gratefulfrog/ArduGuitar/Ardu2/design/POC-3_MAX395/HMI/Images/PB076096 Annotated.pdf

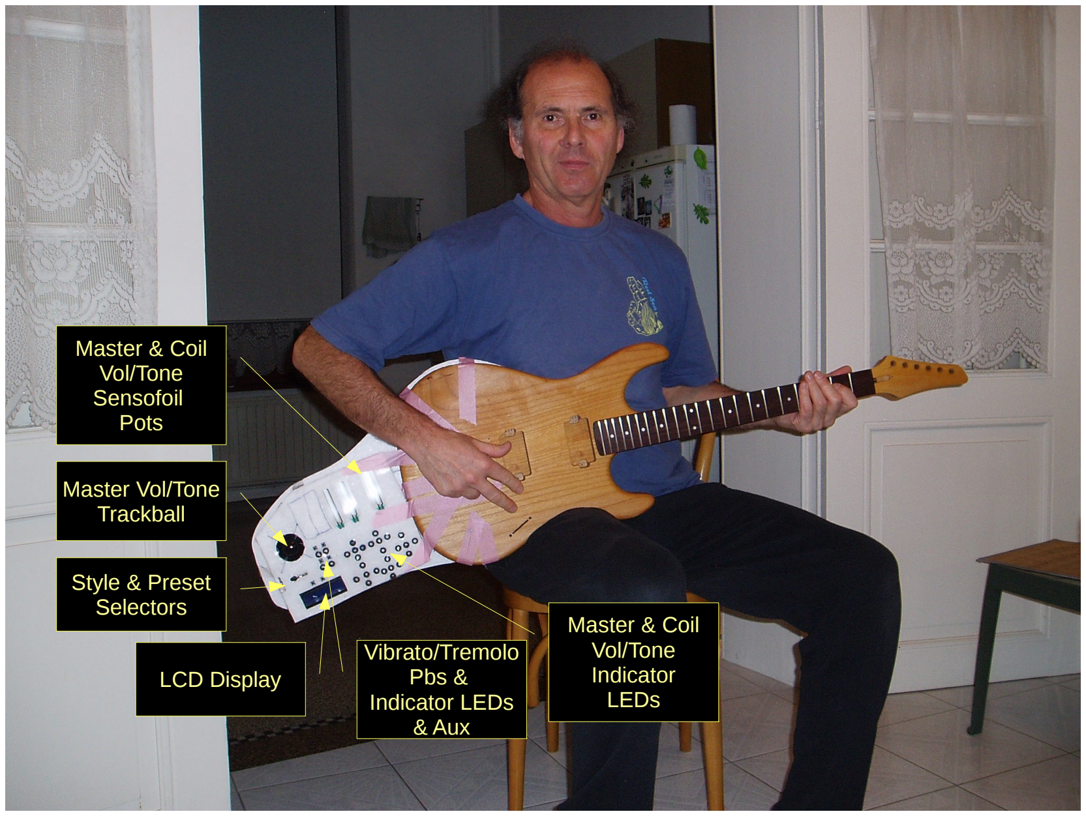
[picture p10: page 1]

Master Vol/Tone
Trackball

Master & Coil
Vol/Tone
Sensofoil
Pots

Style & Preset
Selectors

LCD Display

Vibrato/Tremolo
Pbs &
Indicator LEDs
& Aux

Master & Coil
Vol/Tone
Indicator
LEDs
