gratefulfrog/ArduGuitar/Ardu2/design/POC-3_MAX395/HMI/Images/boltplus-no-text.pdf

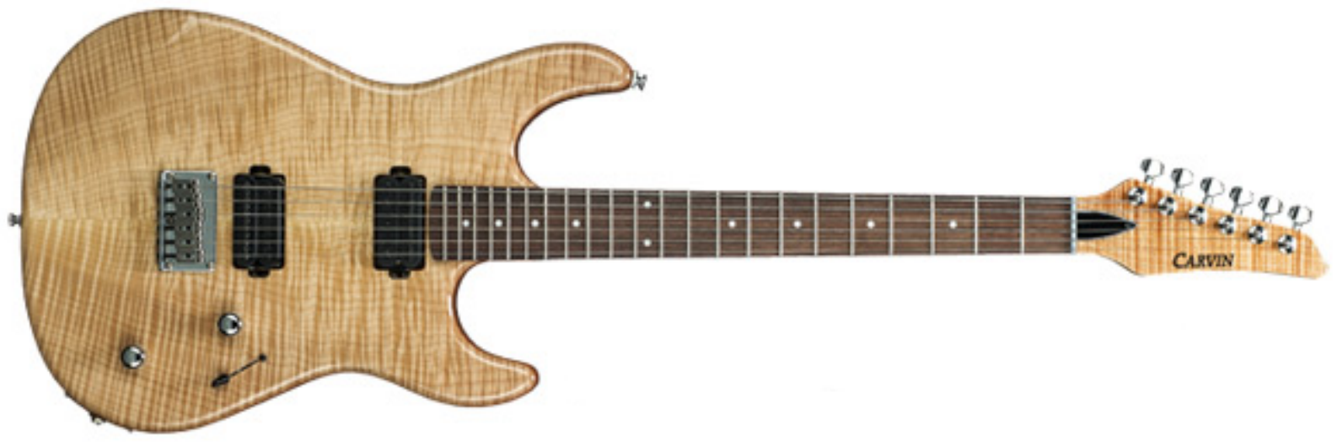
[picture p11: page 1]
