gratefulfrog/ArduGuitar/arduino/Layouts/ArduStomp/EnclosureDesign/2D/FullDesign09/outside-panels.pdf

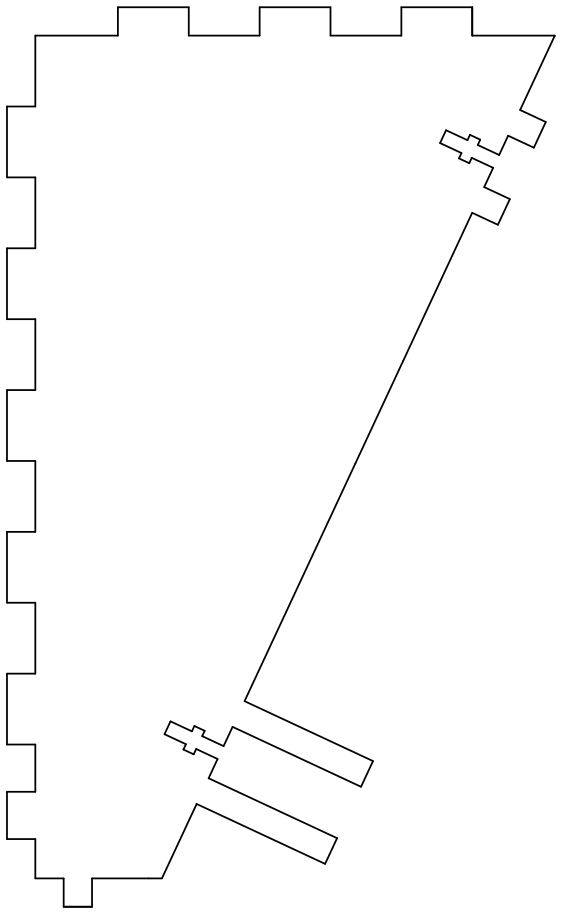
[picture p12: figure]
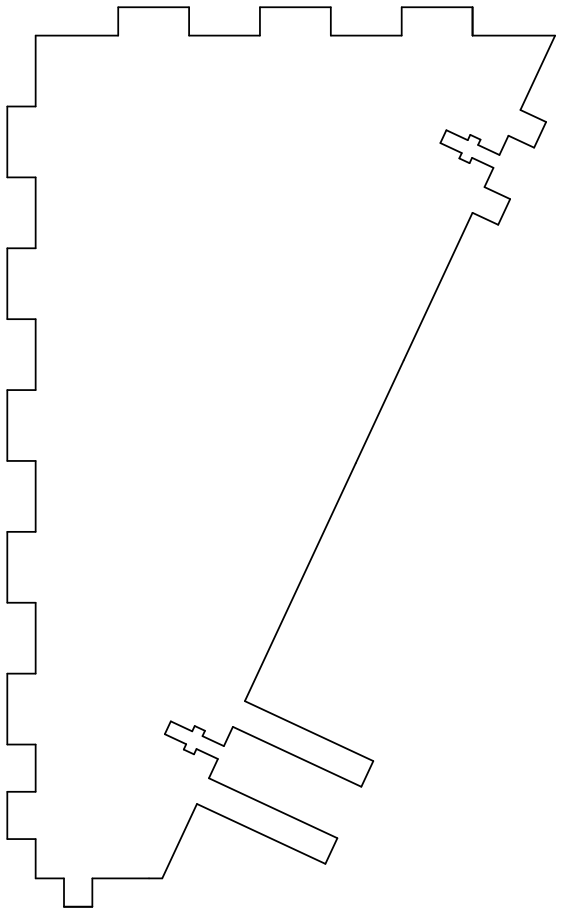
[picture p13: figure]
