gratefulfrog/ArduGuitar/Ardu2/design/EarlyDesigns/Ardu2_schem_00.png

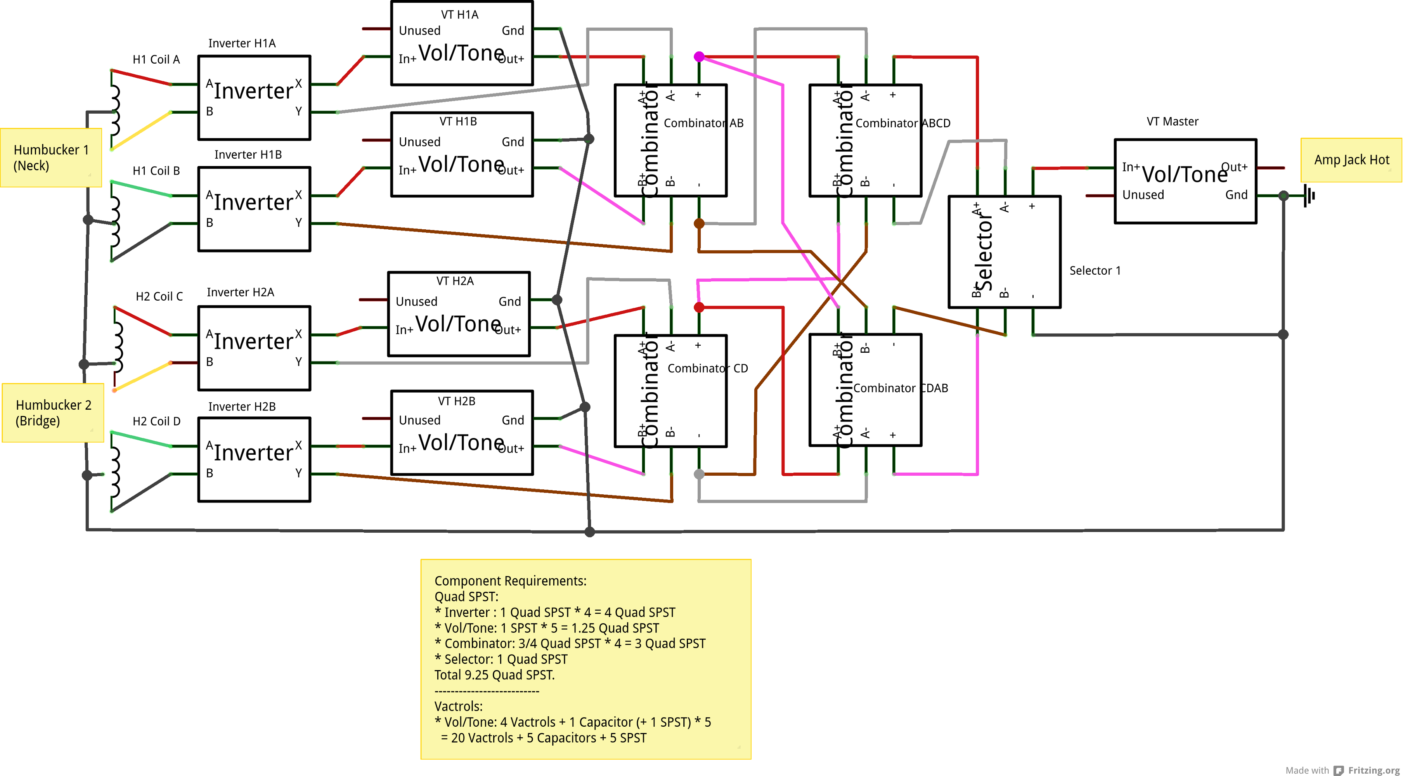
Ardu2/design/EarlyDesigns/Ardu2_schem_00.png
