gratefulfrog/ArduGuitar/Ardu2/design/EarlyDesigns/Ardu2_schem_00_a.png

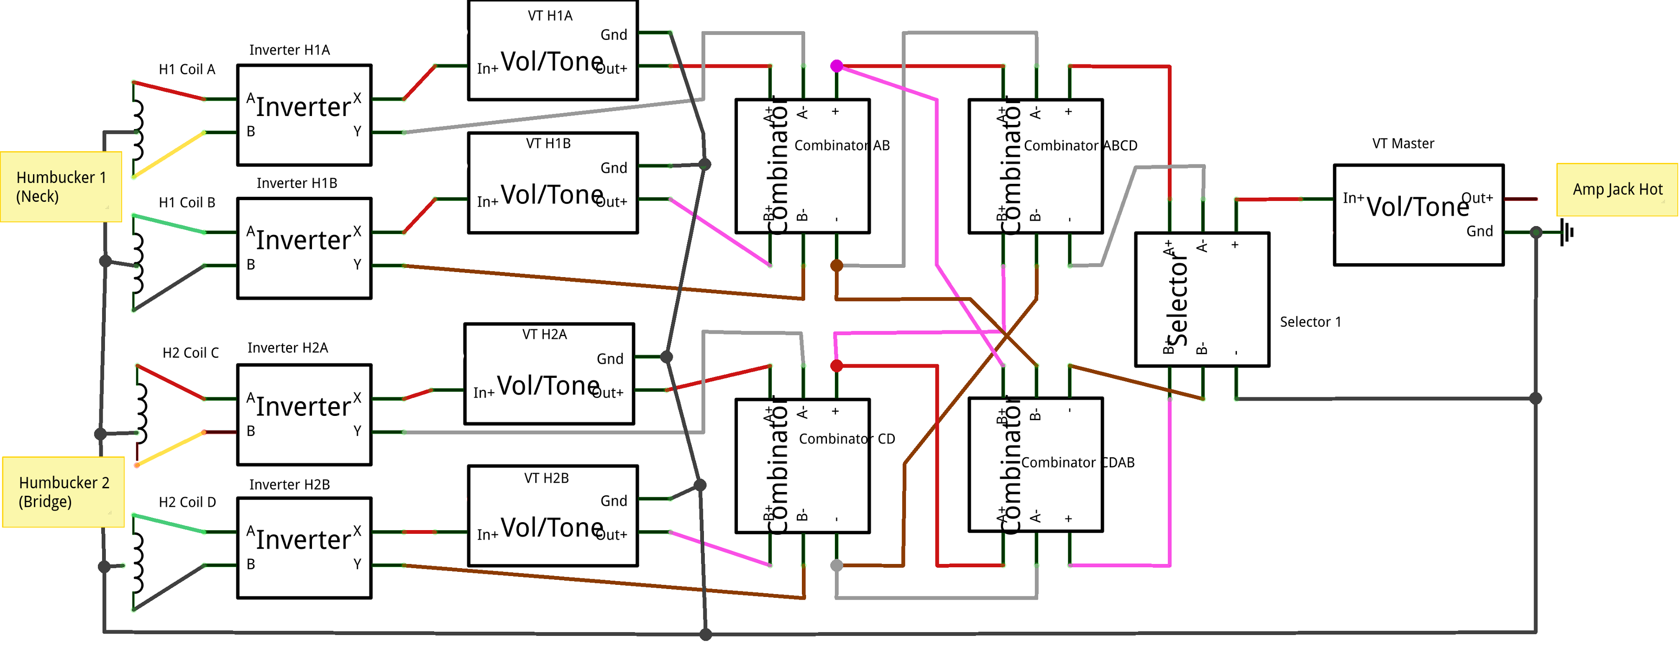
Ardu2/design/EarlyDesigns/Ardu2_schem_00_a.png
