gratefulfrog/ArduGuitar/Ardu2/design/EarlyDesigns/Combinator_pcb.png

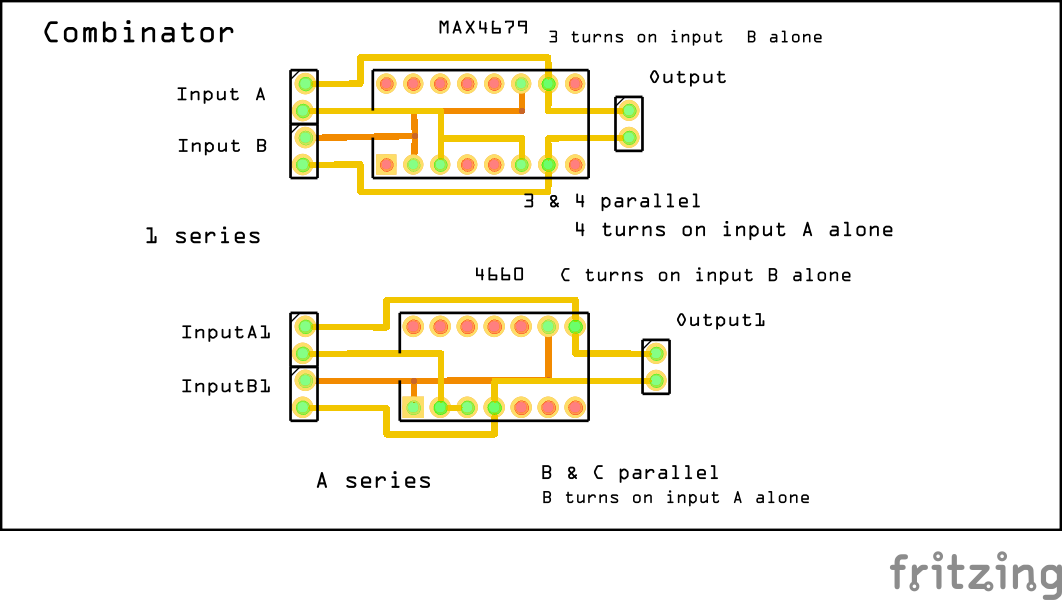
Ardu2/design/EarlyDesigns/Combinator_pcb.png
