gratefulfrog/ArduGuitar/Ardu2/design/EarlyDesigns/Selector_pcb.png

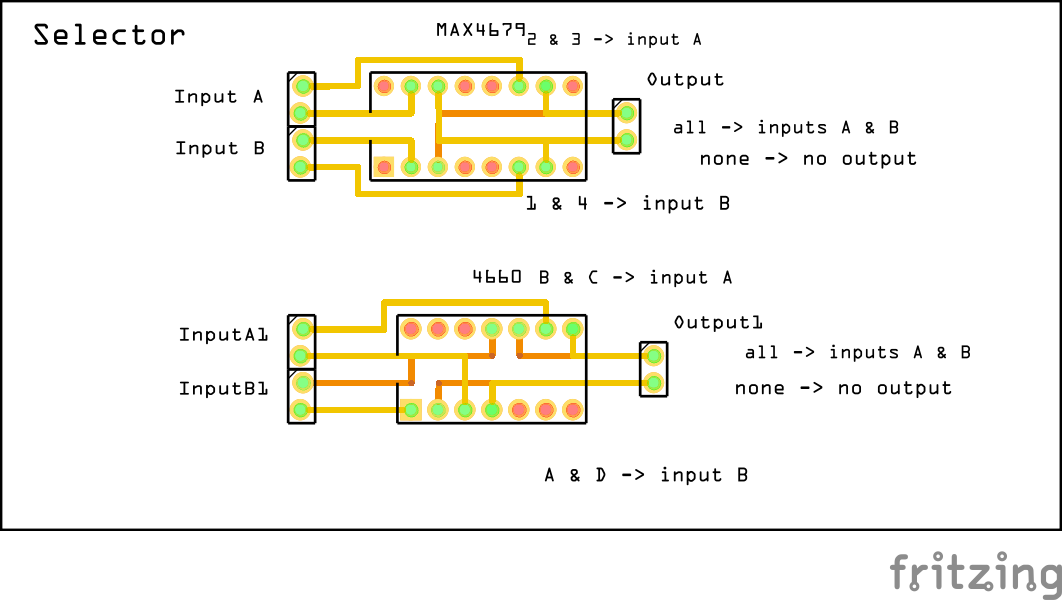
Ardu2/design/EarlyDesigns/Selector_pcb.png
