gratefulfrog/ArduGuitar/Ardu2/design/EarlyDesigns/Vol-Tone 4066_bb.png

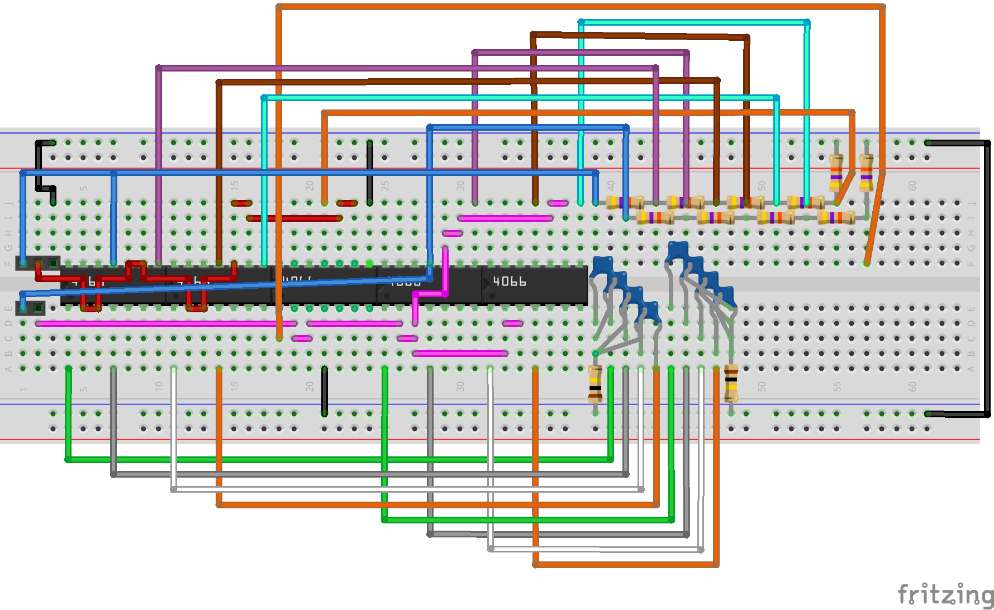
Ardu2/design/EarlyDesigns/Vol-Tone 4066_bb.png
