gratefulfrog/ArduGuitar/Ardu2/design/EarlyDesigns/Vol-Tone Max4679_pcb.png

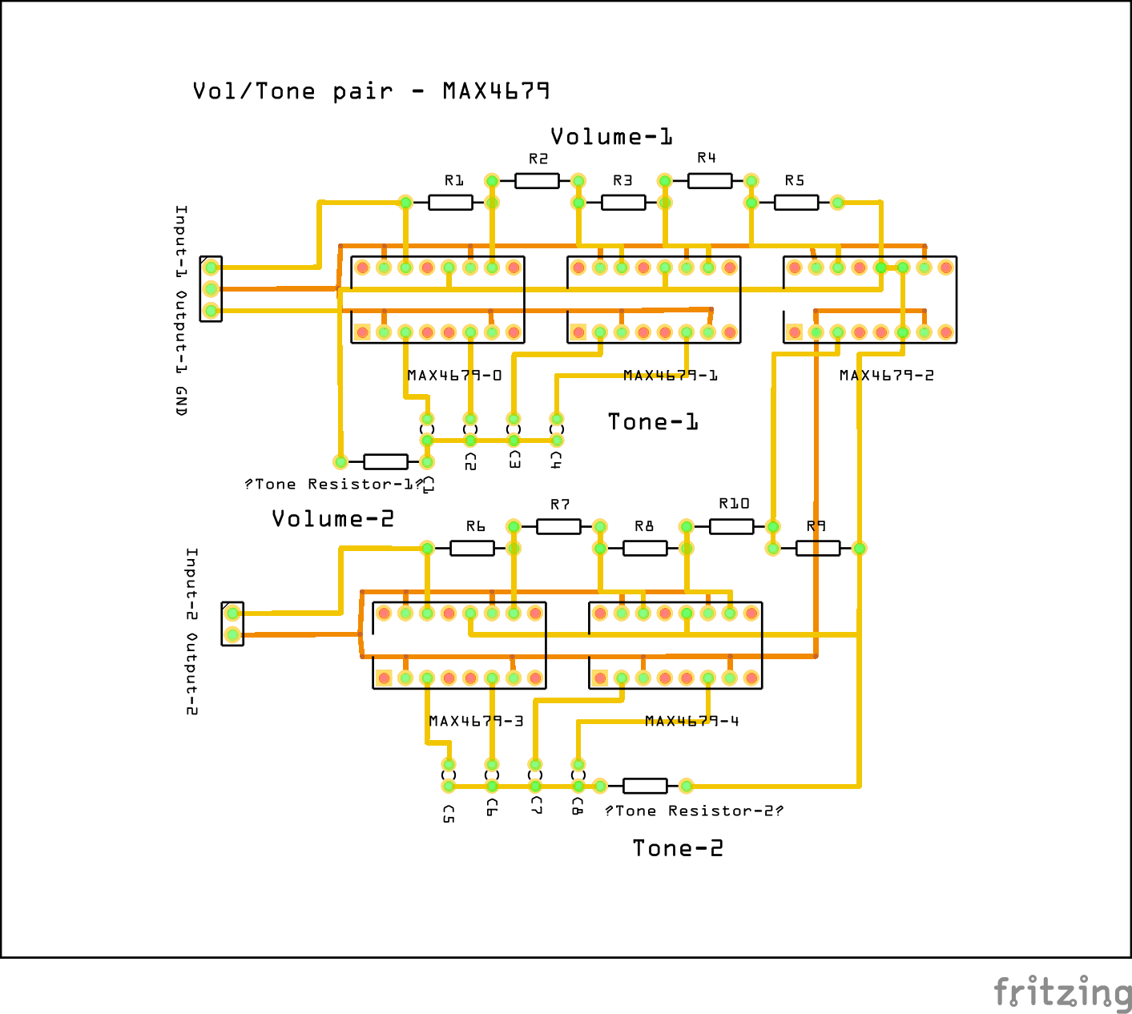
Ardu2/design/EarlyDesigns/Vol-Tone Max4679_pcb.png
