gratefulfrog/ArduGuitar/Ardu2/design/InputStage_Vol_Tone 04_pcb.png

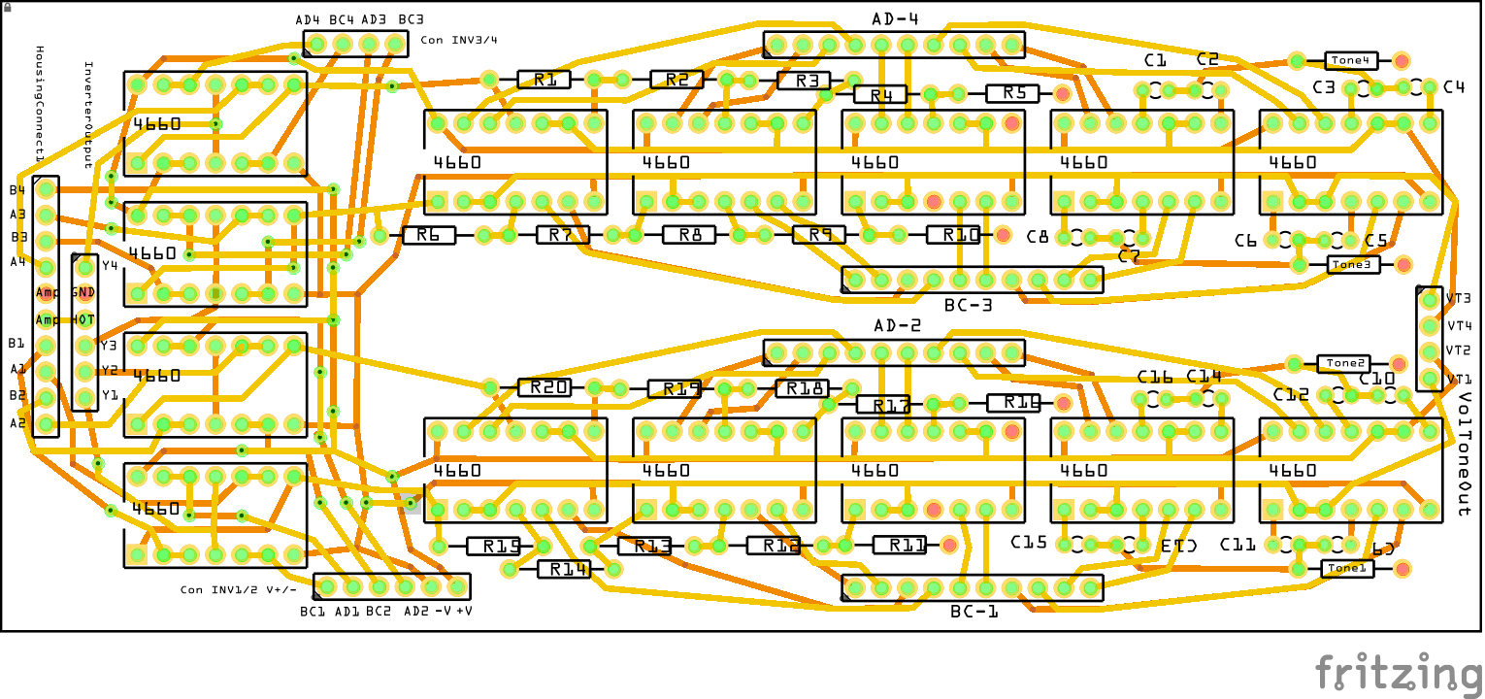
Ardu2/design/InputStage_Vol_Tone 04_pcb.png
