gratefulfrog/ArduGuitar/Ardu2/design/Inverter_pcb.png

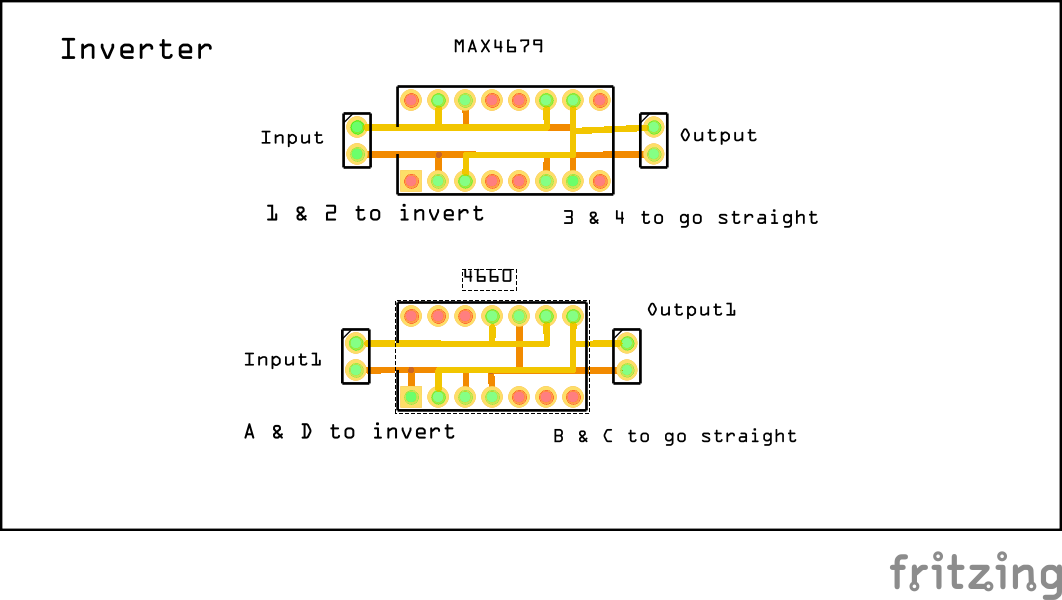
Ardu2/design/Inverter_pcb.png
