gratefulfrog/ArduGuitar/Ardu2/design/POC-0/POC Combine-Select-Master-V-T Breadboard_bb.png

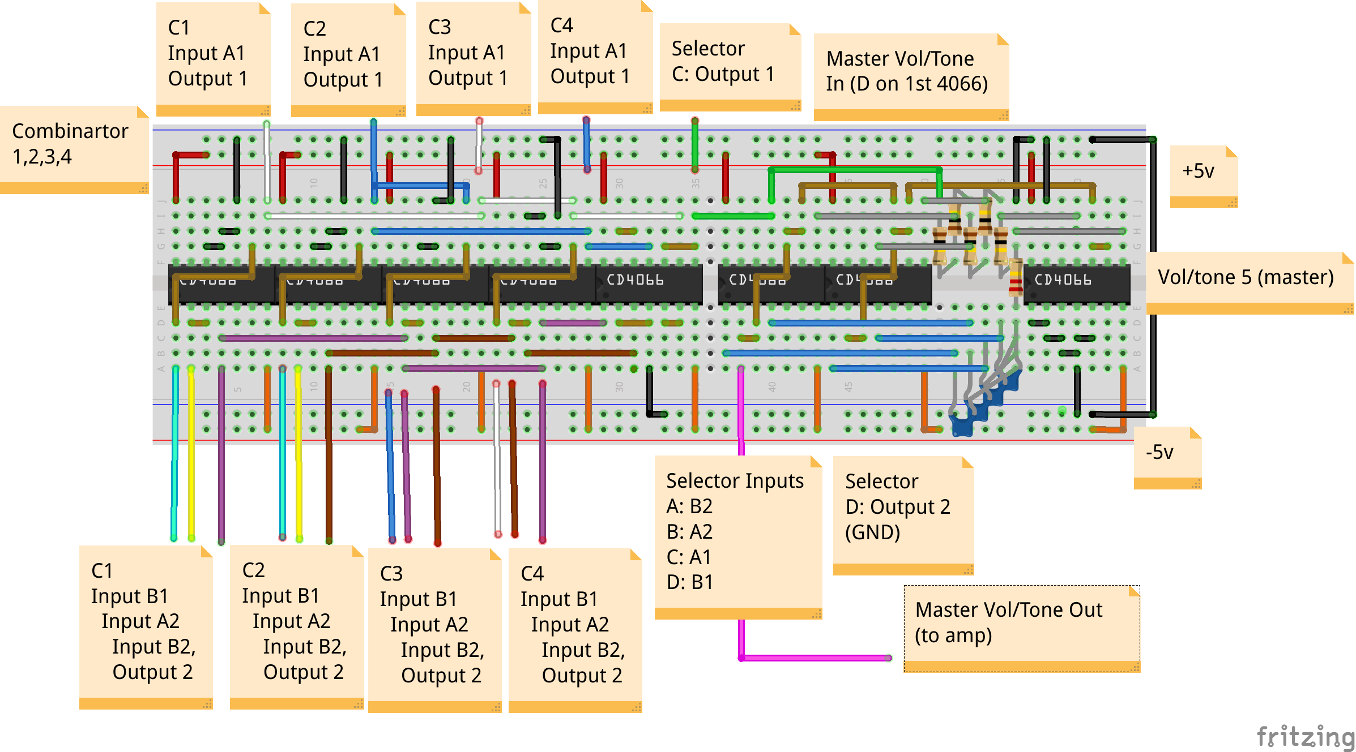
Ardu2/design/POC-0/POC Combine-Select-Master-V-T Breadboard_bb.png
