gratefulfrog/ArduGuitar/Ardu2/design/POC-0/POC Inverter Breadboard_bb.png

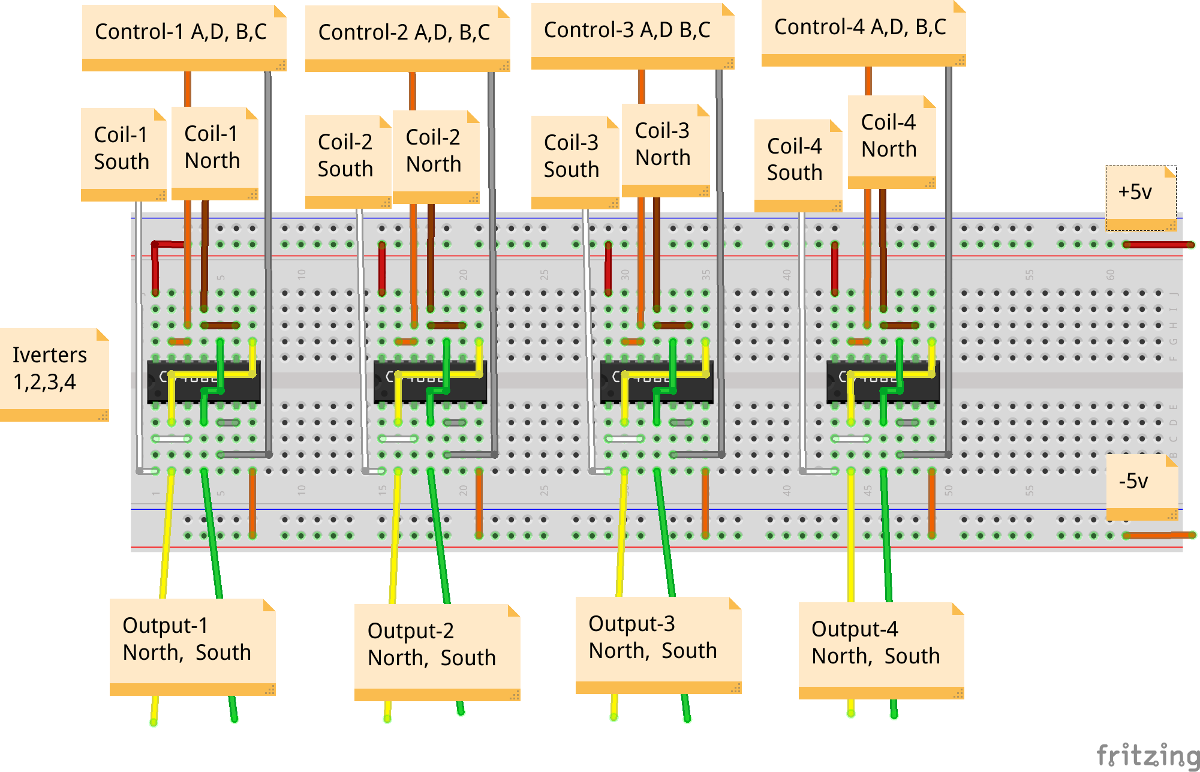
Ardu2/design/POC-0/POC Inverter Breadboard_bb.png
