gratefulfrog/ArduGuitar/Ardu2/design/POC-1/Full Conceptul View_schem.png

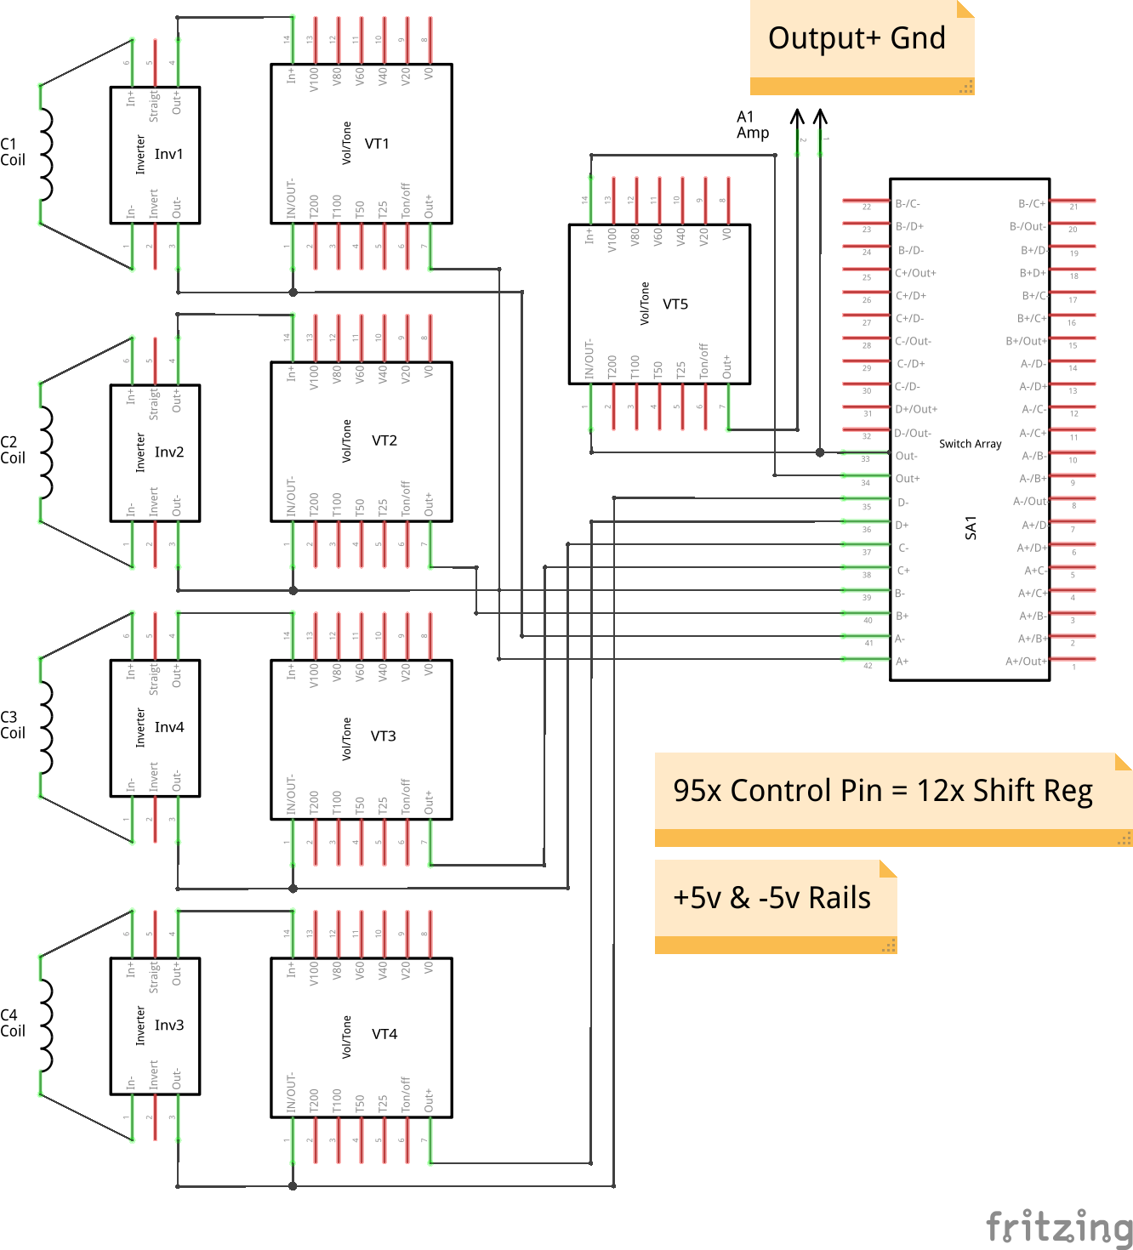
Ardu2/design/POC-1/Full Conceptul View_schem.png
