gratefulfrog/ArduGuitar/Ardu2/design/POC-1/POC -5V PSU breadboard_bb.png

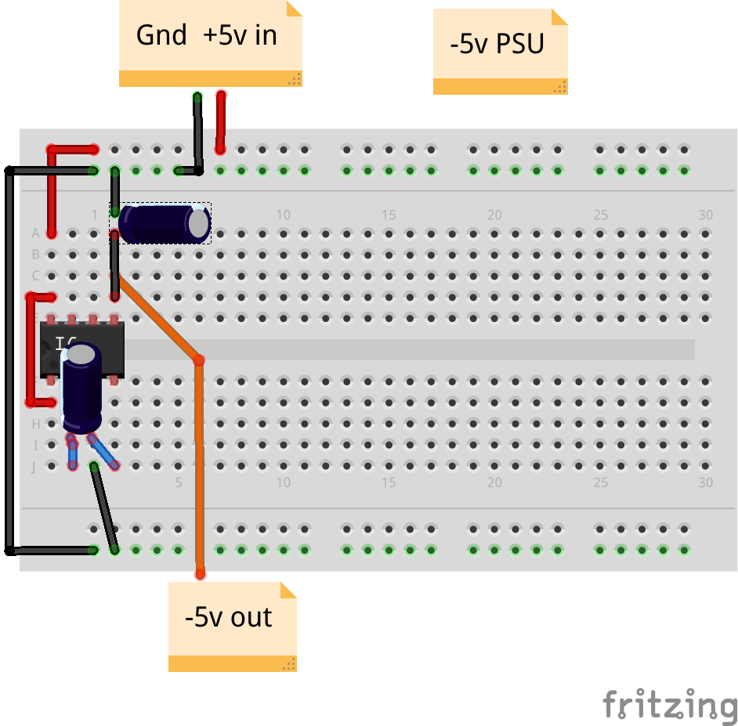
Ardu2/design/POC-1/POC -5V PSU breadboard_bb.png
