gratefulfrog/ArduGuitar/Ardu2/design/POC-1/POC Inverter Breadboard resistive tone control_bb.png

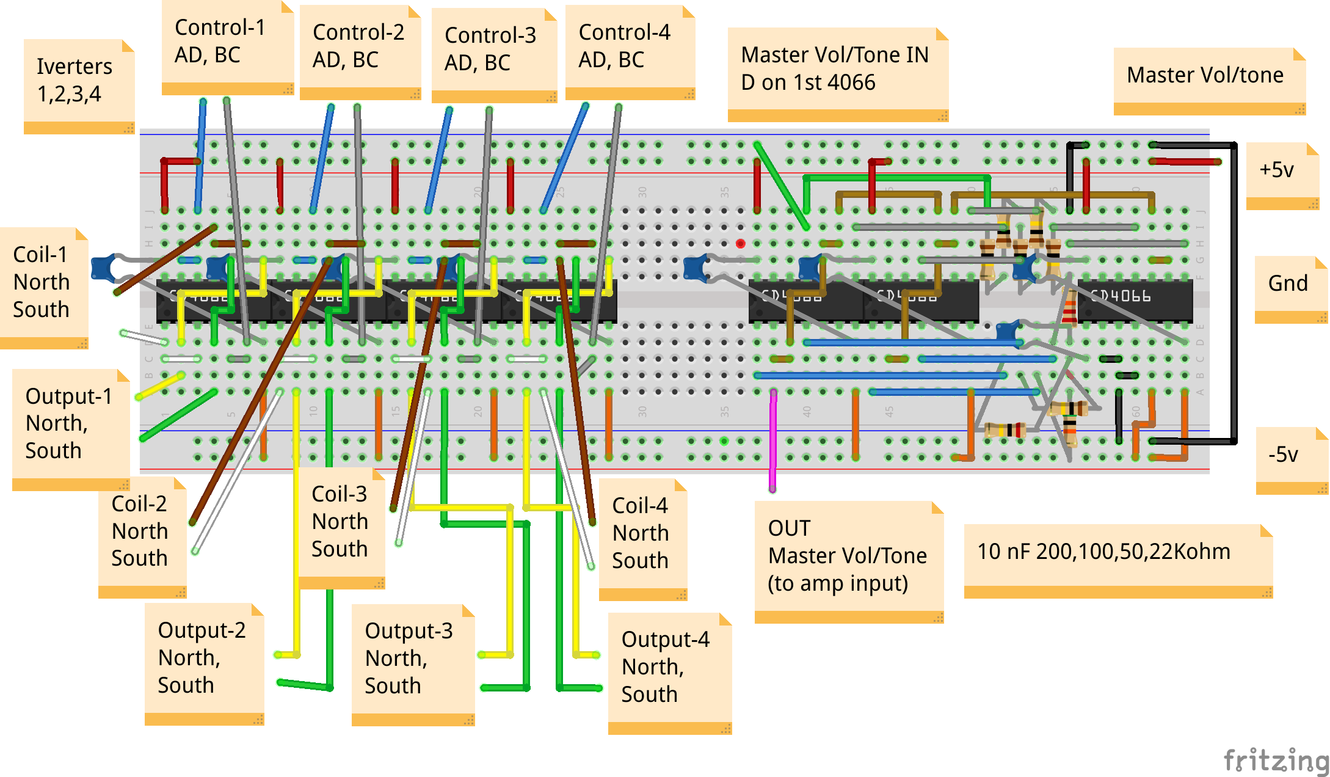
Ardu2/design/POC-1/POC Inverter Breadboard resistive tone control_bb.png
