gratefulfrog/ArduGuitar/Ardu2/design/POC-1/POC Vol-Tone Breadboard_bb.png

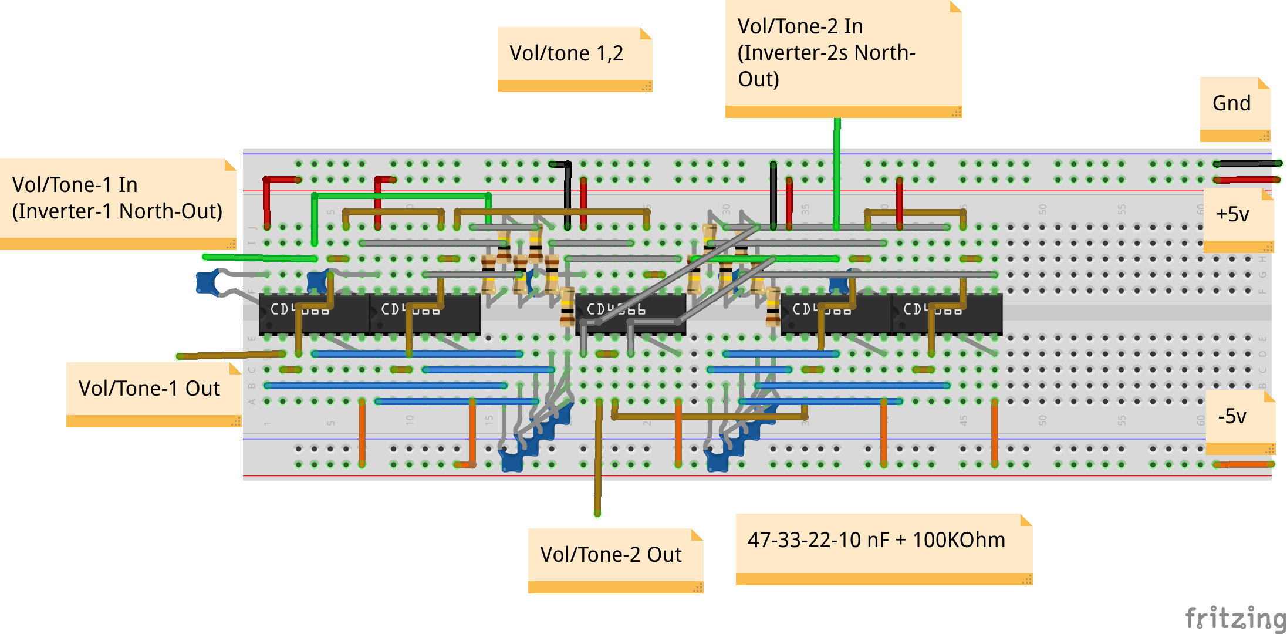
Ardu2/design/POC-1/POC Vol-Tone Breadboard_bb.png
