gratefulfrog/ArduGuitar/Ardu2/design/POC-1/POC-1 Switching Schematic_schem.png

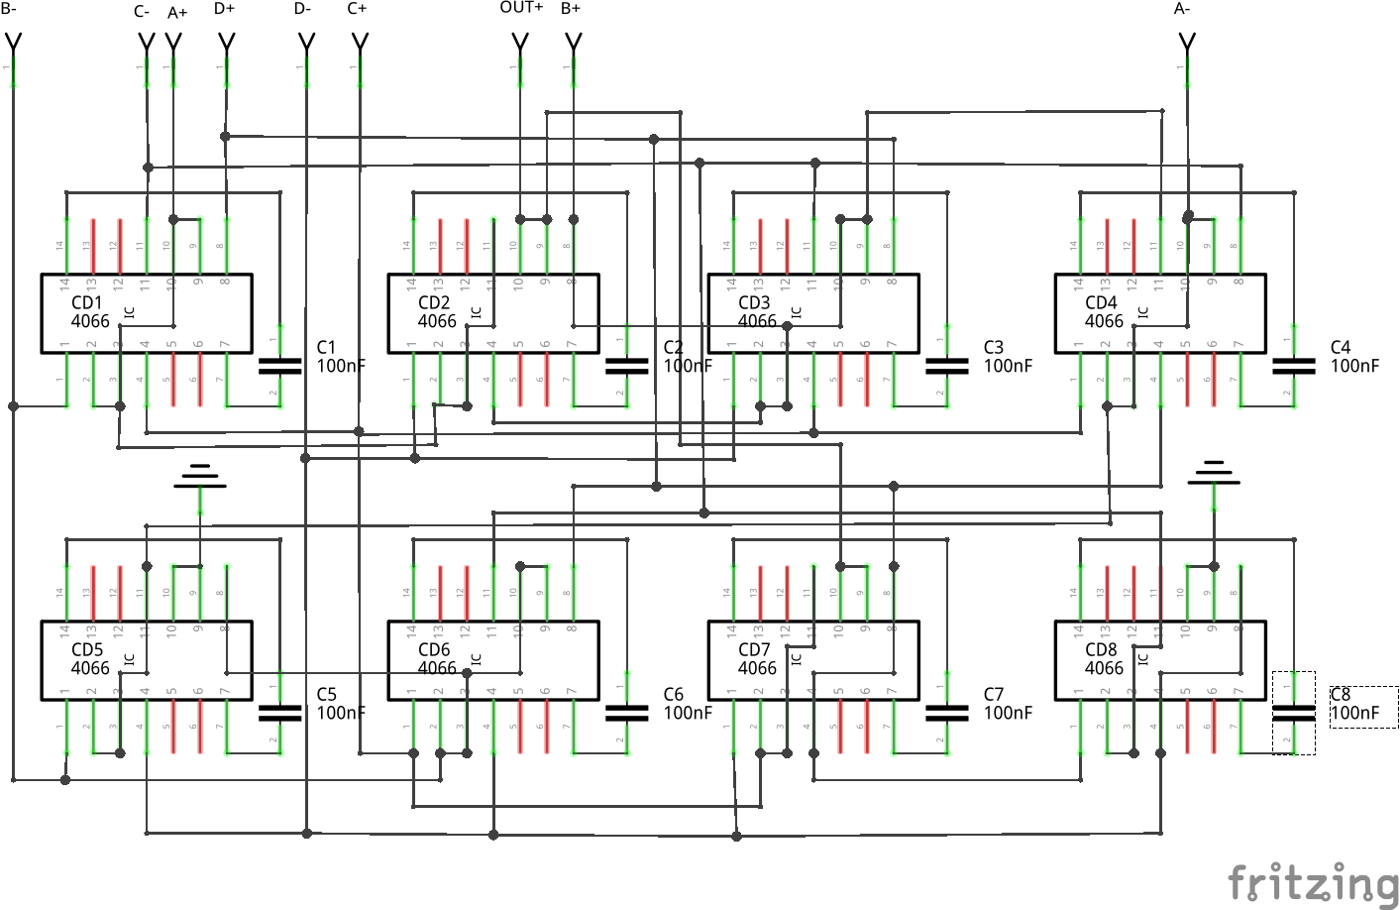
Ardu2/design/POC-1/POC-1 Switching Schematic_schem.png
