gratefulfrog/ArduGuitar/Ardu2/design/POC-1/SPDT Switch-Array-PCB_pcb.png

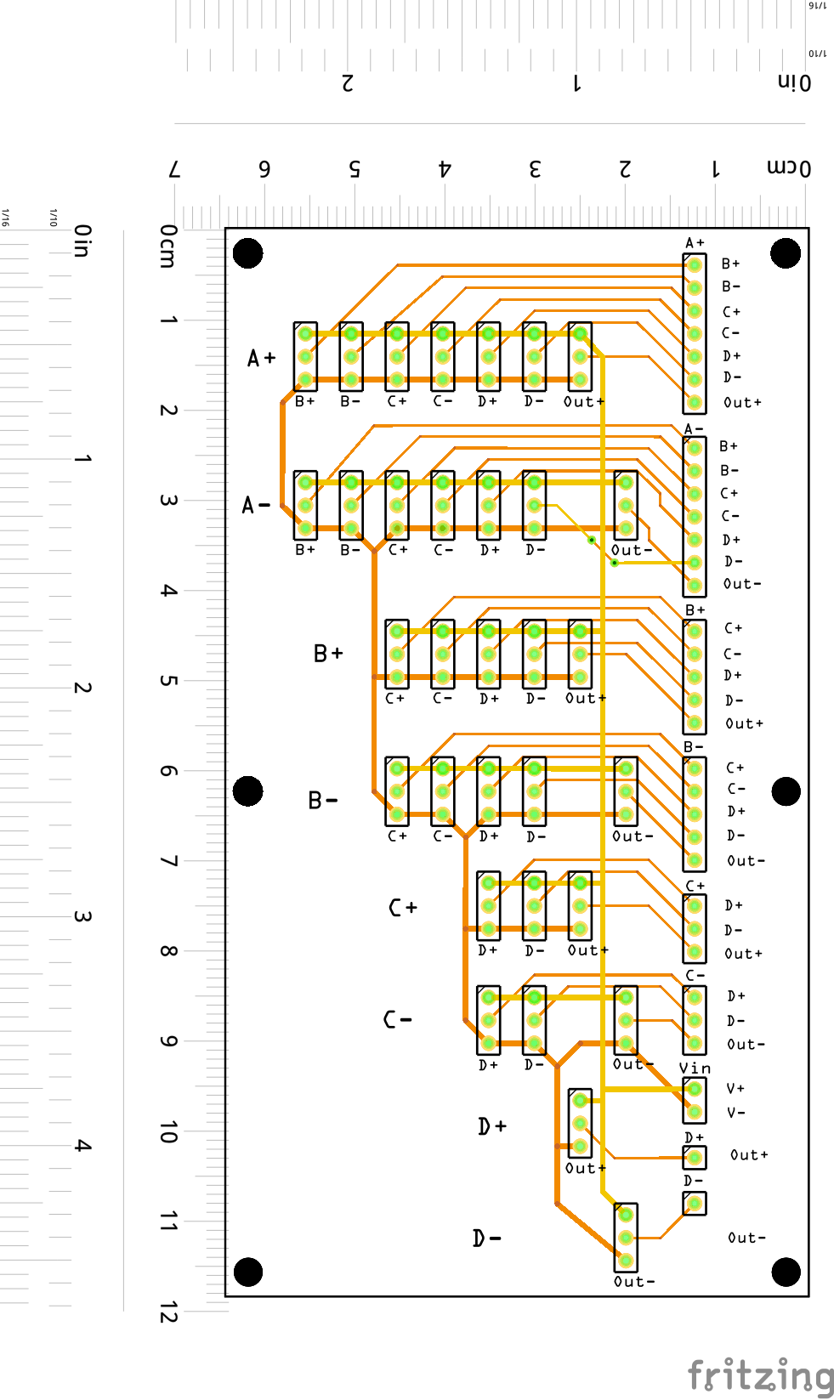
Ardu2/design/POC-1/SPDT Switch-Array-PCB_pcb.png
