gratefulfrog/ArduGuitar/Ardu2/design/POC-2/Carvin Integration/Carvin/10PDT Mount v3_pcb.png

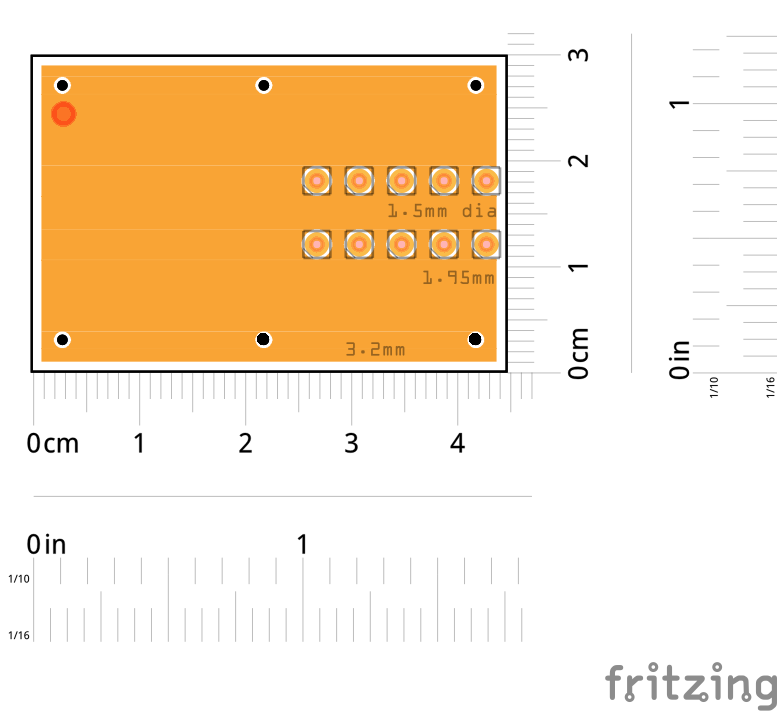
Ardu2/design/POC-2/Carvin Integration/Carvin/10PDT Mount v3_pcb.png
