gratefulfrog/ArduGuitar/Ardu2/design/POC-2/Carvin Integration/Carvin/10PDT Mount v4_pcb.png

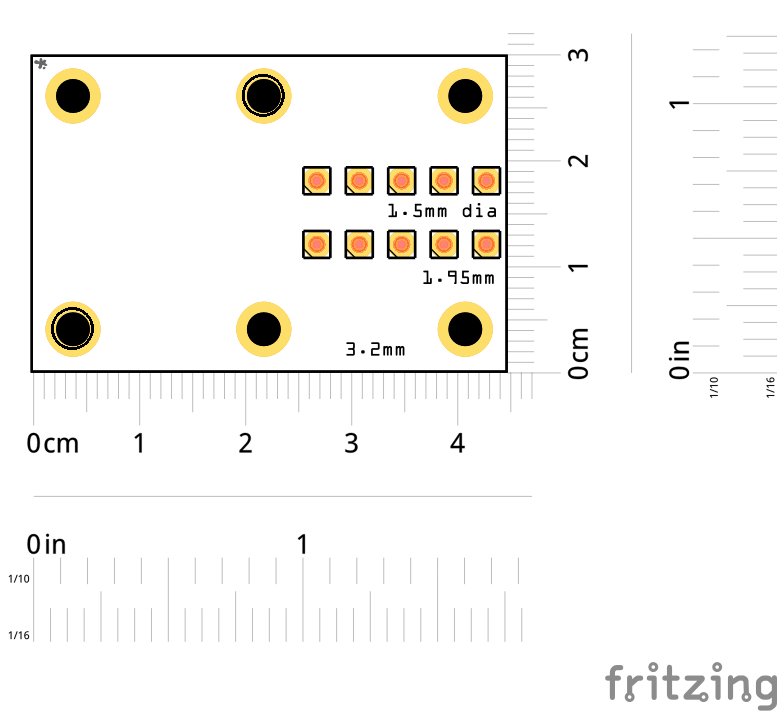
Ardu2/design/POC-2/Carvin Integration/Carvin/10PDT Mount v4_pcb.png
