gratefulfrog/ArduGuitar/Ardu2/design/POC-2/Carvin Integration/Carvin/MyCarvin/IMG_20140908_171224.jpg

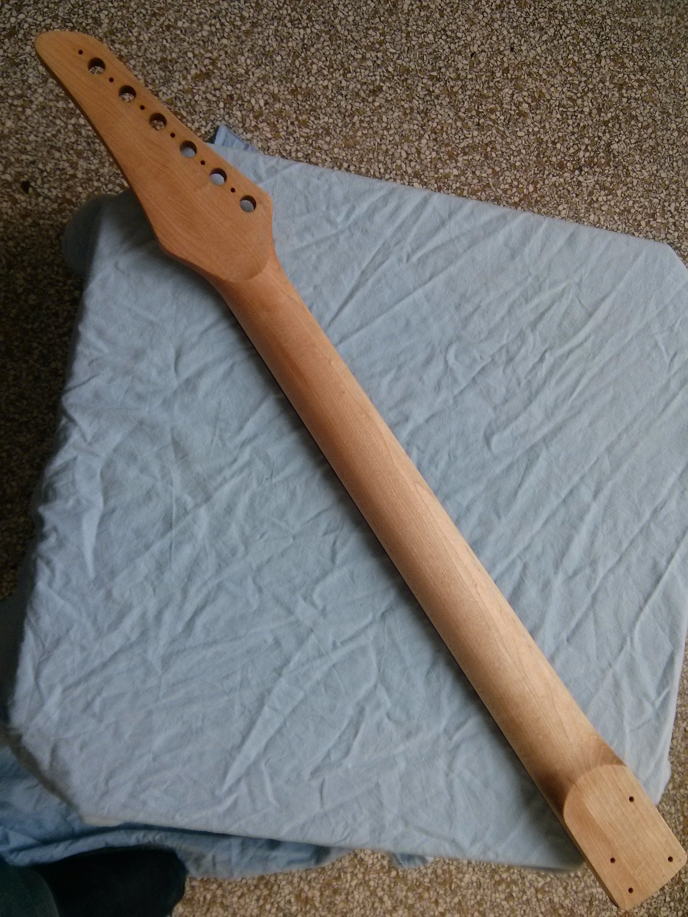
Ardu2/design/POC-2/Carvin Integration/Carvin/MyCarvin/IMG_20140908_171224.jpg
