gratefulfrog/ArduGuitar/Ardu2/design/POC-2/Carvin Integration/Carvin/MyCarvin/ThreadedInserts.jpg

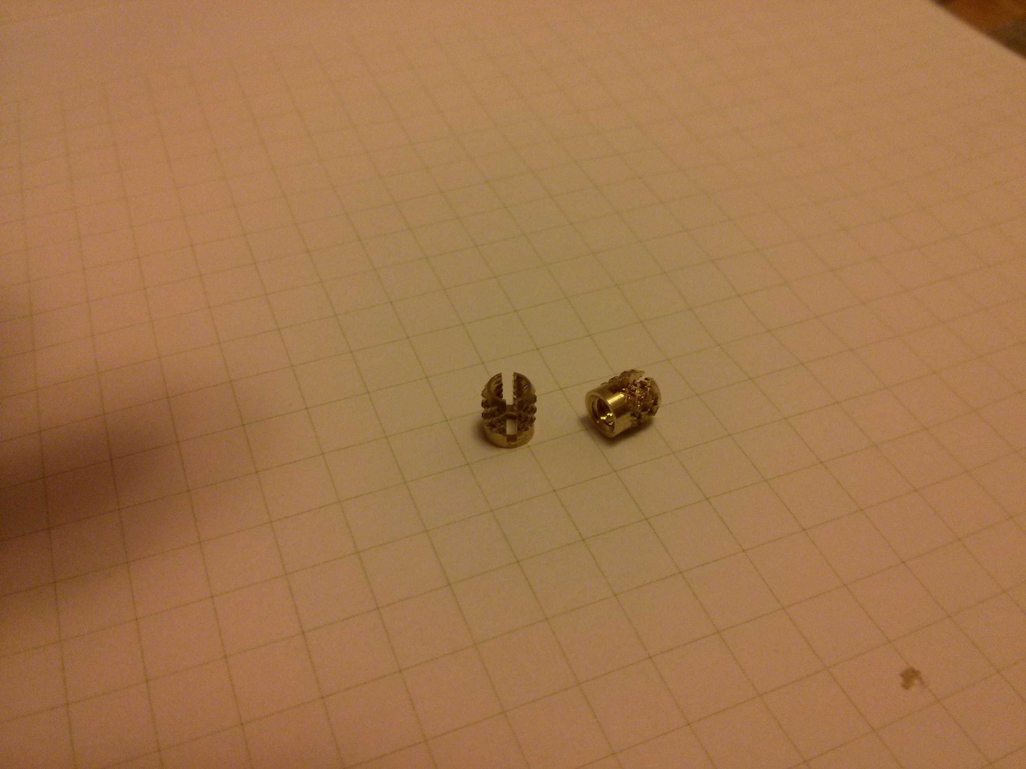
Ardu2/design/POC-2/Carvin Integration/Carvin/MyCarvin/ThreadedInserts.jpg
