gratefulfrog/ArduGuitar/Ardu2/design/POC-2/etch/pcb.png

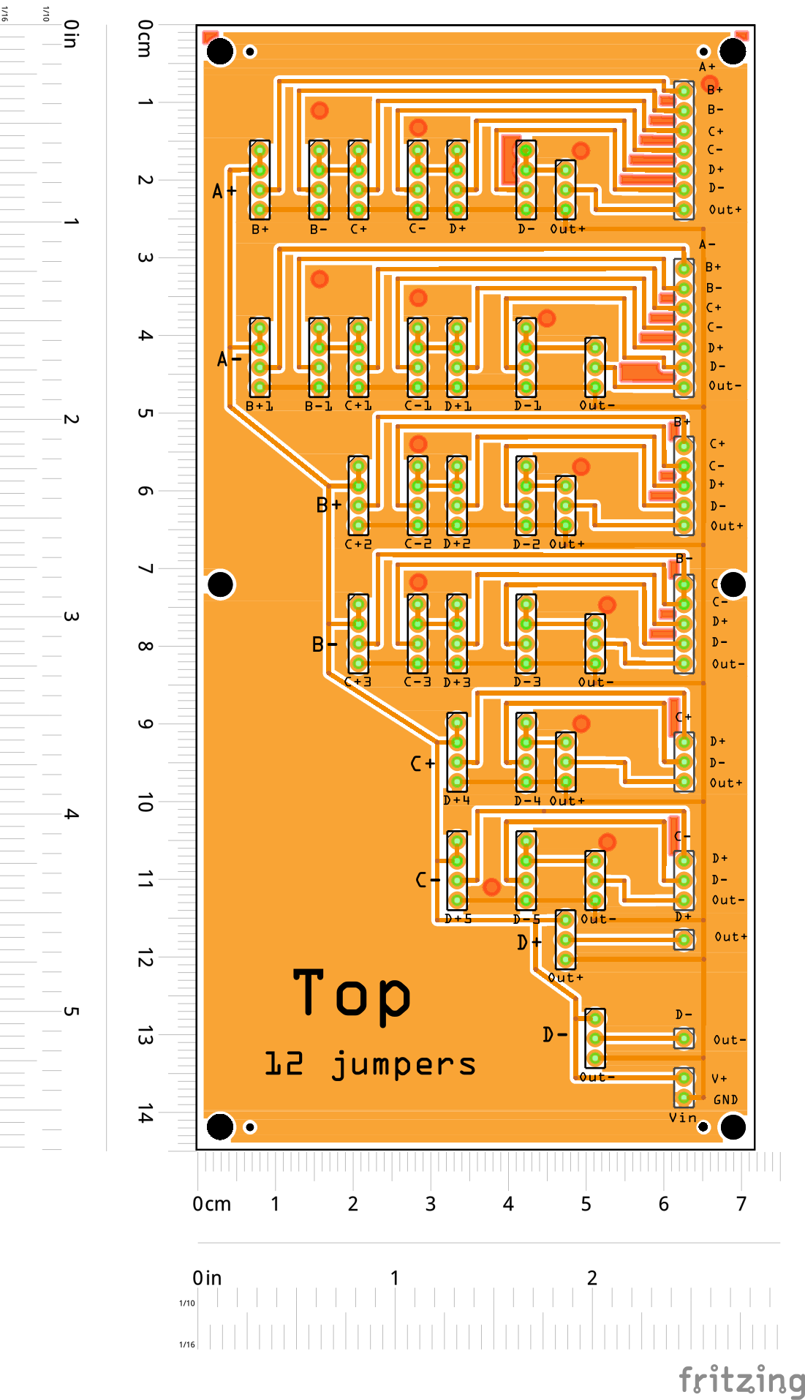
Ardu2/design/POC-2/etch/pcb.png
