gratefulfrog/ArduGuitar/Ardu2/design/POC-2/IntegrationPhotos/IMG_20150215_131508.jpg

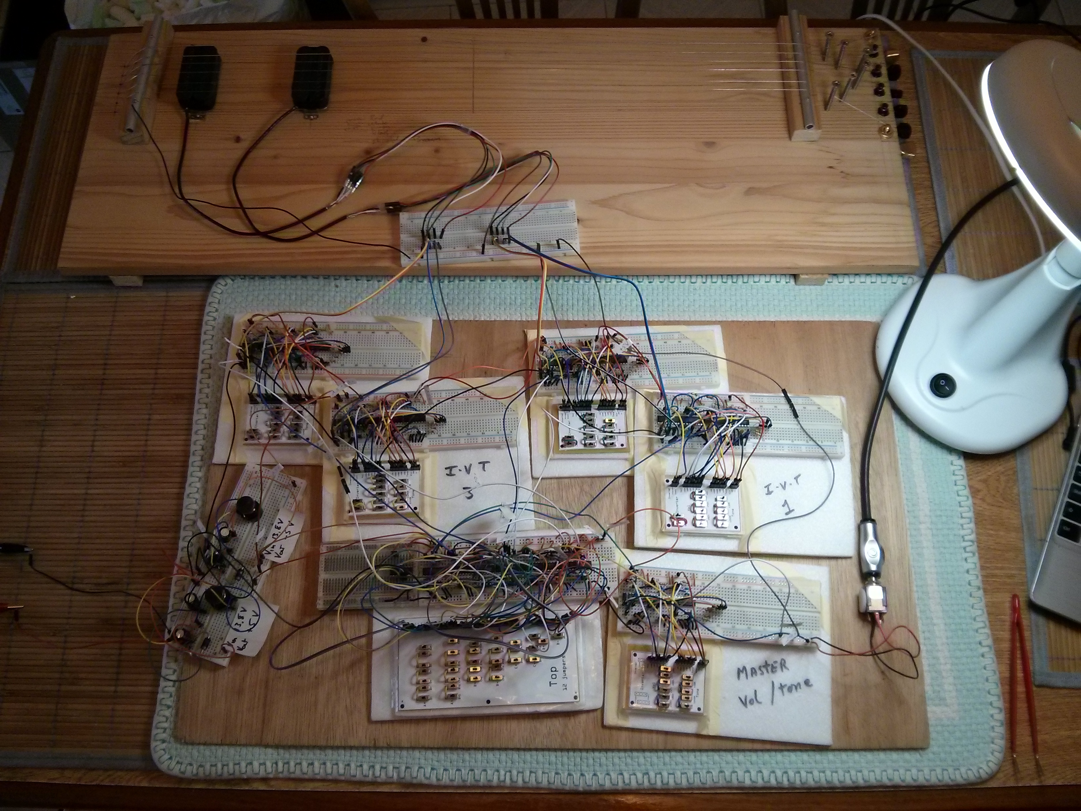
Ardu2/design/POC-2/IntegrationPhotos/IMG_20150215_131508.jpg
