gratefulfrog/ArduGuitar/Ardu2/design/POC-2/IntegrationPhotos/IMG_20150404_211104.jpg

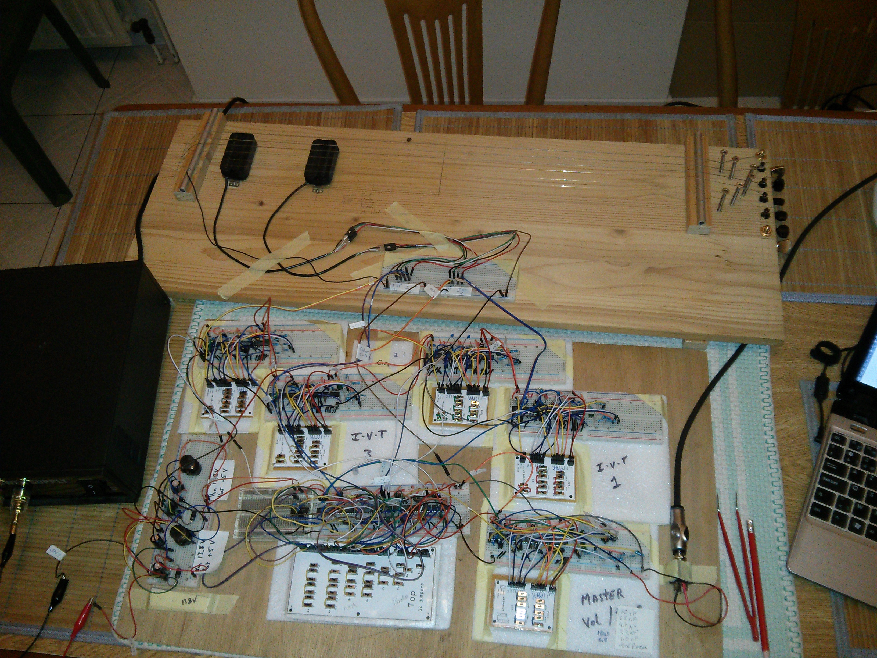
Ardu2/design/POC-2/IntegrationPhotos/IMG_20150404_211104.jpg
