gratefulfrog/ArduGuitar/Ardu2/design/POC-2/InverterVolTone/4316 Master Vol-resistive-tone control PCB _pcb.png

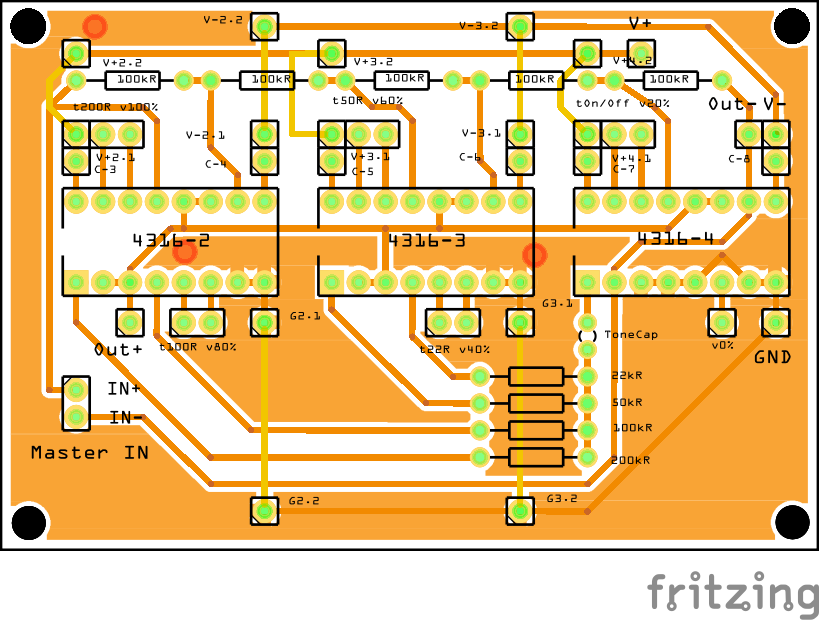
Ardu2/design/POC-2/InverterVolTone/4316 Master Vol-resistive-tone control PCB _pcb.png
