gratefulfrog/ArduGuitar/Ardu2/design/POC-2/InverterVolTone/4316-Inverter-Vol-Tone-PCB_pcb.png

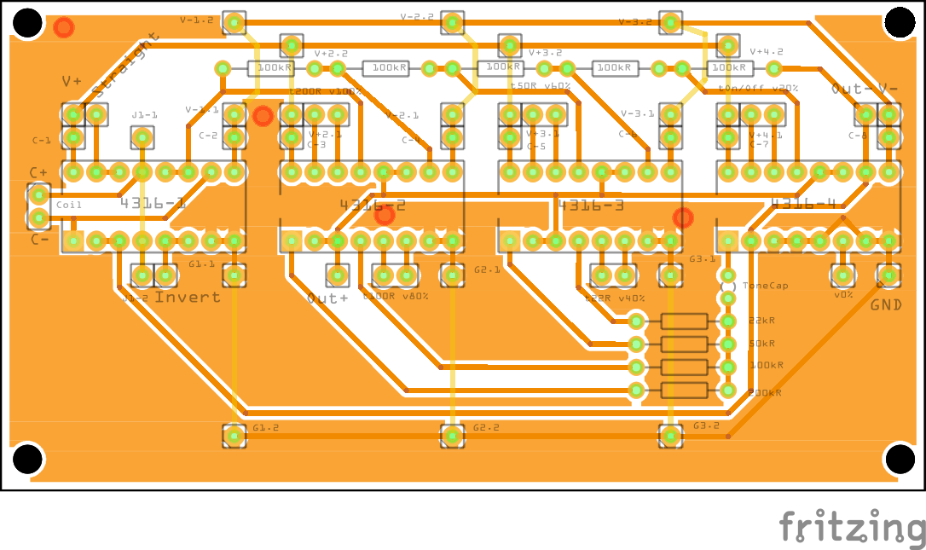
Ardu2/design/POC-2/InverterVolTone/4316-Inverter-Vol-Tone-PCB_pcb.png
