gratefulfrog/ArduGuitar/Ardu2/design/POC-2/InverterVolTone/4316d Single Inverter and resistive tone control pcb b_pcb.png

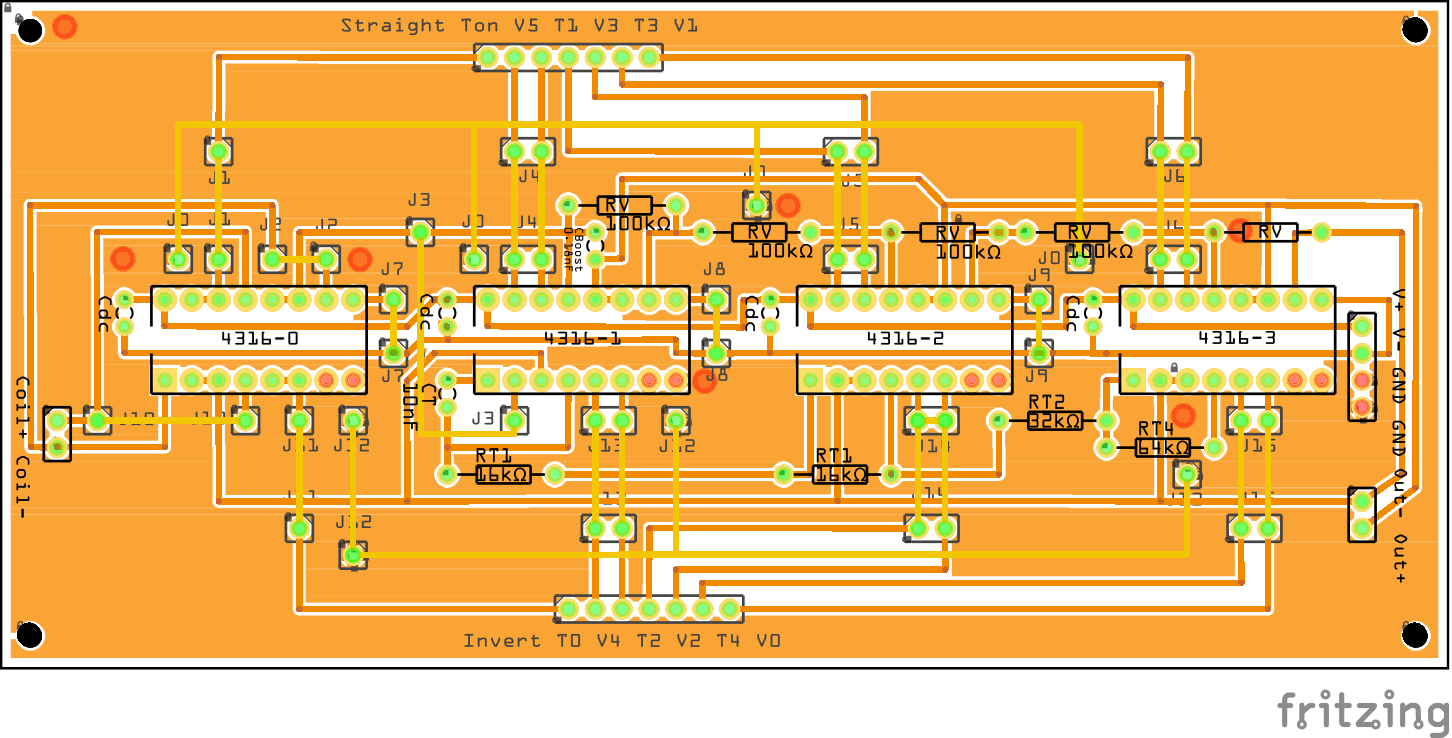
Ardu2/design/POC-2/InverterVolTone/4316d Single Inverter and resistive tone control pcb b_pcb.png
