gratefulfrog/ArduGuitar/Ardu2/design/POC-2/InverterVolTone/4316e IVT schematic _schem.png

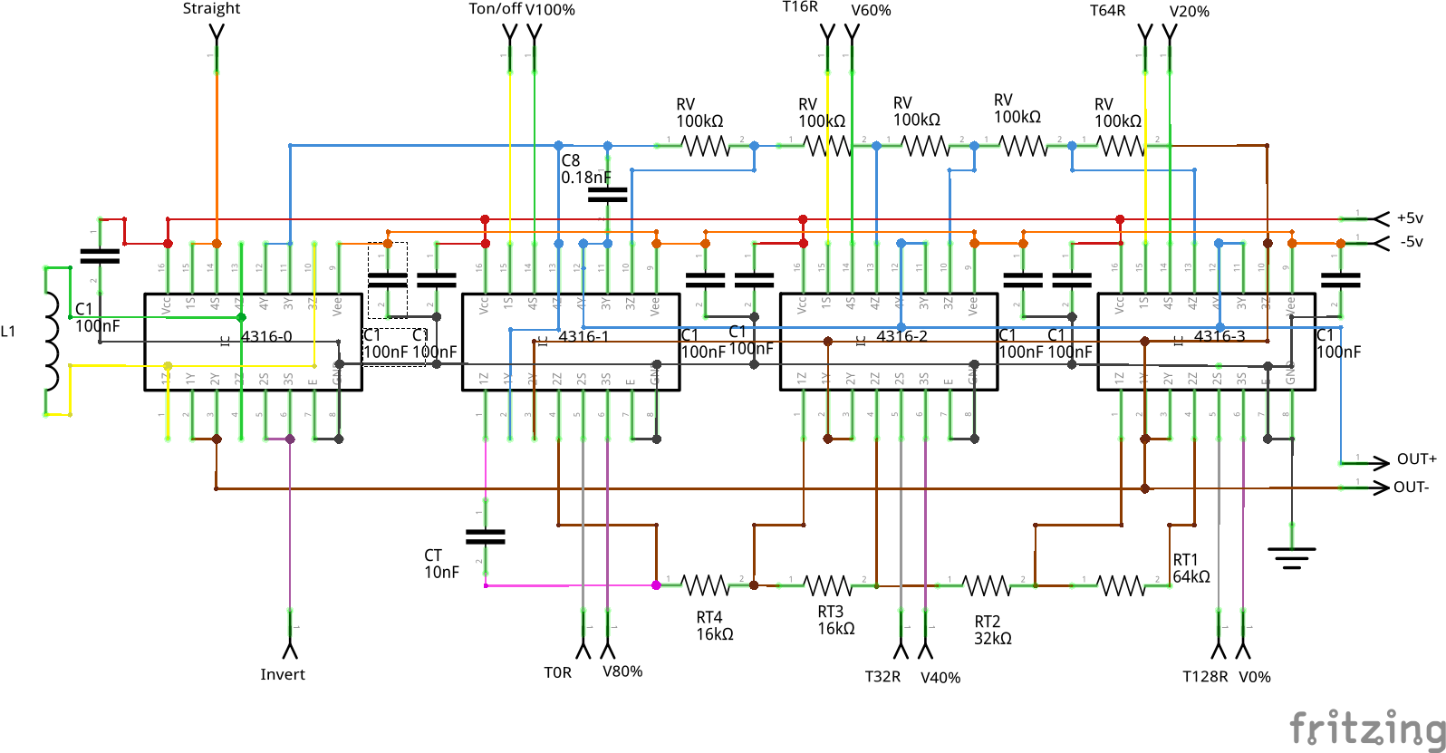
Ardu2/design/POC-2/InverterVolTone/4316e IVT schematic _schem.png
