gratefulfrog/ArduGuitar/Ardu2/design/POC-2/InverterVolTone/4316e Master Vol-resistive-tone control schematic _schem.png

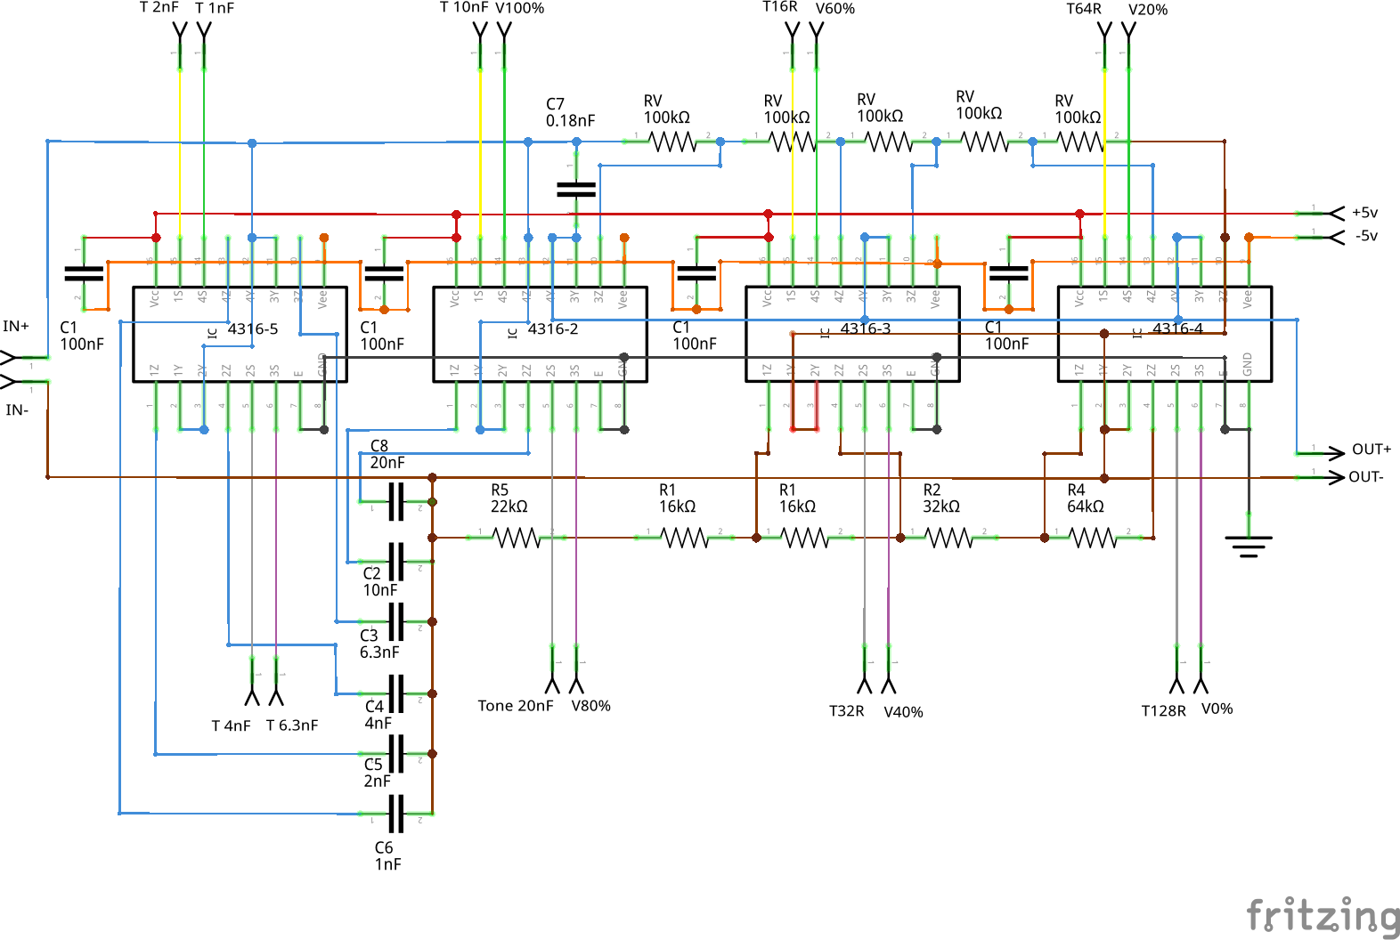
Ardu2/design/POC-2/InverterVolTone/4316e Master Vol-resistive-tone control schematic _schem.png
