gratefulfrog/ArduGuitar/Ardu2/design/POC-2/InverterVolTone/SPDT-GERBER/IMG_20150123_162215.jpg

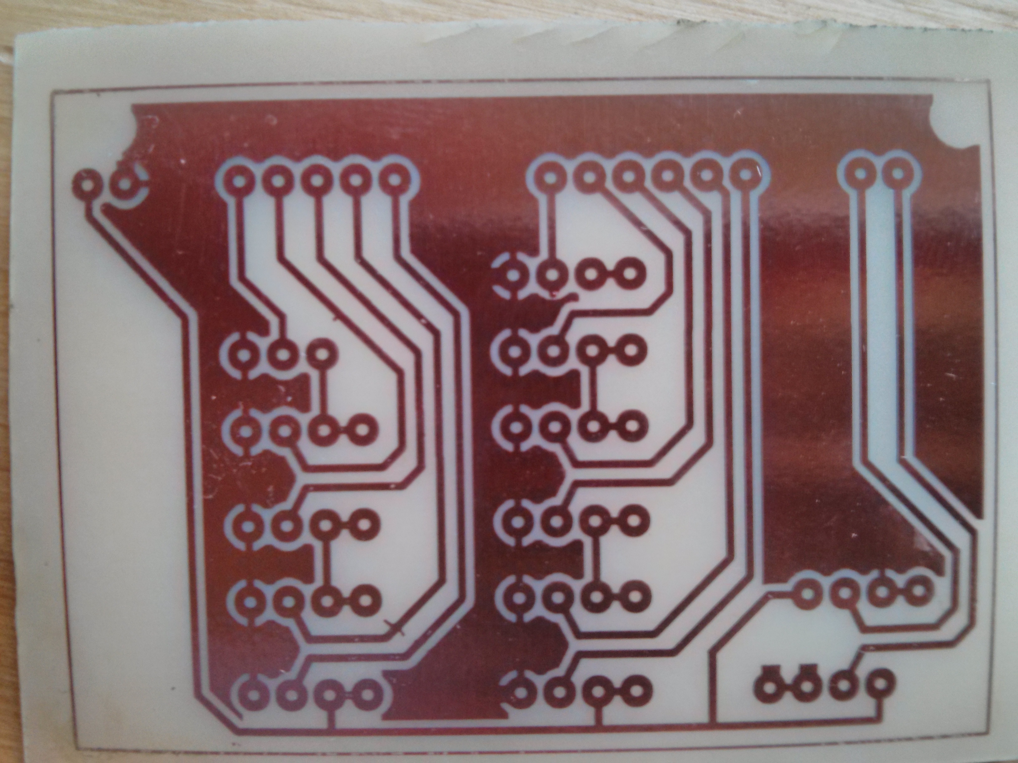
Ardu2/design/POC-2/InverterVolTone/SPDT-GERBER/IMG_20150123_162215.jpg
