gratefulfrog/ArduGuitar/Ardu2/design/POC-2/InverterVolTone/SPDT-GERBER/IMG_20150125_183051.jpg

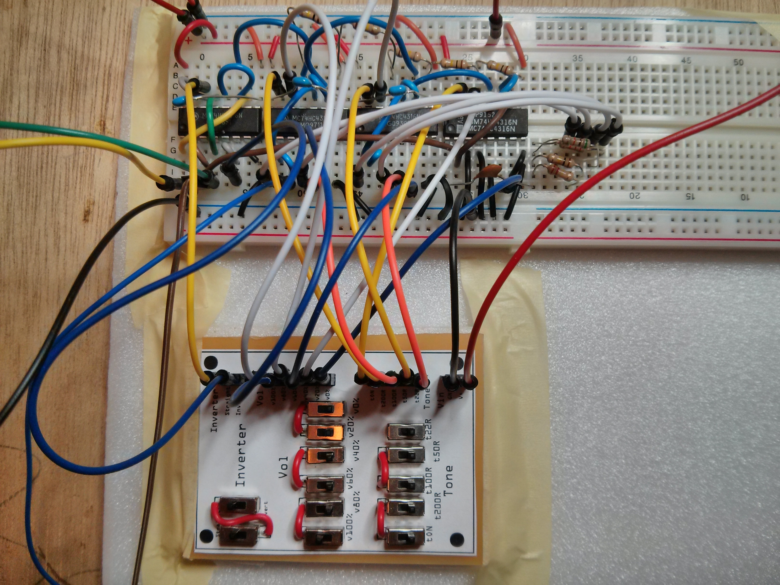
Ardu2/design/POC-2/InverterVolTone/SPDT-GERBER/IMG_20150125_183051.jpg
