gratefulfrog/ArduGuitar/Ardu2/design/POC-2/InverterVolTone/SPDT-GERBER/IMG_20150126_152714.jpg

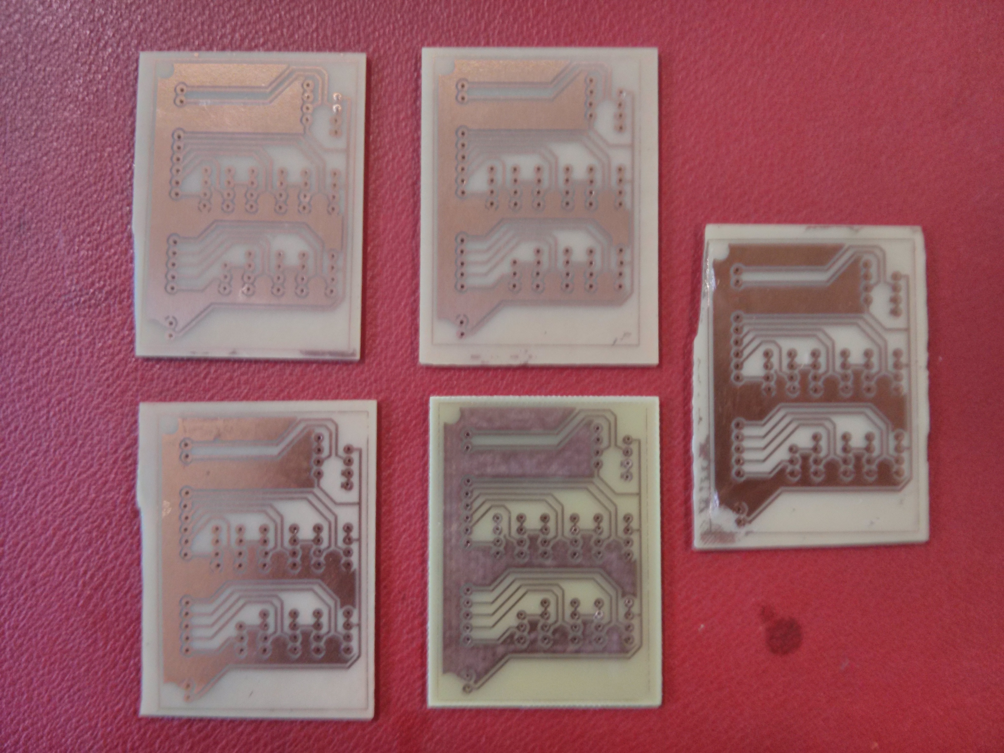
Ardu2/design/POC-2/InverterVolTone/SPDT-GERBER/IMG_20150126_152714.jpg
