gratefulfrog/ArduGuitar/Ardu2/design/POC-2/InverterVolTone/SPDT-GERBER/IMG_20150212_202227.jpg

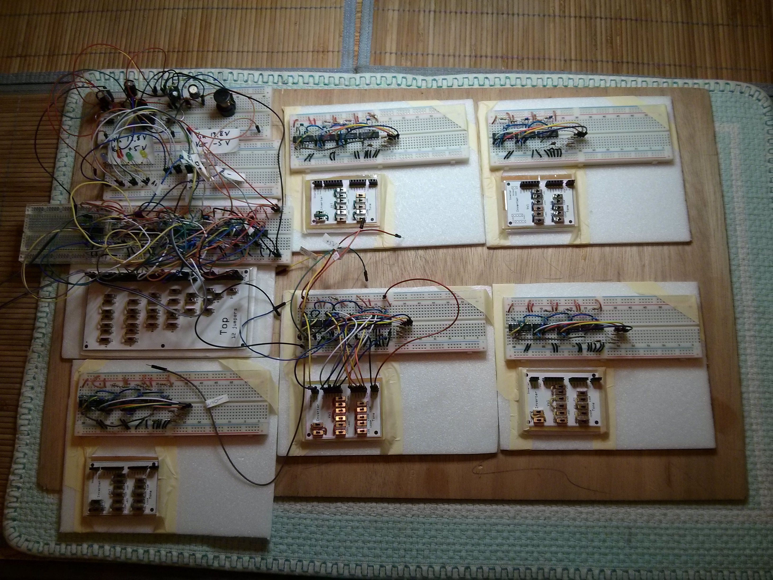
Ardu2/design/POC-2/InverterVolTone/SPDT-GERBER/IMG_20150212_202227.jpg
