gratefulfrog/ArduGuitar/Ardu2/design/POC-2/InverterVolTone/SPDT-GERBER/IMG_20150213_175602.jpg

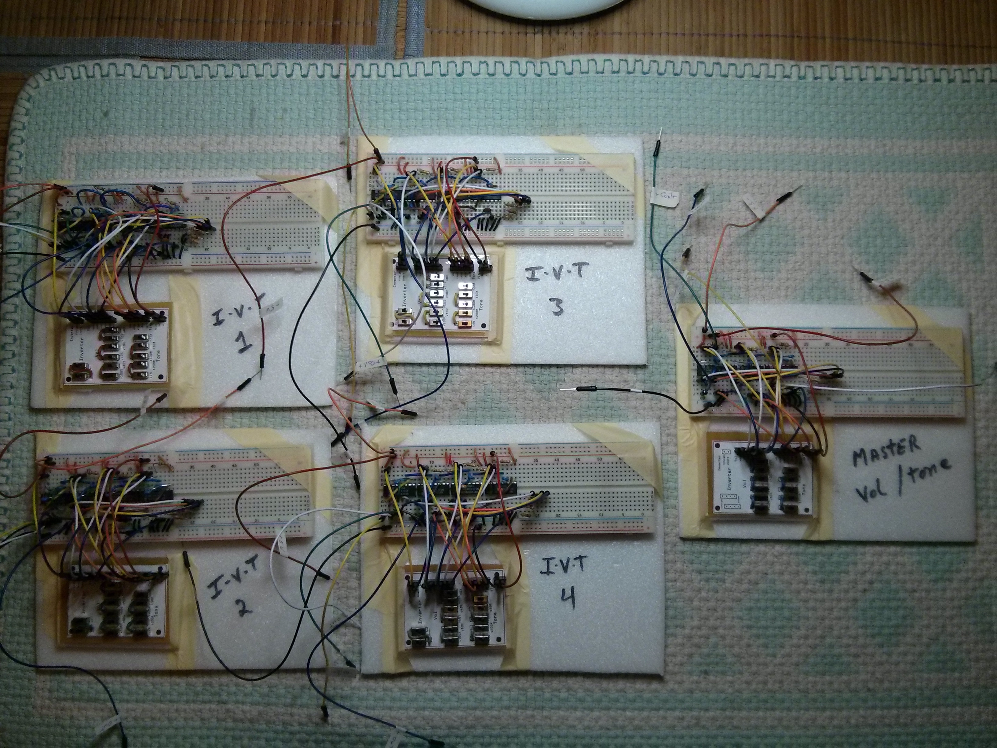
Ardu2/design/POC-2/InverterVolTone/SPDT-GERBER/IMG_20150213_175602.jpg
