gratefulfrog/ArduGuitar/Ardu2/design/POC-2/InverterVolTone/SPDT-JUMPER-Inverter-Vol-tone-Switch-PCB-big-pads_pcb.png

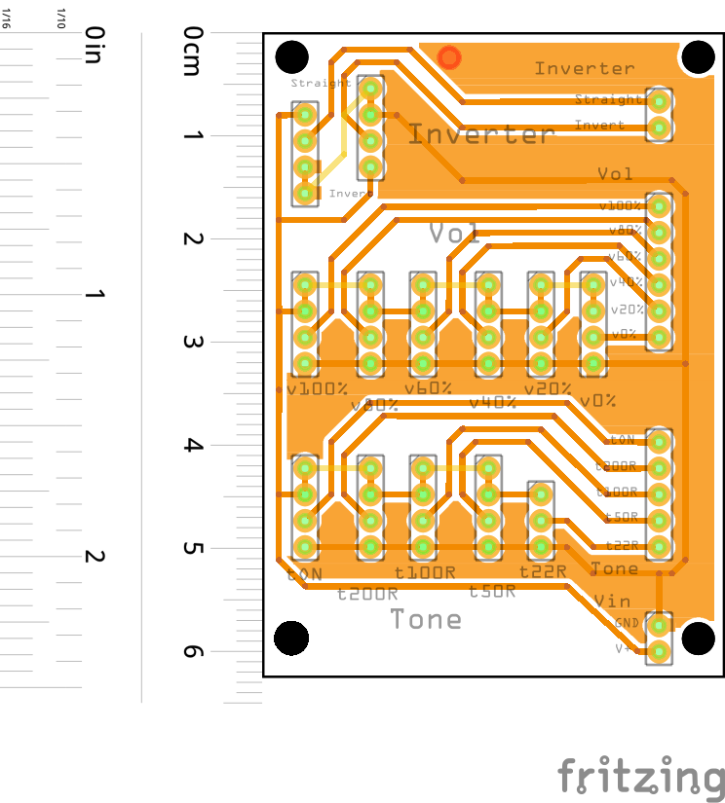
Ardu2/design/POC-2/InverterVolTone/SPDT-JUMPER-Inverter-Vol-tone-Switch-PCB-big-pads_pcb.png
