gratefulfrog/ArduGuitar/Ardu2/design/POC-2/PSU/PSU +5v_bb.png

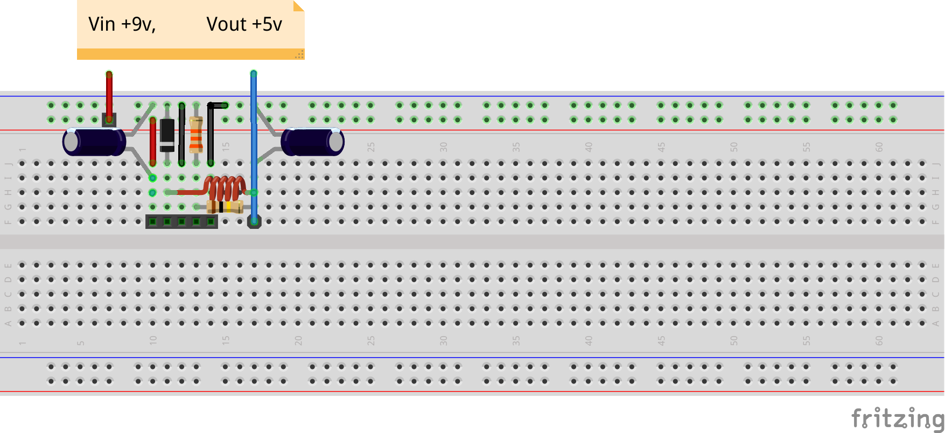
Ardu2/design/POC-2/PSU/PSU +5v_bb.png
