gratefulfrog/ArduGuitar/Ardu2/design/POC-2/PSU/PSU -5v_schem.png

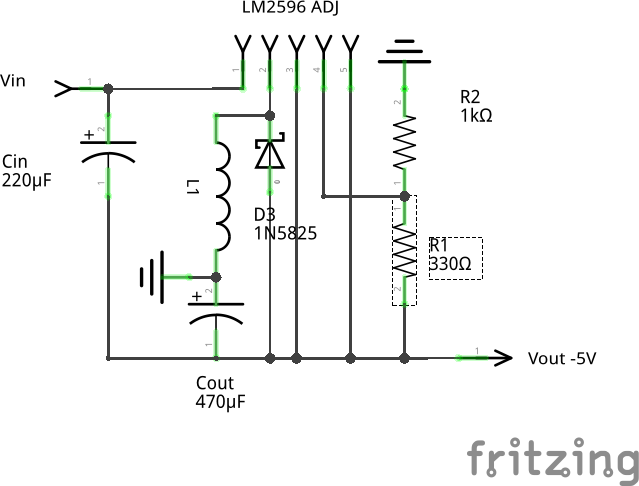
Ardu2/design/POC-2/PSU/PSU -5v_schem.png
