gratefulfrog/ArduGuitar/Ardu2/design/POC-2/SPDT JUMPER Switch-Array-PCB_pcb.png

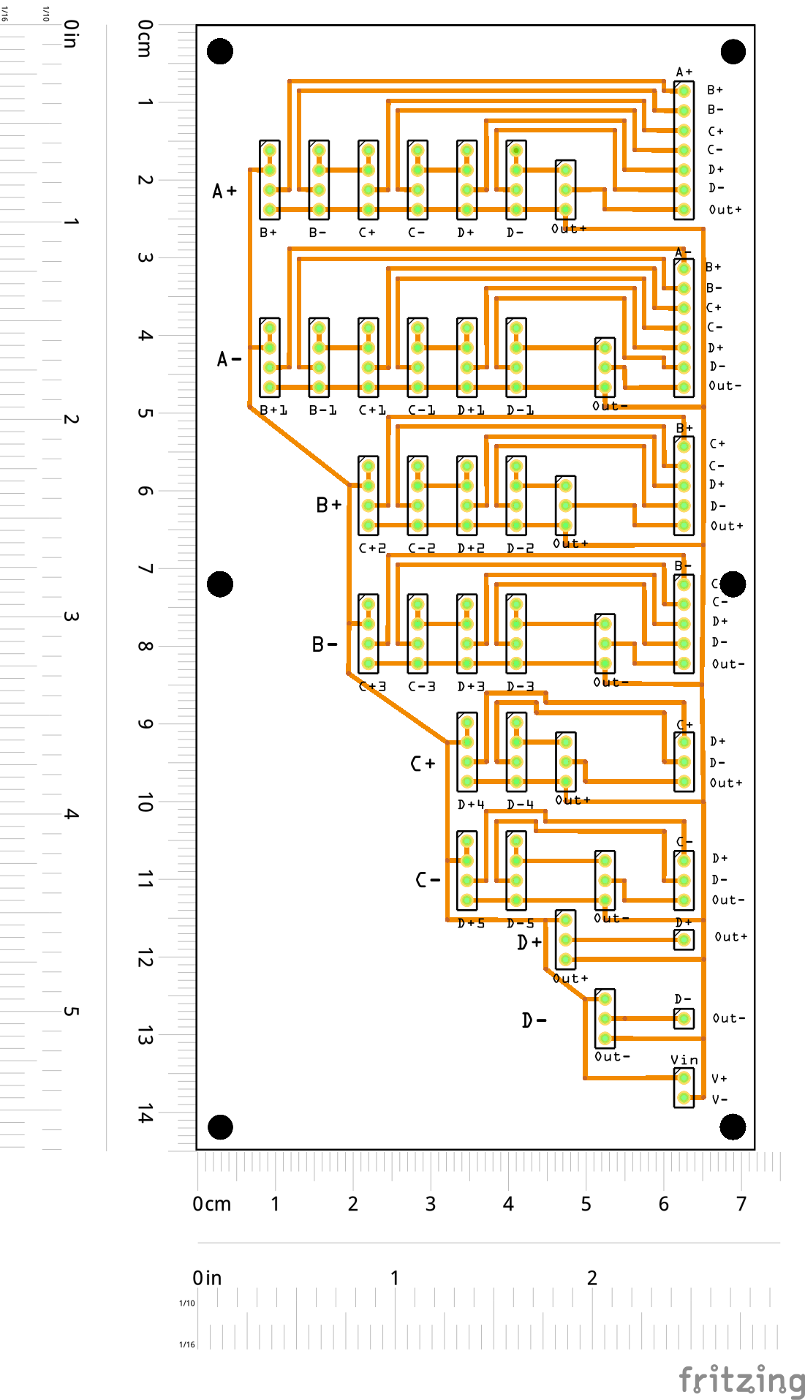
Ardu2/design/POC-2/SPDT JUMPER Switch-Array-PCB_pcb.png
