gratefulfrog/ArduGuitar/Ardu2/design/POC-2/SwitchArray/4316_Switching Schematic_schem.png

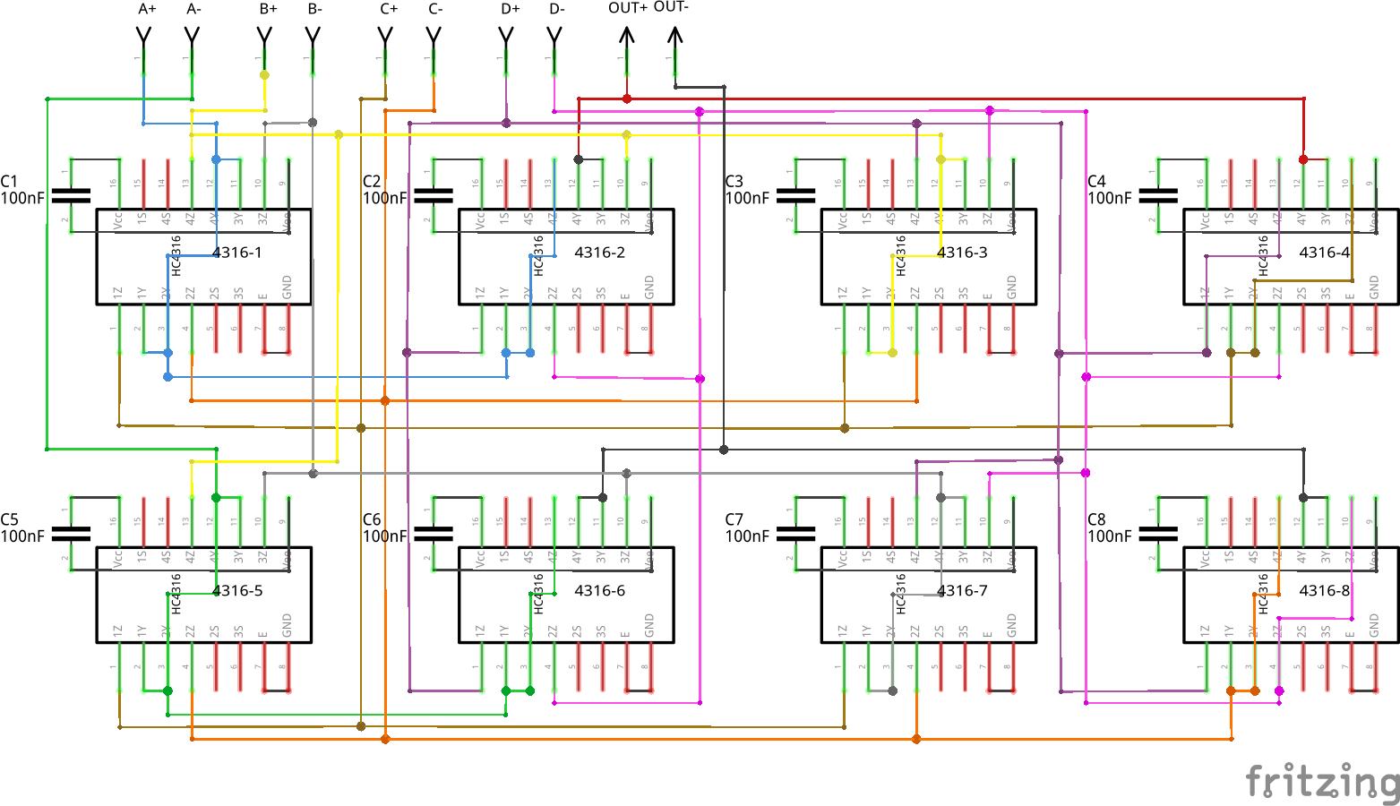
Ardu2/design/POC-2/SwitchArray/4316_Switching Schematic_schem.png
