gratefulfrog/ArduGuitar/Ardu2/design/POC-2/SwitchArray/4316a Switching Schematic_schem.png

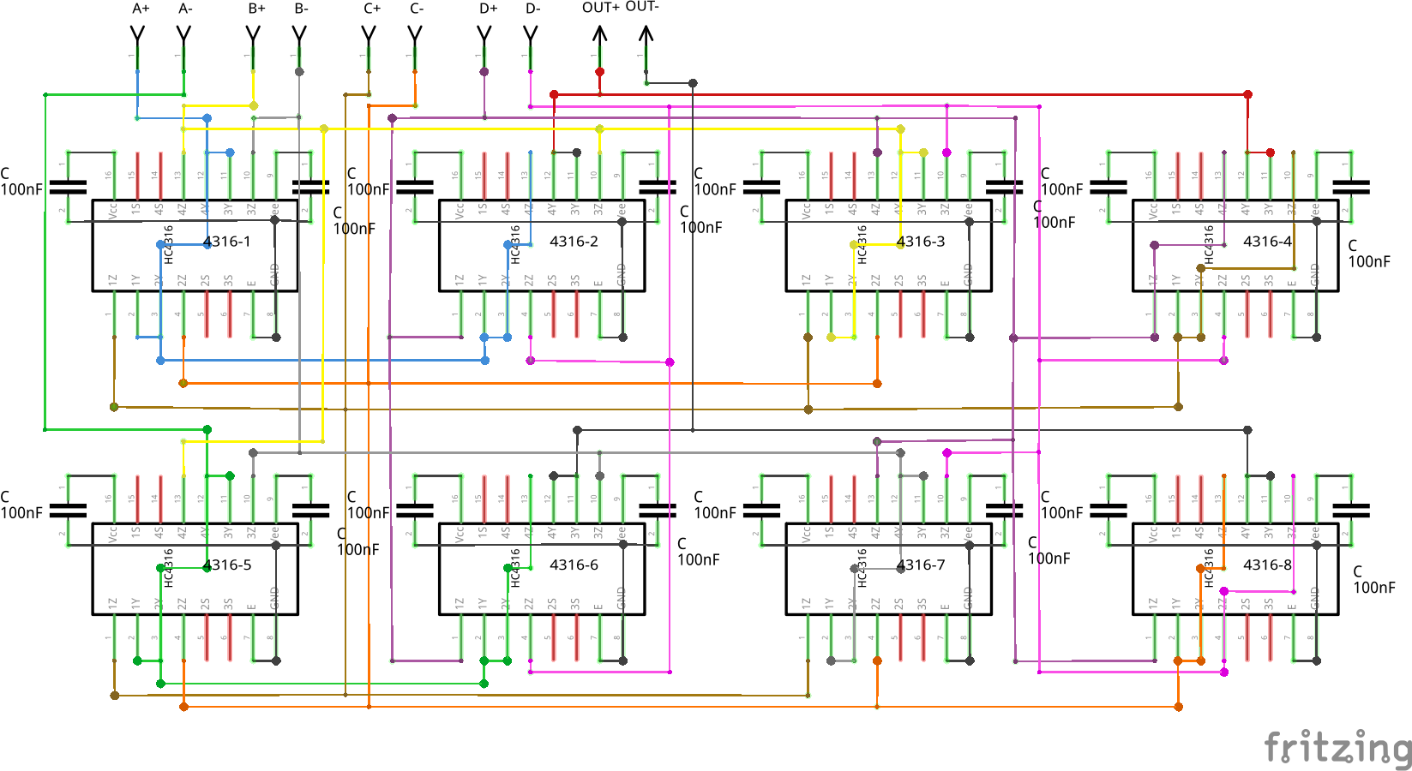
Ardu2/design/POC-2/SwitchArray/4316a Switching Schematic_schem.png
