gratefulfrog/ArduGuitar/Ardu2/design/POC-2/SwitchArray/4316AnalogSwitchArrayBreadBoard/4316ArrayPCB_pcb.png

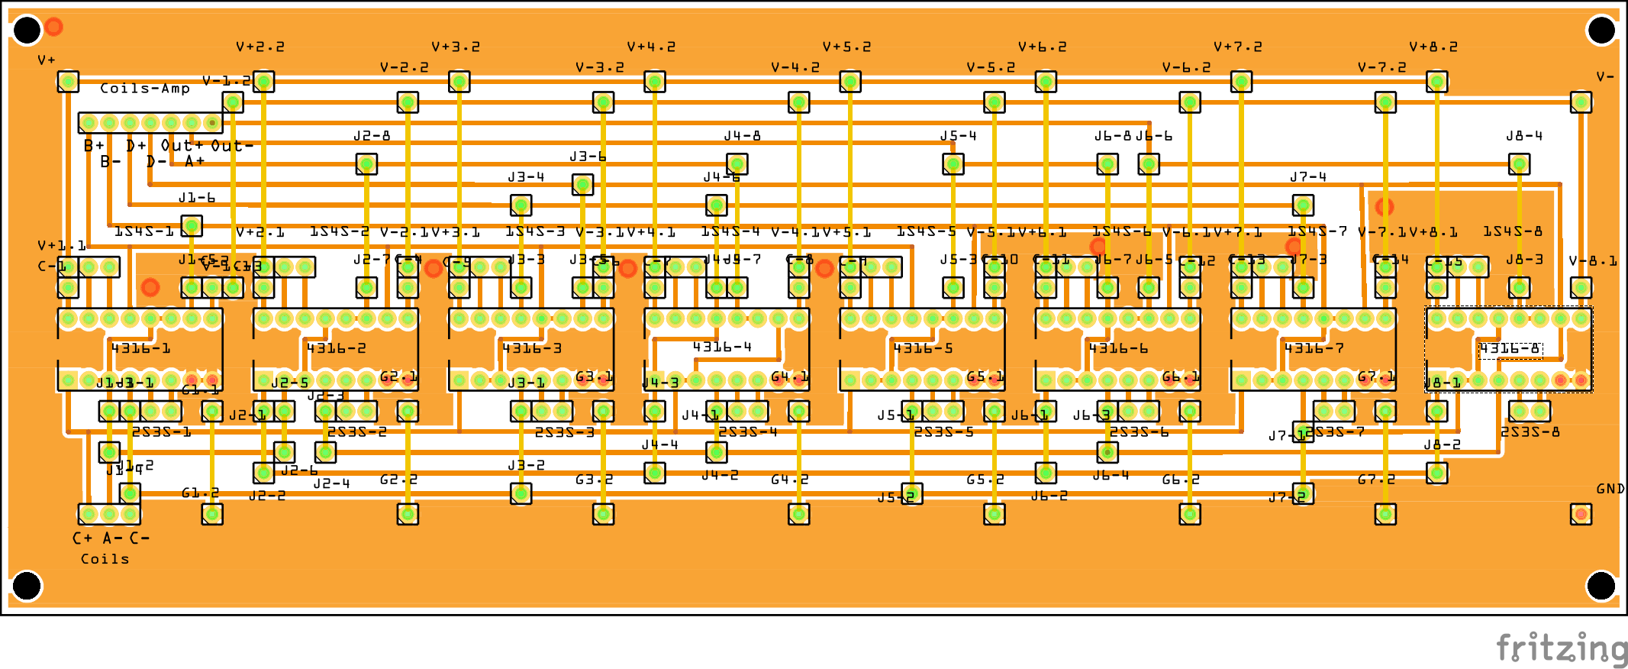
Ardu2/design/POC-2/SwitchArray/4316AnalogSwitchArrayBreadBoard/4316ArrayPCB_pcb.png
