gratefulfrog/ArduGuitar/Ardu2/design/POC-2/SwitchArray/4316AnalogSwitchArrayBreadBoard/Breadboard_LEDs_PSU.jpg

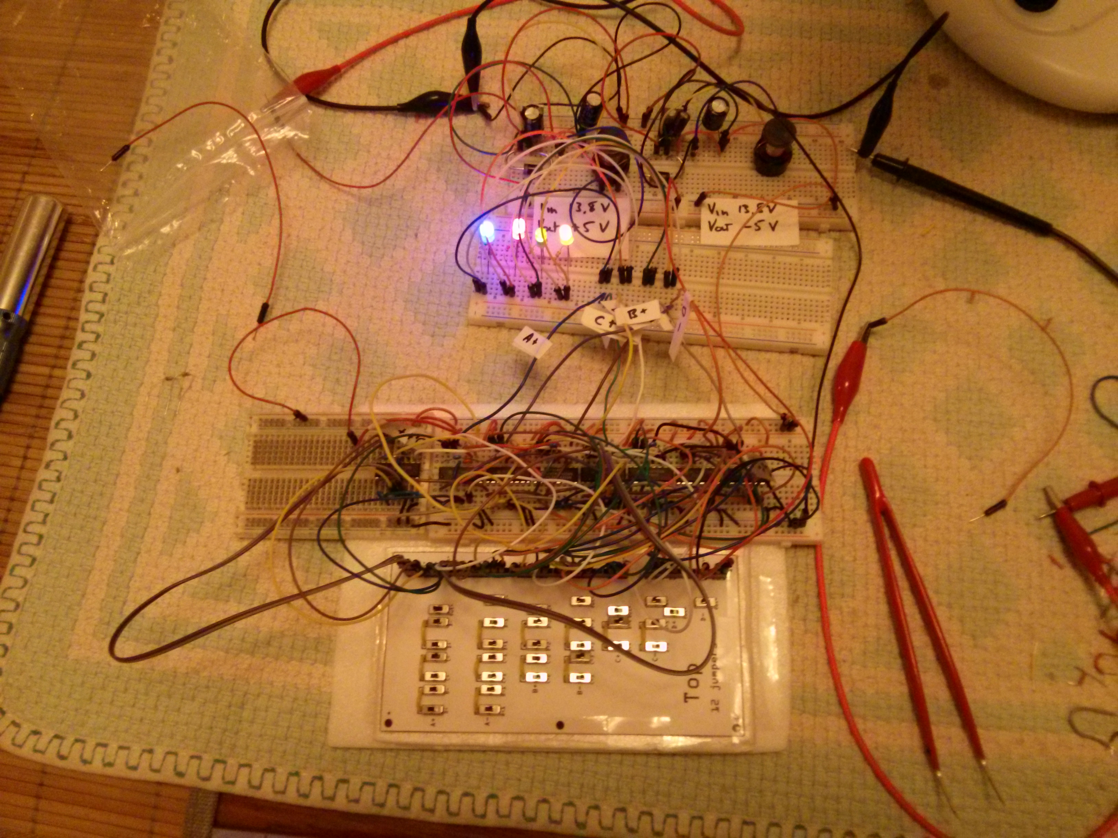
Ardu2/design/POC-2/SwitchArray/4316AnalogSwitchArrayBreadBoard/Breadboard_LEDs_PSU.jpg
