gratefulfrog/ArduGuitar/Ardu2/design/POC-2/SwitchArray/SwitchBoard/SPDT-JUMPER-Switch-Array-PCB-GERBER-Big-Pads/IMG_20141217_205641.jpg

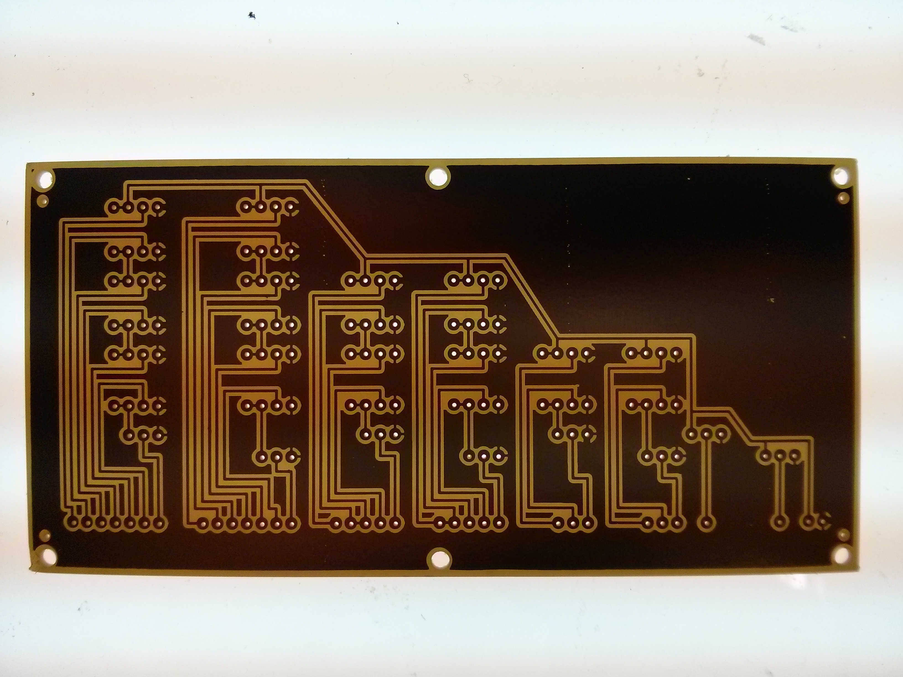
Ardu2/design/POC-2/SwitchArray/SwitchBoard/SPDT-JUMPER-Switch-Array-PCB-GERBER-Big-Pads/IMG_20141217_205641.jpg
