gratefulfrog/ArduGuitar/Ardu2/design/POC-2/SwitchArray/SwitchBoard/SPDT-JUMPER-Switch-Array-PCB-GERBER-Big-Pads/SPDT-JUMPER-Switch-Array-PCB-big-pads_pcb.png

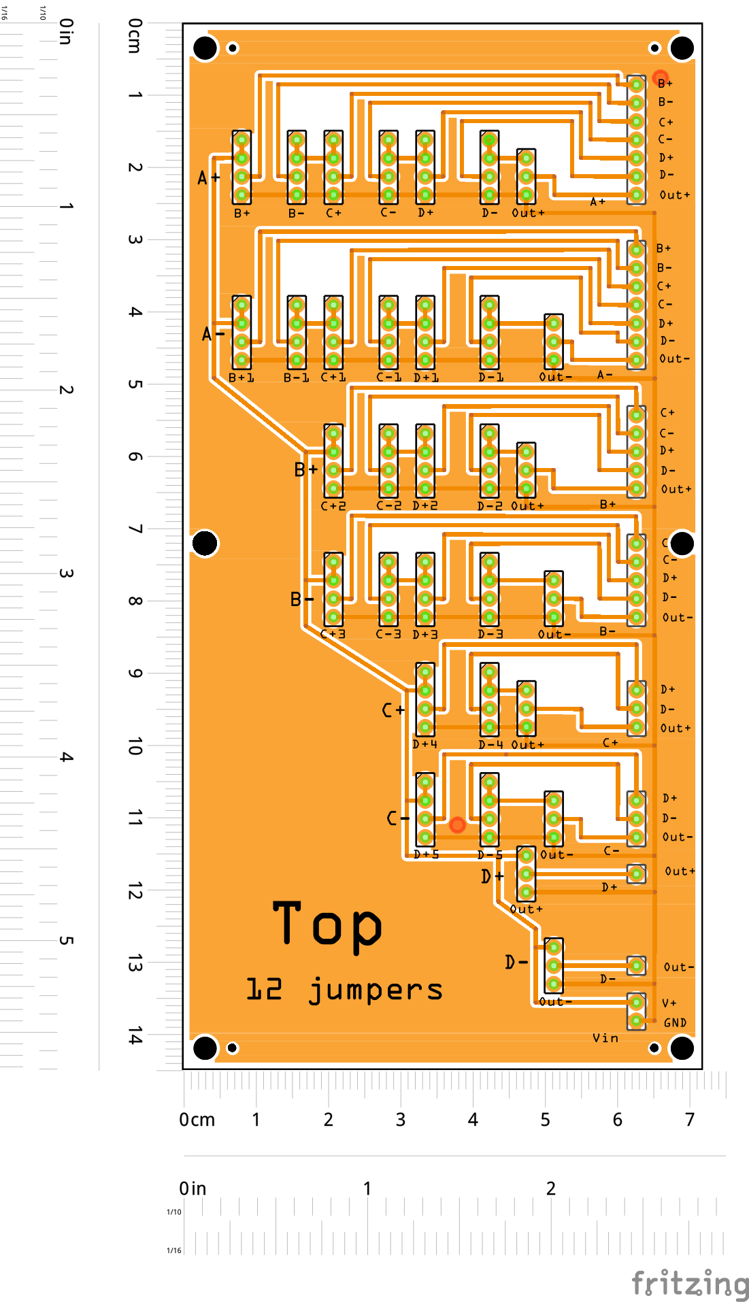
Ardu2/design/POC-2/SwitchArray/SwitchBoard/SPDT-JUMPER-Switch-Array-PCB-GERBER-Big-Pads/SPDT-JUMPER-Switch-Array-PCB-big-pads_pcb.png
