gratefulfrog/ArduGuitar/Ardu2/design/POC-3_MAX395/Fritzing Projects/Inverter-Vol-Tone-Scematic-Audio-d_schem.png

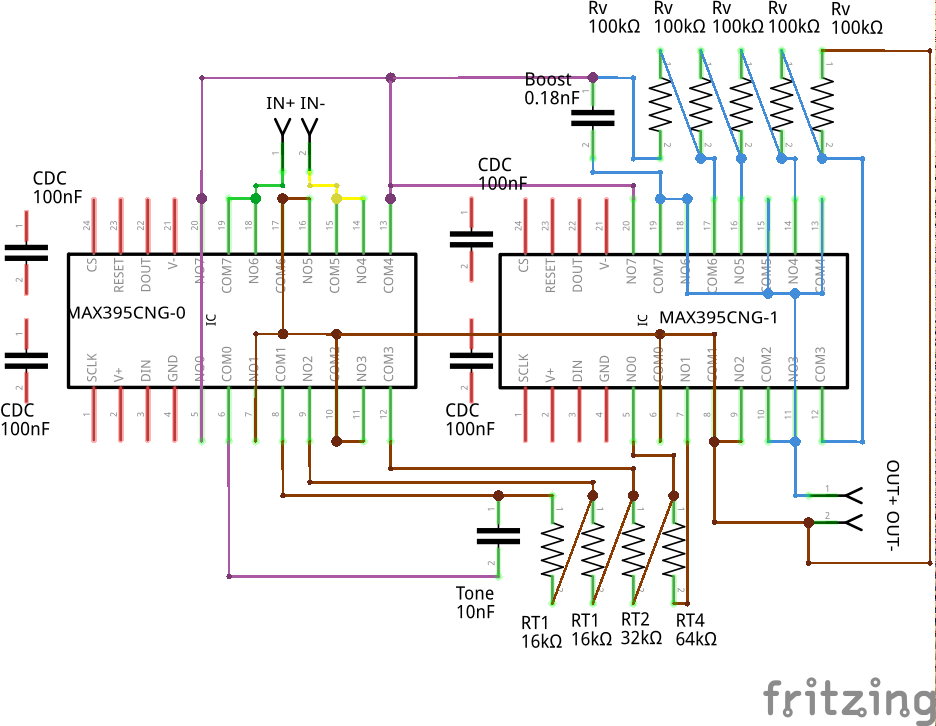
Ardu2/design/POC-3_MAX395/Fritzing Projects/Inverter-Vol-Tone-Scematic-Audio-d_schem.png
