gratefulfrog/ArduGuitar/Ardu2/design/POC-3_MAX395/Fritzing Projects/Master-Vol-Tone-Scematic-d_schem.png

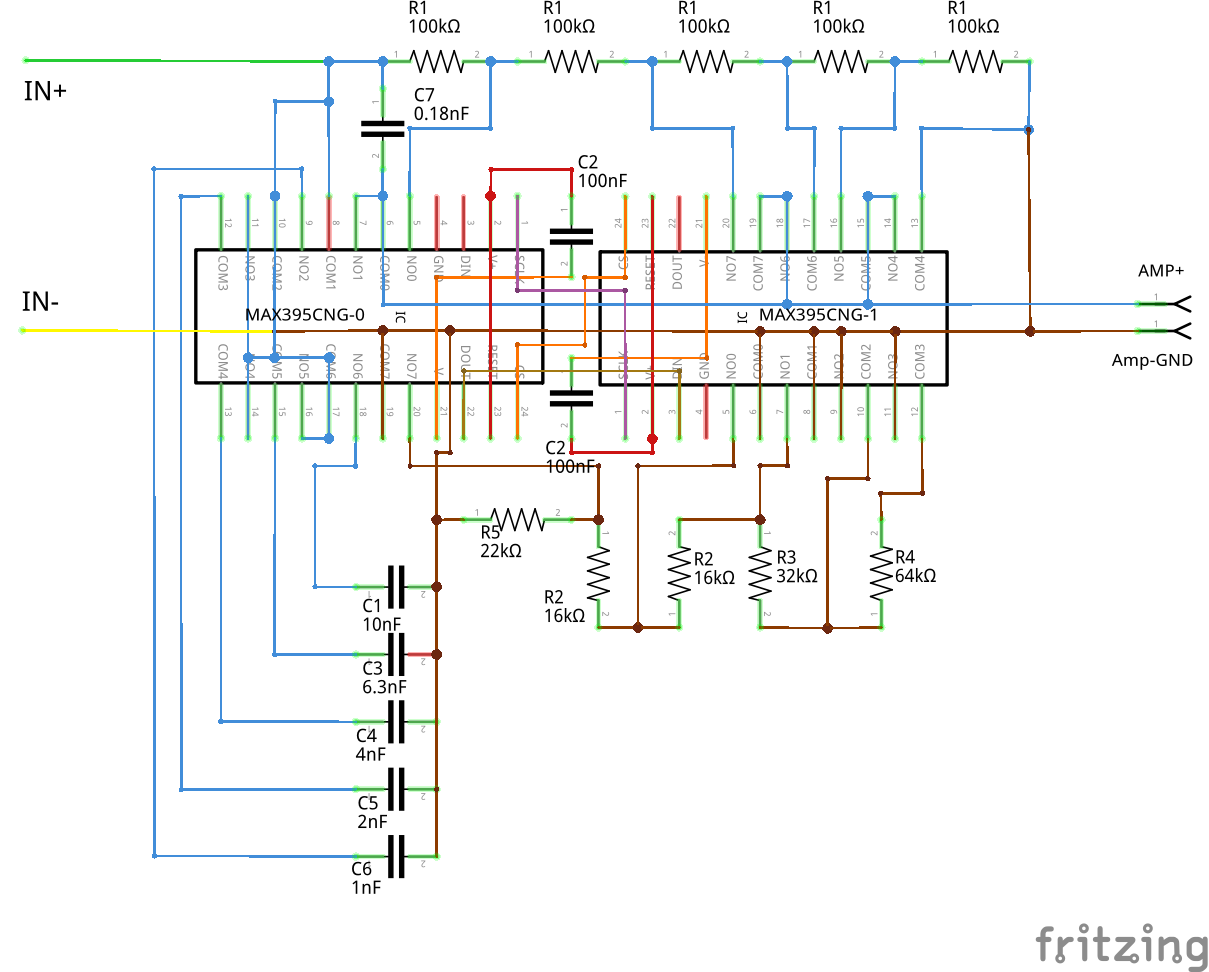
Ardu2/design/POC-3_MAX395/Fritzing Projects/Master-Vol-Tone-Scematic-d_schem.png
