gratefulfrog/ArduGuitar/Ardu2/design/POC-3_MAX395/Fritzing Projects/ReverseCurrentProtection_schem.png

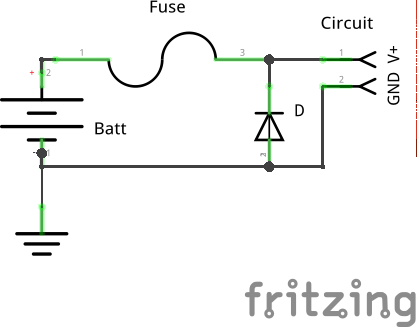
Ardu2/design/POC-3_MAX395/Fritzing Projects/ReverseCurrentProtection_schem.png
