gratefulfrog/ArduGuitar/Ardu2/design/POC-3_MAX395/Fritzing Projects/Vactrol Direct Shunt a_schem.png

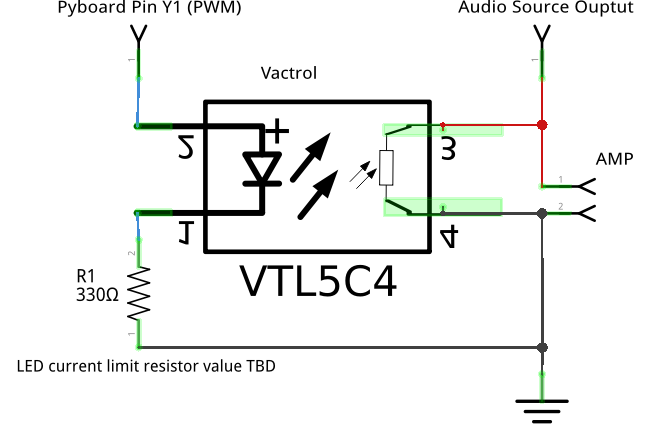
Ardu2/design/POC-3_MAX395/Fritzing Projects/Vactrol Direct Shunt a_schem.png
