gratefulfrog/ArduGuitar/Ardu2/design/POC-3_MAX395/HMI/HMI PCB 00_pcb.png

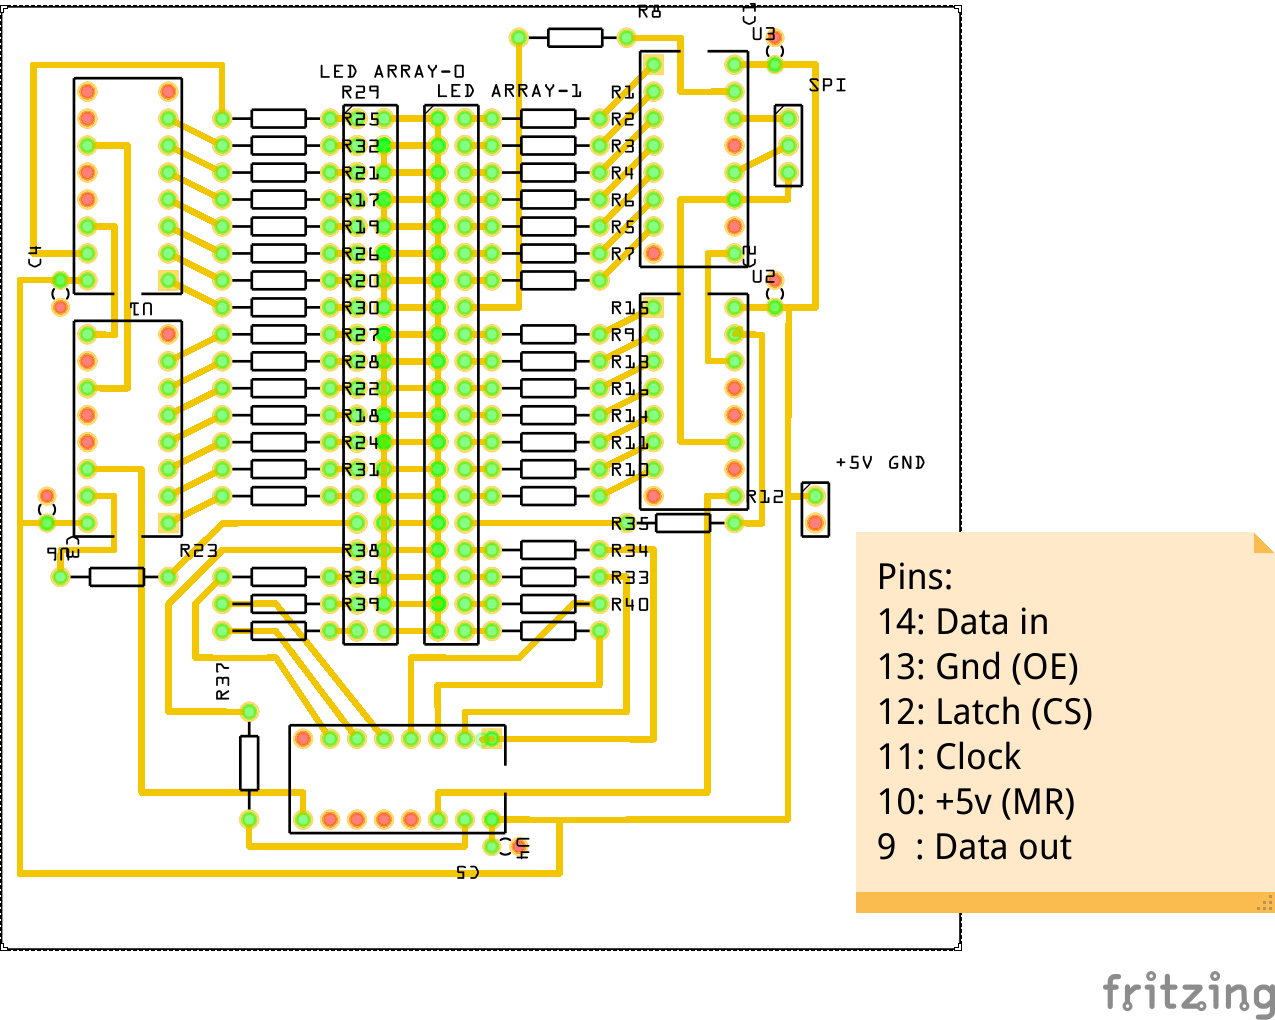
Ardu2/design/POC-3_MAX395/HMI/HMI PCB 00_pcb.png
