gratefulfrog/ArduGuitar/Ardu2/design/POC-3_MAX395/HMI/Images/boltplus-Butt.jpg

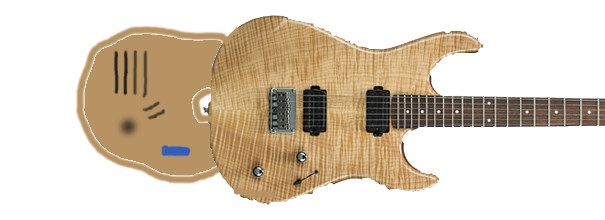
Ardu2/design/POC-3_MAX395/HMI/Images/boltplus-Butt.jpg
