gratefulfrog/ArduGuitar/Ardu2/design/POC-3_MAX395/HMI/Images/boltplus-edge-0.bmp

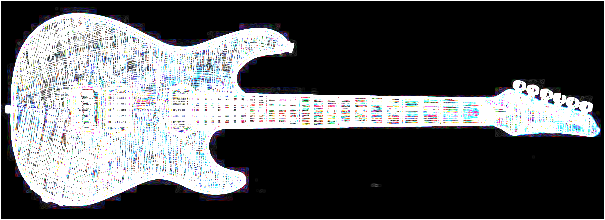
Ardu2/design/POC-3_MAX395/HMI/Images/boltplus-edge-0.bmp
