gratefulfrog/ArduGuitar/Ardu2/design/POC-3_MAX395/HMI/Images/boltplus-main.jpg

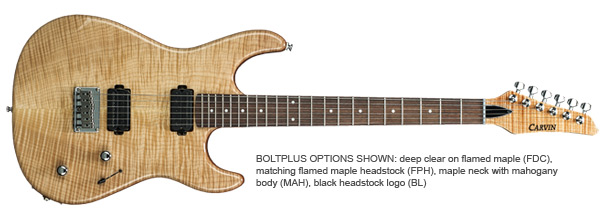
Ardu2/design/POC-3_MAX395/HMI/Images/boltplus-main.jpg
