gratefulfrog/ArduGuitar/Ardu2/design/POC-3_MAX395/HMI/Images/HMI_03.png

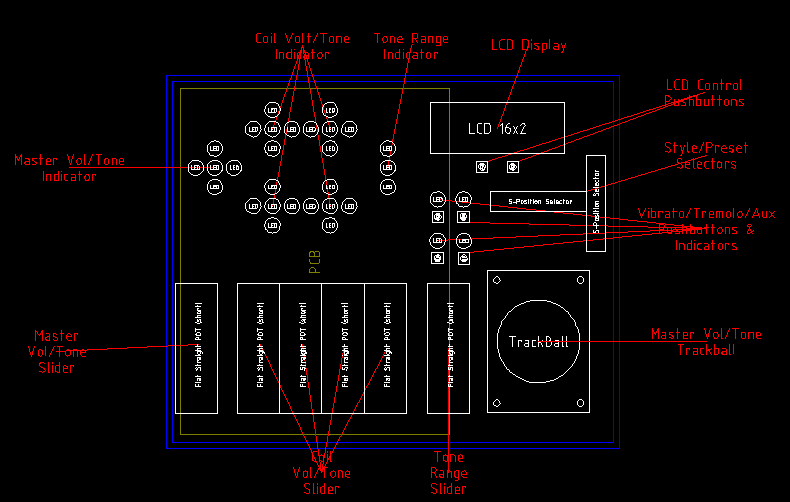
Ardu2/design/POC-3_MAX395/HMI/Images/HMI_03.png
