gratefulfrog/ArduGuitar/Ardu2/design/POC-3_MAX395/HMI/Images/HMI_03_Guitar_Cut_01.png

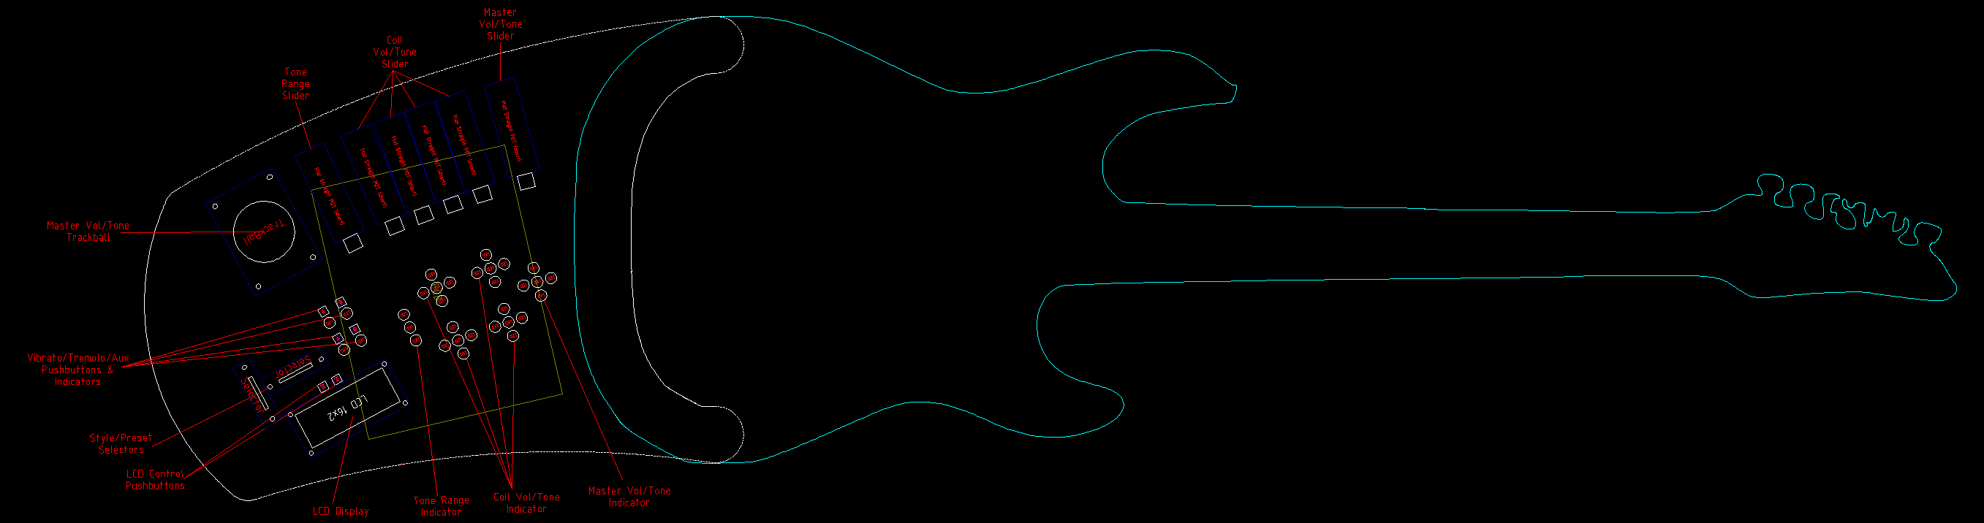
Ardu2/design/POC-3_MAX395/HMI/Images/HMI_03_Guitar_Cut_01.png
