gratefulfrog/ArduGuitar/Ardu2/design/POC-3_MAX395/HMI/Images/IMG_20151107_185758.jpg

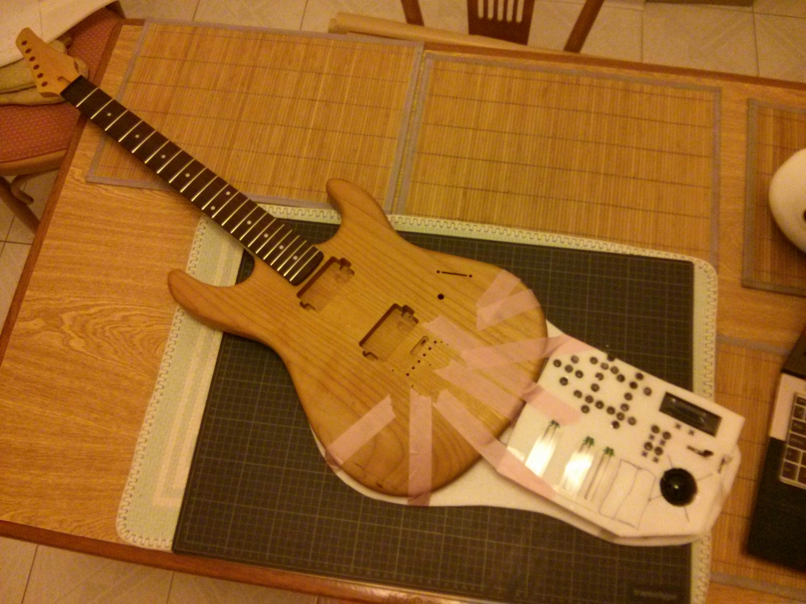
Ardu2/design/POC-3_MAX395/HMI/Images/IMG_20151107_185758.jpg
