gratefulfrog/ArduGuitar/Ardu2/design/POC-3_MAX395/HMI/Images/IMG_20151111_171045.jpg

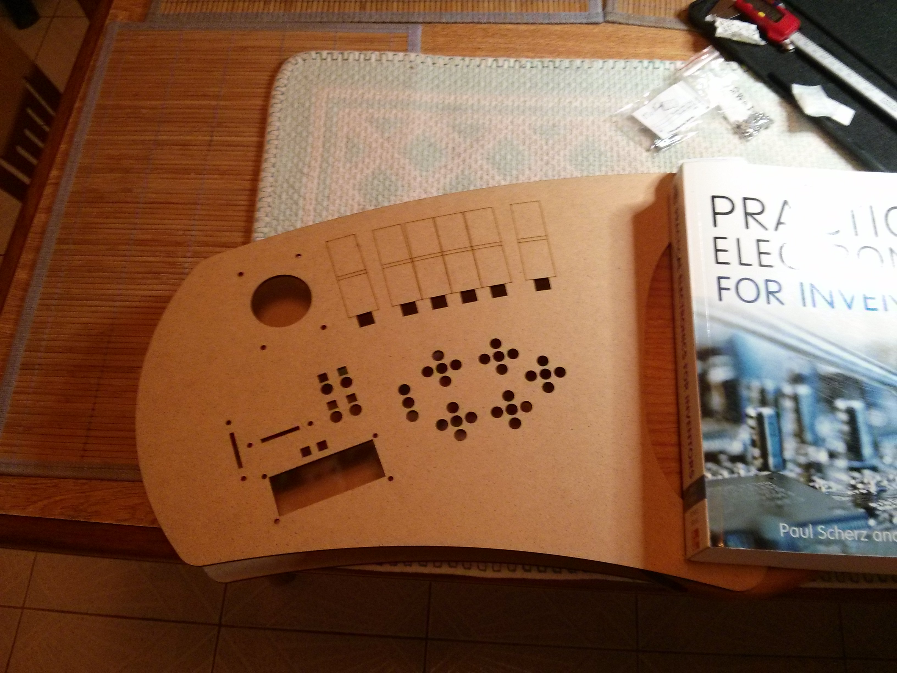
Ardu2/design/POC-3_MAX395/HMI/Images/IMG_20151111_171045.jpg
