gratefulfrog/ArduGuitar/Ardu2/design/POC-3_MAX395/HMI/Images/IMG_20151111_171104.jpg

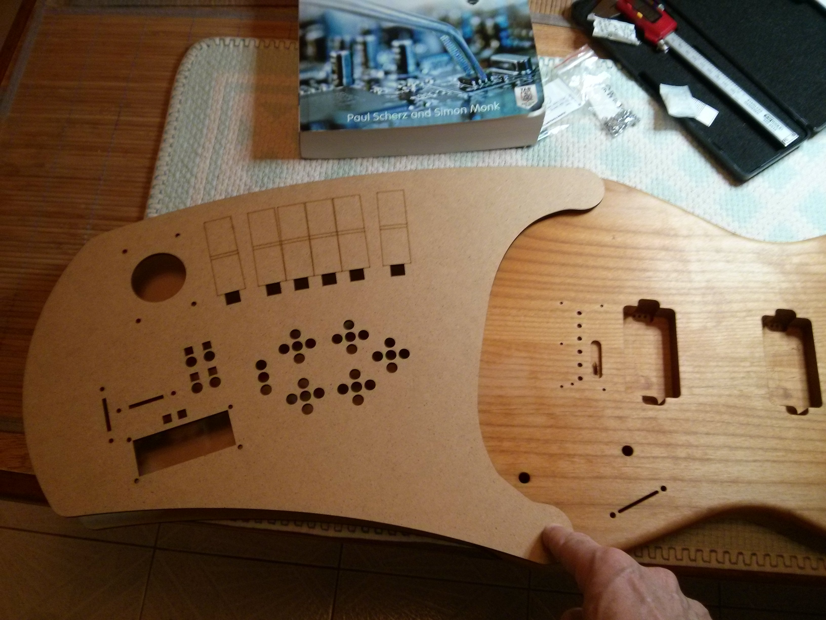
Ardu2/design/POC-3_MAX395/HMI/Images/IMG_20151111_171104.jpg
