gratefulfrog/ArduGuitar/Ardu2/design/POC-3_MAX395/HMI/Images/IMG_20151115_192312.jpg

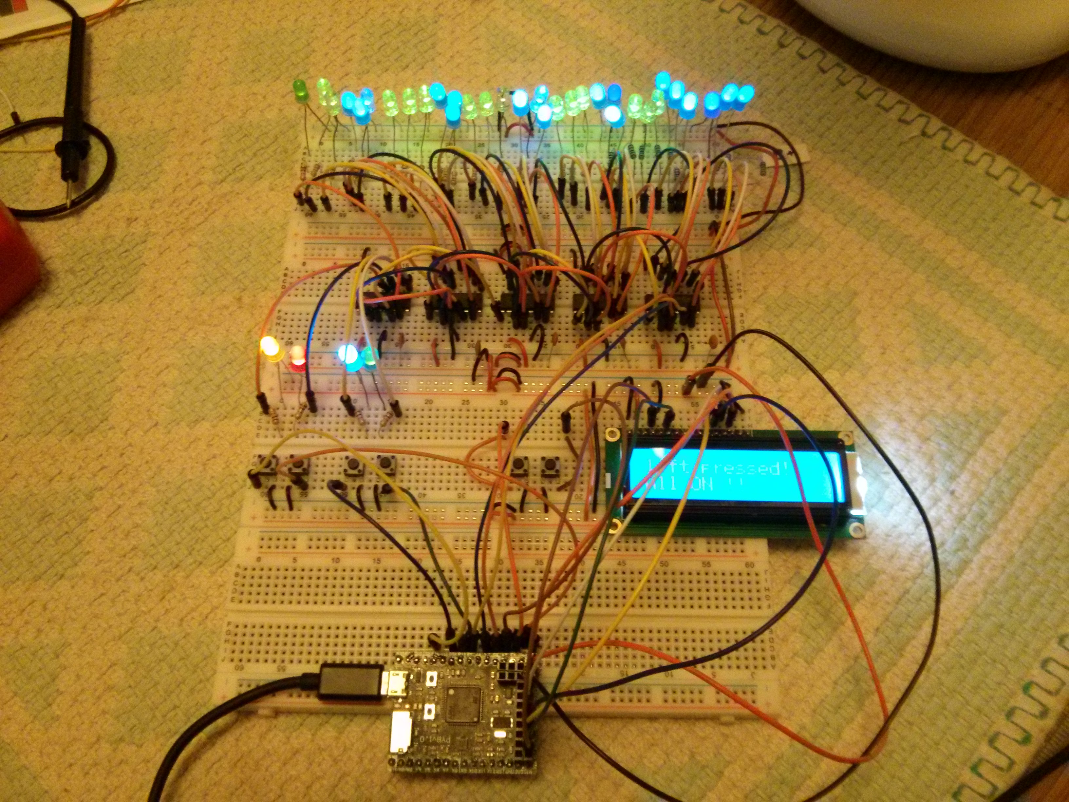
Ardu2/design/POC-3_MAX395/HMI/Images/IMG_20151115_192312.jpg
