gratefulfrog/ArduGuitar/Ardu2/design/POC-3_MAX395/HMI/Images/IMG_20151118_225135.jpg

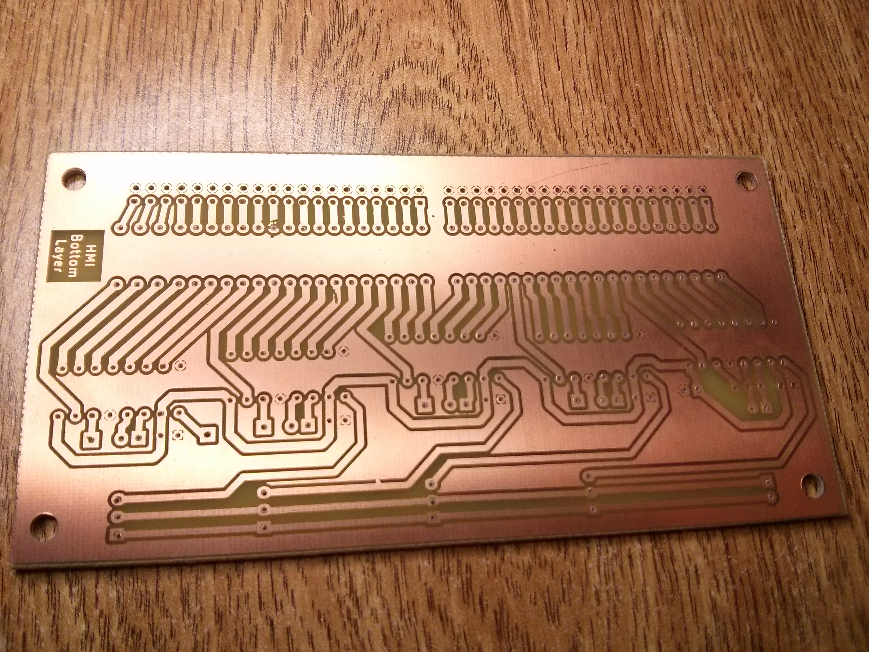
Ardu2/design/POC-3_MAX395/HMI/Images/IMG_20151118_225135.jpg
