gratefulfrog/ArduGuitar/Ardu2/design/POC-3_MAX395/HMI/Images/IMG_20151214_121152.jpg

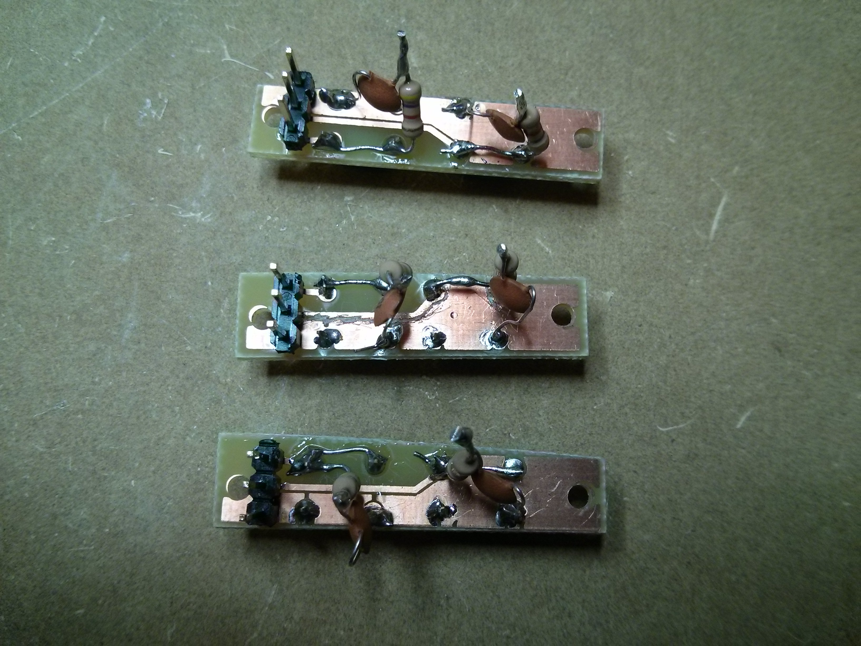
Ardu2/design/POC-3_MAX395/HMI/Images/IMG_20151214_121152.jpg
