gratefulfrog/ArduGuitar/Ardu2/design/POC-3_MAX395/HMI/Images/IMG_20160127_210350.jpg

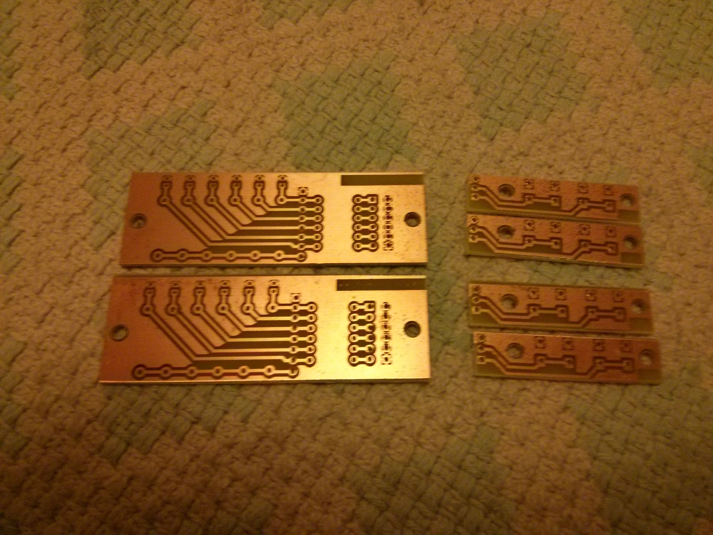
Ardu2/design/POC-3_MAX395/HMI/Images/IMG_20160127_210350.jpg
