gratefulfrog/ArduGuitar/Ardu2/design/POC-3_MAX395/HMI/Images/IMG_20160401_185954.jpg

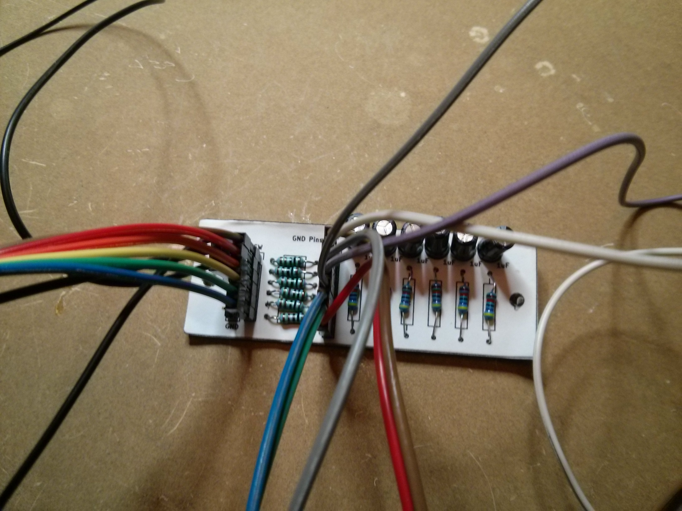
Ardu2/design/POC-3_MAX395/HMI/Images/IMG_20160401_185954.jpg
