gratefulfrog/ArduGuitar/Ardu2/design/POC-3_MAX395/HMI/Images/IMG_20160405_194827.jpg

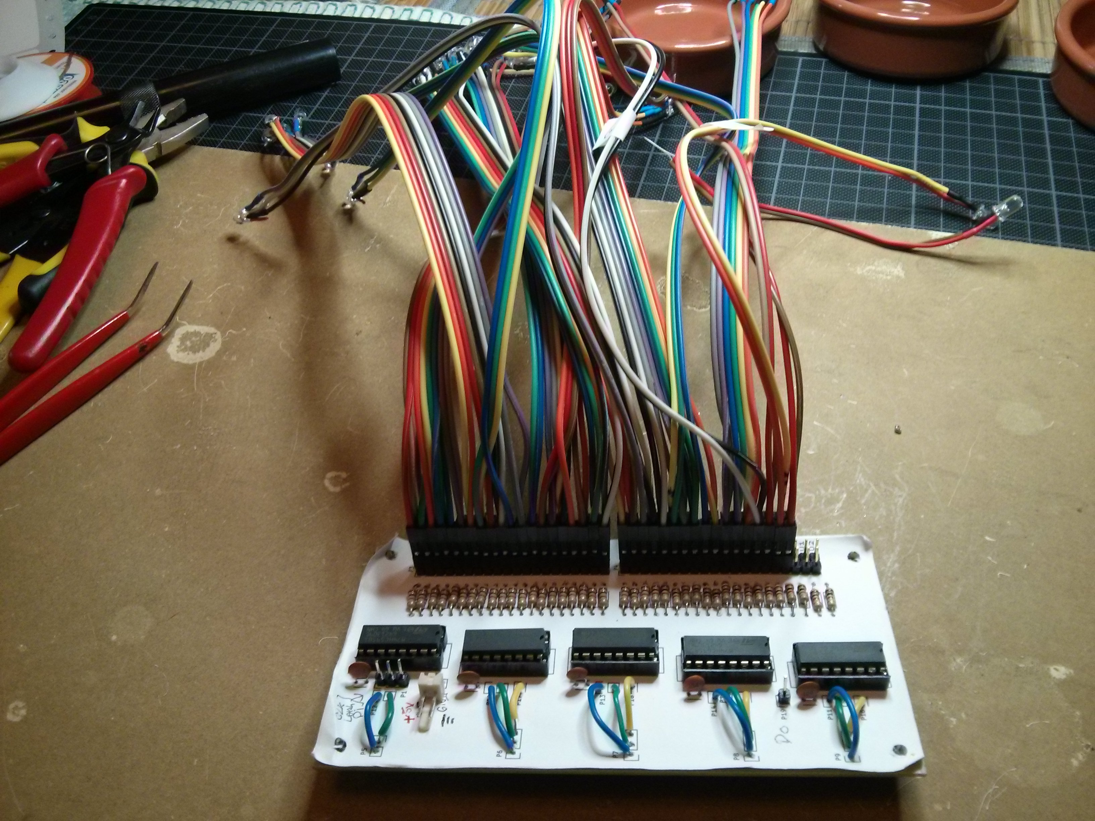
Ardu2/design/POC-3_MAX395/HMI/Images/IMG_20160405_194827.jpg
