gratefulfrog/ArduGuitar/Ardu2/design/POC-3_MAX395/HMI/Images/IMG_20161121_161558.jpg

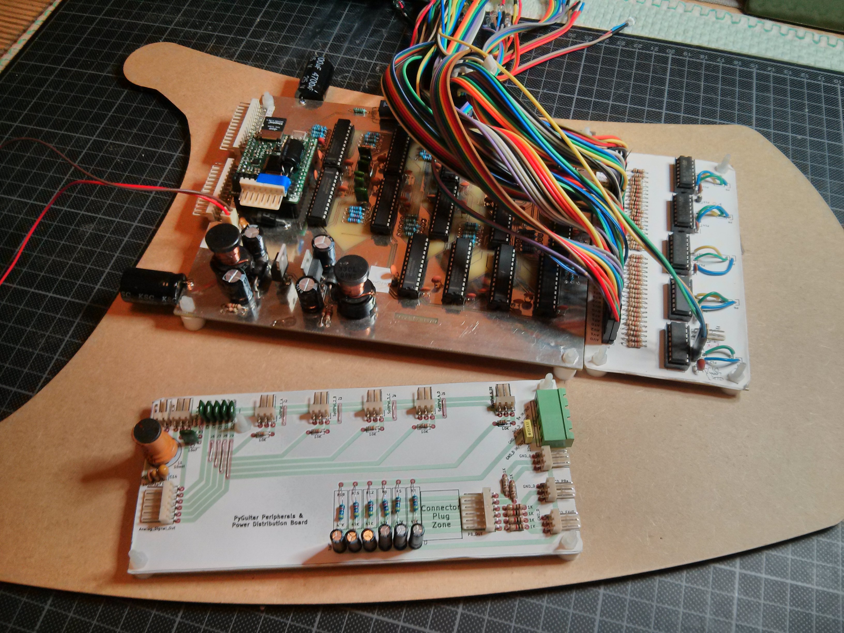
Ardu2/design/POC-3_MAX395/HMI/Images/IMG_20161121_161558.jpg
