gratefulfrog/ArduGuitar/Ardu2/design/POC-3_MAX395/HMI/Images/IMG_20161122_150657.jpg

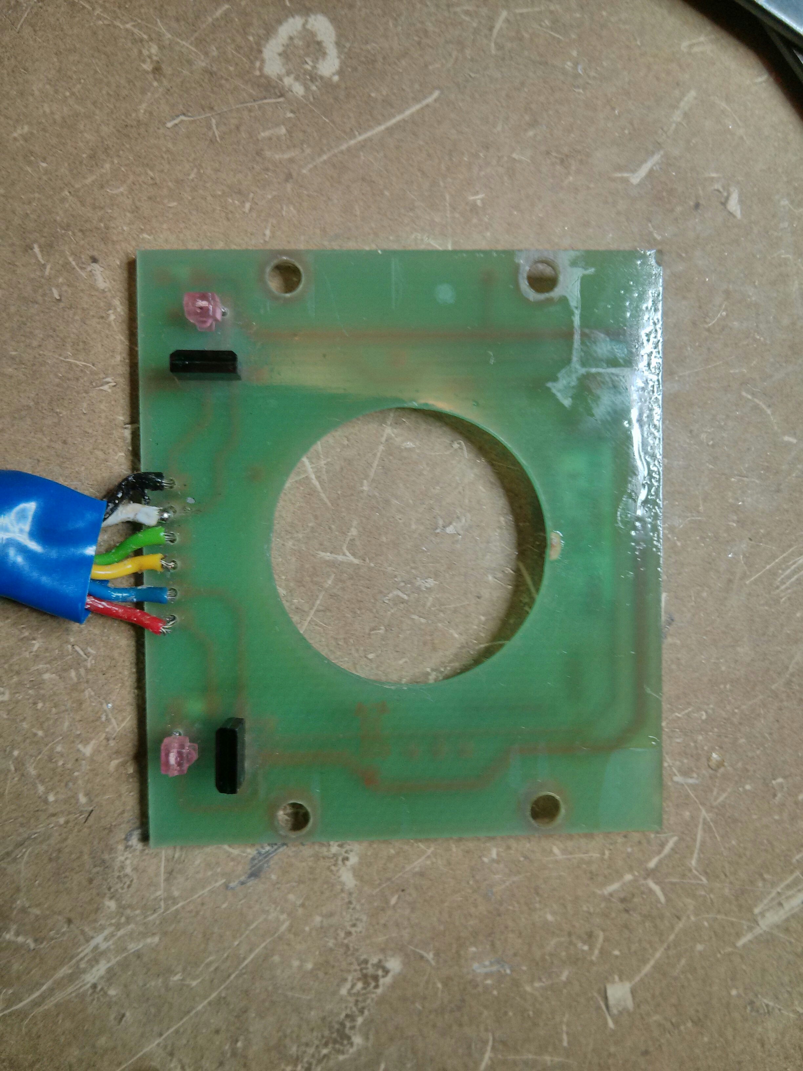
Ardu2/design/POC-3_MAX395/HMI/Images/IMG_20161122_150657.jpg
