gratefulfrog/ArduGuitar/Ardu2/design/POC-3_MAX395/HMI/Images/IMG_20161122_162938.jpg

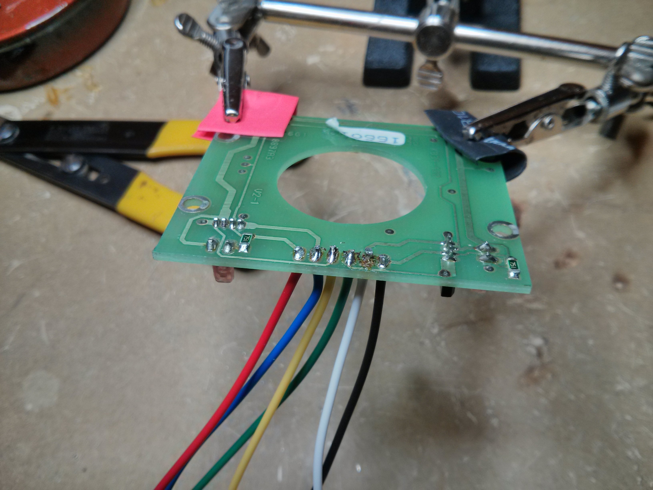
Ardu2/design/POC-3_MAX395/HMI/Images/IMG_20161122_162938.jpg
