gratefulfrog/ArduGuitar/Ardu2/design/POC-3_MAX395/HMI/Images/PB076097.JPG

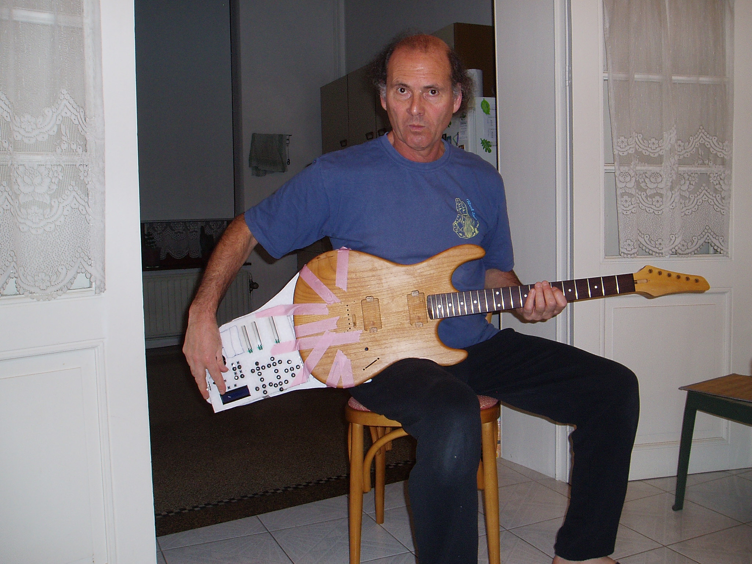
Ardu2/design/POC-3_MAX395/HMI/Images/PB076097.JPG
