gratefulfrog/ArduGuitar/Ardu2/design/POC-3_MAX395/HMI/KicadProjects/2PB with Headers/SVG/2PB with Headers-brd.svg.png

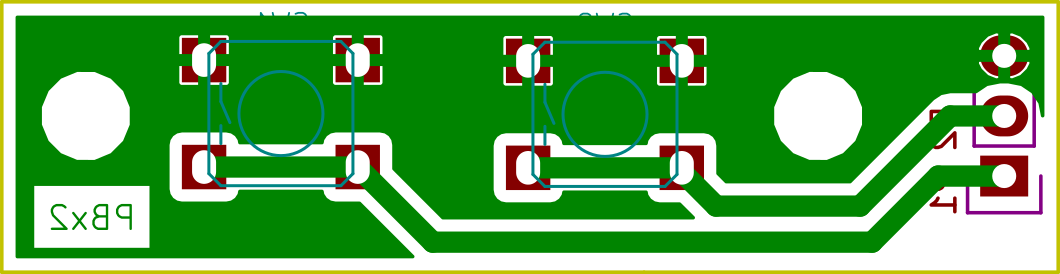
Ardu2/design/POC-3_MAX395/HMI/KicadProjects/2PB with Headers/SVG/2PB with Headers-brd.svg.png
