gratefulfrog/ArduGuitar/Ardu2/design/POC-3_MAX395/HMI/KicadProjects/Main HMI Circuit/Images/IMG_20151119_191544.jpg

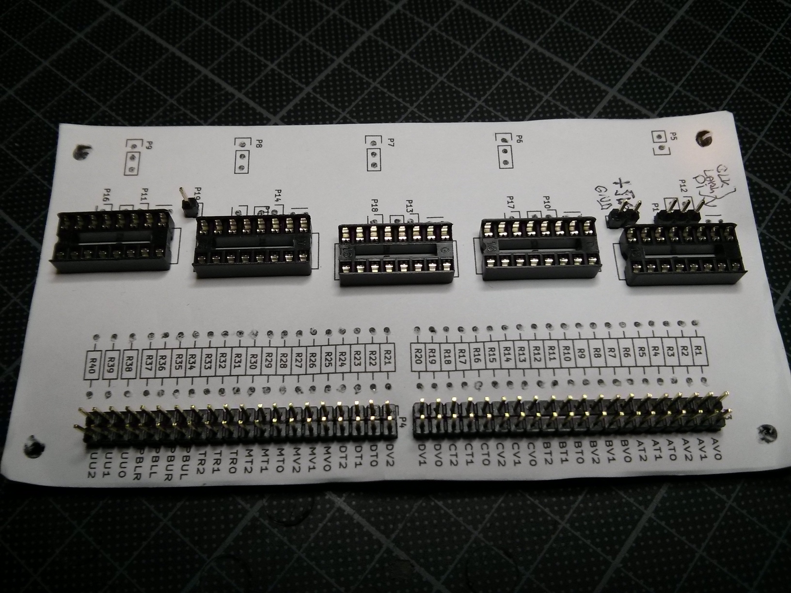
Ardu2/design/POC-3_MAX395/HMI/KicadProjects/Main HMI Circuit/Images/IMG_20151119_191544.jpg
