gratefulfrog/ArduGuitar/Ardu2/design/POC-3_MAX395/HMI/KicadProjects/Main HMI Circuit/Images/IMG_20151120_171828.jpg

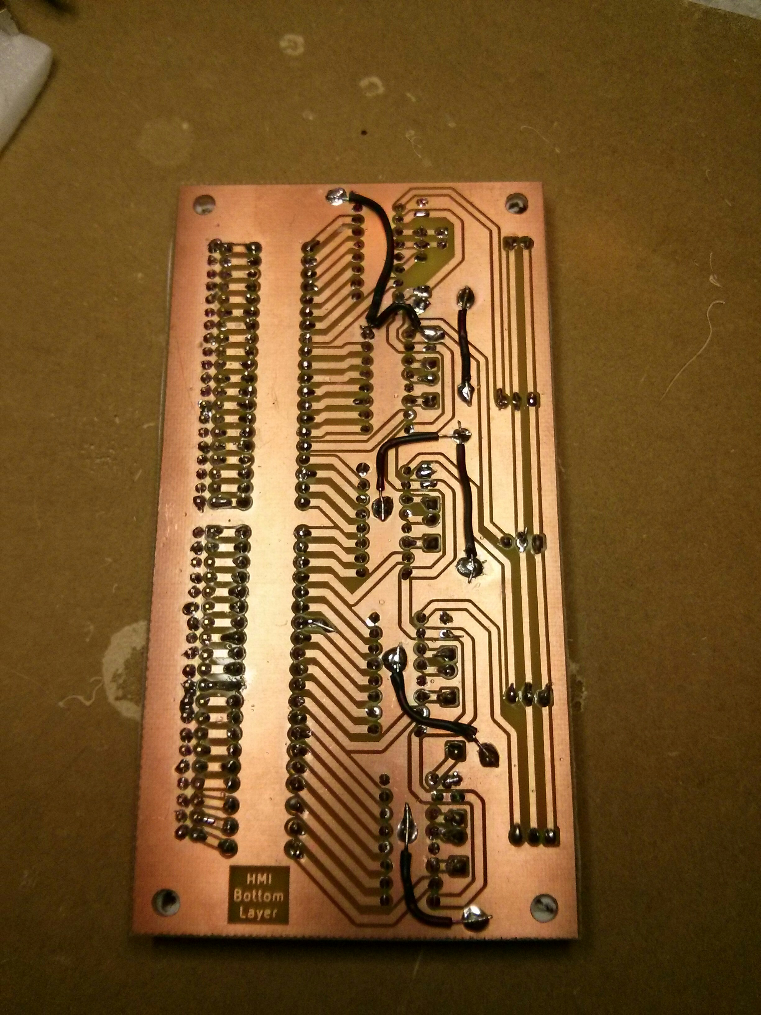
Ardu2/design/POC-3_MAX395/HMI/KicadProjects/Main HMI Circuit/Images/IMG_20151120_171828.jpg
