gratefulfrog/ArduGuitar/Ardu2/design/POC-3_MAX395/HMI/KicadProjects/Multi-PB-Debounce Circuit/SVG/Multi-PB-Debounce Circuit.sch.svg.png

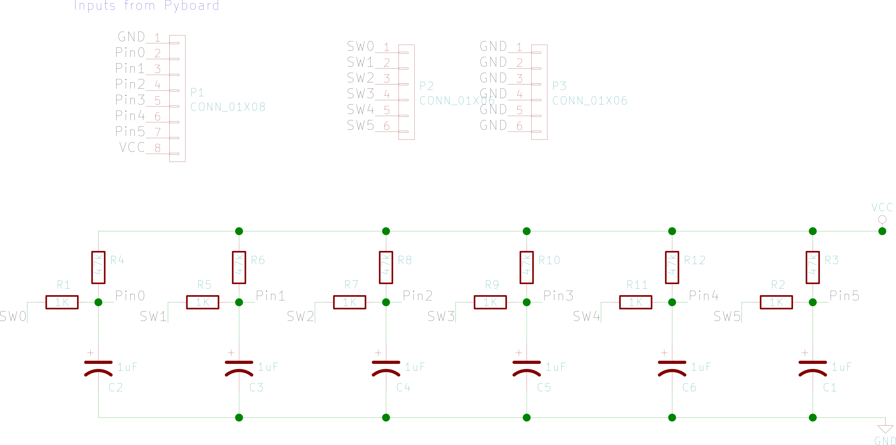
Ardu2/design/POC-3_MAX395/HMI/KicadProjects/Multi-PB-Debounce Circuit/SVG/Multi-PB-Debounce Circuit.sch.svg.png
