gratefulfrog/ArduGuitar/Ardu2/design/POC-3_MAX395/HMI/KicadProjects/PowerSupplyConnections Circuit/Images/IMG_20160601_153843.jpg

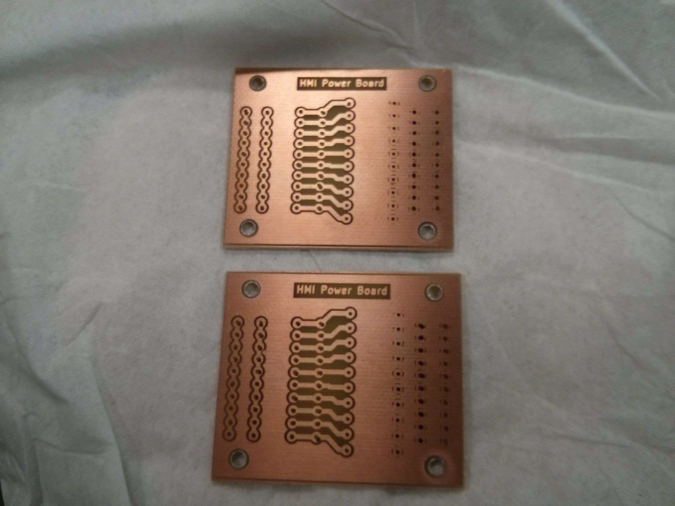
Ardu2/design/POC-3_MAX395/HMI/KicadProjects/PowerSupplyConnections Circuit/Images/IMG_20160601_153843.jpg
