gratefulfrog/ArduGuitar/Ardu2/design/POC-3_MAX395/HMI/KicadProjects/PowerSupplyConnections Circuit/Images/IMG_20160602_161205.jpg

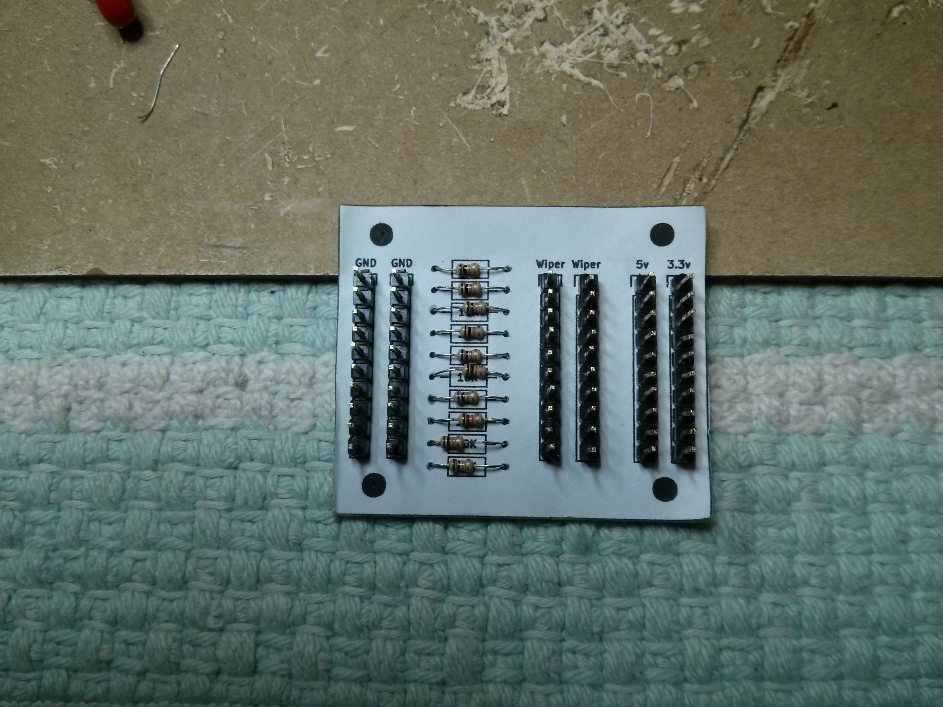
Ardu2/design/POC-3_MAX395/HMI/KicadProjects/PowerSupplyConnections Circuit/Images/IMG_20160602_161205.jpg
