gratefulfrog/ArduGuitar/Ardu2/design/POC-3_MAX395/HMI/MountingBlocks/LaserCutSpacerBlocks.jpg

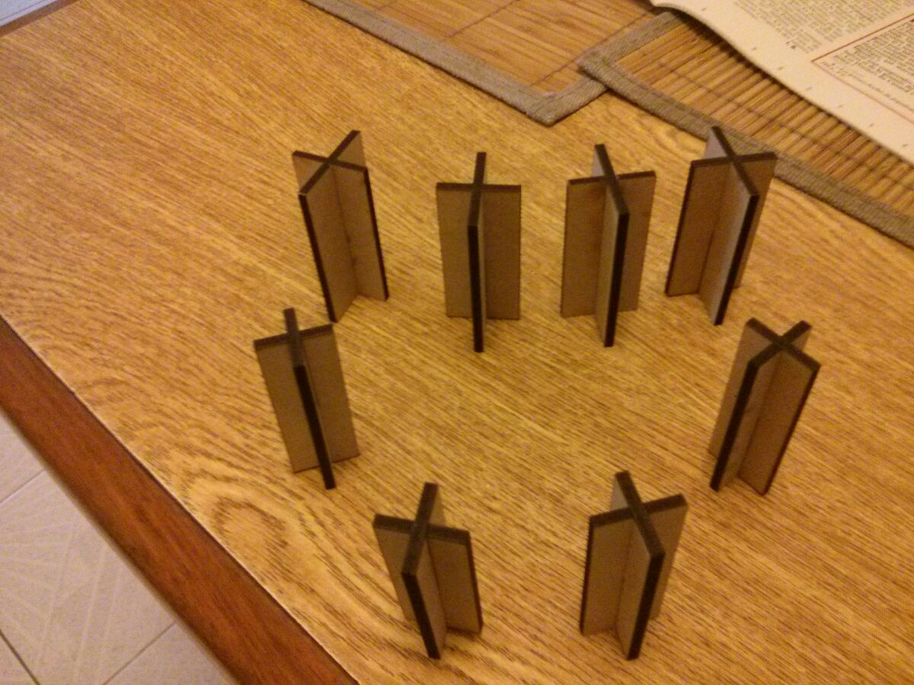
Ardu2/design/POC-3_MAX395/HMI/MountingBlocks/LaserCutSpacerBlocks.jpg
