gratefulfrog/ArduGuitar/Ardu2/design/POC-3_MAX395/HMI/MountingBlocks/LaserCutTempBlocks.png

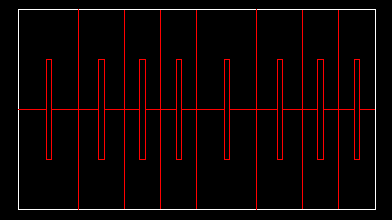
Ardu2/design/POC-3_MAX395/HMI/MountingBlocks/LaserCutTempBlocks.png
