gratefulfrog/ArduGuitar/Ardu2/design/POC-3_MAX395/HMI/MountingBlocks/triJig.png

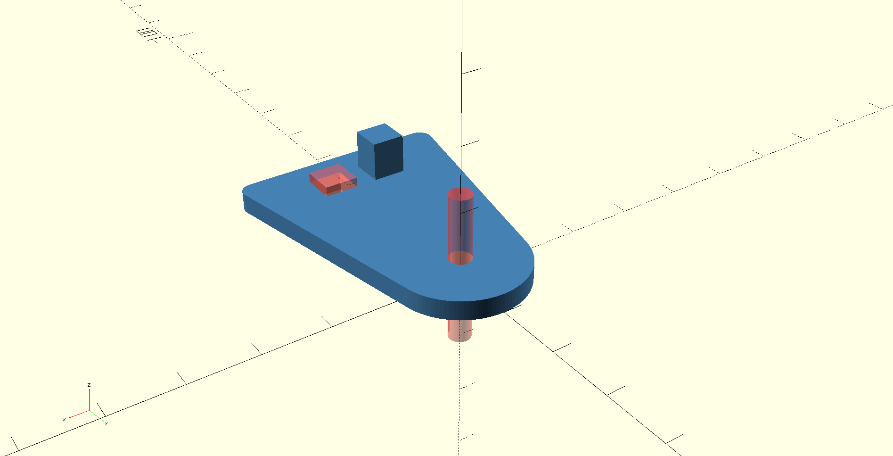
Ardu2/design/POC-3_MAX395/HMI/MountingBlocks/triJig.png
