gratefulfrog/ArduGuitar/Ardu2/design/POC-3_MAX395/HMI/PCB Standoffs/Low_Standoff.png

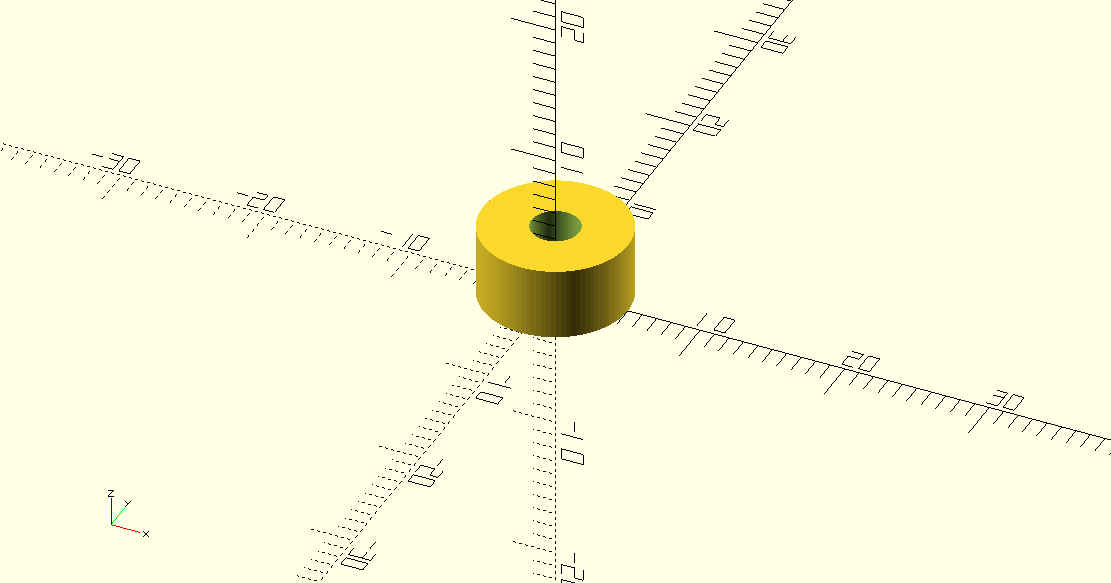
Ardu2/design/POC-3_MAX395/HMI/PCB Standoffs/Low_Standoff.png
