gratefulfrog/ArduGuitar/Ardu2/design/POC-3_MAX395/Images/HMI Integration/IMG_20160611_155002.jpg

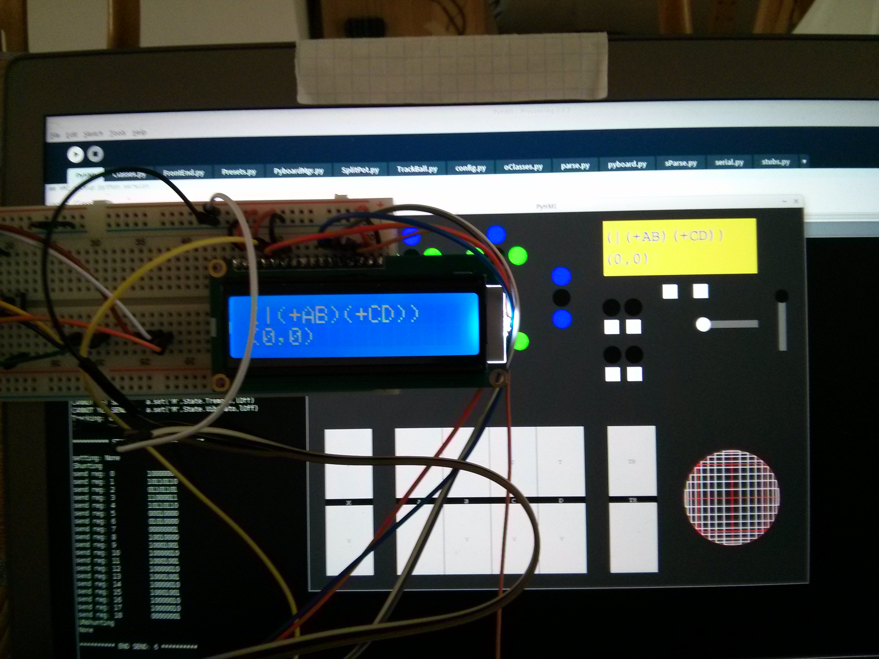
Ardu2/design/POC-3_MAX395/Images/HMI Integration/IMG_20160611_155002.jpg
