gratefulfrog/ArduGuitar/Ardu2/design/POC-3_MAX395/Images/IMG_20150605_182147.jpg

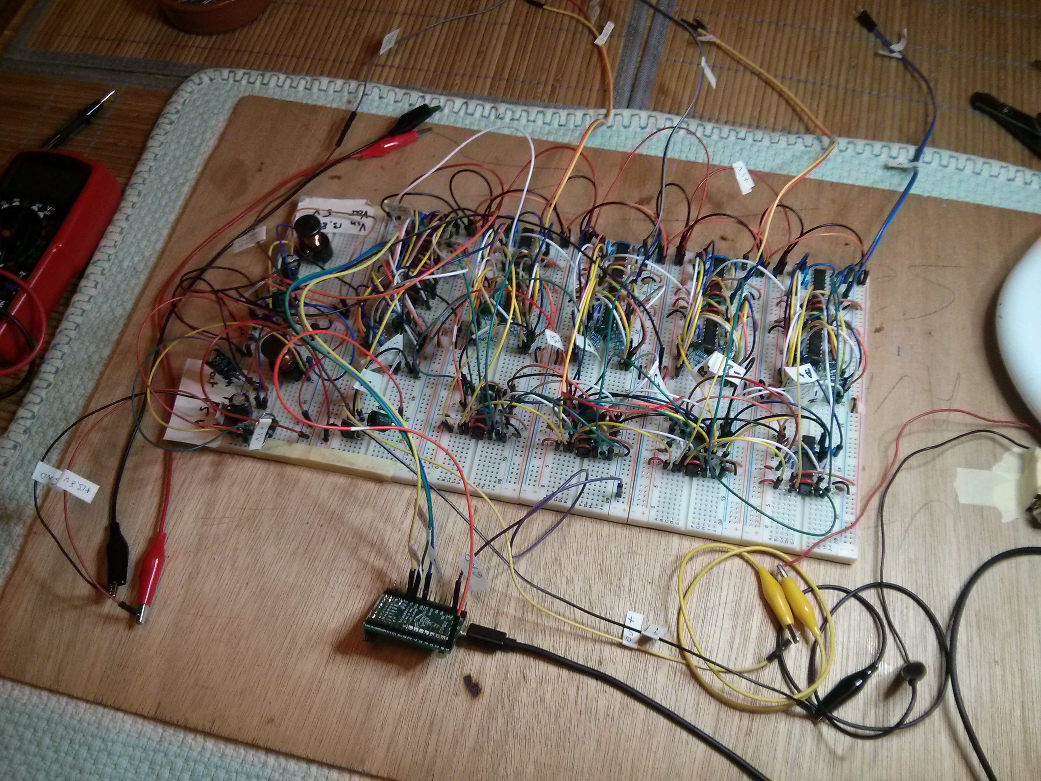
Ardu2/design/POC-3_MAX395/Images/IMG_20150605_182147.jpg
