gratefulfrog/ArduGuitar/Ardu2/design/POC-3_MAX395/Images/IMG_20150611_190052.jpg

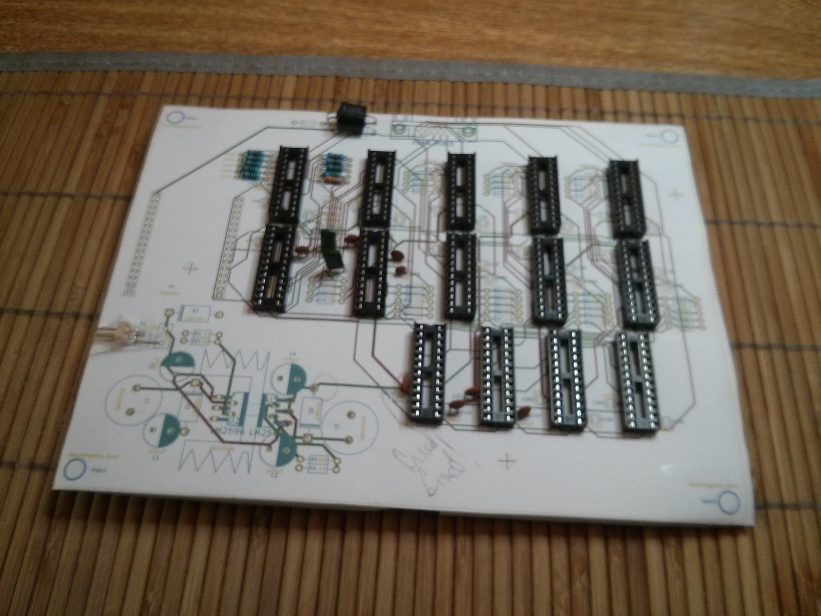
Ardu2/design/POC-3_MAX395/Images/IMG_20150611_190052.jpg
