gratefulfrog/ArduGuitar/Ardu2/design/POC-3_MAX395/Images/IMG_20150617_171433.jpg

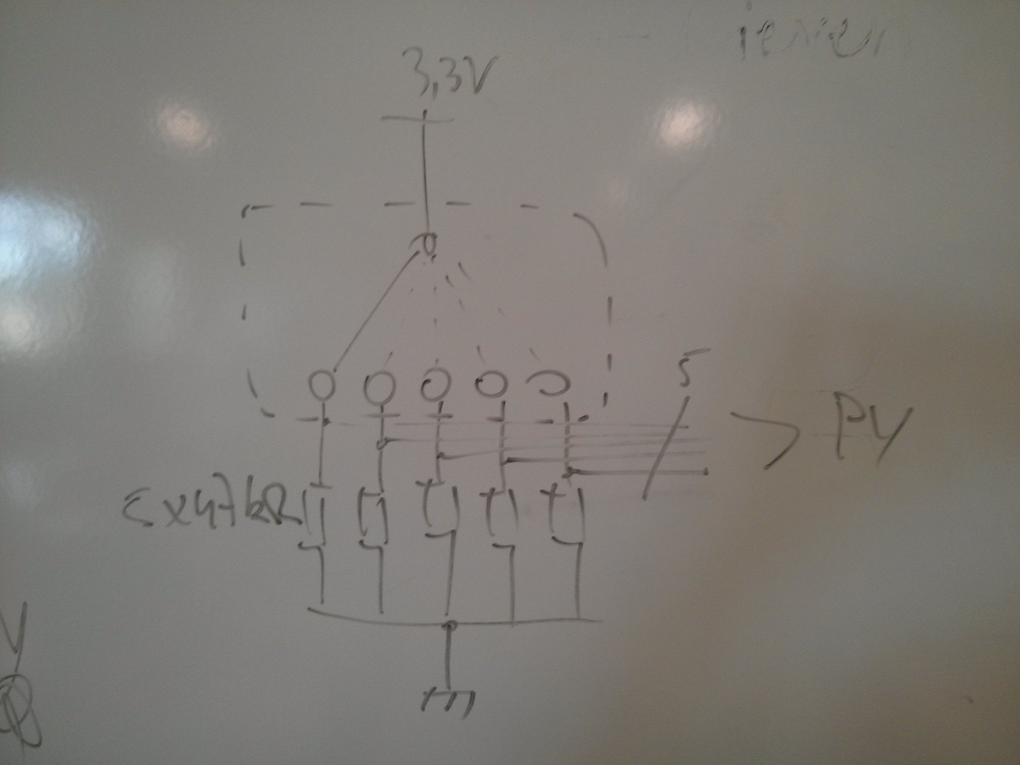
Ardu2/design/POC-3_MAX395/Images/IMG_20150617_171433.jpg
