gratefulfrog/ArduGuitar/Ardu2/design/POC-3_MAX395/Images/IMG_20150619_144740.jpg

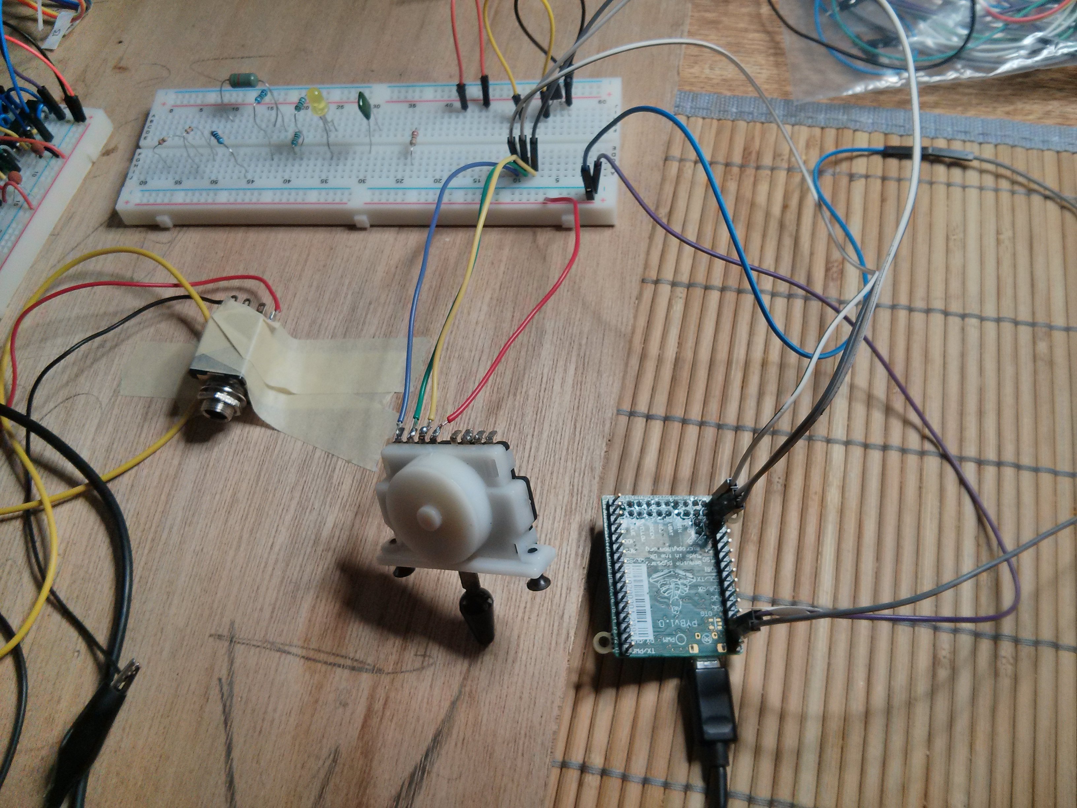
Ardu2/design/POC-3_MAX395/Images/IMG_20150619_144740.jpg
