gratefulfrog/ArduGuitar/Ardu2/design/POC-3_MAX395/Images/IMG_20150921_115923.jpg

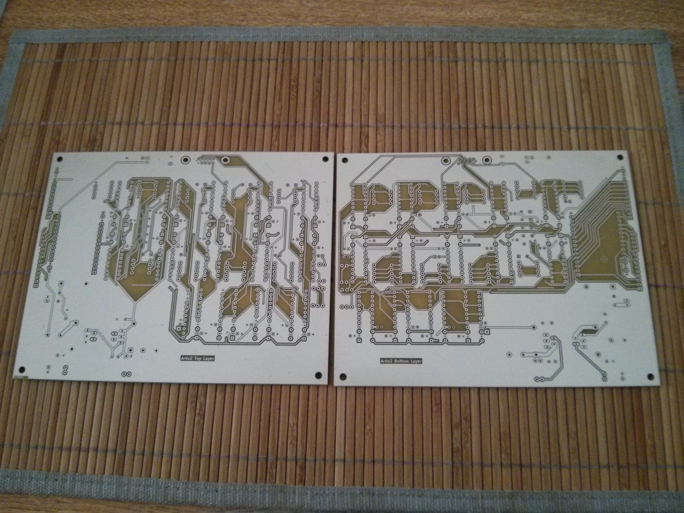
Ardu2/design/POC-3_MAX395/Images/IMG_20150921_115923.jpg
