gratefulfrog/ArduGuitar/Ardu2/design/POC-3_MAX395/Images/IMG_20151030_173928.jpg

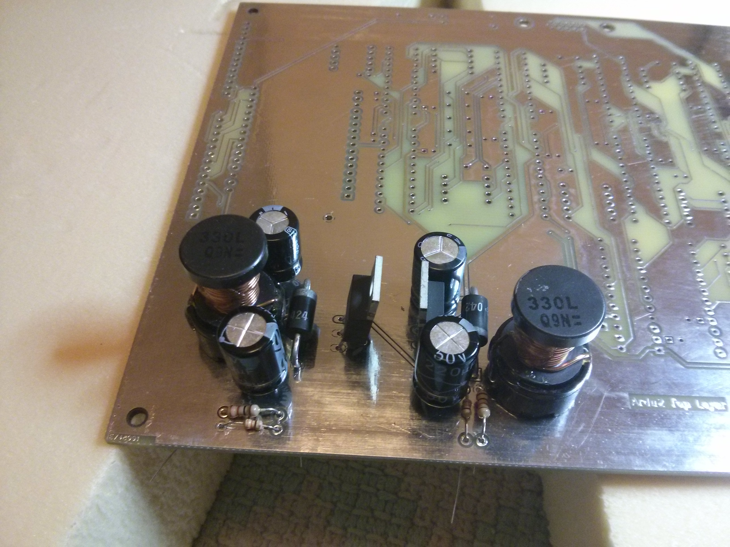
Ardu2/design/POC-3_MAX395/Images/IMG_20151030_173928.jpg
