gratefulfrog/ArduGuitar/Ardu2/design/POC-3_MAX395/Images/IMG_20151031_122256.jpg

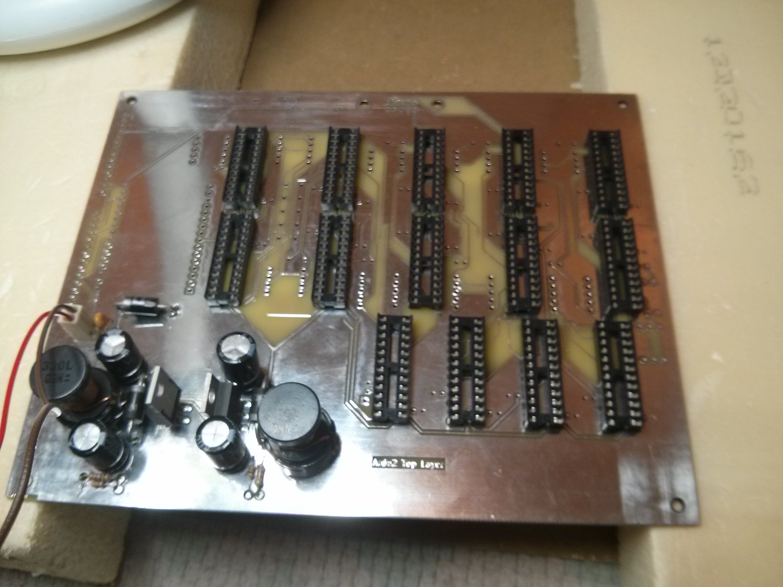
Ardu2/design/POC-3_MAX395/Images/IMG_20151031_122256.jpg
