gratefulfrog/ArduGuitar/Ardu2/design/POC-3_MAX395/Images/IMG_20151101_115259.jpg

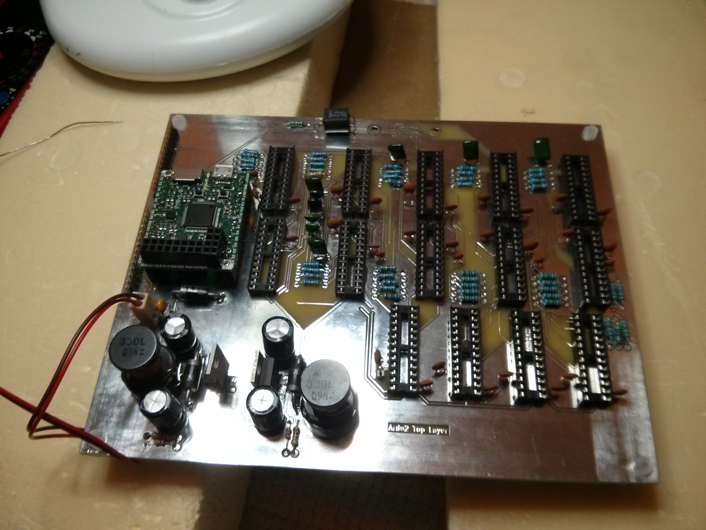
Ardu2/design/POC-3_MAX395/Images/IMG_20151101_115259.jpg
