gratefulfrog/ArduGuitar/Ardu2/design/POC-3_MAX395/Images/IMG_20151101_125033.jpg

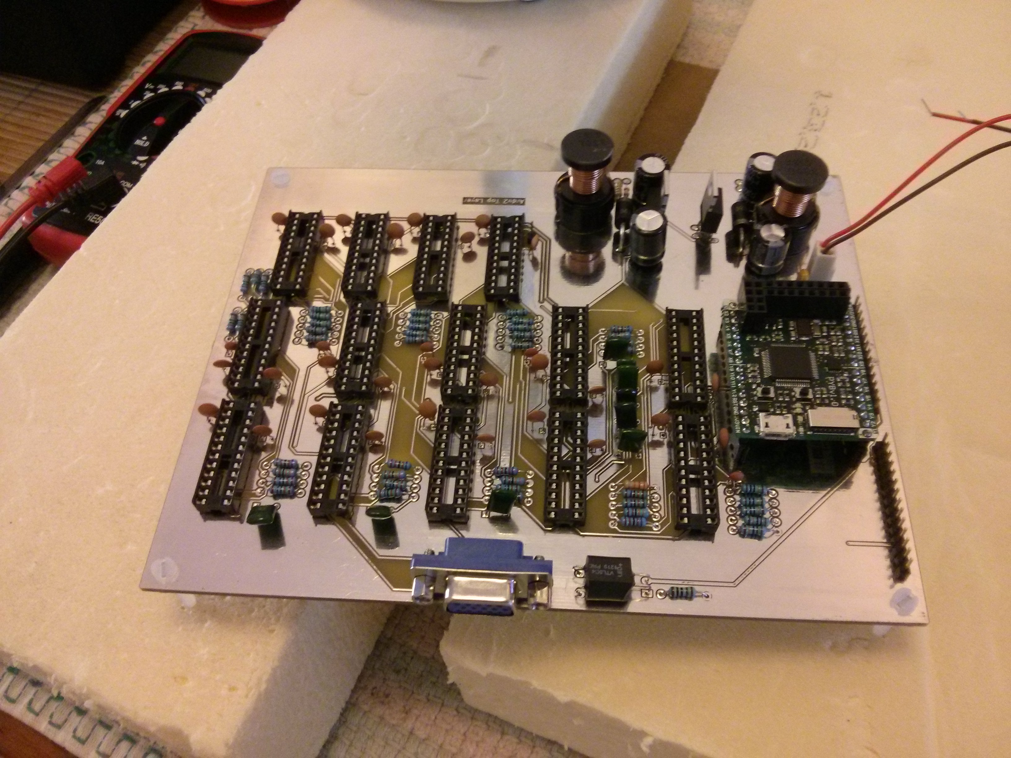
Ardu2/design/POC-3_MAX395/Images/IMG_20151101_125033.jpg
