gratefulfrog/ArduGuitar/Ardu2/design/POC-3_MAX395/Images/IMG_20151102_133929.jpg

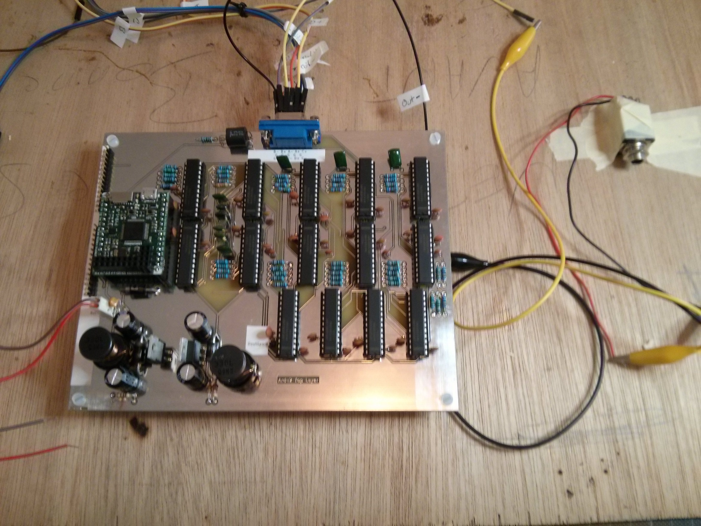
Ardu2/design/POC-3_MAX395/Images/IMG_20151102_133929.jpg
