gratefulfrog/ArduGuitar/Ardu2/design/POC-3_MAX395/Images/IMG_20151104_093342.jpg

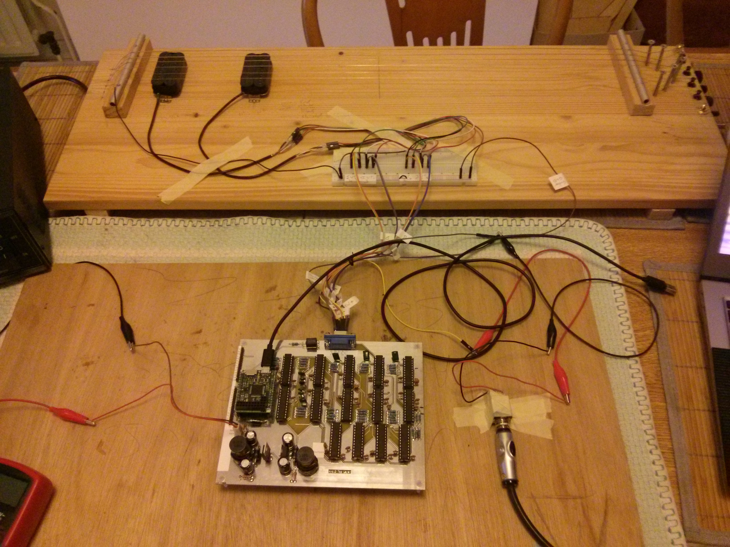
Ardu2/design/POC-3_MAX395/Images/IMG_20151104_093342.jpg
