gratefulfrog/ArduGuitar/Ardu2/design/POC-3_MAX395/Images/IMG_20151105_194800.jpg

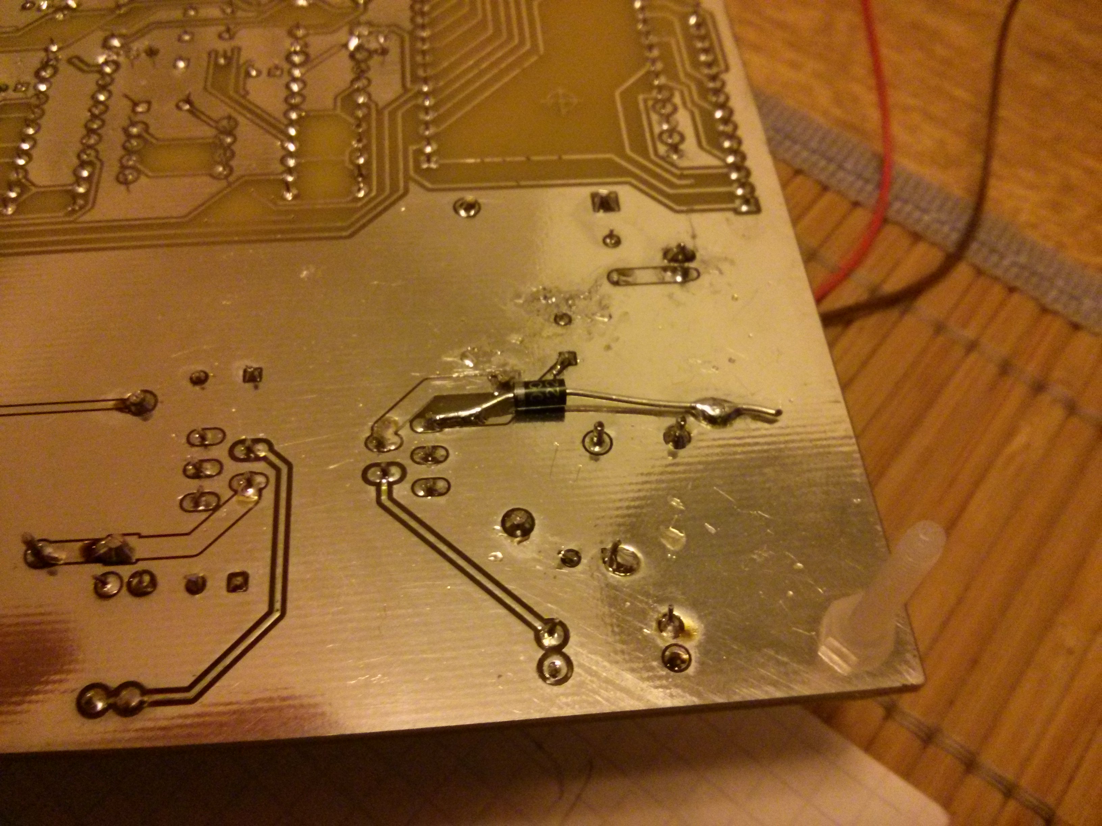
Ardu2/design/POC-3_MAX395/Images/IMG_20151105_194800.jpg
