gratefulfrog/ArduGuitar/Ardu2/design/POC-3_MAX395/Images/IMG_20161108_184722.jpg

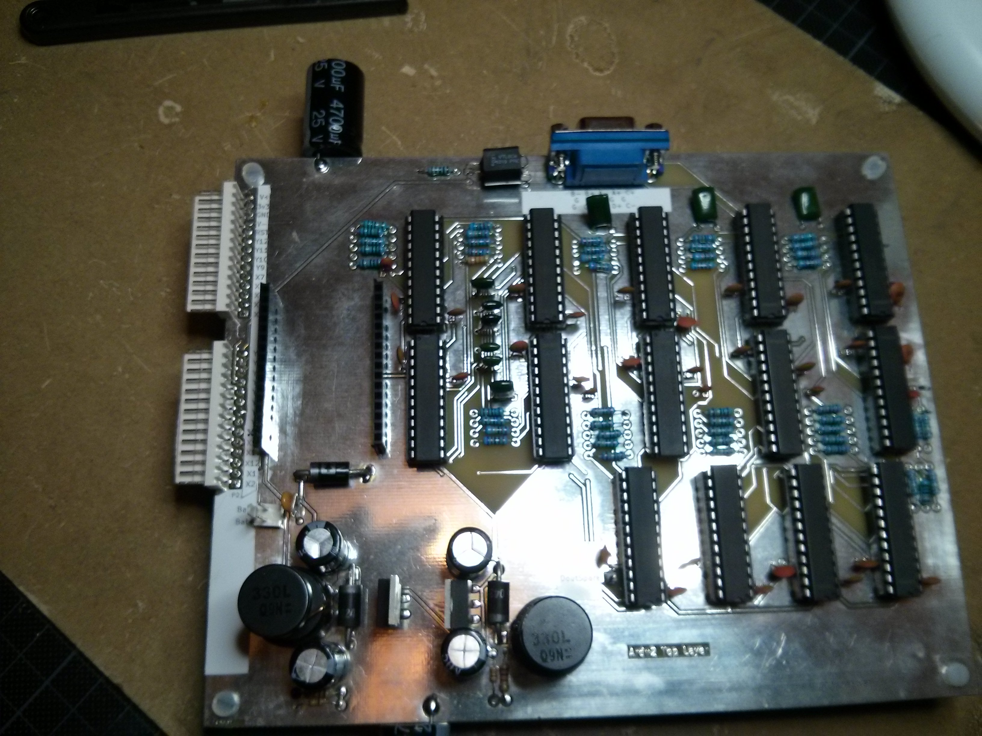
Ardu2/design/POC-3_MAX395/Images/IMG_20161108_184722.jpg
