gratefulfrog/ArduGuitar/Ardu2/design/POC-3_MAX395/Images/IMG_20161108_185035.jpg

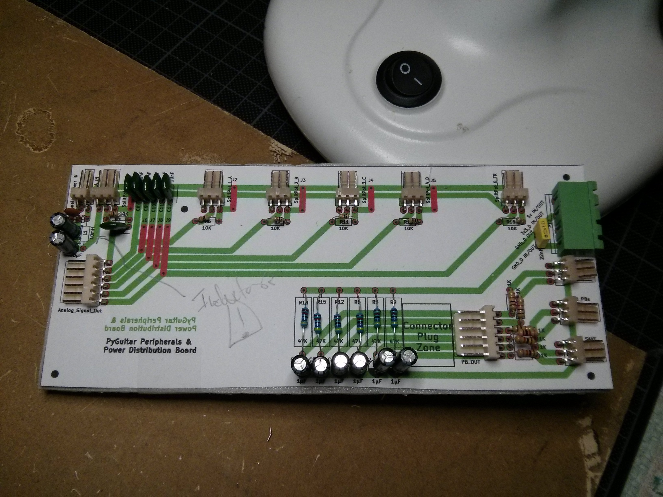
Ardu2/design/POC-3_MAX395/Images/IMG_20161108_185035.jpg
