gratefulfrog/ArduGuitar/Ardu2/design/POC-3_MAX395/Images/IMG_20161112_153519.jpg

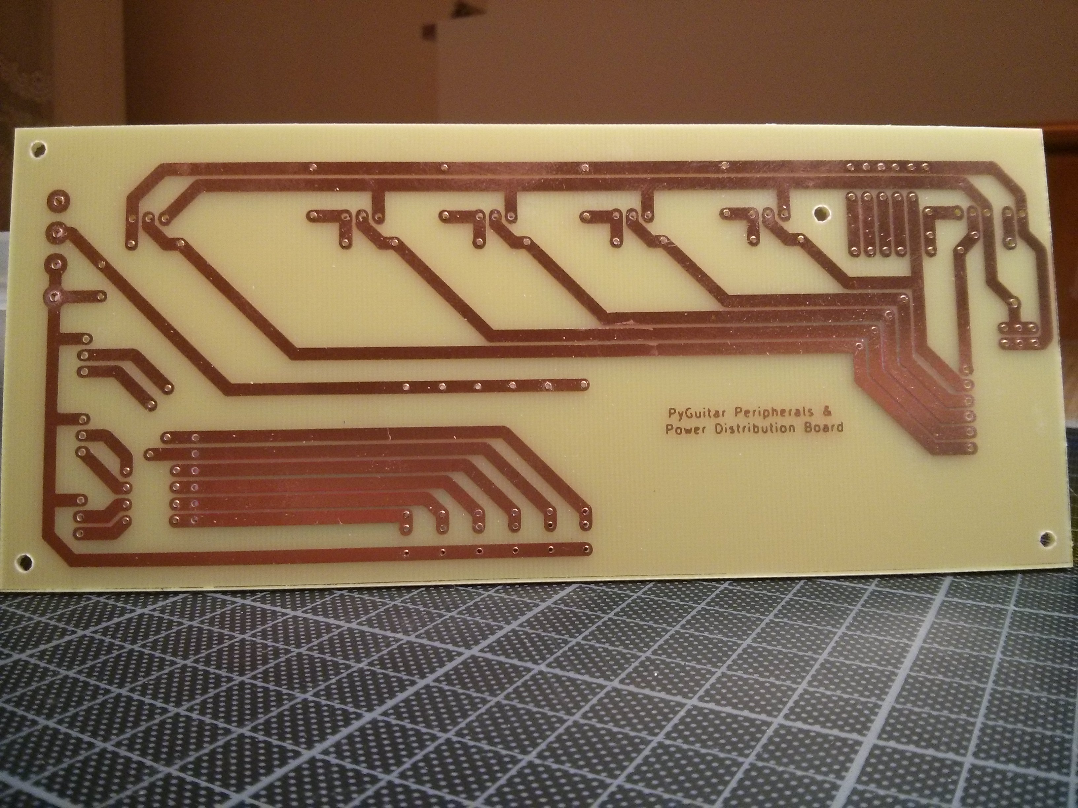
Ardu2/design/POC-3_MAX395/Images/IMG_20161112_153519.jpg
