gratefulfrog/ArduGuitar/Ardu2/design/POC-3_MAX395/Images/IMG_20161112_213906.jpg

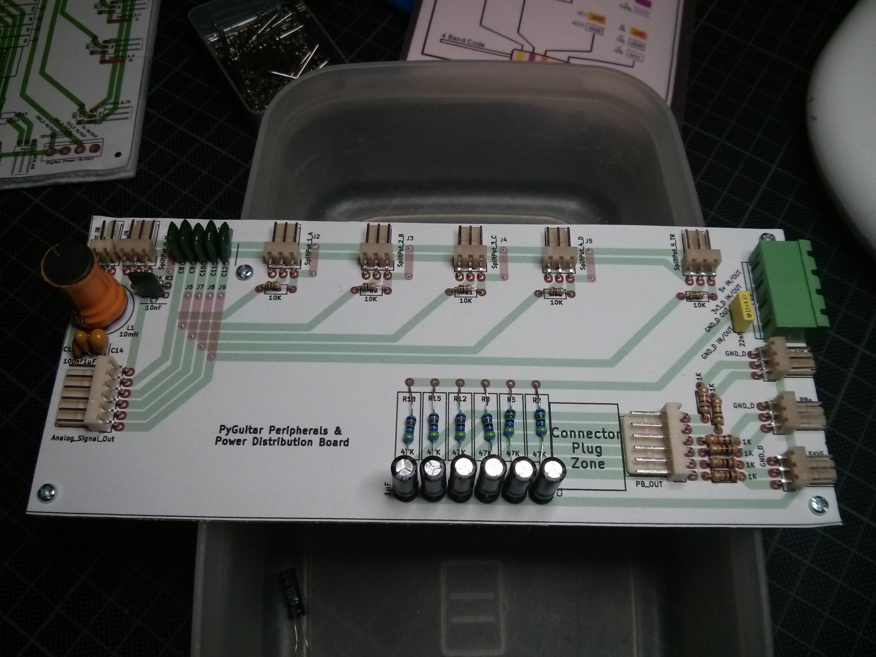
Ardu2/design/POC-3_MAX395/Images/IMG_20161112_213906.jpg
