gratefulfrog/ArduGuitar/Ardu2/design/POC-3_MAX395/Images/IMG_20161113_161443.jpg

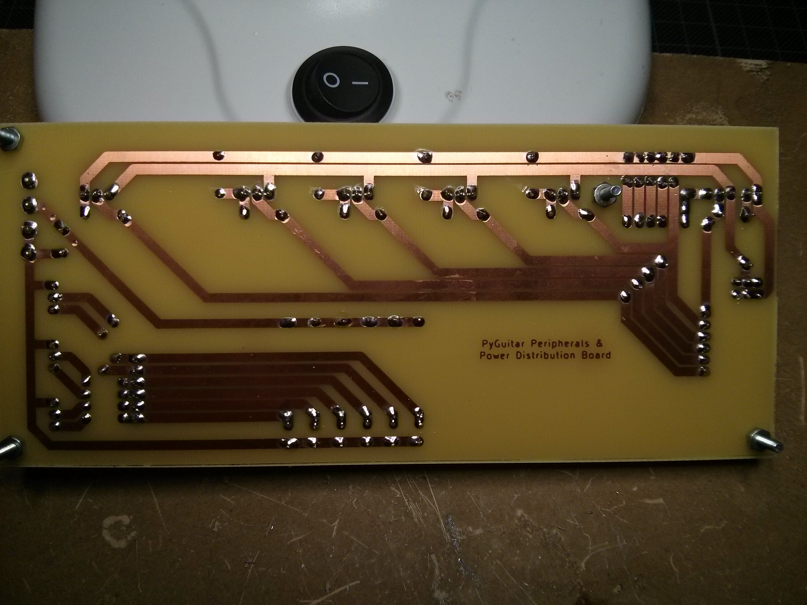
Ardu2/design/POC-3_MAX395/Images/IMG_20161113_161443.jpg
