gratefulfrog/ArduGuitar/Ardu2/design/POC-3_MAX395/Images/IMG_20161114_180803.jpg

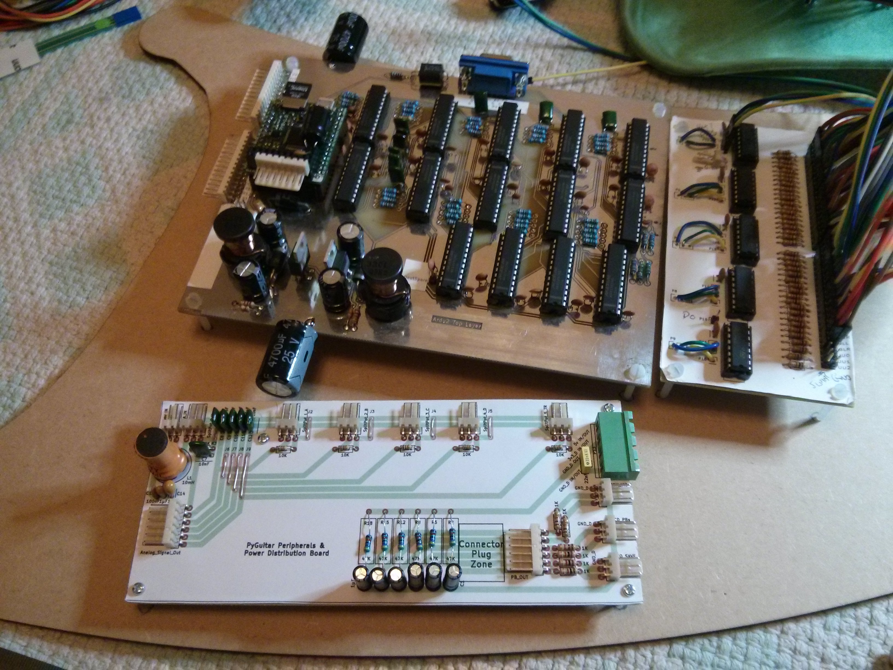
Ardu2/design/POC-3_MAX395/Images/IMG_20161114_180803.jpg
