gratefulfrog/ArduGuitar/Ardu2/design/POC-3_MAX395/Images/IMG_20161114_180810.jpg

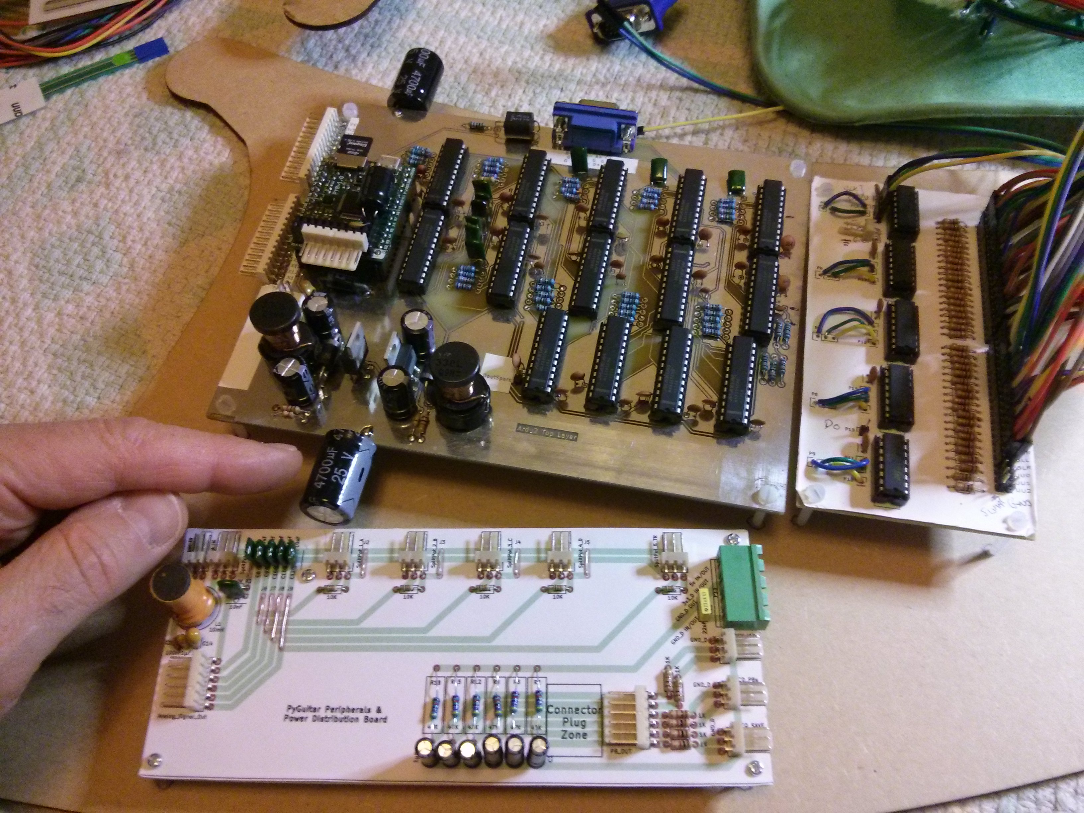
Ardu2/design/POC-3_MAX395/Images/IMG_20161114_180810.jpg
