gratefulfrog/ArduGuitar/Ardu2/design/POC-3_MAX395/Images/IMG_20161115_164658.jpg

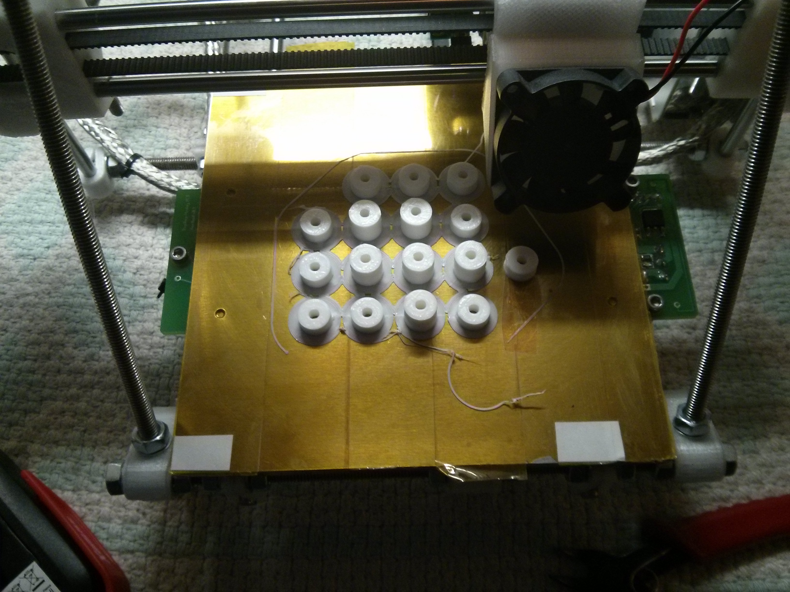
Ardu2/design/POC-3_MAX395/Images/IMG_20161115_164658.jpg
