gratefulfrog/ArduGuitar/Ardu2/design/POC-3_MAX395/Images/IMG_20161202_190014.jpg

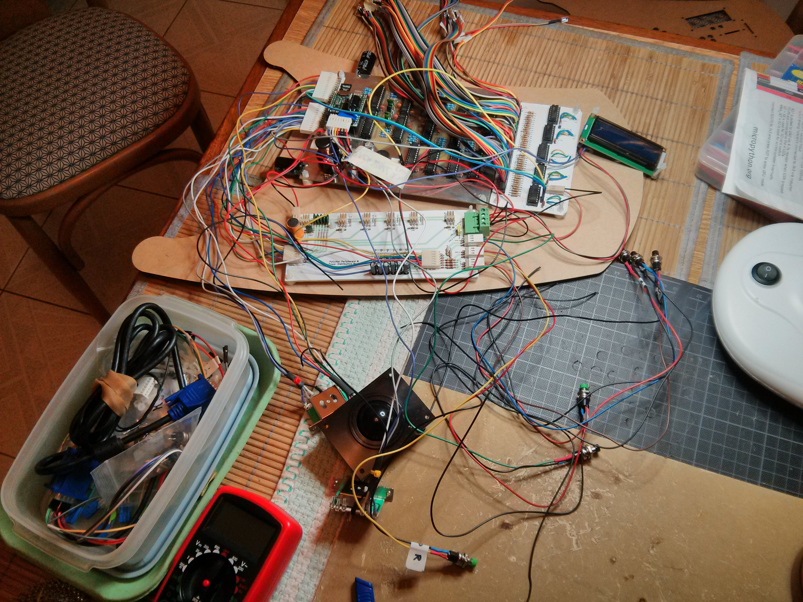
Ardu2/design/POC-3_MAX395/Images/IMG_20161202_190014.jpg
