gratefulfrog/ArduGuitar/Ardu2/design/POC-3_MAX395/Images/IMG_20161227_161129.jpg

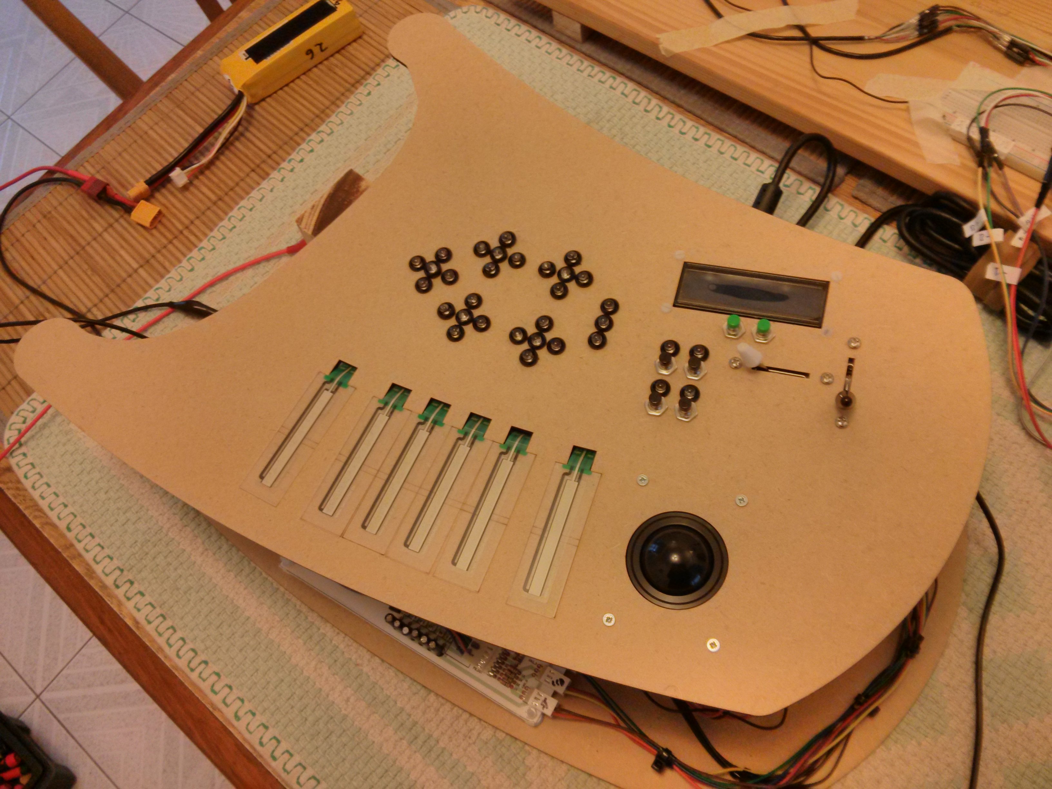
Ardu2/design/POC-3_MAX395/Images/IMG_20161227_161129.jpg
