gratefulfrog/ArduGuitar/Ardu2/design/POC-3_MAX395/Images/IMG_20171229_121007.jpg

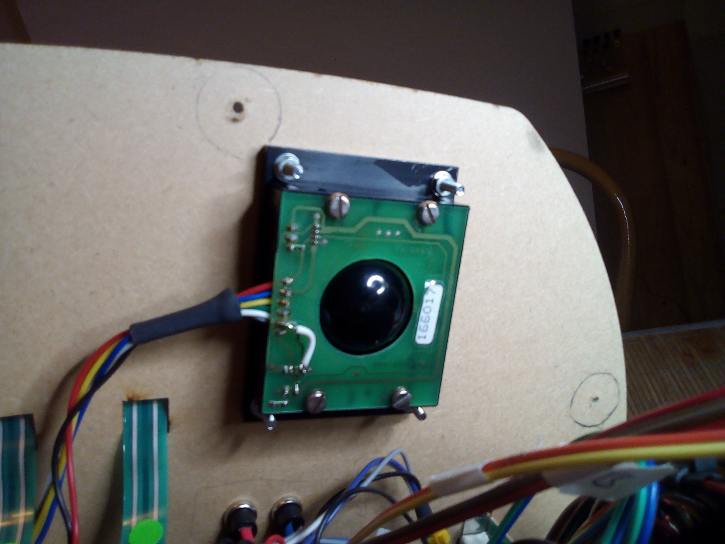
Ardu2/design/POC-3_MAX395/Images/IMG_20171229_121007.jpg
