gratefulfrog/ArduGuitar/Ardu2/design/POC-3_MAX395/Images/Switch-Debouncing-cap.png

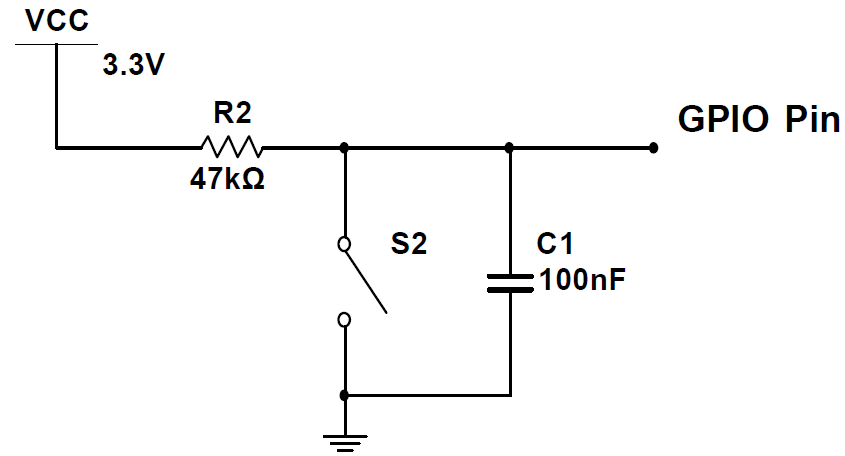
Ardu2/design/POC-3_MAX395/Images/Switch-Debouncing-cap.png
