gratefulfrog/ArduGuitar/Ardu2/design/POC-3_MAX395/Images/VGA Connector/IMG_20151102_095550.jpg

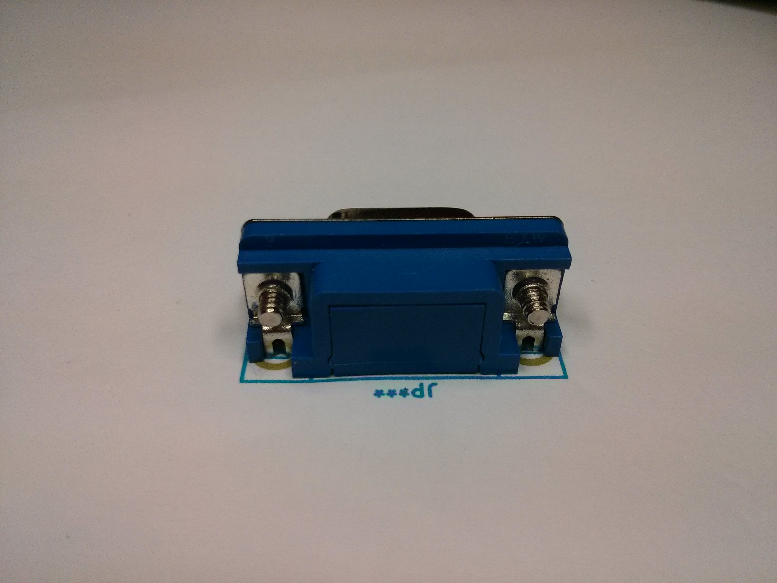
Ardu2/design/POC-3_MAX395/Images/VGA Connector/IMG_20151102_095550.jpg
