gratefulfrog/ArduGuitar/Ardu2/design/POC-3_MAX395/Images/VGA Connector/VGA_Connector_Pinout.png

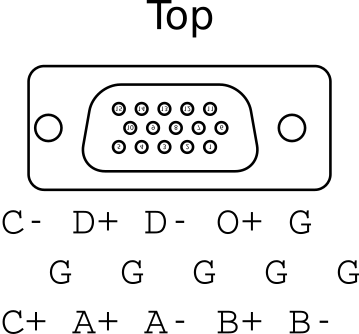
Ardu2/design/POC-3_MAX395/Images/VGA Connector/VGA_Connector_Pinout.png
