gratefulfrog/ArduGuitar/Ardu2/design/POC-3_MAX395/KicadProjects/FullCircuit/Gerber/V1.7/fullCircuit-brd.png

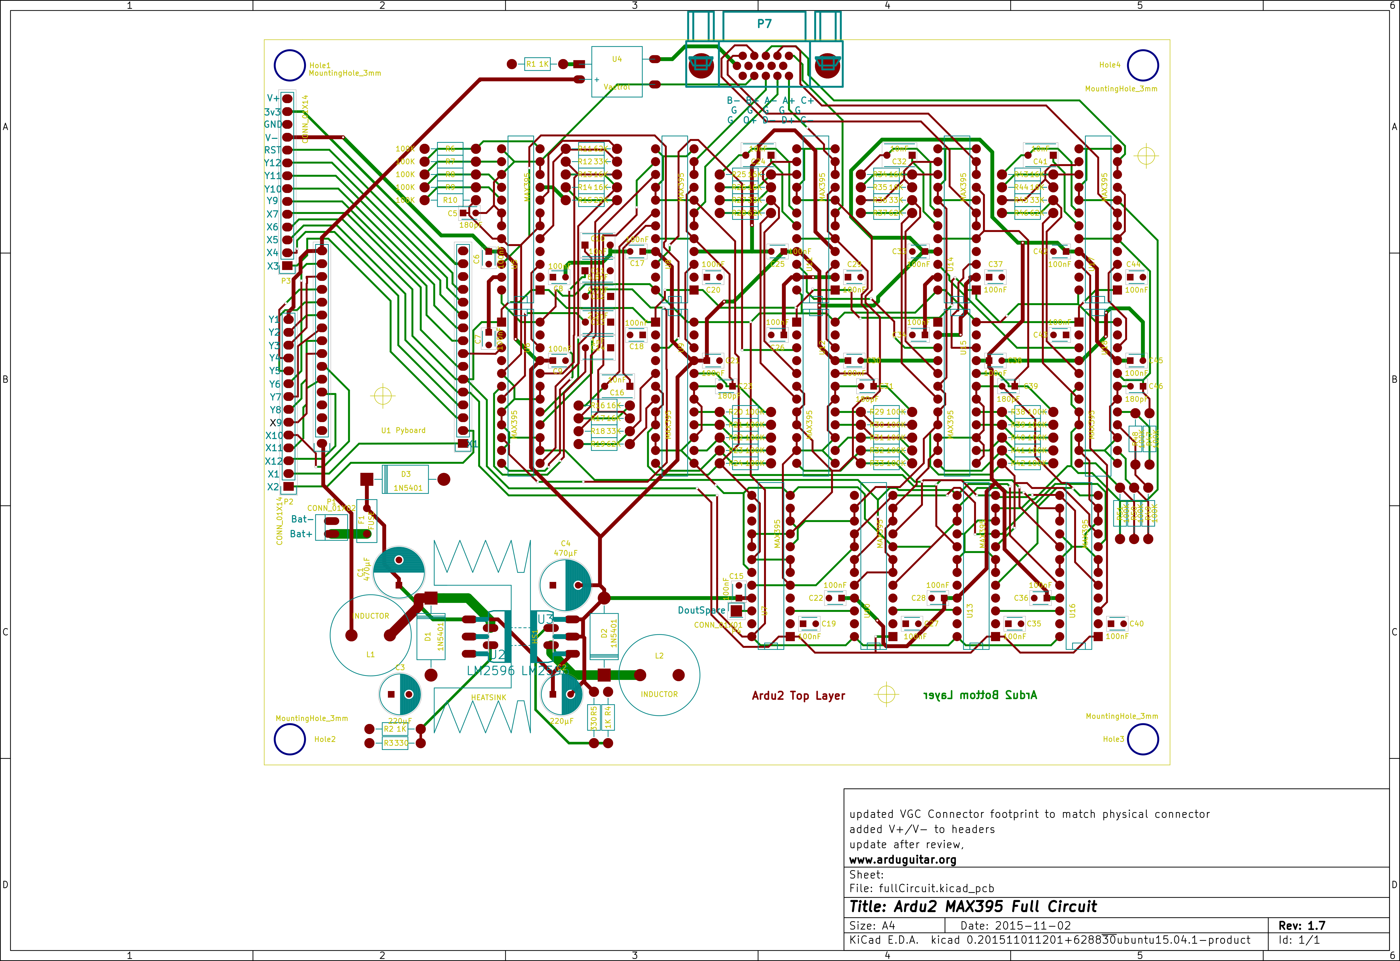
Ardu2/design/POC-3_MAX395/KicadProjects/FullCircuit/Gerber/V1.7/fullCircuit-brd.png
