gratefulfrog/ArduGuitar/Ardu2/design/POC-3_MAX395/KicadProjects/FullCircuit/Images/V1.8/FullSchematic.png

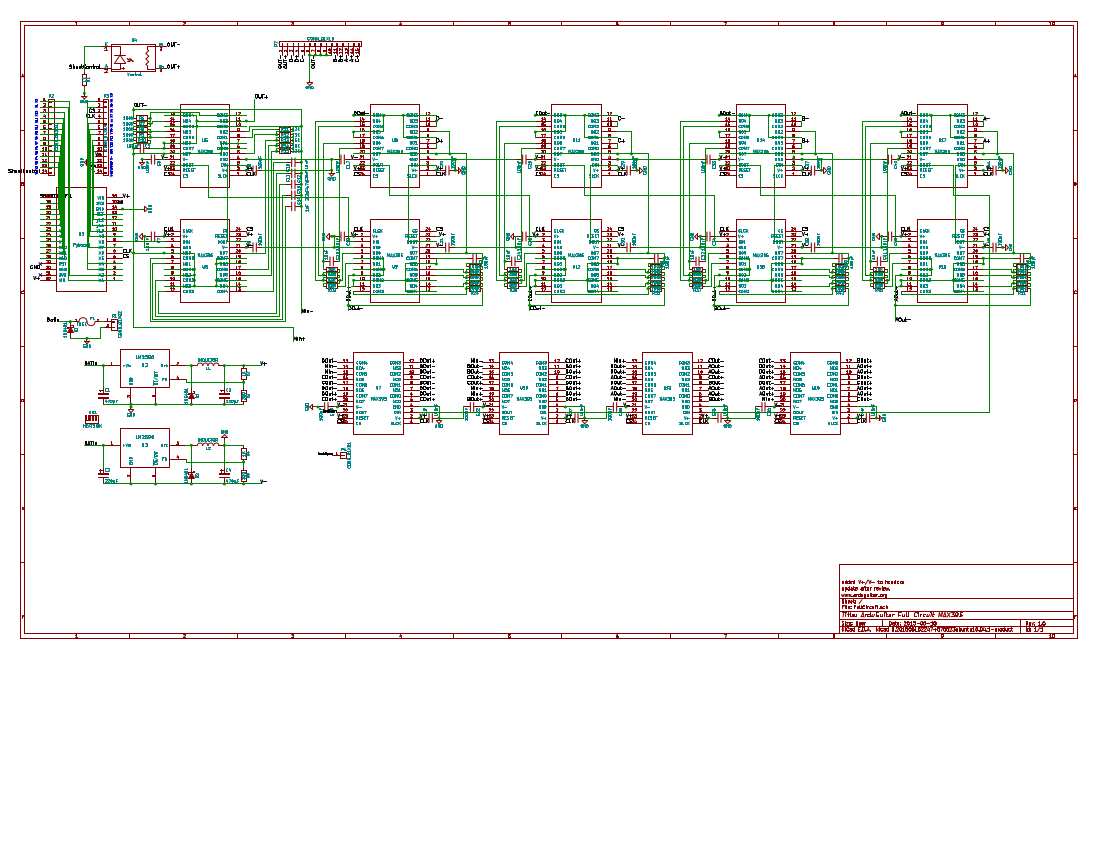
Ardu2/design/POC-3_MAX395/KicadProjects/FullCircuit/Images/V1.8/FullSchematic.png
