gratefulfrog/ArduGuitar/Ardu2/design/POC-3_MAX395/KicadProjects/FullCircuit/Images/V1.8/PCB_1_8_add_Schottkey.png

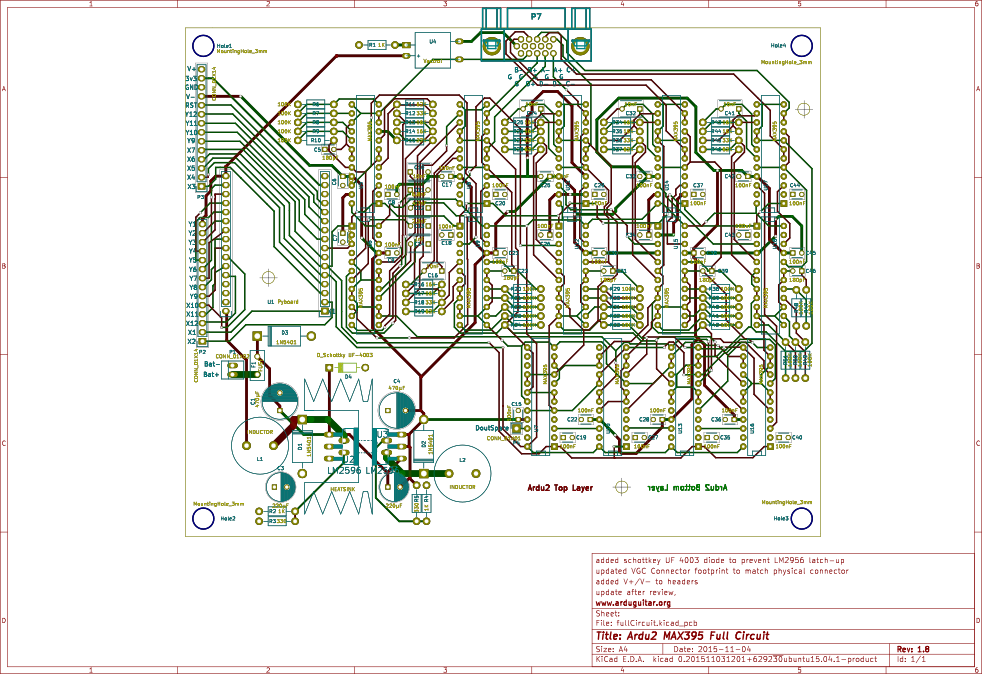
Ardu2/design/POC-3_MAX395/KicadProjects/FullCircuit/Images/V1.8/PCB_1_8_add_Schottkey.png
