gratefulfrog/ArduGuitar/Ardu2/design/POC-3_MAX395/KicadProjects/HMI_PCB/HMI-PCB-brd.png

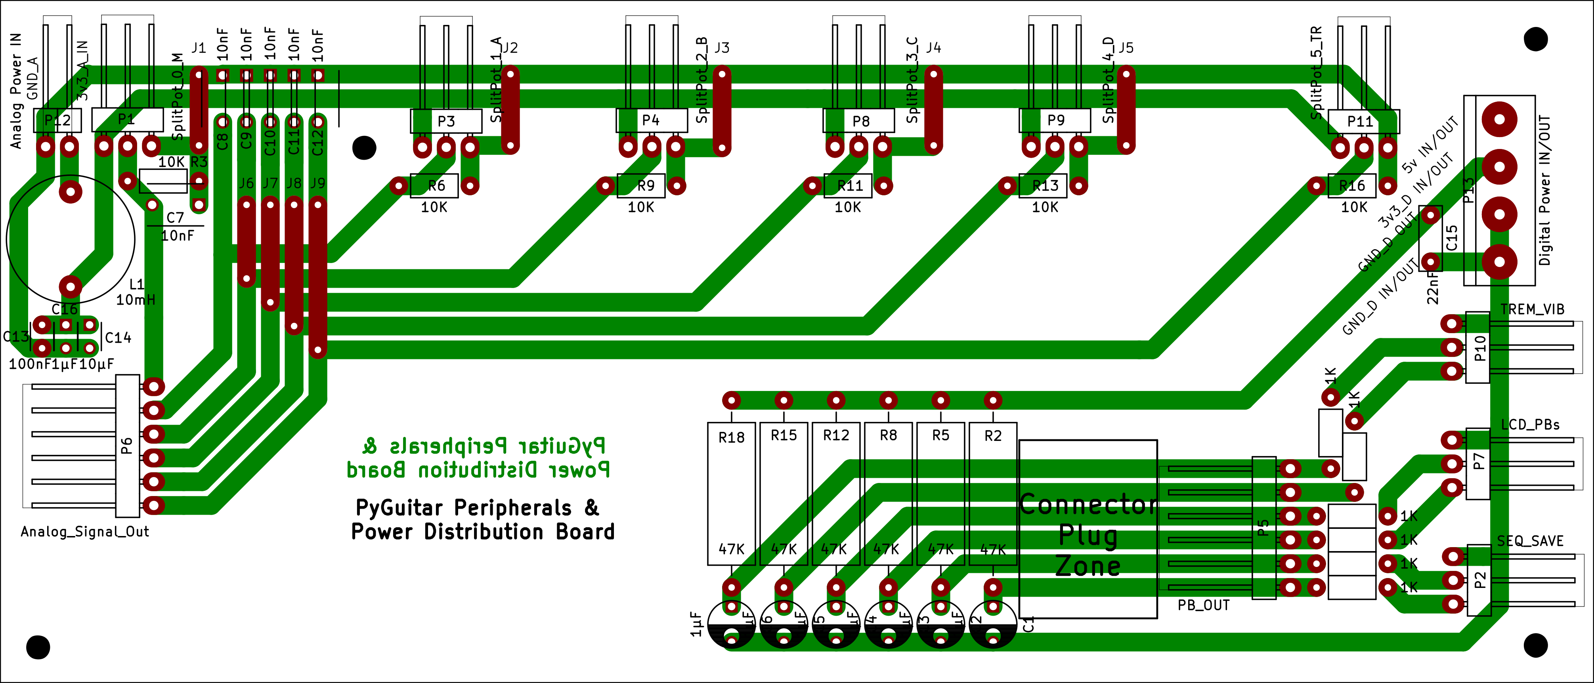
Ardu2/design/POC-3_MAX395/KicadProjects/HMI_PCB/HMI-PCB-brd.png
