gratefulfrog/ArduGuitar/Ardu2/design/POC-3_MAX395/KicadProjects/HMI_PCB/HMI-PCB.sch.png

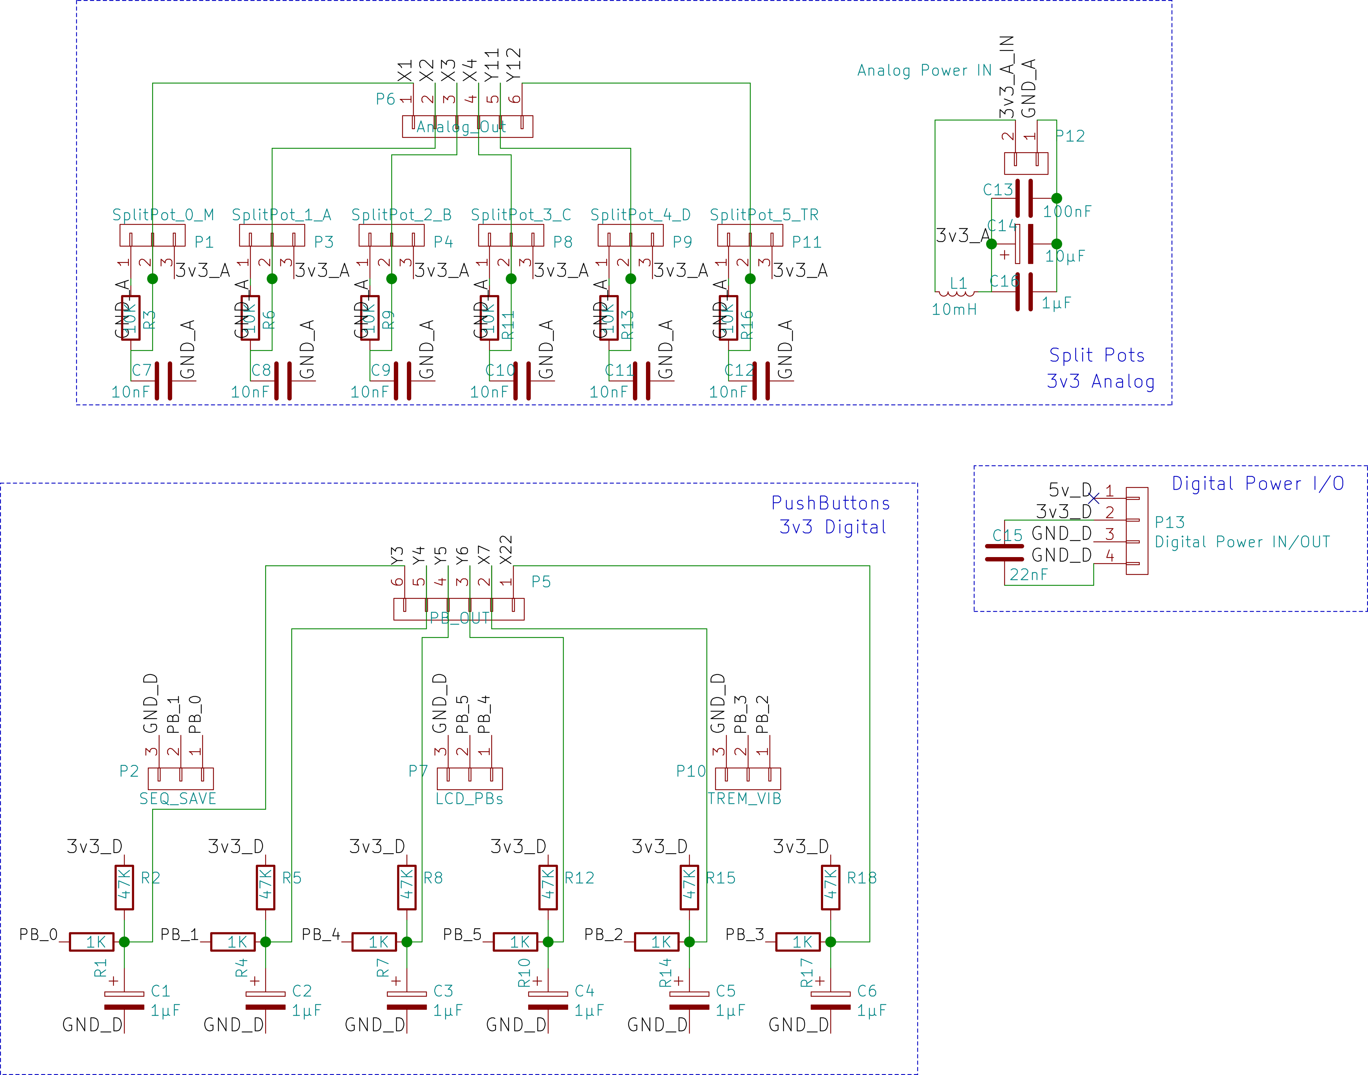
Ardu2/design/POC-3_MAX395/KicadProjects/HMI_PCB/HMI-PCB.sch.png
