gratefulfrog/ArduGuitar/Ardu2/design/POC-3_MAX395/pyboard/DraftDevt/PS2/PyPS2/interruptVersion/Images/PollInteraction.png

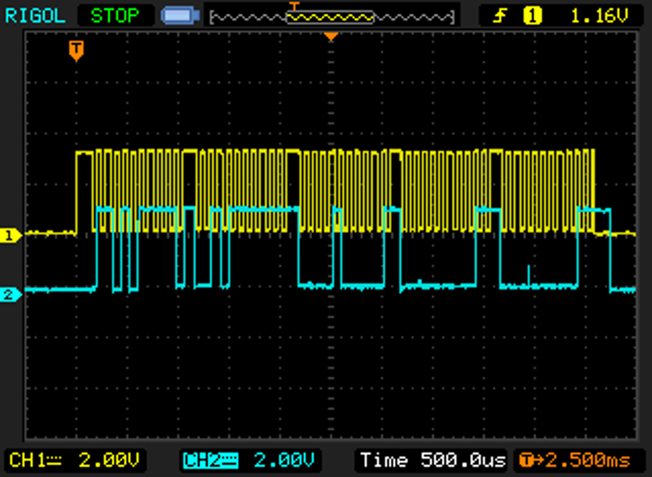
Ardu2/design/POC-3_MAX395/pyboard/DraftDevt/PS2/PyPS2/interruptVersion/Images/PollInteraction.png
