gratefulfrog/ArduGuitar/Ardu2/design/POC-3_MAX395/pyboard/images/Full HMI Mockup.png

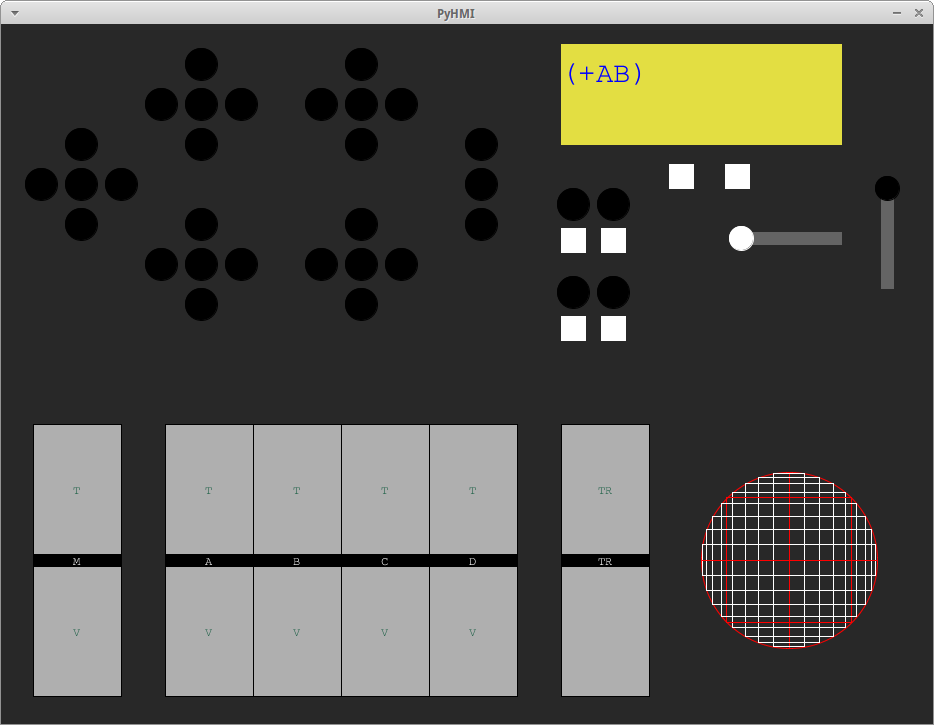
Ardu2/design/POC-3_MAX395/pyboard/images/Full HMI Mockup.png
