gratefulfrog/ArduGuitar/Ardu2/design/POC-3_MAX395/pyboard/images/IMG_20150228_122853.jpg

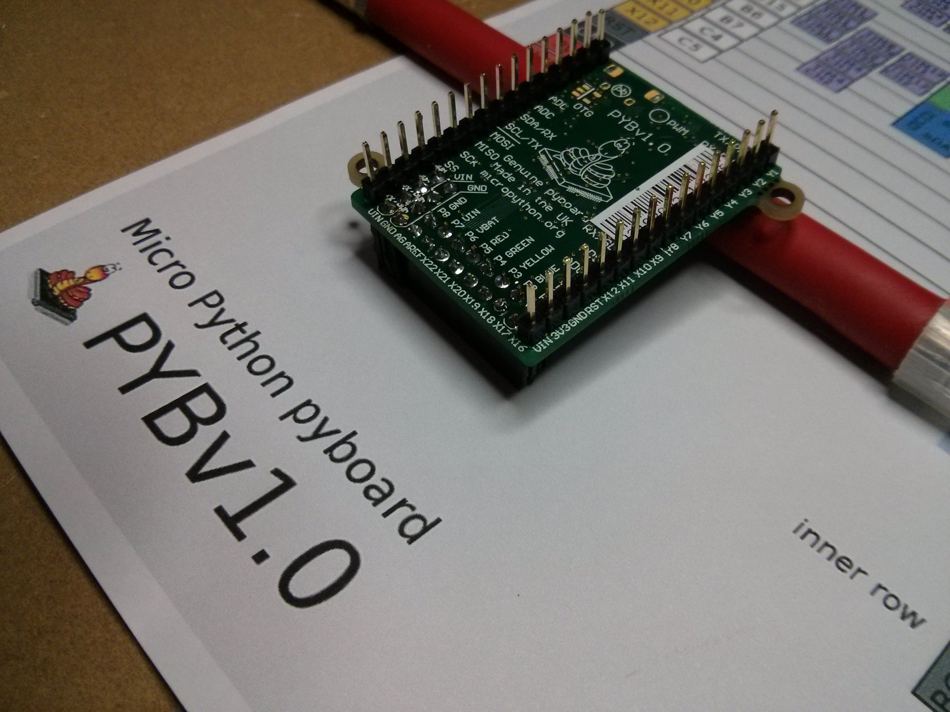
Ardu2/design/POC-3_MAX395/pyboard/images/IMG_20150228_122853.jpg
