gratefulfrog/ArduGuitar/Ardu2/design/POC-3_MAX395/pyboard/images/PyHMI/Screenshot_2016-05-06_18-09-31.png

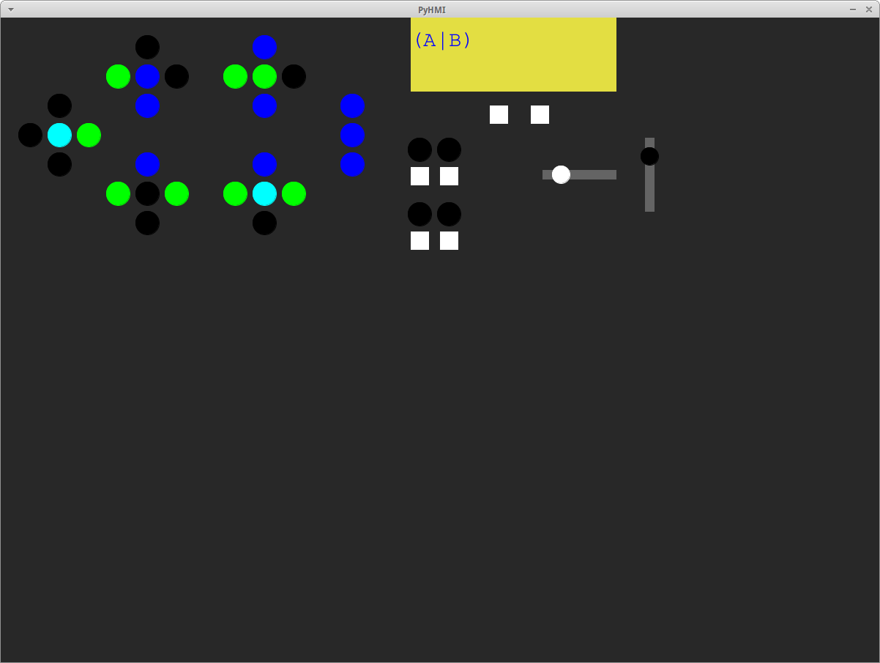
Ardu2/design/POC-3_MAX395/pyboard/images/PyHMI/Screenshot_2016-05-06_18-09-31.png
