gratefulfrog/ArduGuitar/Ardu2/design/POC-3_MAX395/pyboard/images/SplitPot 2016 05 29.jpg

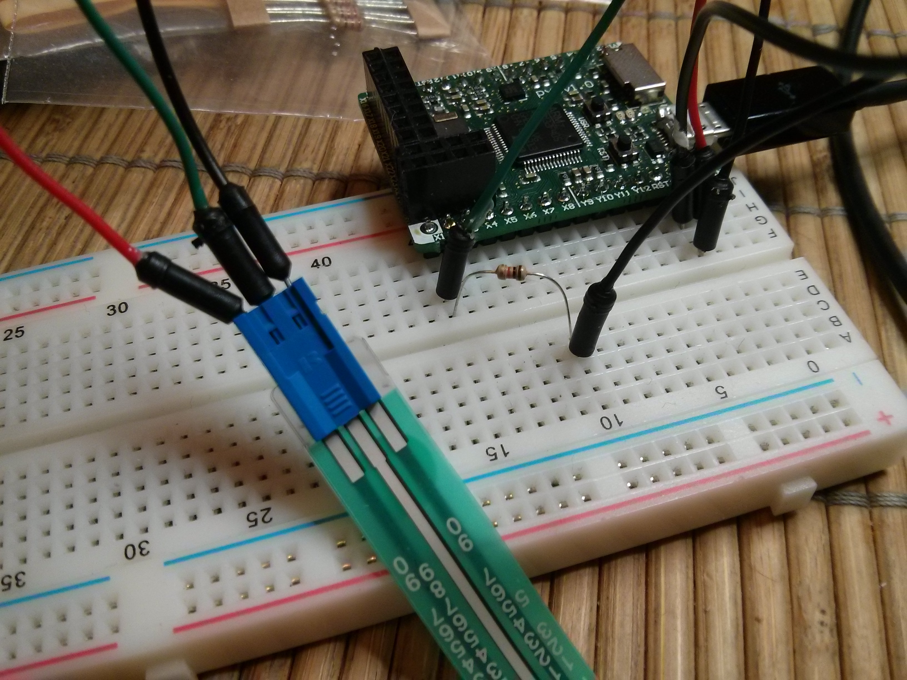
Ardu2/design/POC-3_MAX395/pyboard/images/SplitPot 2016 05 29.jpg
