gratefulfrog/ArduGuitar/Ardu2/design/POC-3_MAX395/pyboard/images/TrackBall Integration in HMI Mockup.png

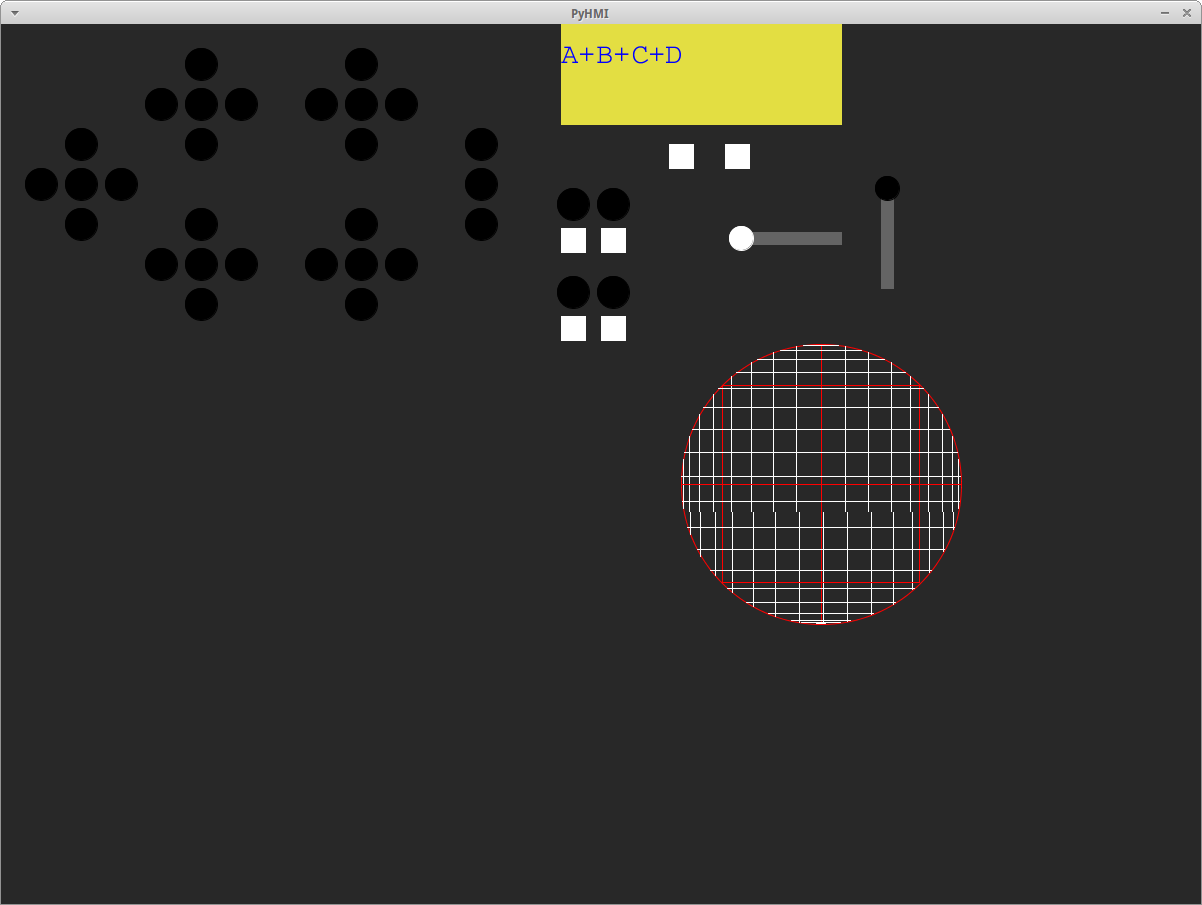
Ardu2/design/POC-3_MAX395/pyboard/images/TrackBall Integration in HMI Mockup.png
