gratefulfrog/ArduGuitar/Ardu2/design/POC-3_MAX395/pyboard/images/TrackballSimulation.png

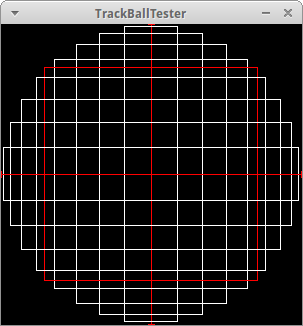
Ardu2/design/POC-3_MAX395/pyboard/images/TrackballSimulation.png
