gratefulfrog/ArduGuitar/Ardu2/design/POC-3_MAX395/pyboard/V1_WithHMI/PyHMI/Data/Asynch Q Mecahnics.png

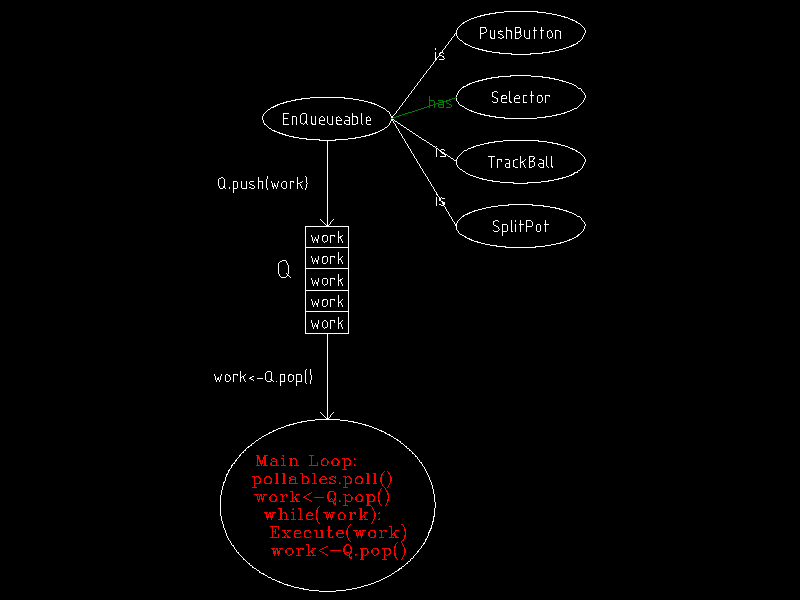
Ardu2/design/POC-3_MAX395/pyboard/V1_WithHMI/PyHMI/Data/Asynch Q Mecahnics.png
