gratefulfrog/ArduGuitar/Ardu3/DraftDevt/Pyboard/AD75019/Scope Images and Test Results/X0_Y0 True overview.png

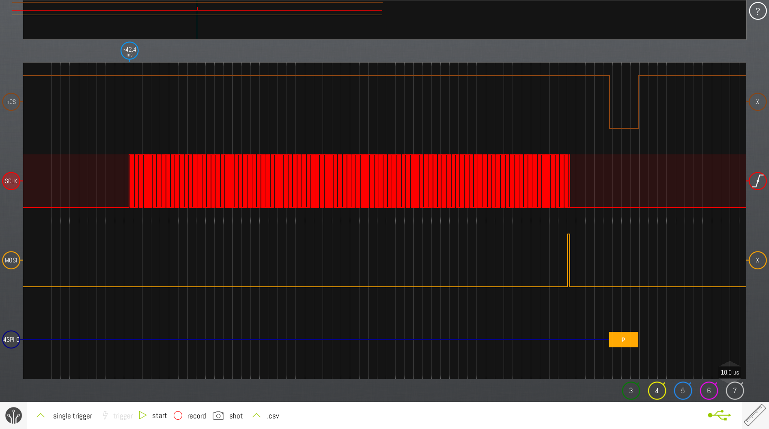
Ardu3/DraftDevt/Pyboard/AD75019/Scope Images and Test Results/X0_Y0 True overview.png
