gratefulfrog/ArduGuitar/arduino/Layouts/ArduStomp/ArduStomp02/ArduStomp02schematic.png

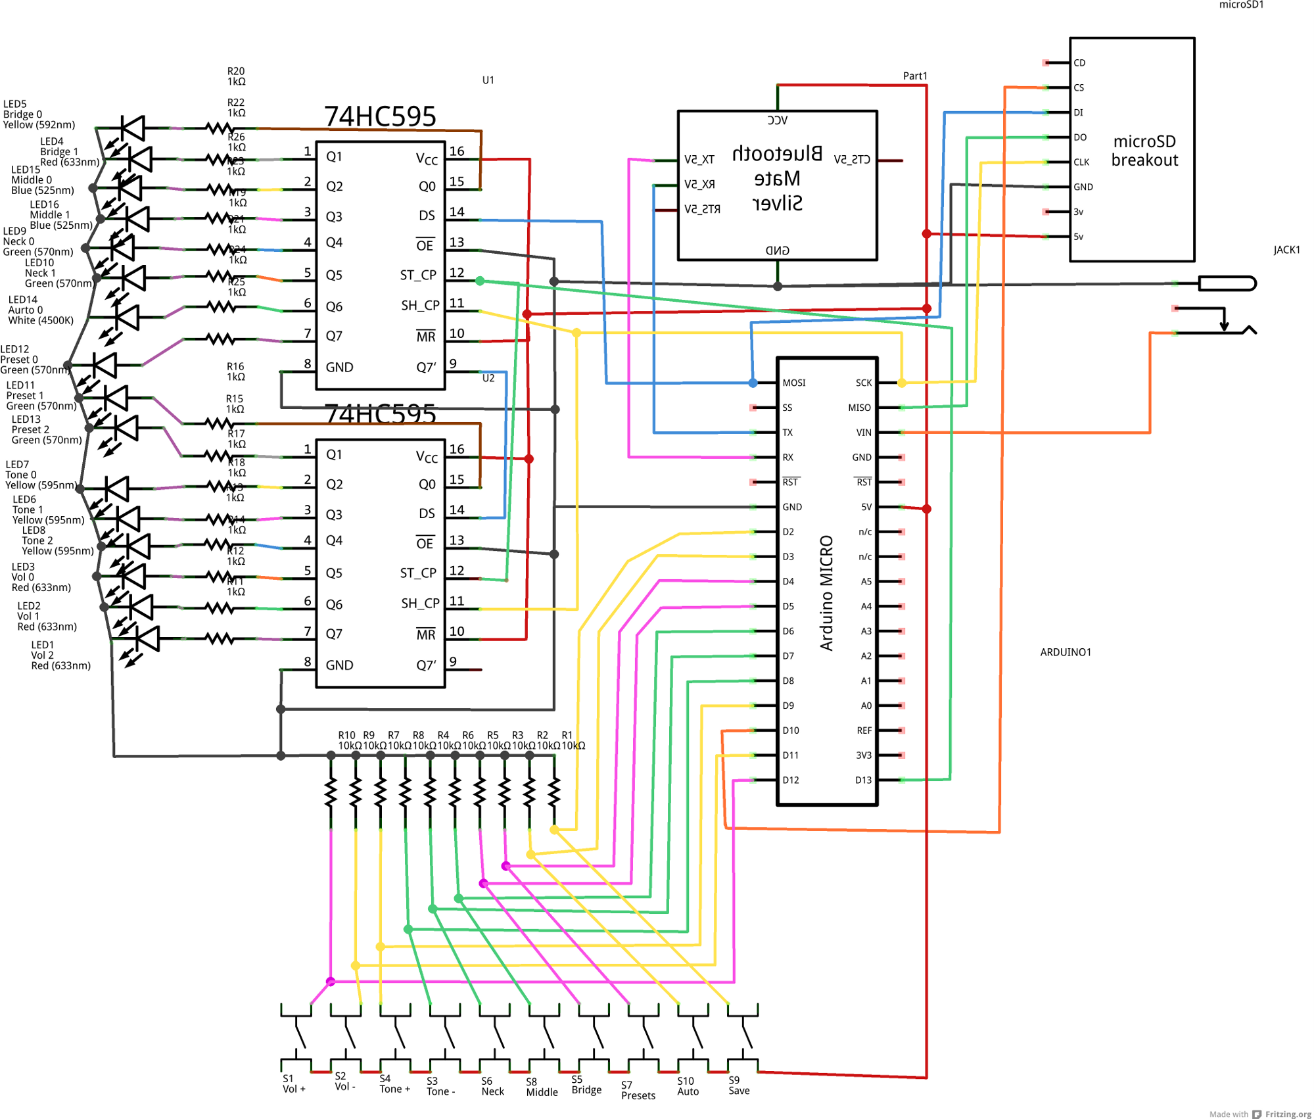
arduino/Layouts/ArduStomp/ArduStomp02/ArduStomp02schematic.png
