gratefulfrog/ArduGuitar/arduino/Layouts/ArduStomp/EnclosureDesign/3D/Arcs Model/Arcs01.png

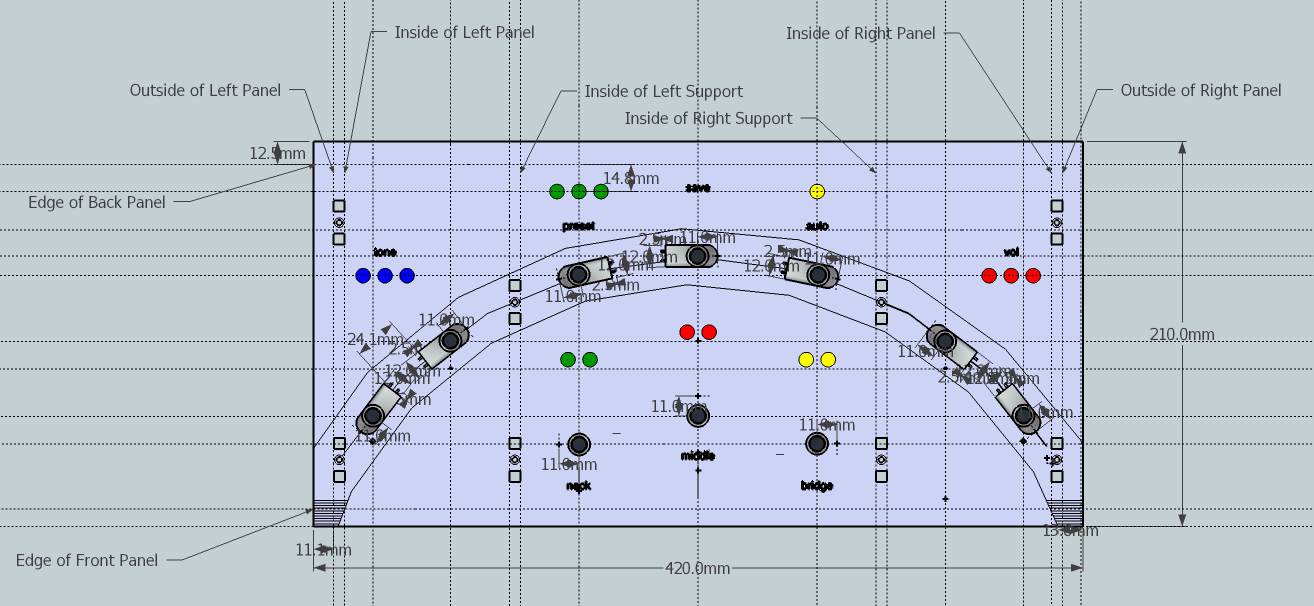
arduino/Layouts/ArduStomp/EnclosureDesign/3D/Arcs Model/Arcs01.png
