gratefulfrog/ArduGuitar/arduino/Layouts/ArduStomp/EnclosureDesign/3D/Arcs Model/Arcs07.png

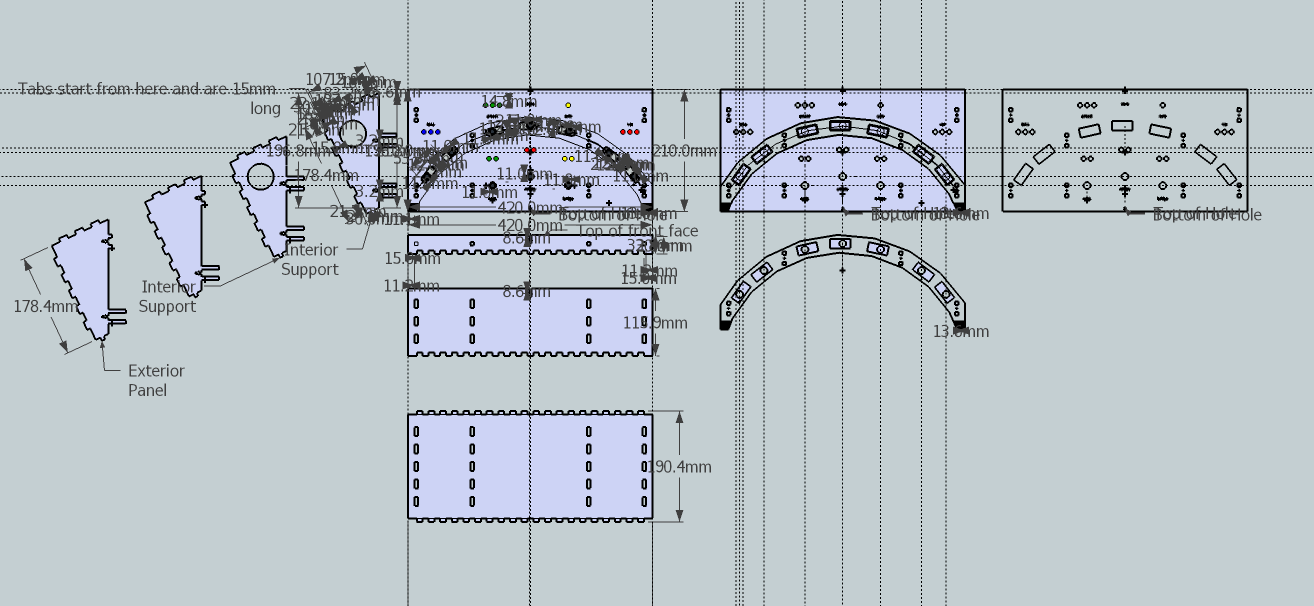
arduino/Layouts/ArduStomp/EnclosureDesign/3D/Arcs Model/Arcs07.png
