gratefulfrog/ArduGuitar/arduino/Layouts/ArduStomp/EnclosureDesign/3D/ArduStomp Prototypes/ConceptualView.png

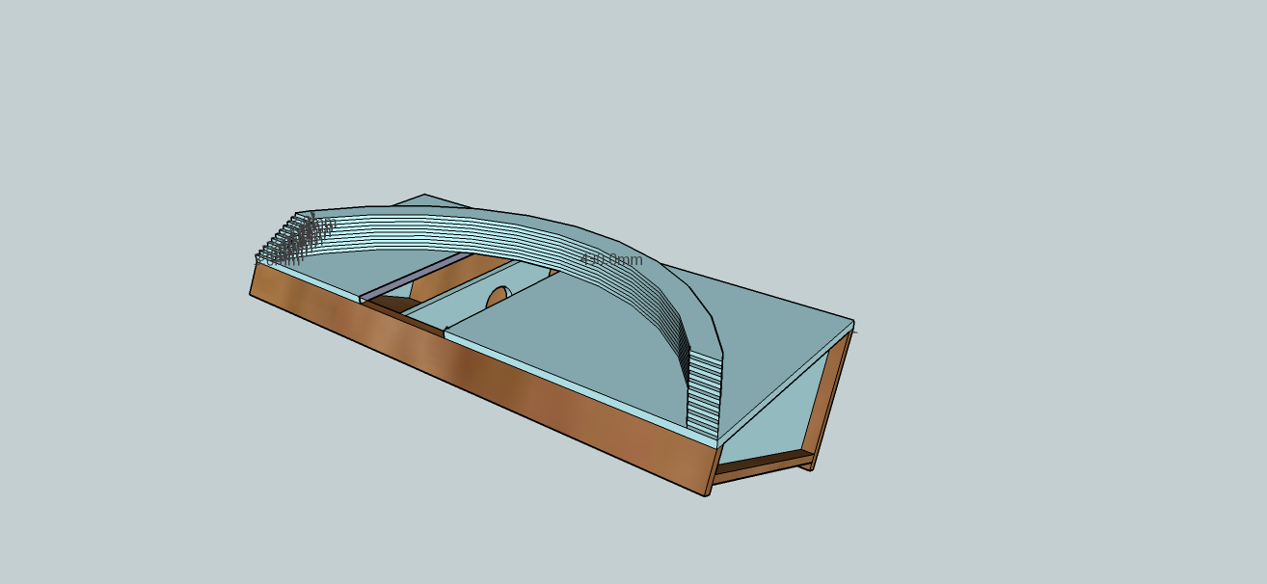
arduino/Layouts/ArduStomp/EnclosureDesign/3D/ArduStomp Prototypes/ConceptualView.png
