gratefulfrog/ArduGuitar/arduino/Layouts/ArduStomp/EnclosureDesign/3D/ArduStomp Prototypes/Enclosure 00.png

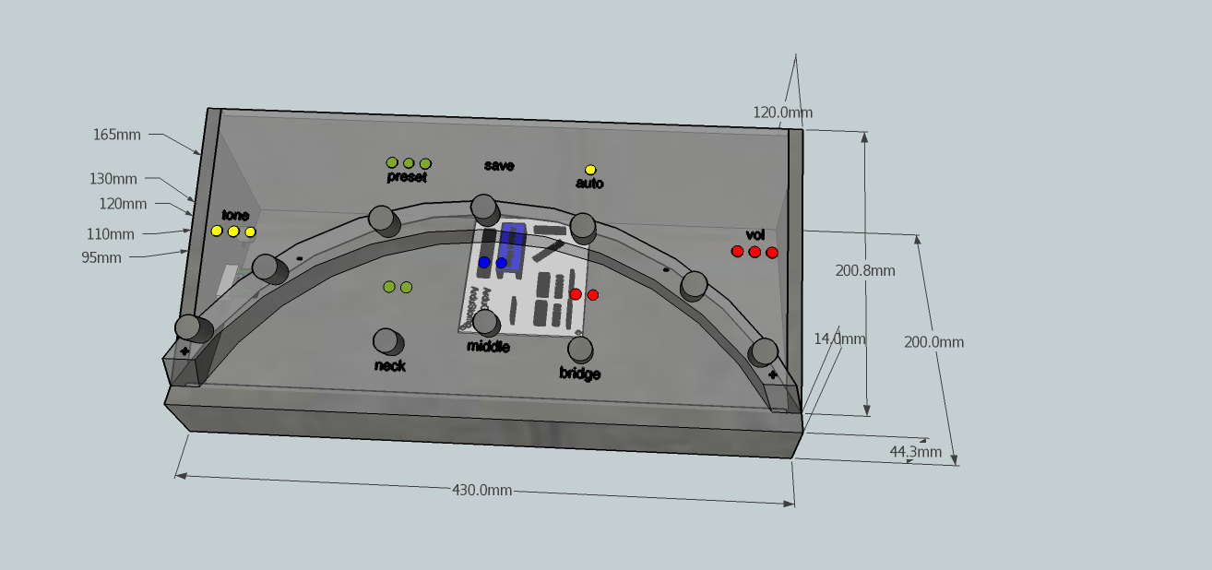
arduino/Layouts/ArduStomp/EnclosureDesign/3D/ArduStomp Prototypes/Enclosure 00.png
