gratefulfrog/ArduGuitar/arduino/Layouts/ArduStomp/EnclosureDesign/3D/SDCardReader/SD Card Reader.png

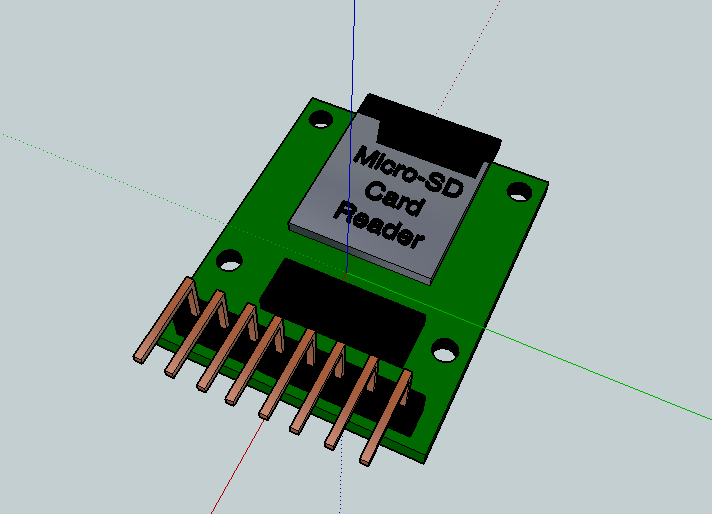
arduino/Layouts/ArduStomp/EnclosureDesign/3D/SDCardReader/SD Card Reader.png
