gratefulfrog/ArduGuitar/arduino/Layouts/ArduStomp/EnclosureDesign/ArcLAyout01.png

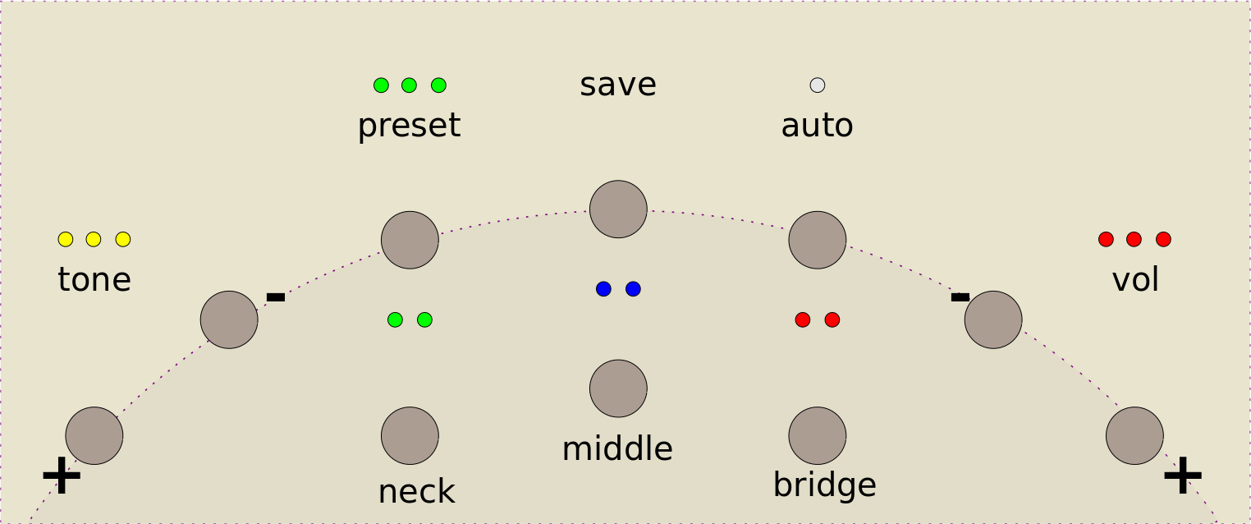
arduino/Layouts/ArduStomp/EnclosureDesign/ArcLAyout01.png
