gratefulfrog/ArduGuitar/arduino/Layouts/ArduStomp/EnclosureDesign/Photos/IMG_20131108_214445.jpg

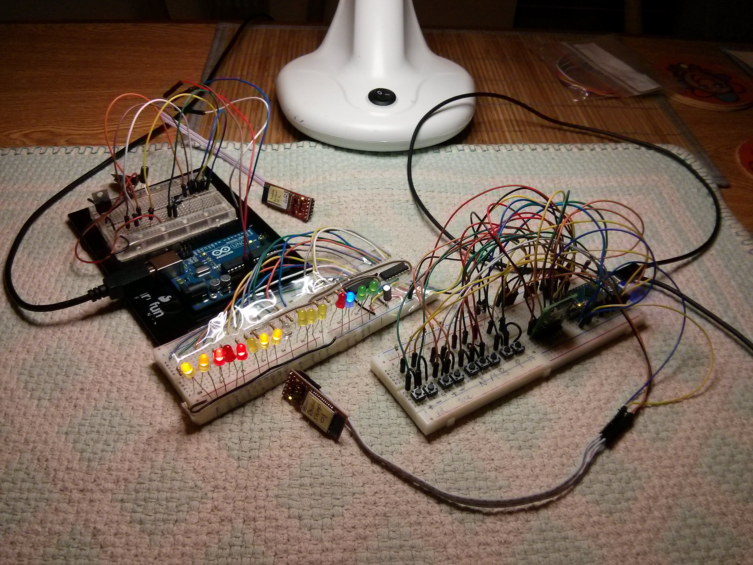
arduino/Layouts/ArduStomp/EnclosureDesign/Photos/IMG_20131108_214445.jpg
