gratefulfrog/ArduGuitar/arduino/Layouts/ArduStomp/EnclosureDesign/Photos/IMG_20131111_161719.jpg

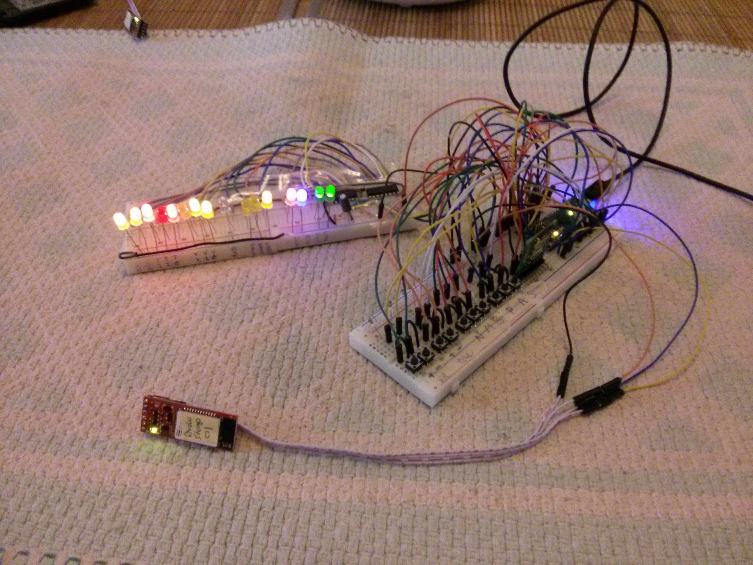
arduino/Layouts/ArduStomp/EnclosureDesign/Photos/IMG_20131111_161719.jpg
