gratefulfrog/ArduGuitar/arduino/Layouts/ArduStomp/EnclosureDesign/Photos/IMG_20131112_180953.jpg

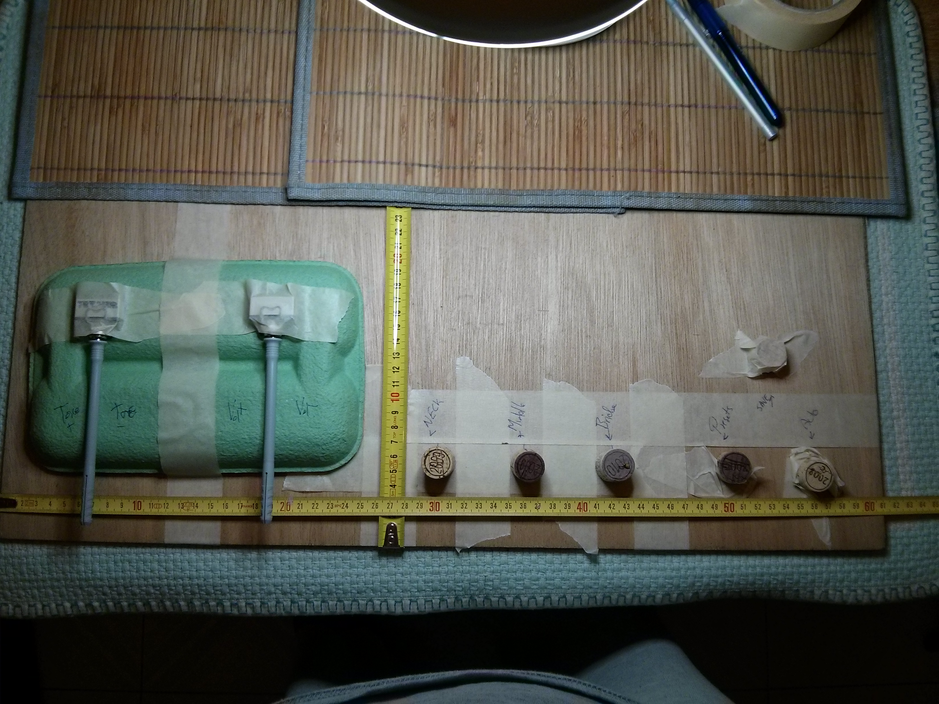
arduino/Layouts/ArduStomp/EnclosureDesign/Photos/IMG_20131112_180953.jpg
