gratefulfrog/ArduGuitar/arduino/Layouts/ArduStomp/EnclosureDesign/Photos/IMG_20131112_190251.jpg

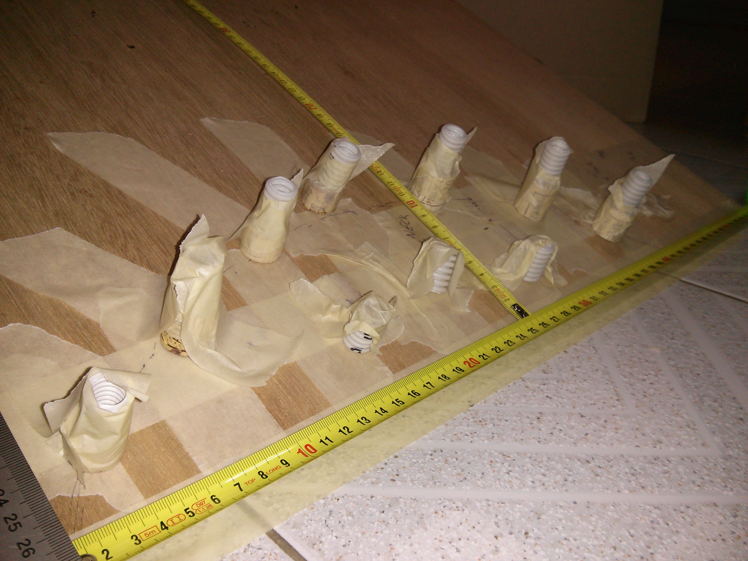
arduino/Layouts/ArduStomp/EnclosureDesign/Photos/IMG_20131112_190251.jpg
