gratefulfrog/ArduGuitar/arduino/Layouts/ArduStomp/EnclosureDesign/Photos/IMG_20131112_190456.jpg

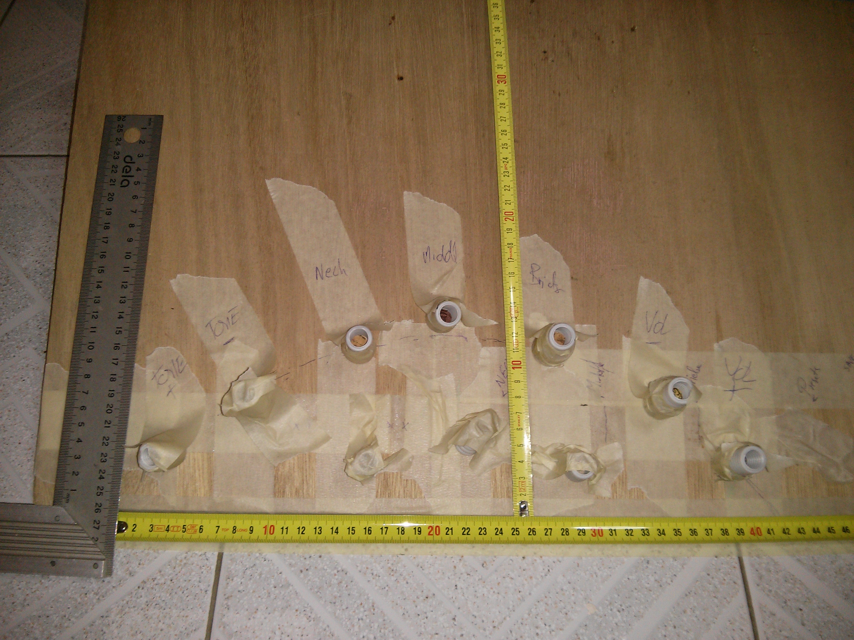
arduino/Layouts/ArduStomp/EnclosureDesign/Photos/IMG_20131112_190456.jpg
