gratefulfrog/ArduGuitar/arduino/Layouts/ArduStomp/EnclosureDesign/Photos/IMG_20131114_181835.jpg

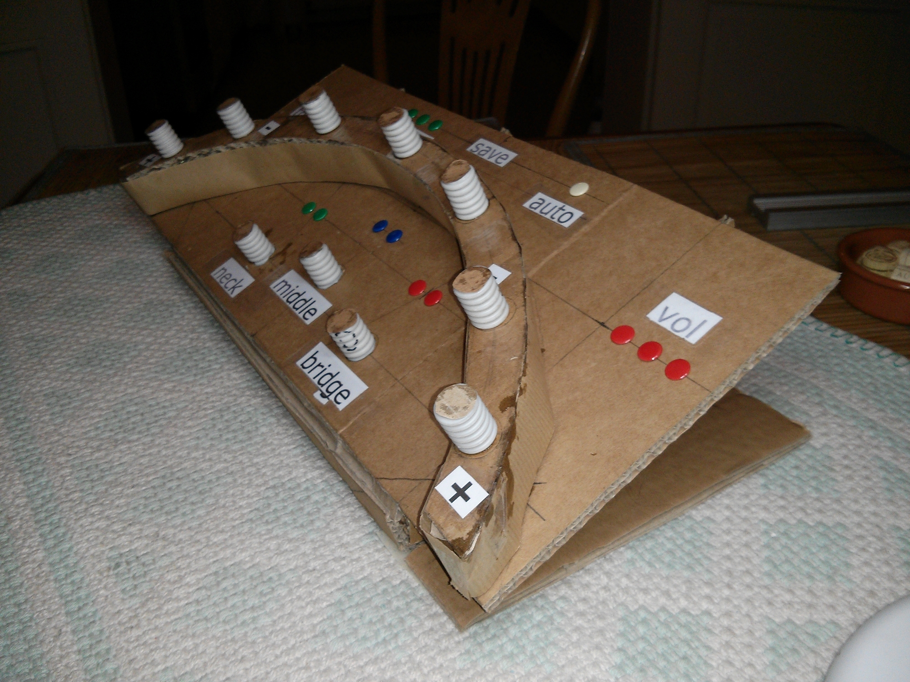
arduino/Layouts/ArduStomp/EnclosureDesign/Photos/IMG_20131114_181835.jpg
