gratefulfrog/ArduGuitar/arduino/Layouts/ArduStomp/EnclosureDesign/Photos/IMG_20131114_181906.jpg

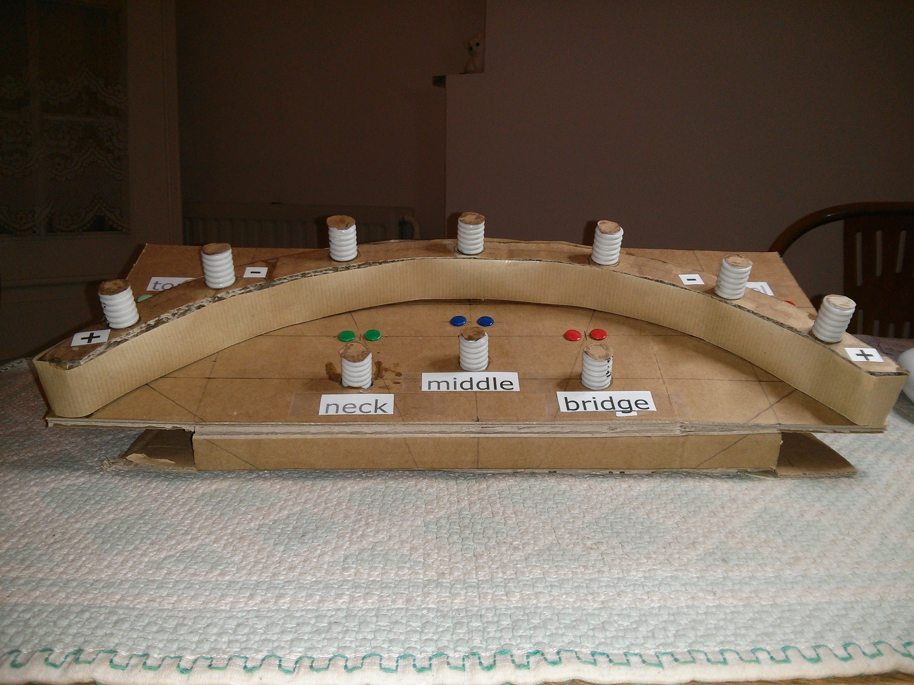
arduino/Layouts/ArduStomp/EnclosureDesign/Photos/IMG_20131114_181906.jpg
