gratefulfrog/ArduGuitar/arduino/Layouts/ArduStomp/EnclosureDesign/Photos/IMG_20131114_182025.jpg

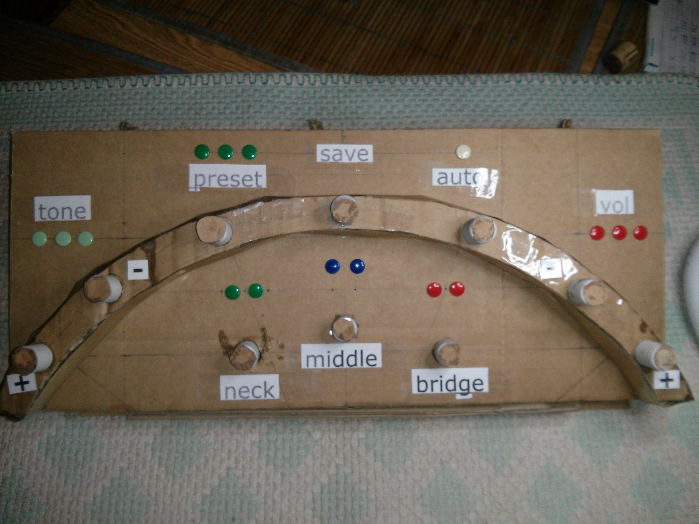
arduino/Layouts/ArduStomp/EnclosureDesign/Photos/IMG_20131114_182025.jpg
