gratefulfrog/ArduGuitar/arduino/Layouts/ArduStomp/EnclosureDesign/Photos/IMG_20131221_200612.jpg

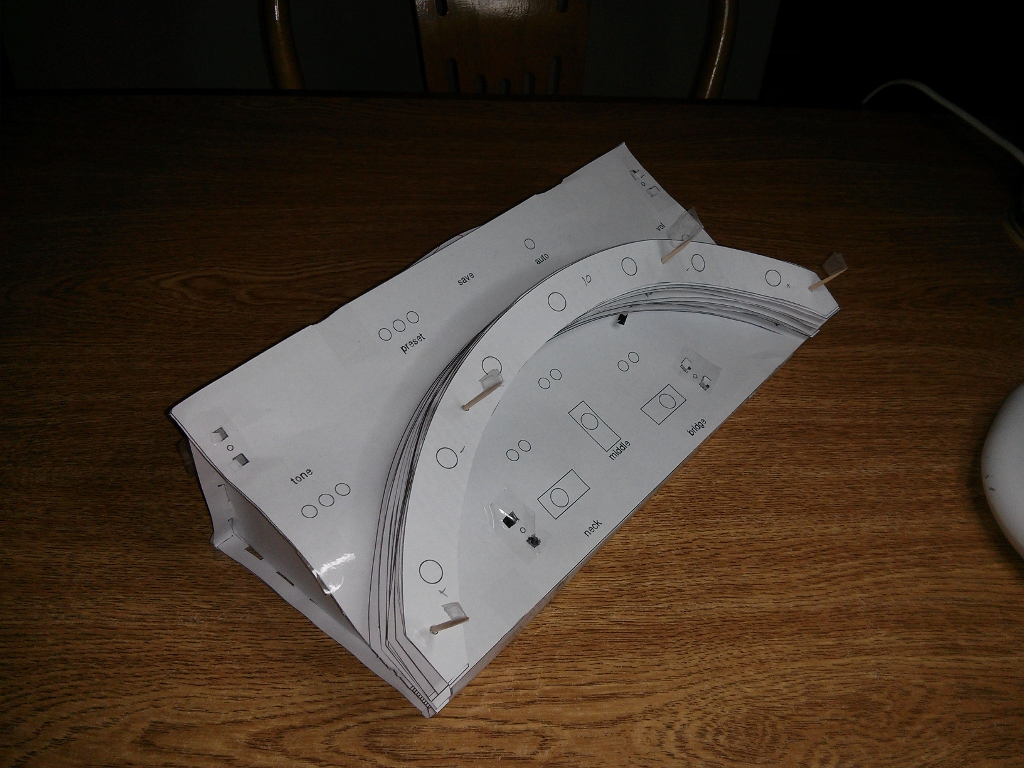
arduino/Layouts/ArduStomp/EnclosureDesign/Photos/IMG_20131221_200612.jpg
