gratefulfrog/ArduGuitar/arduino/Layouts/ArduStomp/EnclosureDesign/Photos/IMG_20131224_122529.jpg

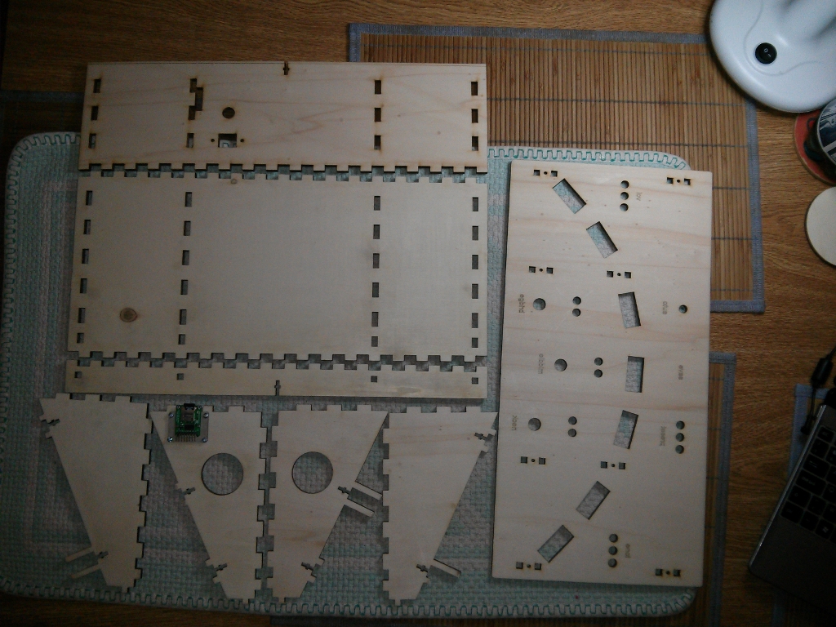
arduino/Layouts/ArduStomp/EnclosureDesign/Photos/IMG_20131224_122529.jpg
