gratefulfrog/ArduGuitar/arduino/Layouts/ArduStomp/EnclosureDesign/Photos/IMG_20131224_123456.jpg

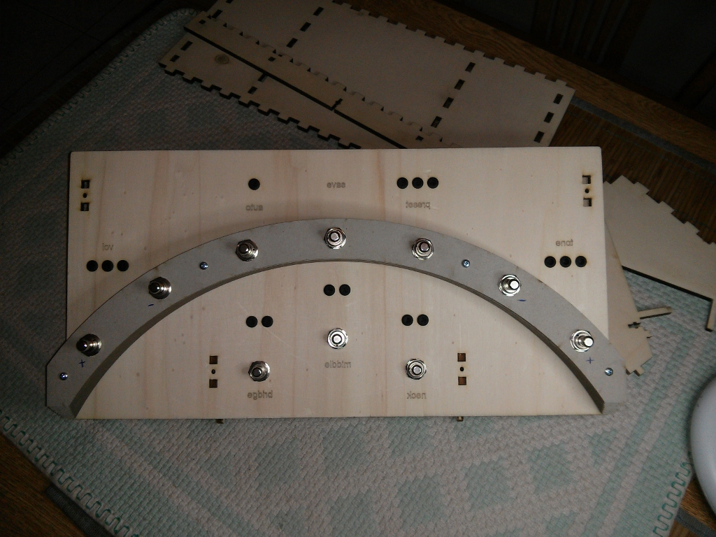
arduino/Layouts/ArduStomp/EnclosureDesign/Photos/IMG_20131224_123456.jpg
