gratefulfrog/ArduGuitar/arduino/Layouts/ArduStomp/EnclosureDesign/Photos/IMG_20131224_123618.jpg

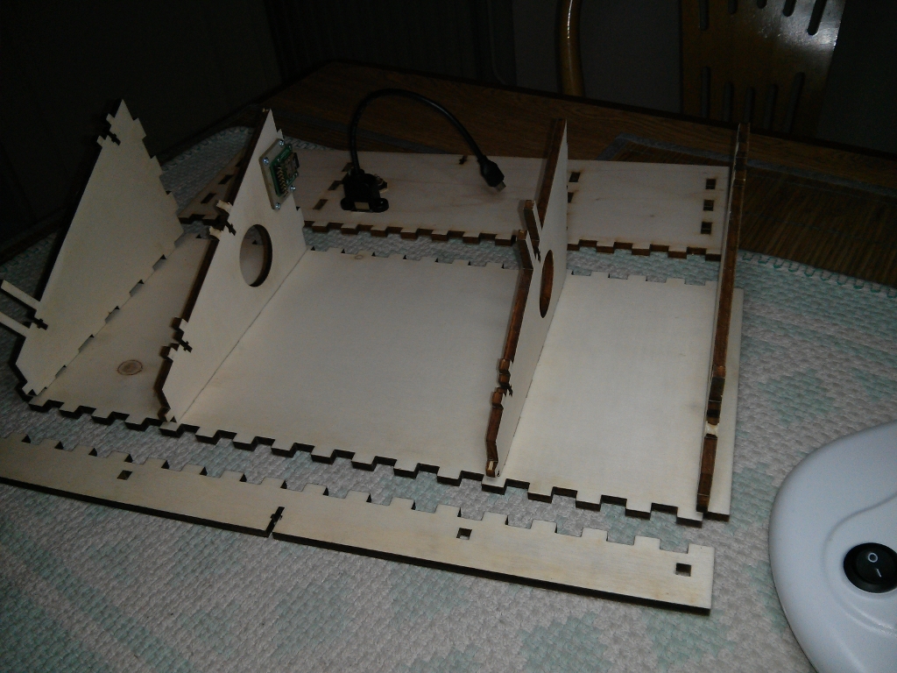
arduino/Layouts/ArduStomp/EnclosureDesign/Photos/IMG_20131224_123618.jpg
