gratefulfrog/ArduGuitar/arduino/Layouts/ArduStomp/EnclosureDesign/Photos/IMG_20131224_124239.jpg

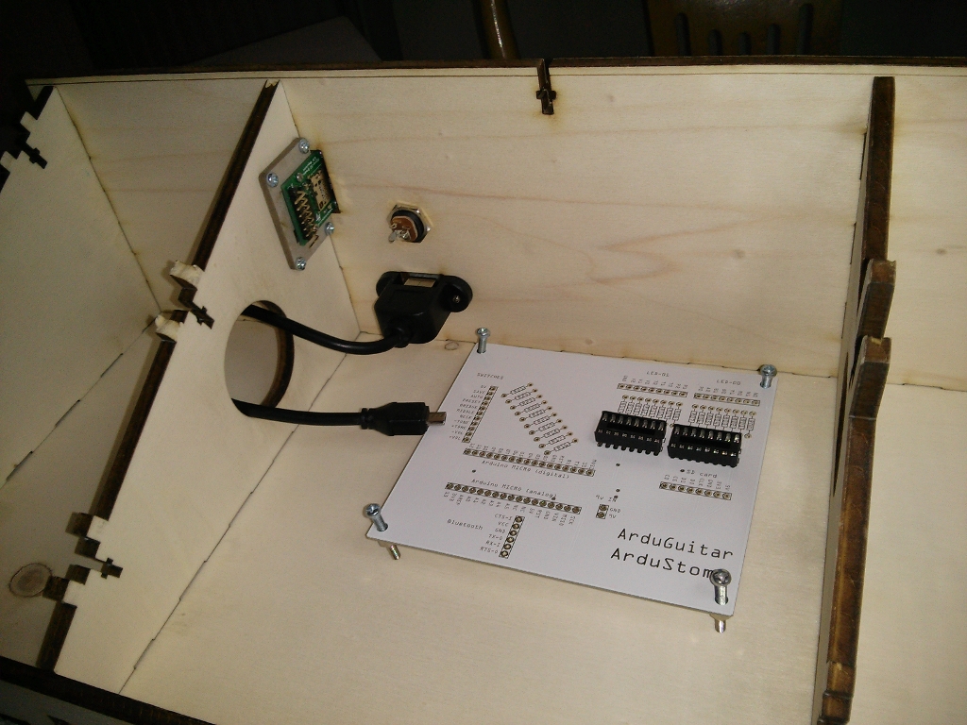
arduino/Layouts/ArduStomp/EnclosureDesign/Photos/IMG_20131224_124239.jpg
