gratefulfrog/ArduGuitar/arduino/Layouts/ArduStomp/EnclosureDesign/Photos/IMG_20131224_124545.jpg

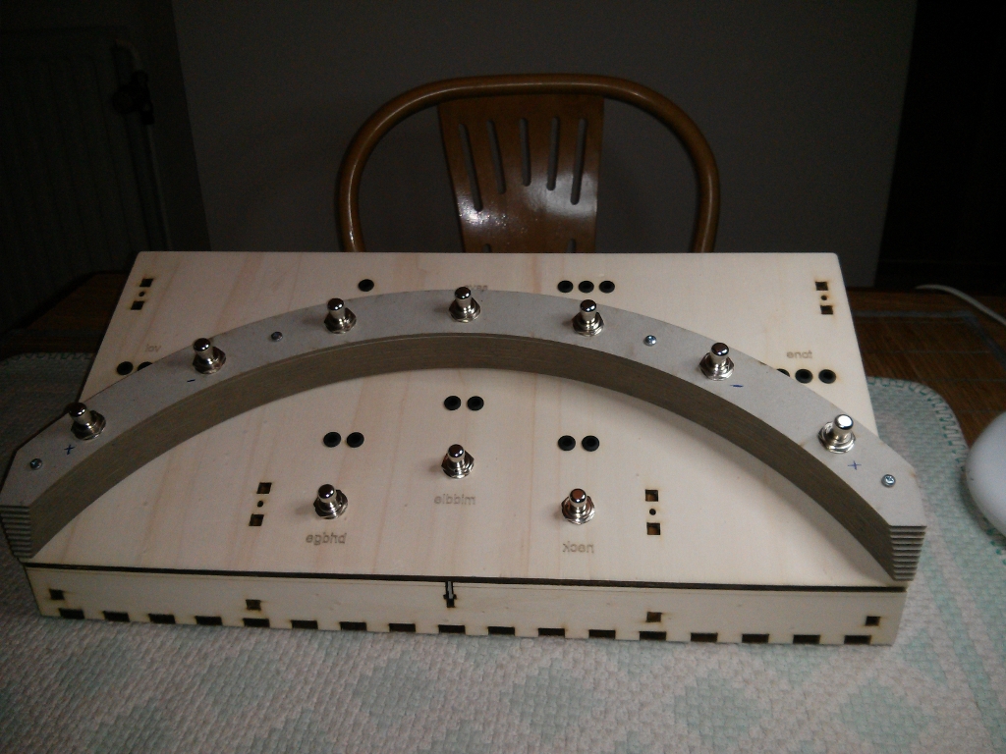
arduino/Layouts/ArduStomp/EnclosureDesign/Photos/IMG_20131224_124545.jpg
