gratefulfrog/ArduGuitar/arduino/Layouts/ArduStomp/EnclosureDesign/Photos/IMG_20131224_124900.jpg

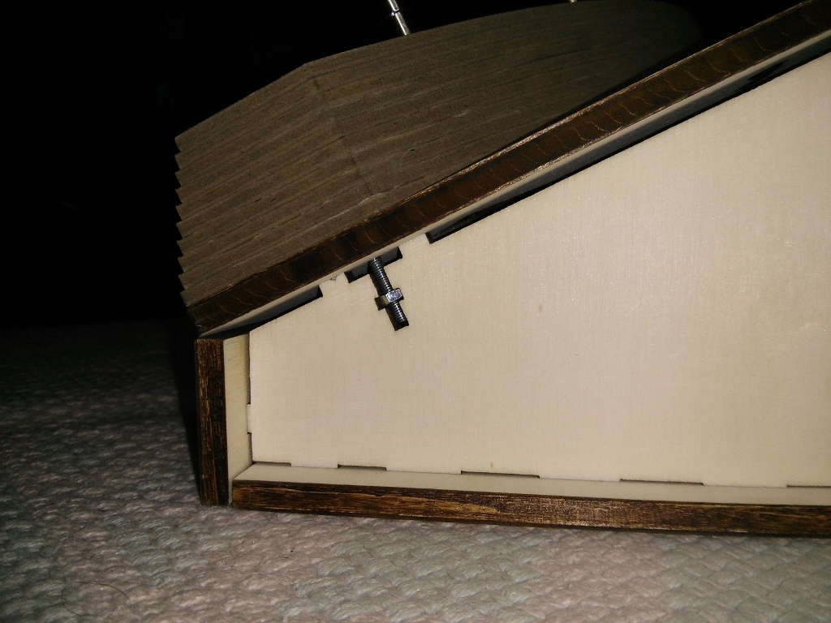
arduino/Layouts/ArduStomp/EnclosureDesign/Photos/IMG_20131224_124900.jpg
