gratefulfrog/ArduGuitar/arduino/Layouts/ArduStomp/EnclosureDesign/Photos/IMG_20131225_121725.jpg

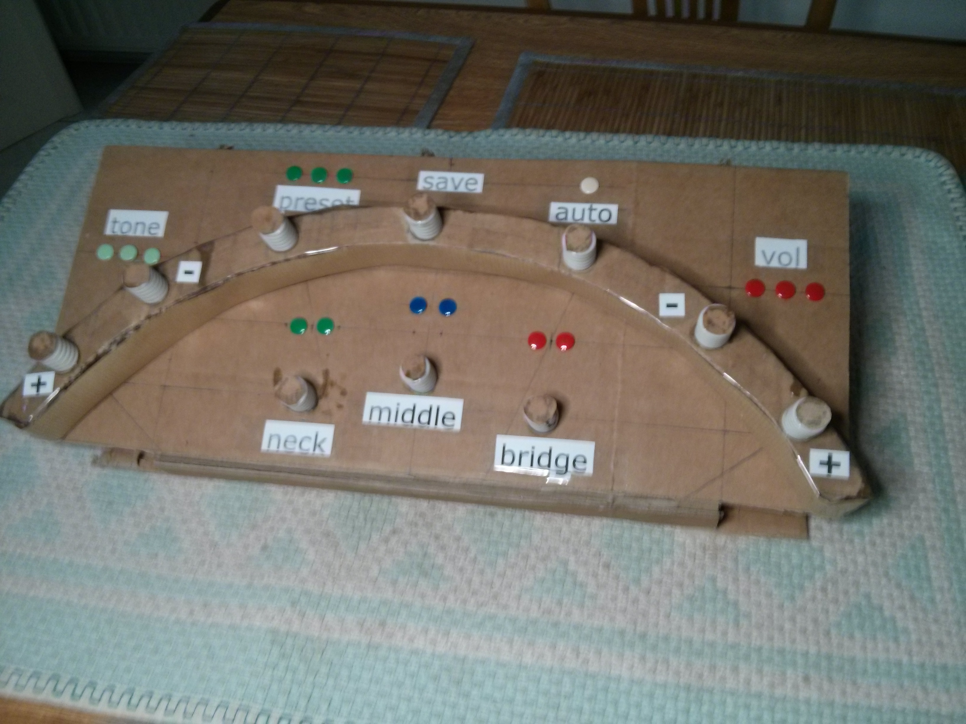
arduino/Layouts/ArduStomp/EnclosureDesign/Photos/IMG_20131225_121725.jpg
