gratefulfrog/ArduGuitar/arduino/Layouts/ArduStomp/EnclosureDesign/Photos/IMG_20131225_121743.jpg

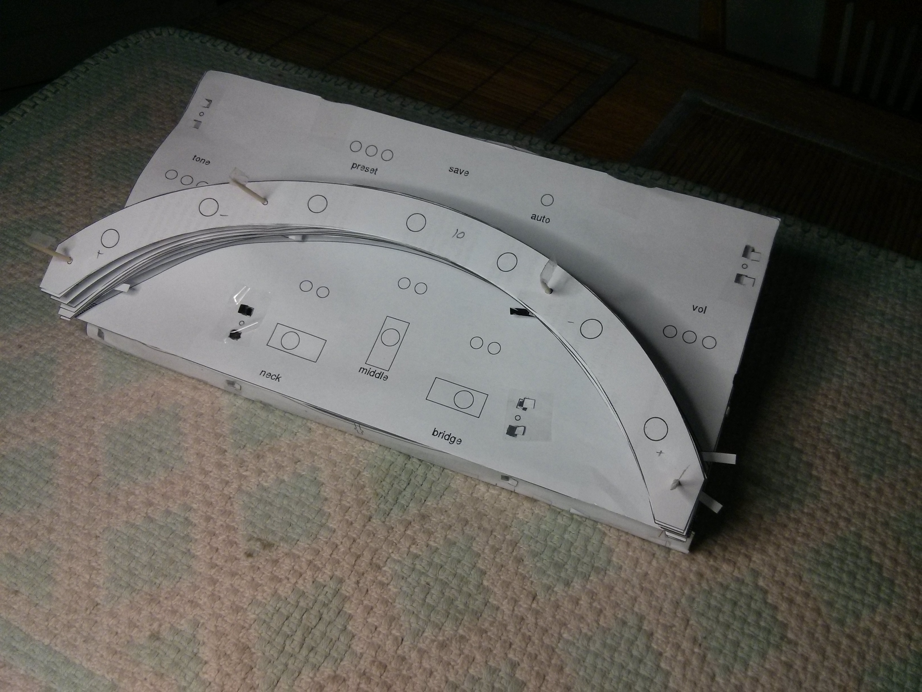
arduino/Layouts/ArduStomp/EnclosureDesign/Photos/IMG_20131225_121743.jpg
