gratefulfrog/ArduGuitar/arduino/Layouts/ArduStomp/EnclosureDesign/Photos/IMG_20140101_183116.jpg

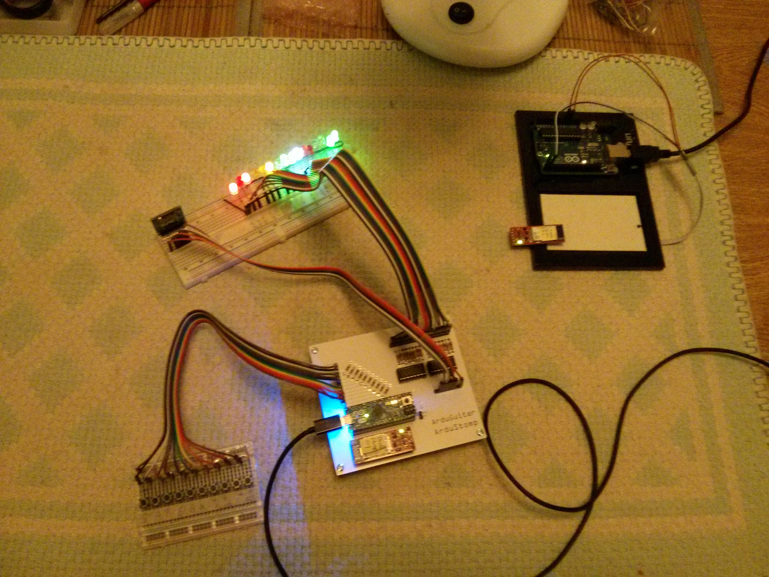
arduino/Layouts/ArduStomp/EnclosureDesign/Photos/IMG_20140101_183116.jpg
