gratefulfrog/ArduGuitar/arduino/Layouts/ArduStomp/EnclosureDesign/Photos/IMG_20140108_120447.jpg

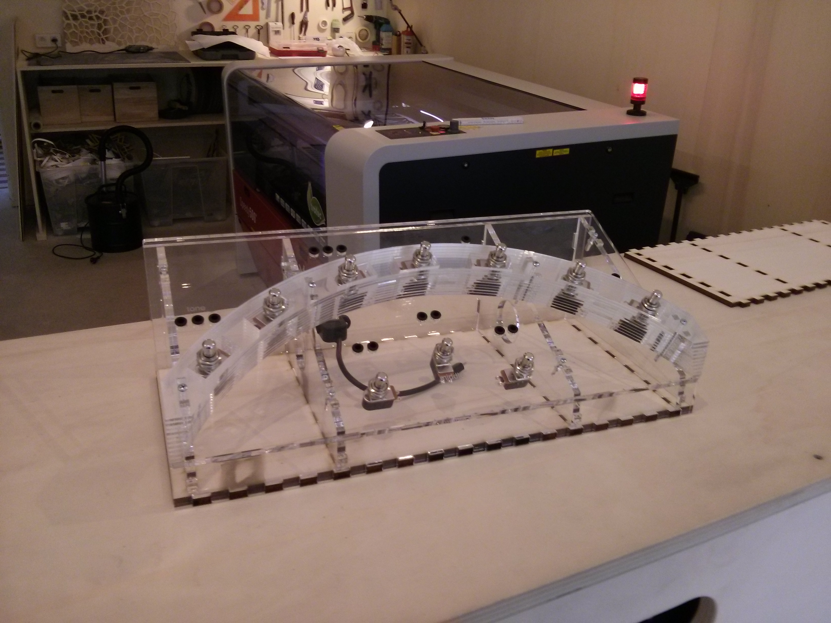
arduino/Layouts/ArduStomp/EnclosureDesign/Photos/IMG_20140108_120447.jpg
