gratefulfrog/ArduGuitar/arduino/Layouts/ArduStomp/EnclosureDesign/Photos/IMG_20140126_104611.jpg

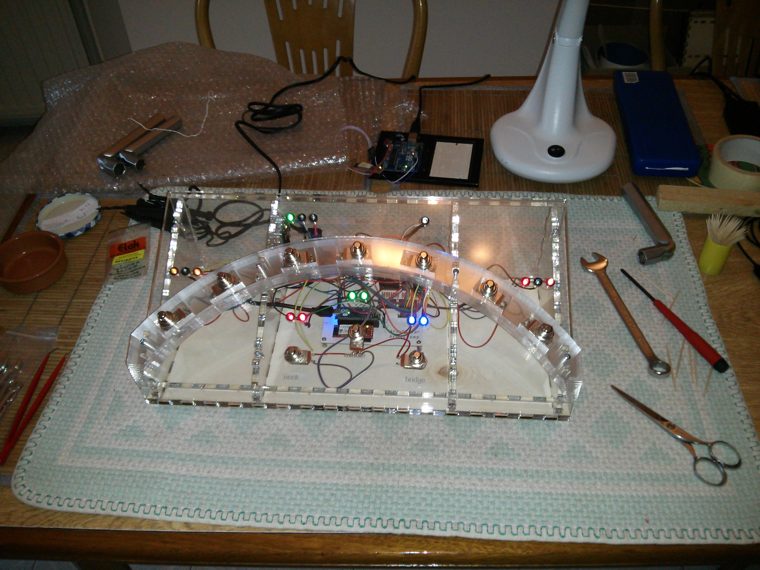
arduino/Layouts/ArduStomp/EnclosureDesign/Photos/IMG_20140126_104611.jpg
