gratefulfrog/ArduGuitar/arduino/Layouts/ArduStomp/EnclosureDesign/Photos/IMG_20140126_105929.jpg

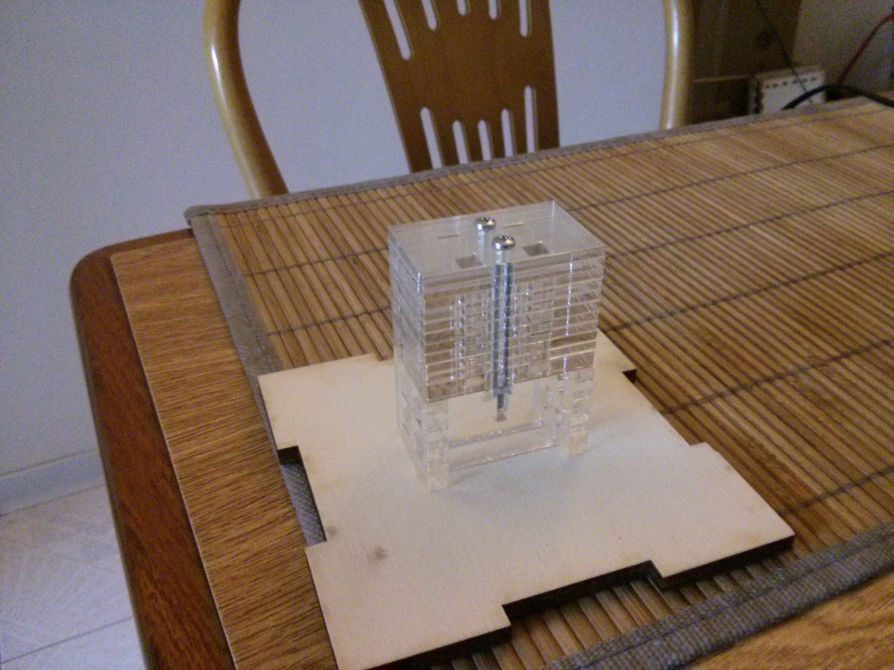
arduino/Layouts/ArduStomp/EnclosureDesign/Photos/IMG_20140126_105929.jpg
