gratefulfrog/ArduGuitar/arduino/Layouts/ArduStomp/EnclosureDesign/Photos/IMG_20140126_120722.jpg

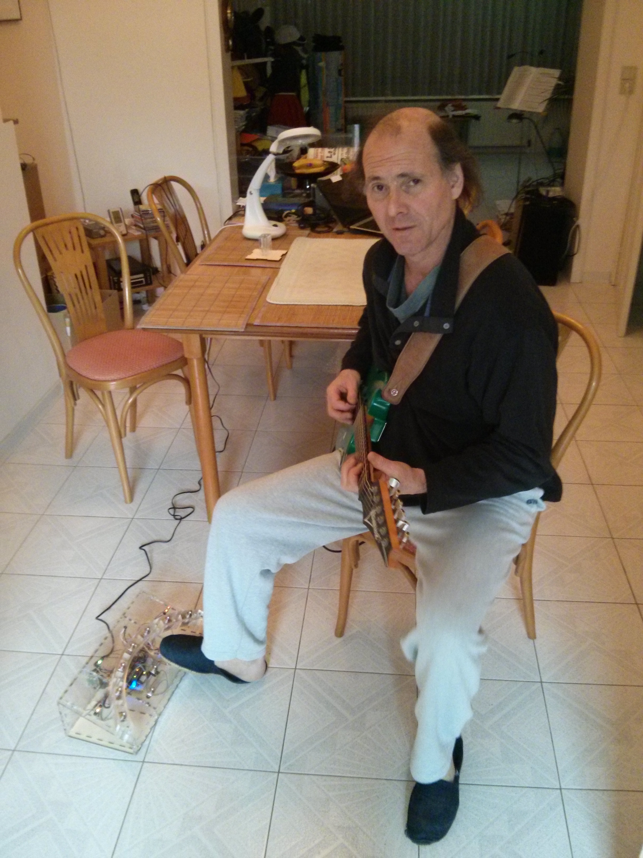
arduino/Layouts/ArduStomp/EnclosureDesign/Photos/IMG_20140126_120722.jpg
