gratefulfrog/ArduGuitar/arduino/Layouts/ArduStomp/EnclosureDesign/Photos/IMG_20140126_120724.jpg

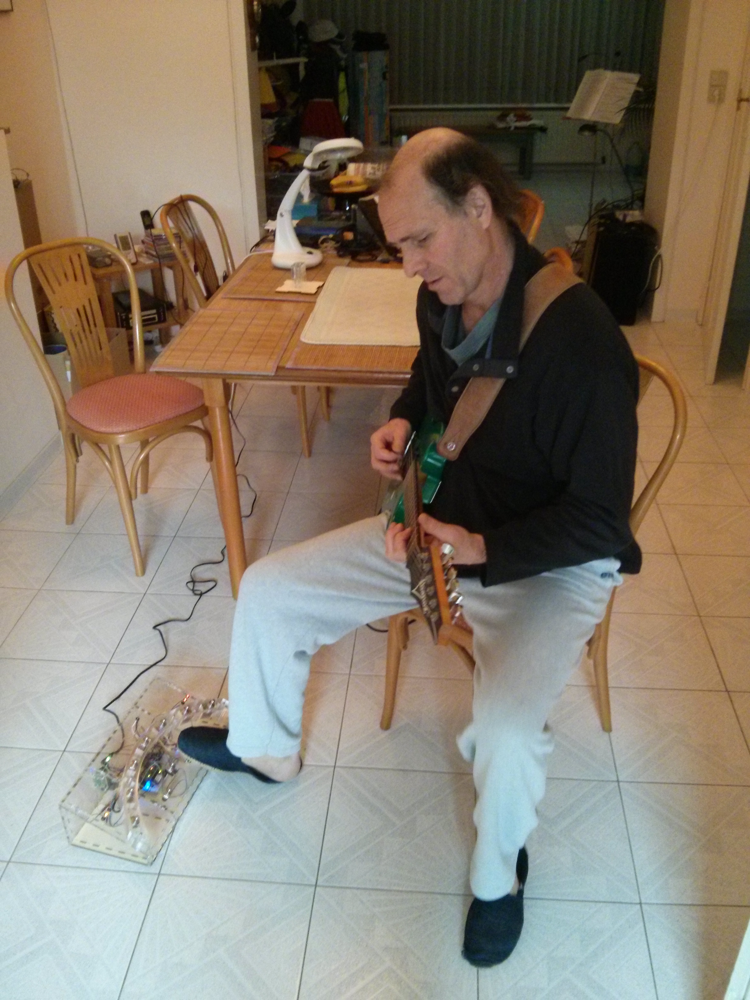
arduino/Layouts/ArduStomp/EnclosureDesign/Photos/IMG_20140126_120724.jpg
