gratefulfrog/ArduGuitar/arduino/Layouts/ArduStomp/EnclosureDesign/Photos/IMG_20140126_122457.jpg

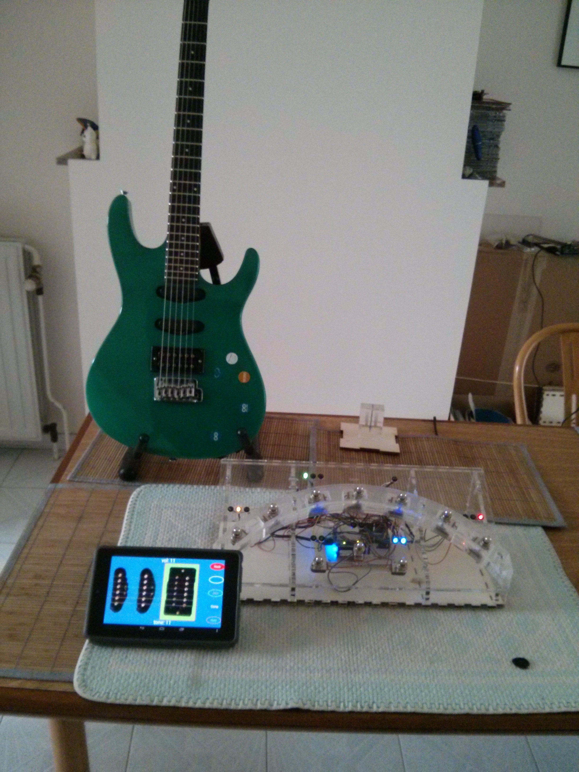
arduino/Layouts/ArduStomp/EnclosureDesign/Photos/IMG_20140126_122457.jpg
