gratefulfrog/ArduGuitar/arduino/Layouts/ArduStomp/EnclosureDesign/Photos/IMG_20140126_122506.jpg

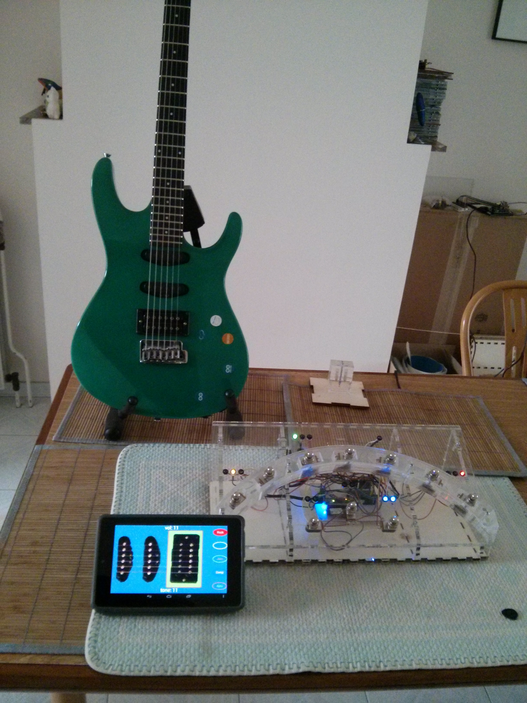
arduino/Layouts/ArduStomp/EnclosureDesign/Photos/IMG_20140126_122506.jpg
