gratefulfrog/ArduGuitar/arduino/Layouts/ArduStomp/EnclosureDesign/stomp-box-02.png

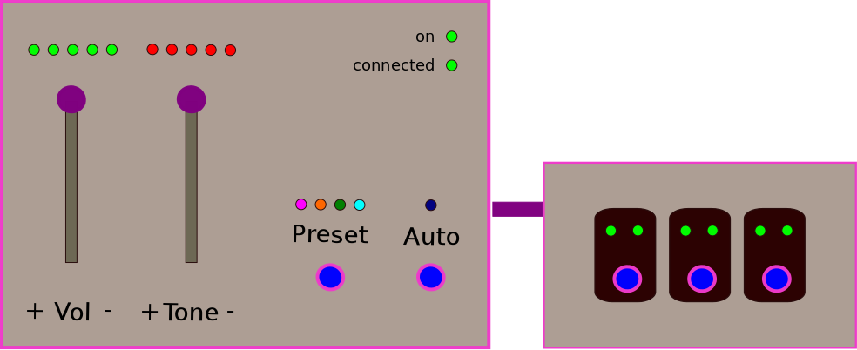
arduino/Layouts/ArduStomp/EnclosureDesign/stomp-box-02.png
