gratefulfrog/ArduGuitar/arduino/Layouts/ArduStomp/EnclosureDesign/stomp-box.png

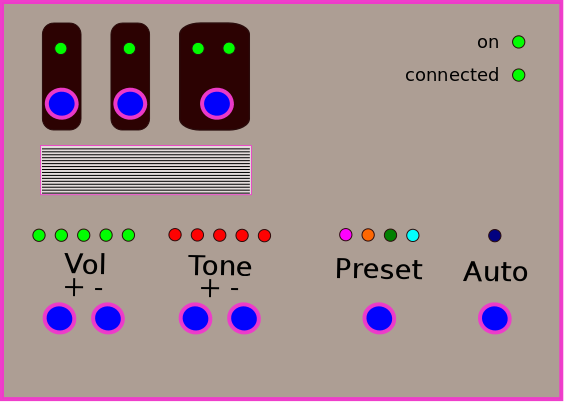
arduino/Layouts/ArduStomp/EnclosureDesign/stomp-box.png
