gratefulfrog/ArduGuitar/arduino/Layouts/ArduStomp/EnclosureDesign/2D/FullDesign01.dxf

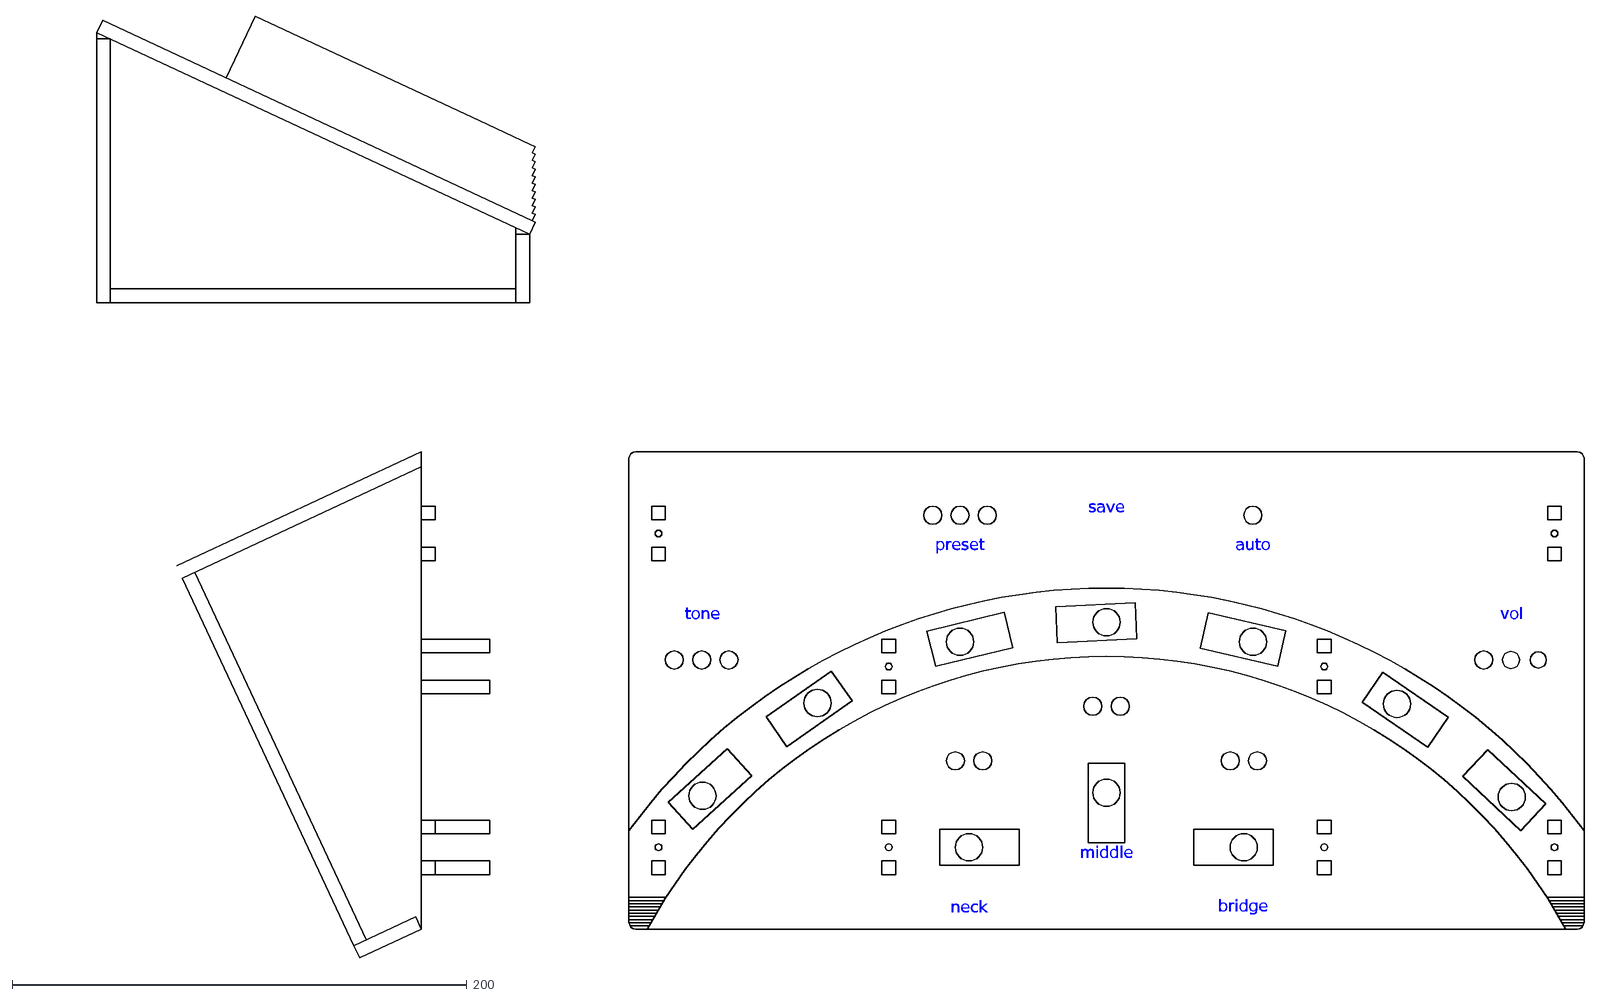
[picture p221: CAD file, 2013-12-15]
arduino/Layouts/ArduStomp/EnclosureDesign/2D/FullDesign01.dxf
neck
middle
bridge
tone
save
vol
preset
auto
