gratefulfrog/ArduGuitar/Ardu2/design/POC-2/Carvin Integration/Carvin/MyCarvin/PushButton_3_6.stl

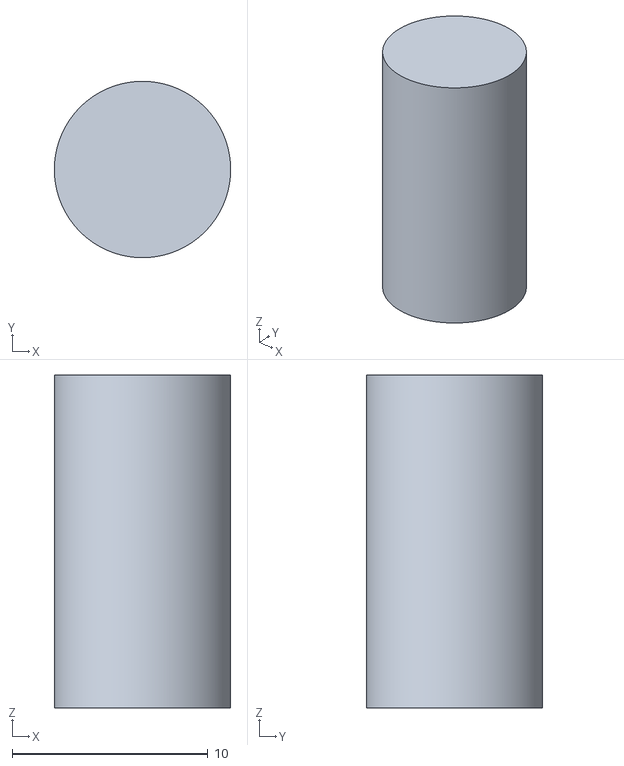
[picture p222: CAD file, 2015-04-13]
Ardu2/design/POC-2/Carvin Integration/Carvin/MyCarvin/PushButton_3_6.stl
9.00 x 9.00 x 17.0
