gratefulfrog/ArduGuitar/Ardu2/design/POC-3_MAX395/HMI/#HMI_03_Guitar_Cut_03.dxf

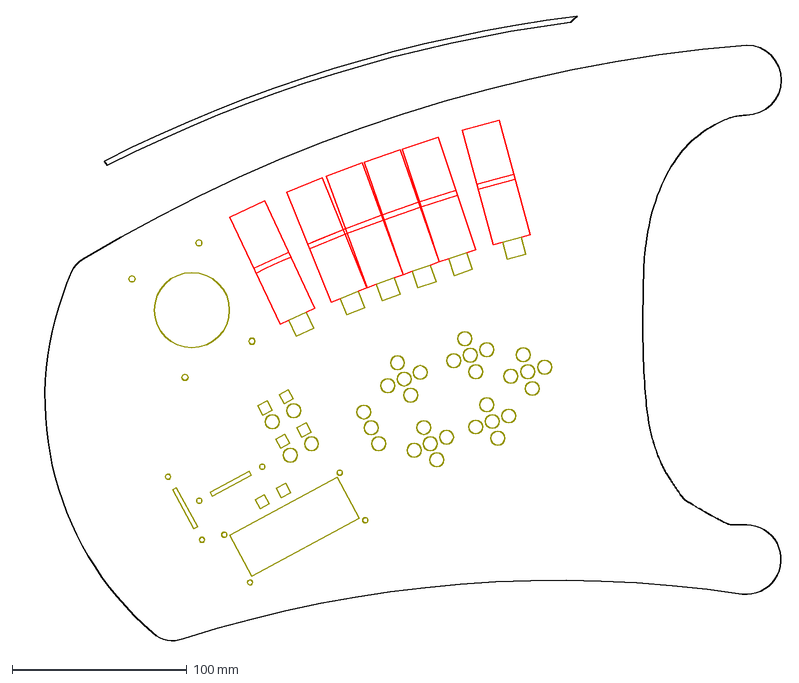
[picture p223: CAD file, 2017-06-04]
Ardu2/design/POC-3_MAX395/HMI/#HMI_03_Guitar_Cut_03.dxf
439.2 x 358.8 mm
