gratefulfrog/ArduGuitar/Ardu2/design/POC-3_MAX395/HMI/KicadProjects/2PB with Headers/DXF/2PB with Headers-NPTH-drl_map.dxf

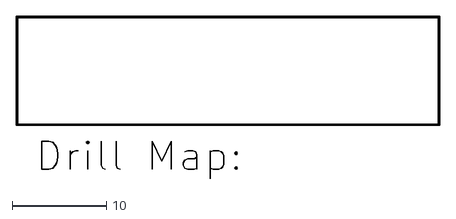
[picture p224: CAD file, 2016-01-25]
Ardu2/design/POC-3_MAX395/HMI/KicadProjects/2PB with Headers/DXF/2PB with Headers-NPTH-drl_map.dxf
44.9 x 17.2
