gratefulfrog/ArduGuitar/Ardu2/design/POC-3_MAX395/HMI/KicadProjects/Single HW Debounce PBs circuit /PB2 PCB.dxf

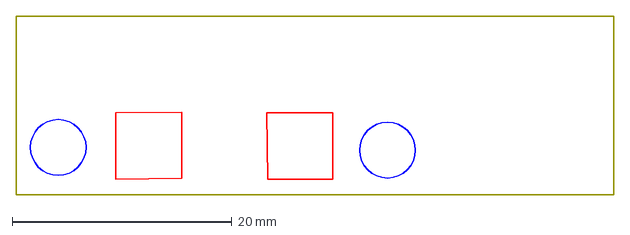
[picture p225: CAD file, 2016-01-24]
Ardu2/design/POC-3_MAX395/HMI/KicadProjects/Single HW Debounce PBs circuit /PB2 PCB.dxf
54.4 x 16.3 mm
