gratefulfrog/ArduGuitar/Ardu2/design/POC-3_MAX395/HMI/KicadProjects/Single HW Debounce PBs circuit /SVG/HW Debounce Button-brd.dxf

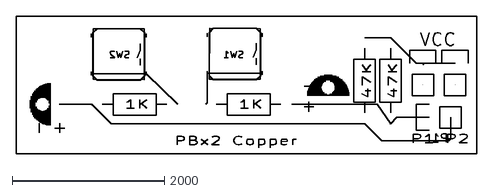
[picture p226: CAD file, 2016-01-24]
Ardu2/design/POC-3_MAX395/HMI/KicadProjects/Single HW Debounce PBs circuit /SVG/HW Debounce Button-brd.dxf
6039.6 x 1806.2
