gratefulfrog/ArduGuitar/Ardu2/design/POC-3_MAX395/HMI/MountingBlocks/LaserCutTempBlocksR12.dxf

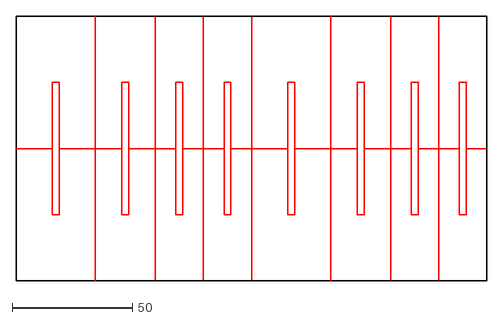
[picture p227: CAD file, 2017-06-09]
Ardu2/design/POC-3_MAX395/HMI/MountingBlocks/LaserCutTempBlocksR12.dxf
196.0 x 110.0
