gratefulfrog/ArduGuitar/Ardu2/design/POC-3_MAX395/pyboard/images/10PDT Soldering.dxf

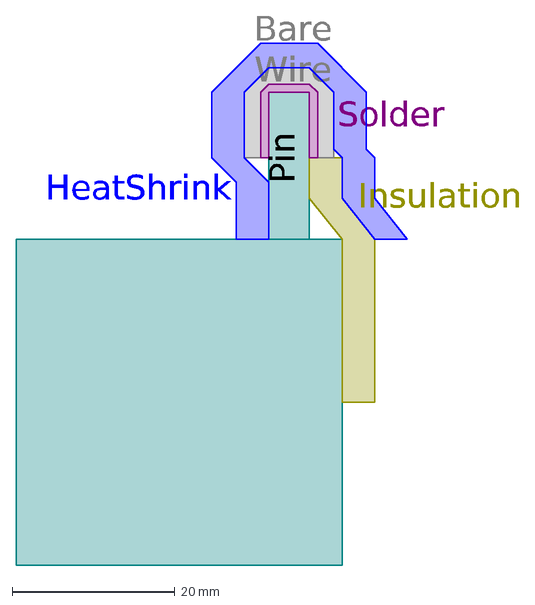
[picture p229: CAD file, 2017-02-13]
Ardu2/design/POC-3_MAX395/pyboard/images/10PDT Soldering.dxf
Pin
Insulation
Bare Wire
Solder
HeatShrink
