gratefulfrog/ArduGuitar/Ardu2/design/POC-3_MAX395/pyboard/V1_WithHMI/PyHMI/Data/PyGuitar Architecture.dxf

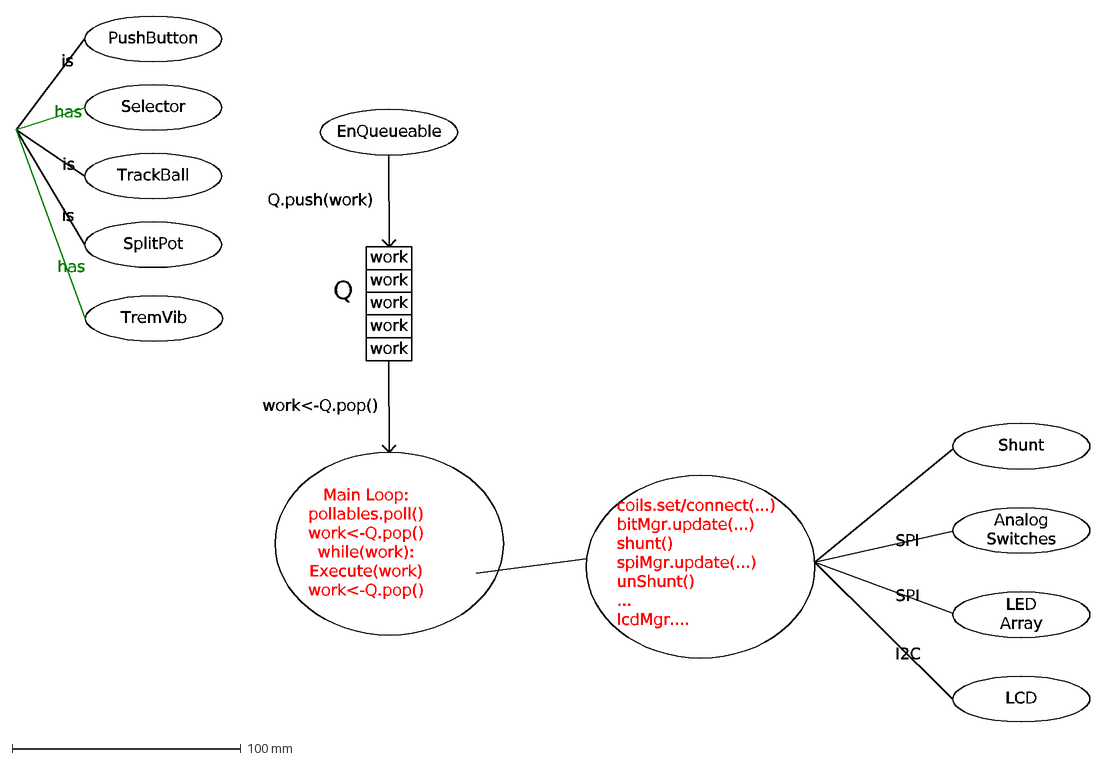
[picture p230: CAD file, 2016-10-06]
Ardu2/design/POC-3_MAX395/pyboard/V1_WithHMI/PyHMI/Data/PyGuitar Architecture.dxf
EnQueueable
Q.push(work)
work<-Q.pop()
work
Q
Main Loop: pollables.poll() work<-Q.pop() while(work): Execute(work) work<-Q.pop()
coils.set/connect(...) bitMgr.update(...) shunt() spiMgr.update(...) unShunt() ... lcdMgr....
Shunt
Analog Switches
LED Array
LCD
SPI
I2C
PushButton
Selector
TrackBall
SplitPot
has
is
TremVib
