gratefulfrog/ArduGuitar/Ardu3/Concept/joysticks/psp 1000 annotated.dxf

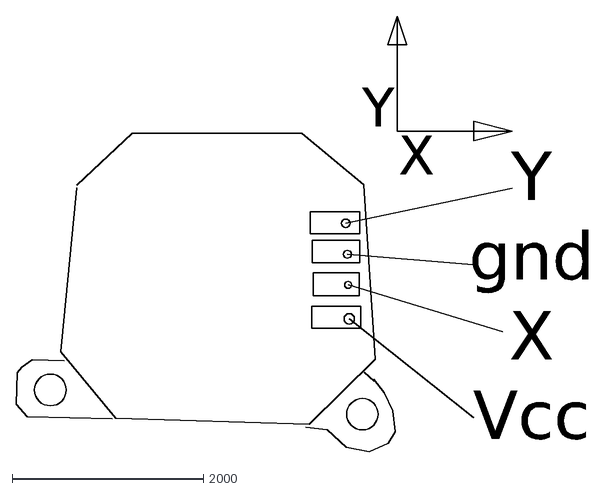
[picture p231: CAD file, 2018-02-15]
Ardu3/Concept/joysticks/psp 1000 annotated.dxf
Y gnd X Vcc
Y
X
