gratefulfrog/ArduGuitar/arduino/Layouts/ArduStomp/EnclosureDesign/3D/Arcs Model/Arcs19_3mx2m.dxf

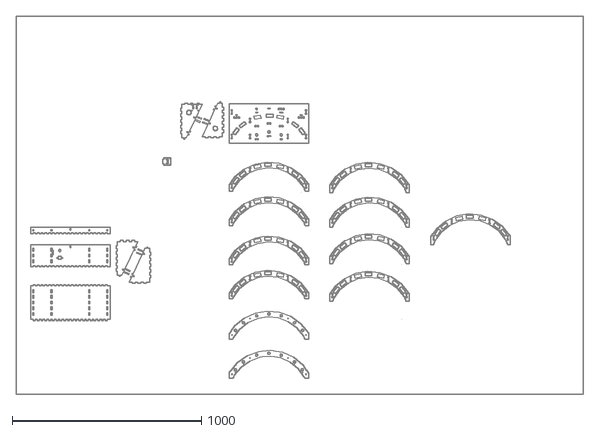
[picture p232: CAD file, 2013-12-15]
arduino/Layouts/ArduStomp/EnclosureDesign/3D/Arcs Model/Arcs19_3mx2m.dxf
3000.0 x 2000.0
