gratefulfrog/ArduGuitar/arduino/Layouts/ArduStomp/EnclosureDesign/3D/Arcs Model/Kerf_0_2mm/Arcs14Kerf21lines.dxf

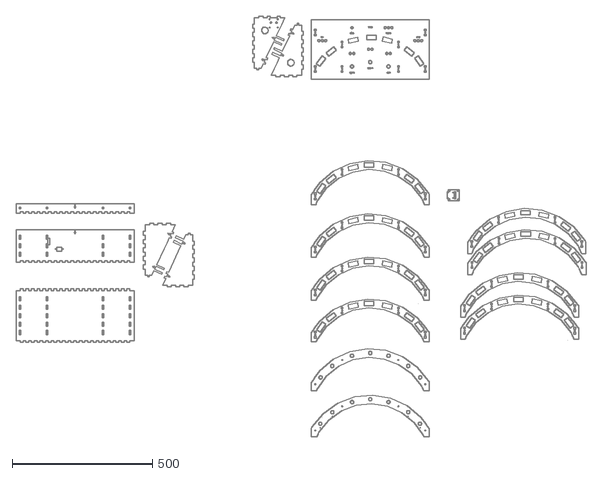
[picture p233: CAD file, 2013-12-15]
arduino/Layouts/ArduStomp/EnclosureDesign/3D/Arcs Model/Kerf_0_2mm/Arcs14Kerf21lines.dxf
2028.9 x 1496.9
