gratefulfrog/ArduGuitar/arduino/Layouts/ArduStomp/EnclosureDesign/3D/FabTestModels/FabTestKerf01_00_export_0.dxf

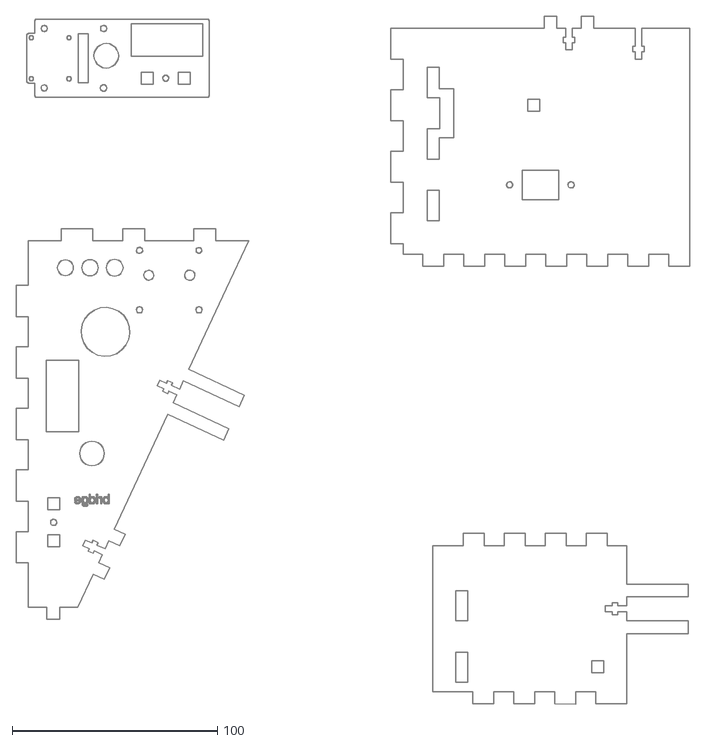
[picture p234: CAD file, 2013-12-15]
arduino/Layouts/ArduStomp/EnclosureDesign/3D/FabTestModels/FabTestKerf01_00_export_0.dxf
328.7 x 335.6
