gratefulfrog/ArduGuitar/arduino/Layouts/ArduStomp/EnclosureDesign/3D/Misc Tests/LaserPrepTest02untitled.dxf

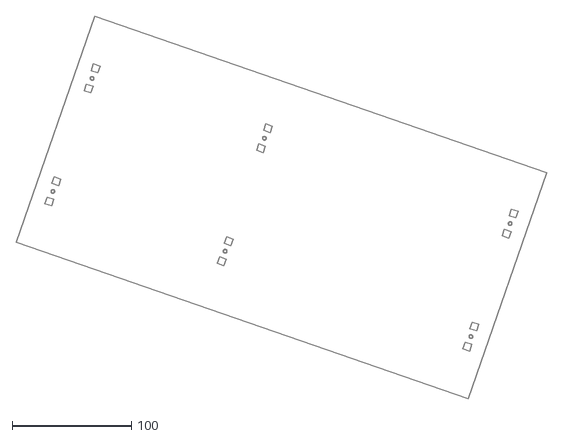
[picture p235: CAD file, 2013-12-01]
arduino/Layouts/ArduStomp/EnclosureDesign/3D/Misc Tests/LaserPrepTest02untitled.dxf
443.7 x 320.4
