gratefulfrog/ArduGuitar/Ardu2/design/POC-2/Carvin Integration/Carvin/MyCarvin/PushButton.stl

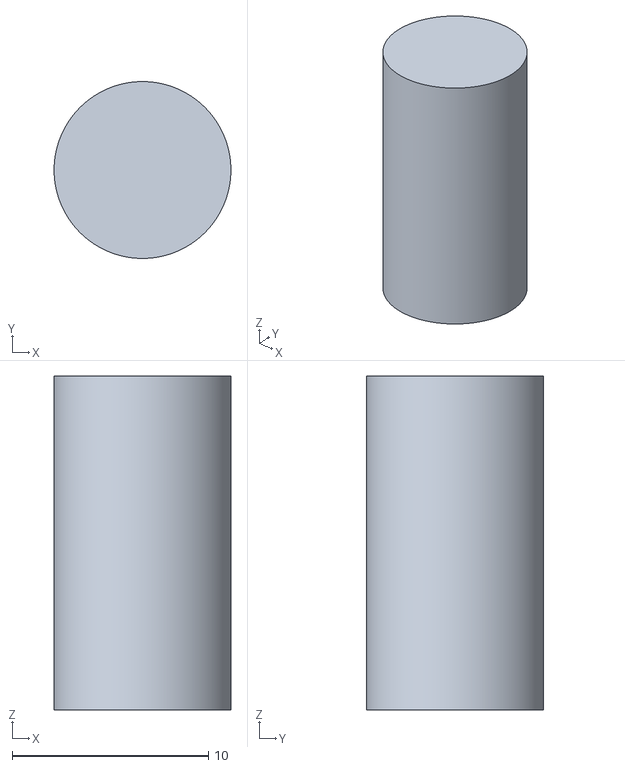
[picture p236: CAD file, 2015-04-13]
Ardu2/design/POC-2/Carvin Integration/Carvin/MyCarvin/PushButton.stl
9.00 x 9.00 x 17.0
