gratefulfrog/ArduGuitar/Ardu2/design/POC-3_MAX395/HMI/#HMI_03_Guitar_3_Cut.dxf

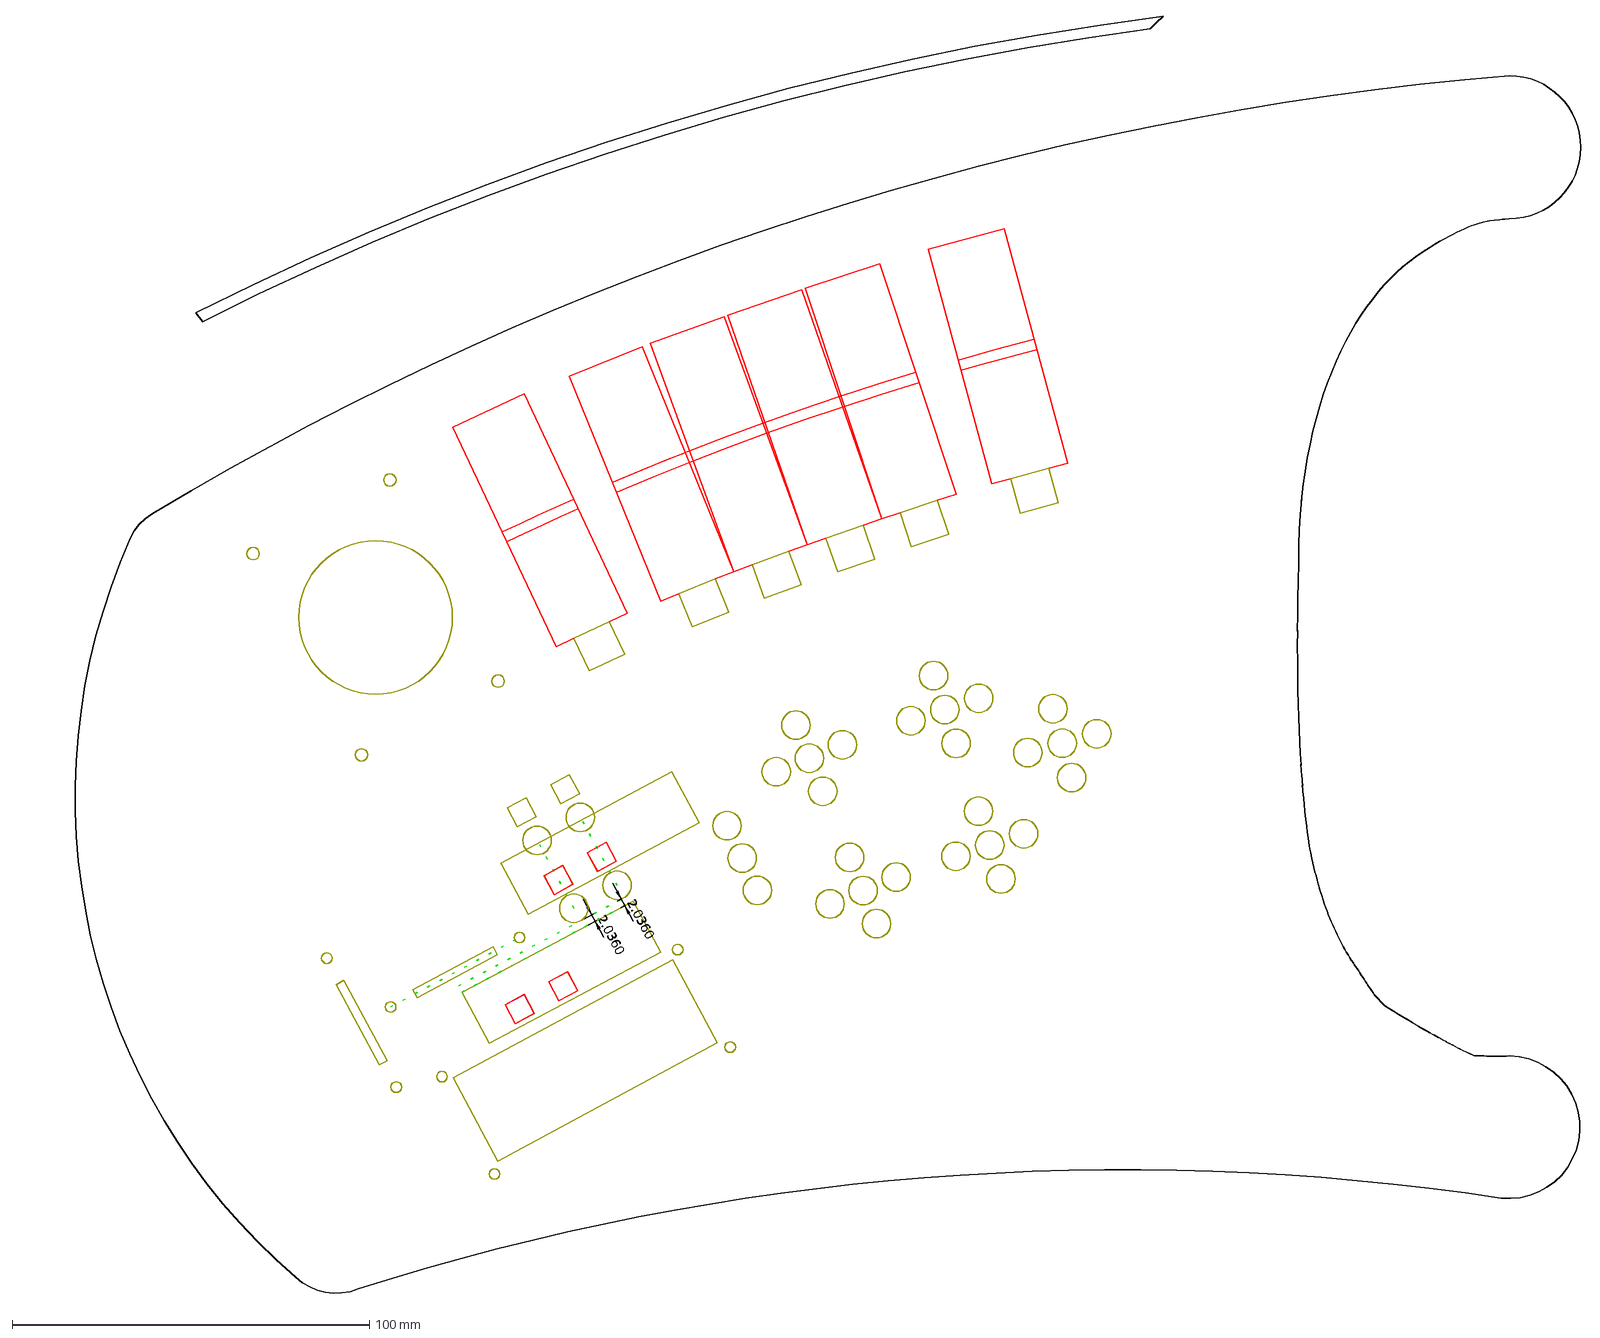
[picture p237: CAD file, 2017-06-04]
Ardu2/design/POC-3_MAX395/HMI/#HMI_03_Guitar_3_Cut.dxf
2.0360
