gratefulfrog/ArduGuitar/Ardu2/design/POC-3_MAX395/HMI/KicadProjects/2PB with Headers/DXF/#2PB with Headers-B.Cu.dxf

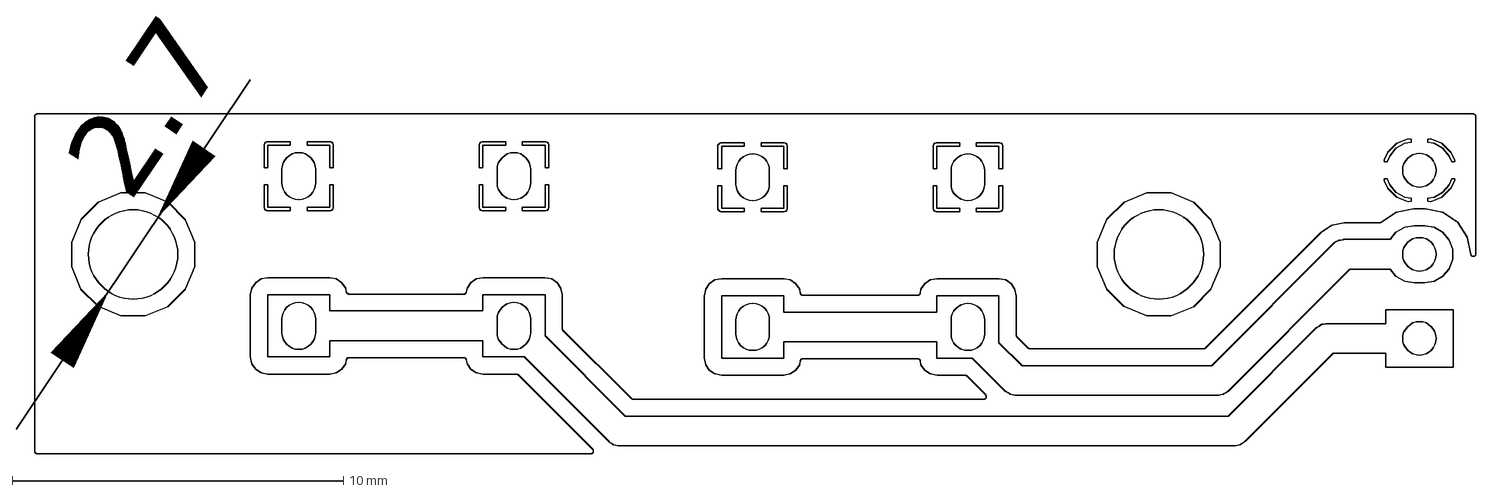
[picture p238: CAD file, 2016-01-25]
Ardu2/design/POC-3_MAX395/HMI/KicadProjects/2PB with Headers/DXF/#2PB with Headers-B.Cu.dxf
2.7
