gratefulfrog/ArduGuitar/Ardu2/design/POC-3_MAX395/HMI/KicadProjects/Single HW Debounce PBs circuit /PCB.dxf

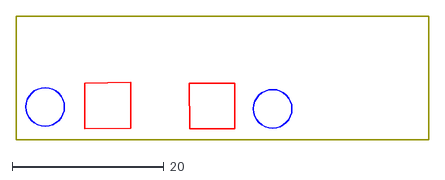
[picture p239: CAD file, 2016-01-24]
Ardu2/design/POC-3_MAX395/HMI/KicadProjects/Single HW Debounce PBs circuit /PCB.dxf
54.4 x 16.3
