gratefulfrog/ArduGuitar/Ardu2/design/POC-3_MAX395/HMI/PCB Standoffs/High_Standoff.stl

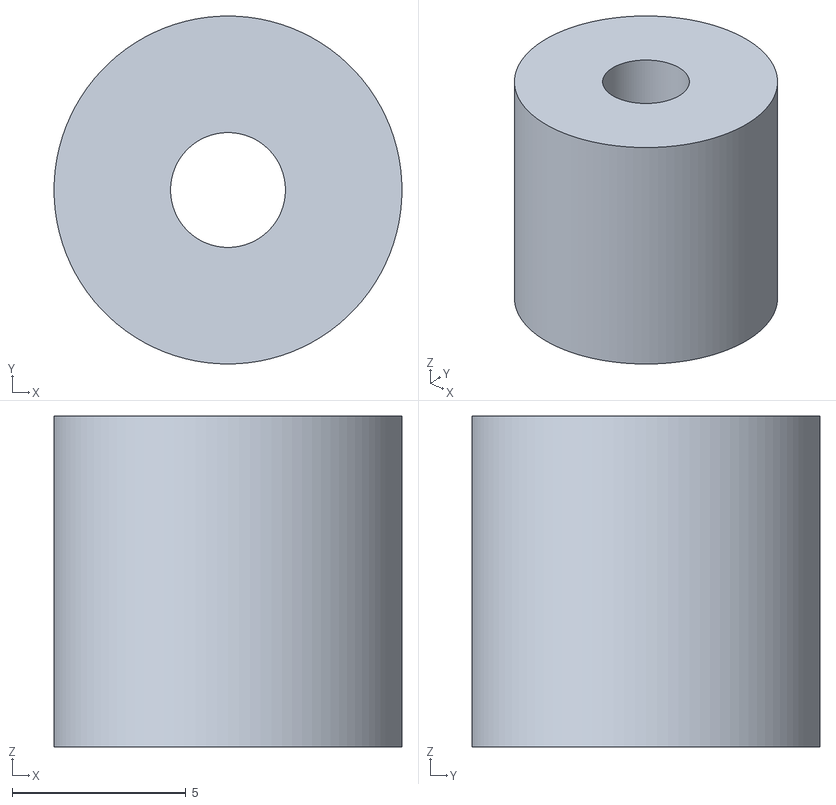
[picture p241: CAD file, 2016-11-14]
Ardu2/design/POC-3_MAX395/HMI/PCB Standoffs/High_Standoff.stl
10.0 x 10.0 x 9.50
