gratefulfrog/ArduGuitar/Ardu2/design/POC-3_MAX395/pyboard/V1_WithHMI/PyHMI/Data/Asynch Q Mecahnics.dxf

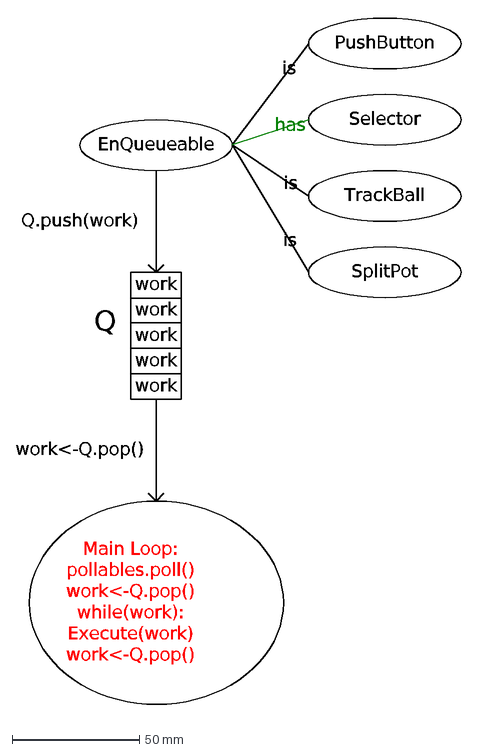
[picture p242: CAD file, 2016-05-22]
Ardu2/design/POC-3_MAX395/pyboard/V1_WithHMI/PyHMI/Data/Asynch Q Mecahnics.dxf
EnQueueable
PushButton
Selector
TrackBall
SplitPot
has
is
Q.push(work)
work<-Q.pop()
work
Q
Main Loop: pollables.poll() work<-Q.pop() while(work): Execute(work) work<-Q.pop()
