gratefulfrog/ArduGuitar/arduino/Layouts/ArduStomp/EnclosureDesign/2D/BoxTest/BoxTest2kerf_0_1_2010.dxf

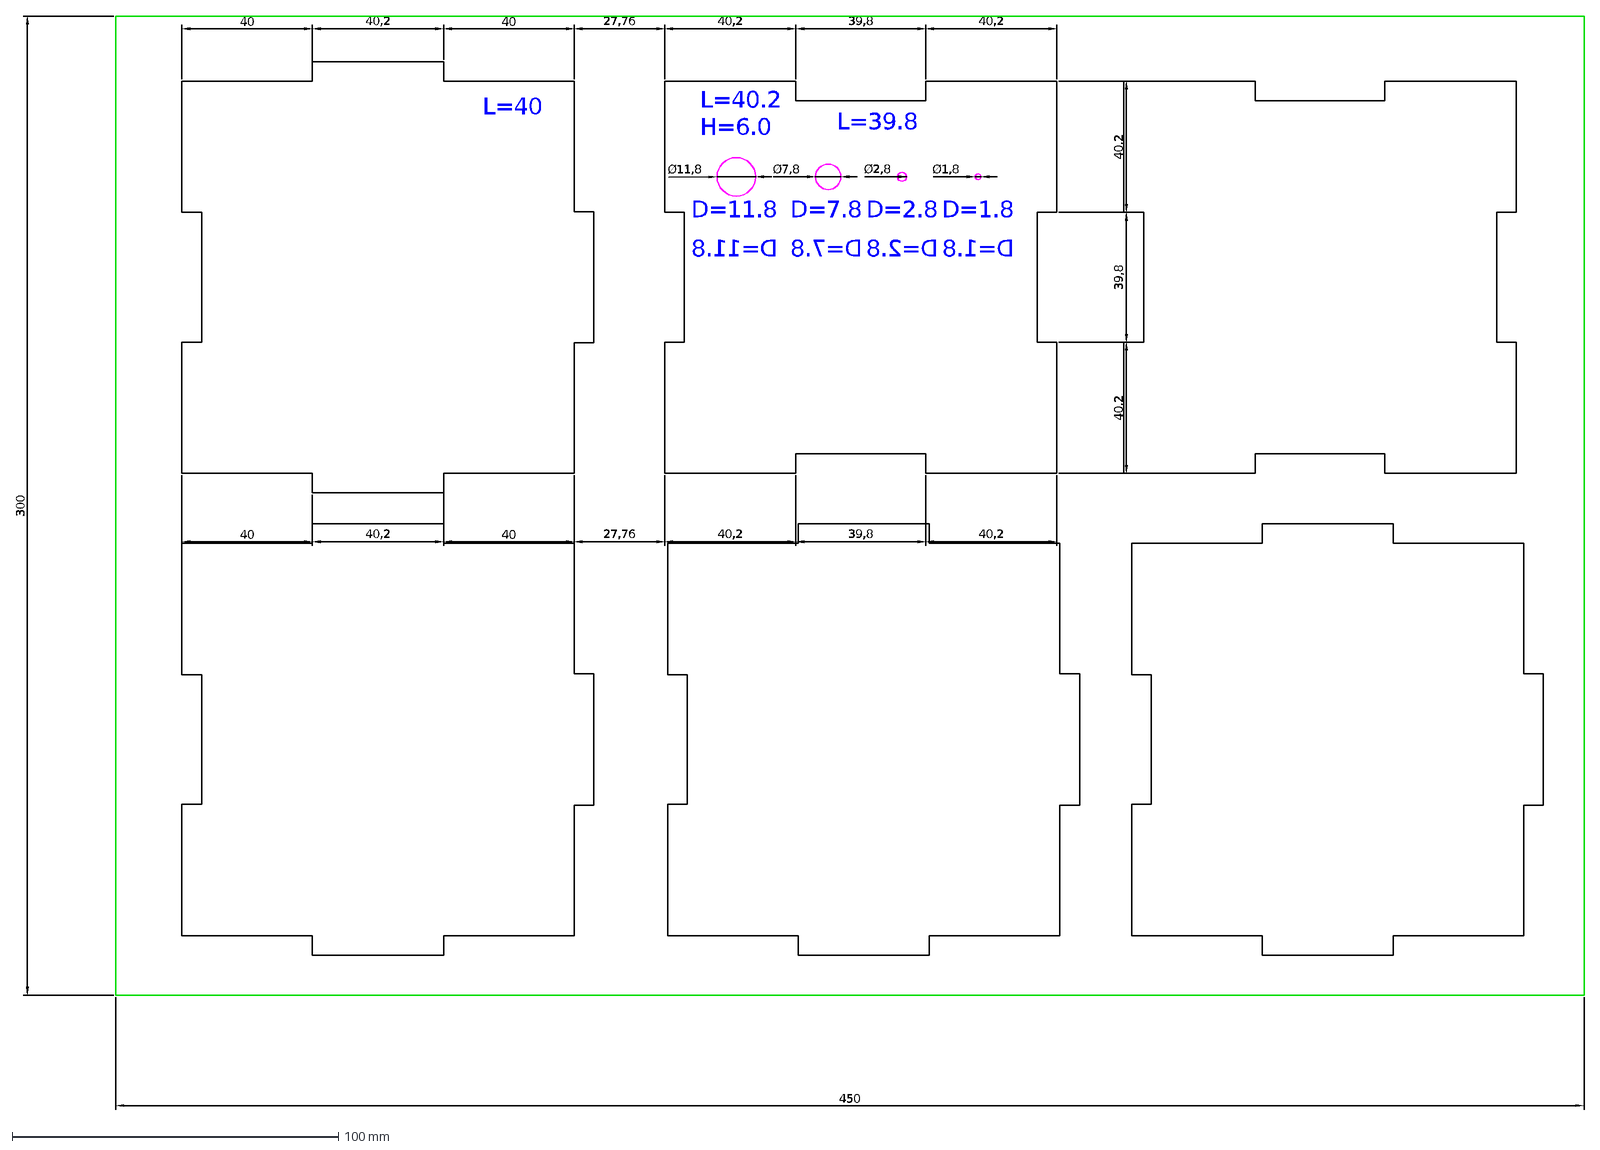
[picture p243: CAD file, 2013-12-22]
arduino/Layouts/ArduStomp/EnclosureDesign/2D/BoxTest/BoxTest2kerf_0_1_2010.dxf
40
40,2
27,76
39,8
D=11.8
D=2.8
D=1.8
D=7.8
Ø11,8
Ø7,8
Ø2,8
Ø1,8
L=40.2
H=6.0
L=39.8
L=40
300
450
