gratefulfrog/ArduGuitar/arduino/Layouts/ArduStomp/EnclosureDesign/3D/Arcs Model/Arcs19SomeKerfs.dxf

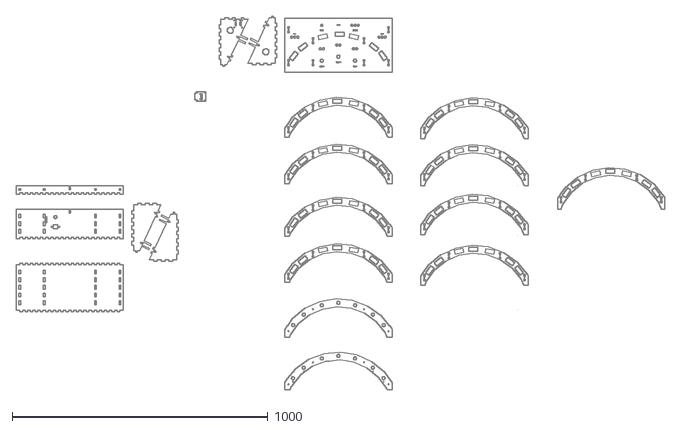
[picture p244: CAD file, 2013-12-15]
arduino/Layouts/ArduStomp/EnclosureDesign/3D/Arcs Model/Arcs19SomeKerfs.dxf
2537.9 x 1463.0
