gratefulfrog/ArduGuitar/arduino/Layouts/ArduStomp/EnclosureDesign/3D/Arcs Model/Kerf_0_2mm/Arcs14Kerf21MeshExport.dxf

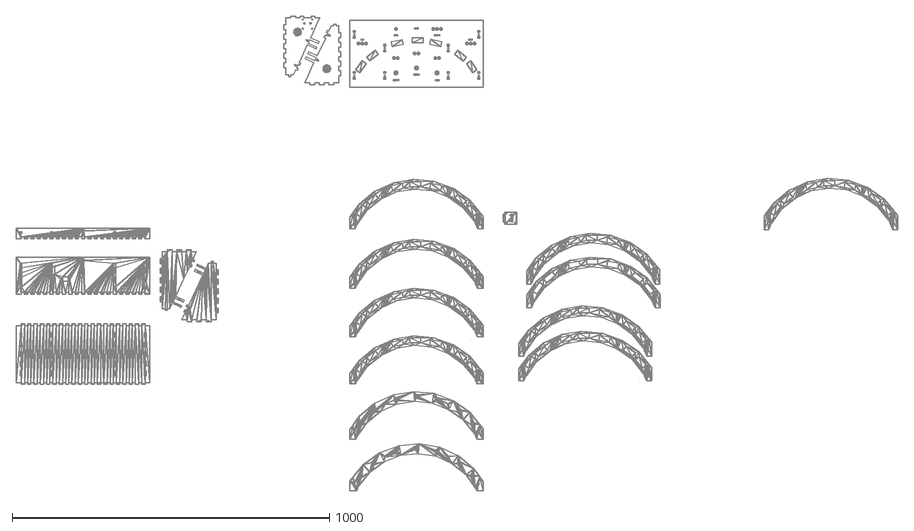
[picture p245: CAD file, 2013-12-04]
arduino/Layouts/ArduStomp/EnclosureDesign/3D/Arcs Model/Kerf_0_2mm/Arcs14Kerf21MeshExport.dxf
2777.1 x 1496.9
