gratefulfrog/ArduGuitar/arduino/Layouts/ArduStomp/EnclosureDesign/3D/FabTestModels/FabTestKerf01_02.dxf

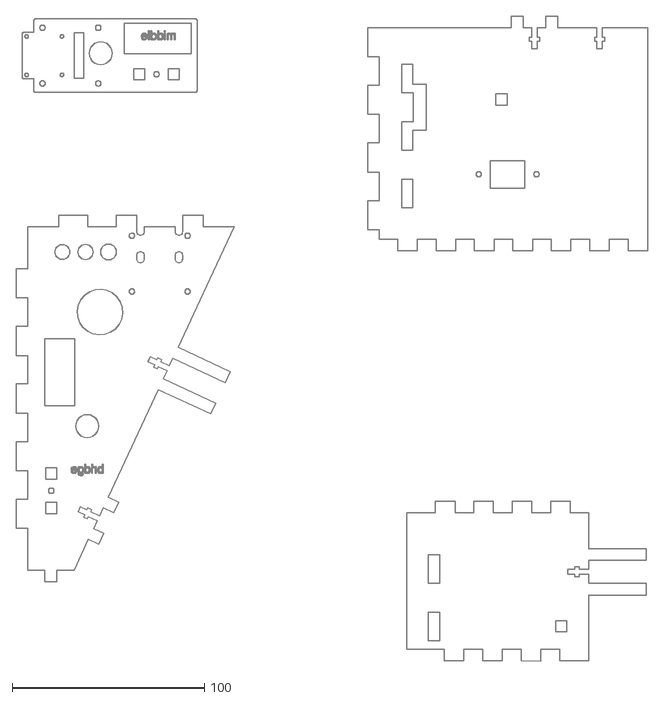
[picture p246: CAD file, 2013-12-15]
arduino/Layouts/ArduStomp/EnclosureDesign/3D/FabTestModels/FabTestKerf01_02.dxf
328.7 x 335.6
