gratefulfrog/ArduGuitar/Ardu2/design/POC-3_MAX395/HMI/HMI_04_Guitar_Bottom_Cut.dxf

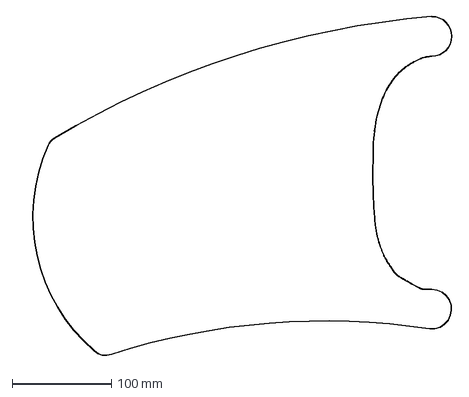
[picture p247: CAD file, 2017-06-04]
Ardu2/design/POC-3_MAX395/HMI/HMI_04_Guitar_Bottom_Cut.dxf
439.2 x 342.3 mm
