gratefulfrog/ArduGuitar/Ardu2/design/POC-3_MAX395/HMI/KicadProjects/2PB with Headers/DXF/2PB with Headers-Dwgs.User.dxf

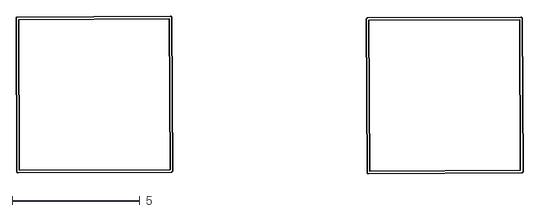
[picture p248: CAD file, 2016-01-25]
Ardu2/design/POC-3_MAX395/HMI/KicadProjects/2PB with Headers/DXF/2PB with Headers-Dwgs.User.dxf
19.9 x 6.16
