gratefulfrog/ArduGuitar/Ardu2/design/POC-3_MAX395/HMI/MountingBlocks/triJig.stl

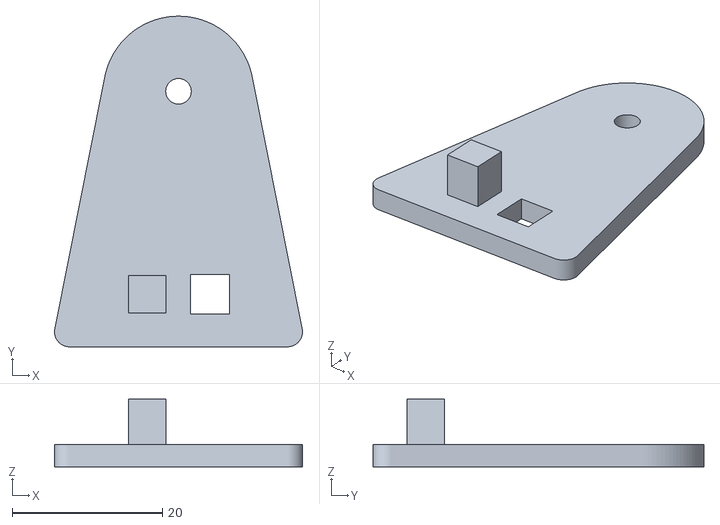
[picture p249: CAD file, 2017-06-06]
Ardu2/design/POC-3_MAX395/HMI/MountingBlocks/triJig.stl
33.0 x 44.0 x 9.00
