gratefulfrog/ArduGuitar/arduino/Layouts/ArduStomp/EnclosureDesign/2D/BoxTest/BoxTest2kerf_0_125_2013.dxf

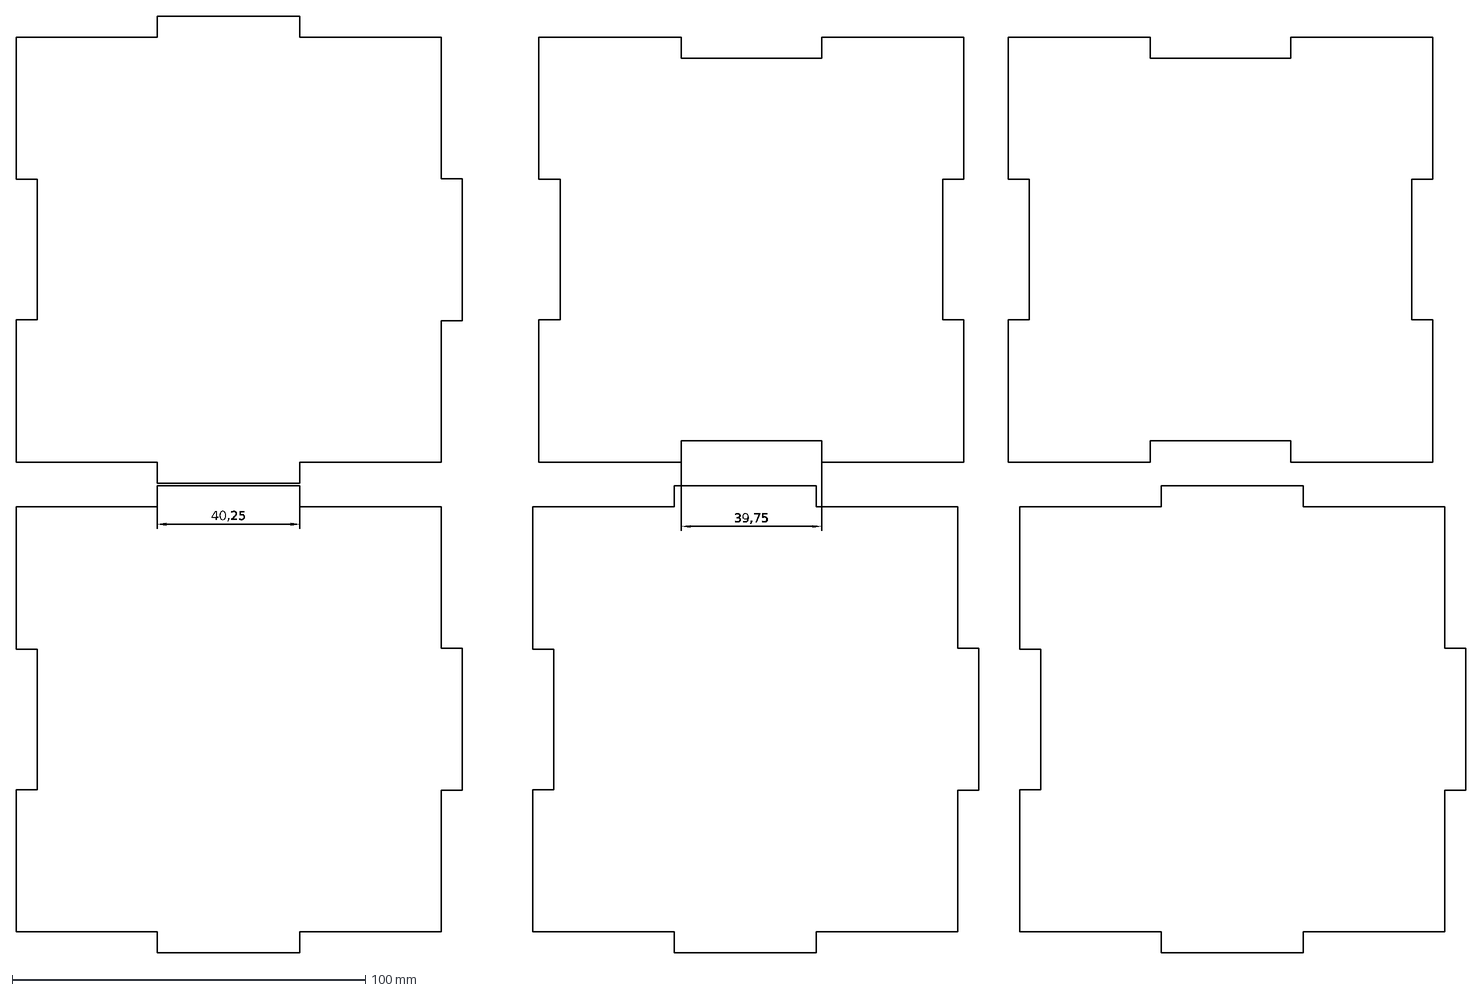
[picture p250: CAD file, 2013-12-22]
arduino/Layouts/ArduStomp/EnclosureDesign/2D/BoxTest/BoxTest2kerf_0_125_2013.dxf
40,25
39,75
