gratefulfrog/ArduGuitar/arduino/Layouts/ArduStomp/EnclosureDesign/3D/FabTestModels/FabTestKerf01_01.dxf

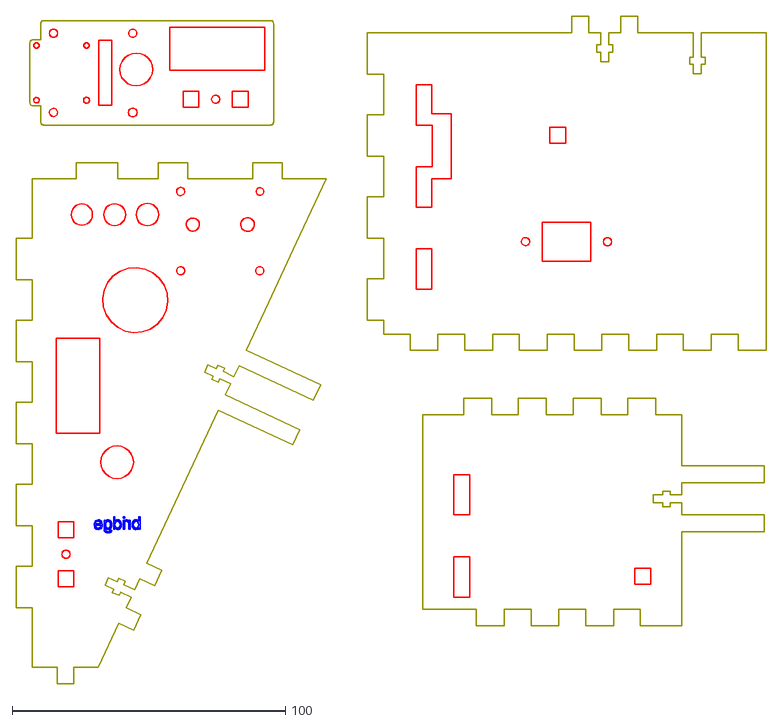
[picture p251: CAD file, 2013-12-15]
arduino/Layouts/ArduStomp/EnclosureDesign/3D/FabTestModels/FabTestKerf01_01.dxf
274.3 x 244.0
