gratefulfrog/ArduGuitar/Ardu2/design/POC-3_MAX395/HMI/HMI_05_Guitar_Top_pb_mounting_holes.dxf

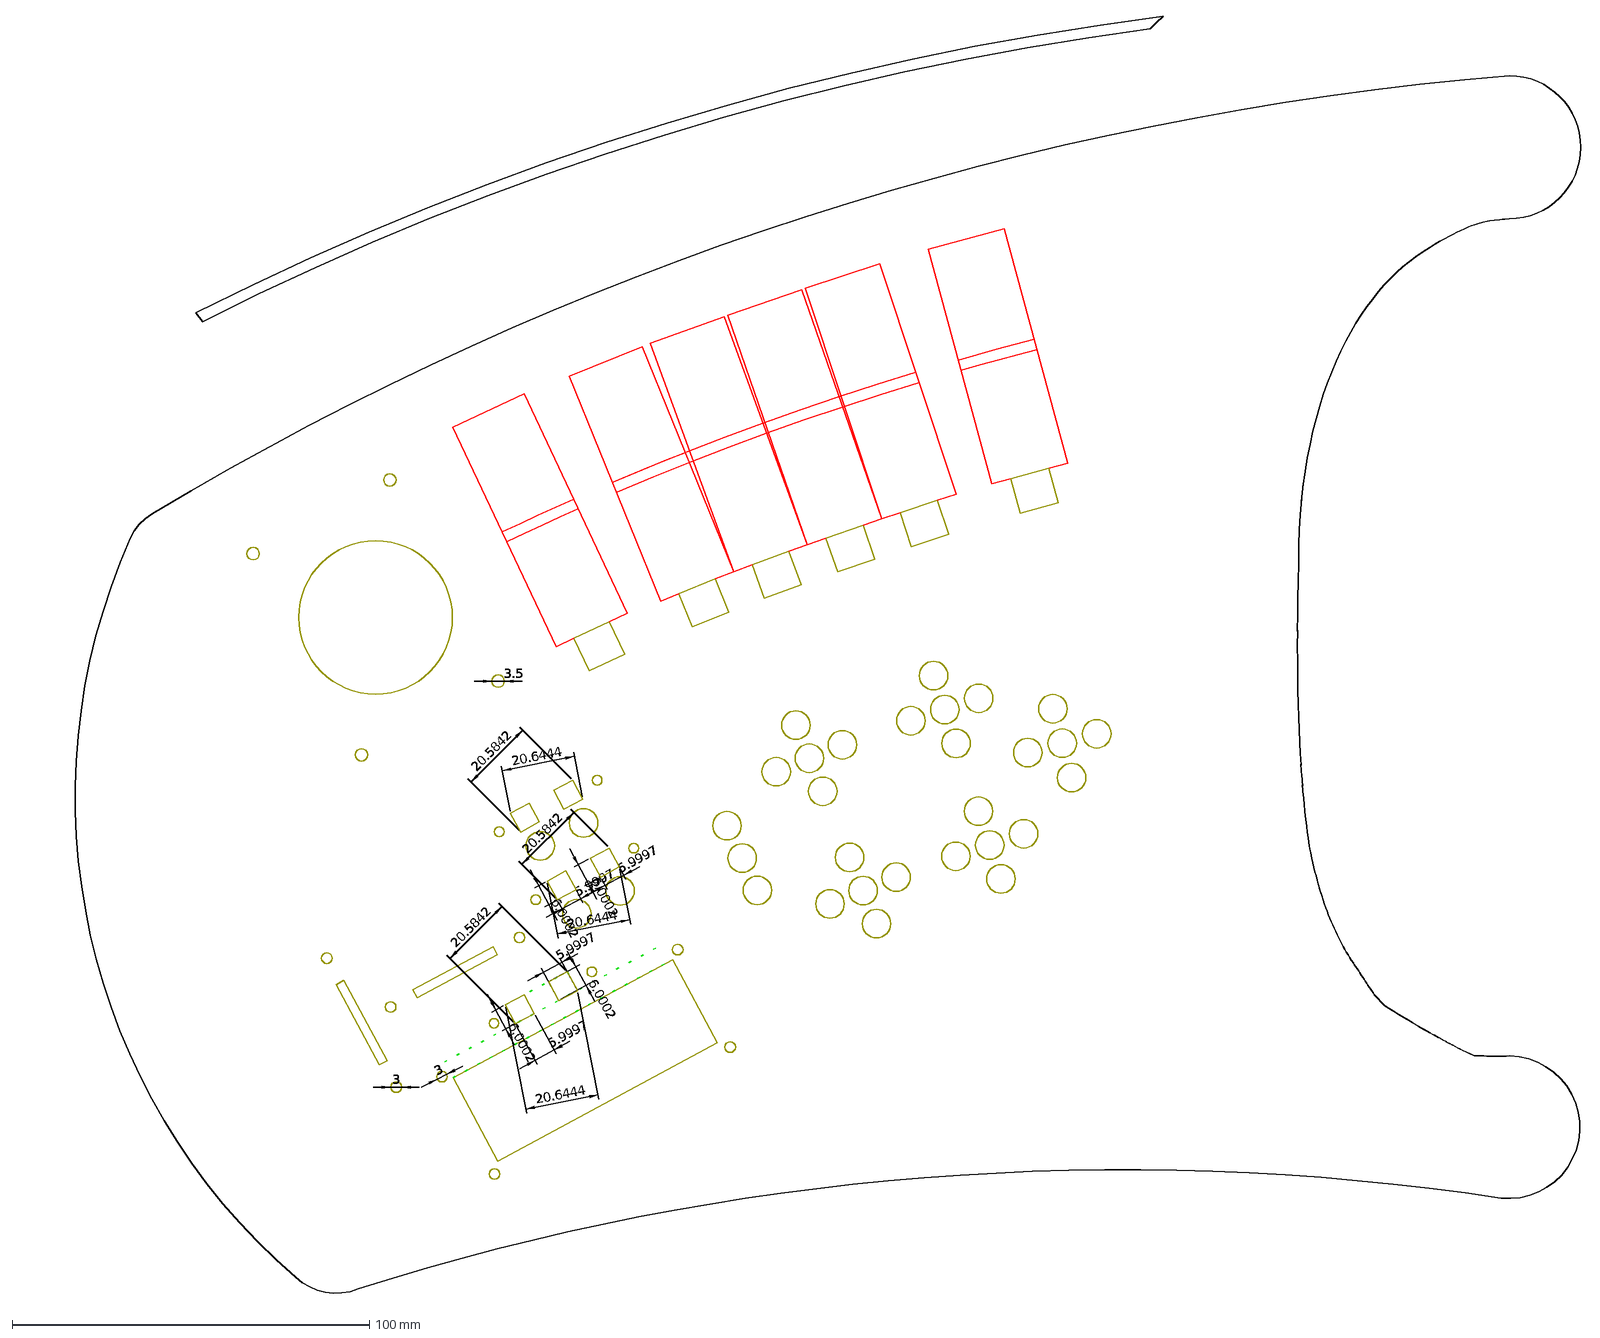
[picture p252: CAD file, 2016-04-04]
Ardu2/design/POC-3_MAX395/HMI/HMI_05_Guitar_Top_pb_mounting_holes.dxf
6.0002
5.9997
20.5842
20.6444
3.5
3
