gratefulfrog/ArduGuitar/Ardu2/design/POC-3_MAX395/HMI/MountingBlocks/drillingJig.stl

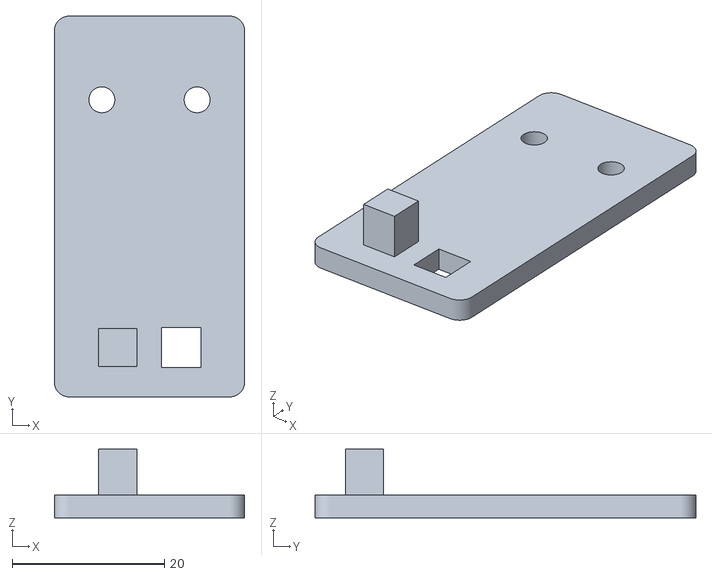
[picture p253: CAD file, 2017-06-06]
Ardu2/design/POC-3_MAX395/HMI/MountingBlocks/drillingJig.stl
25.0 x 50.0 x 9.00
