gratefulfrog/ArduGuitar/Ardu2/design/POC-3_MAX395/HMI/MountingBlocks/ovalPlate.stl

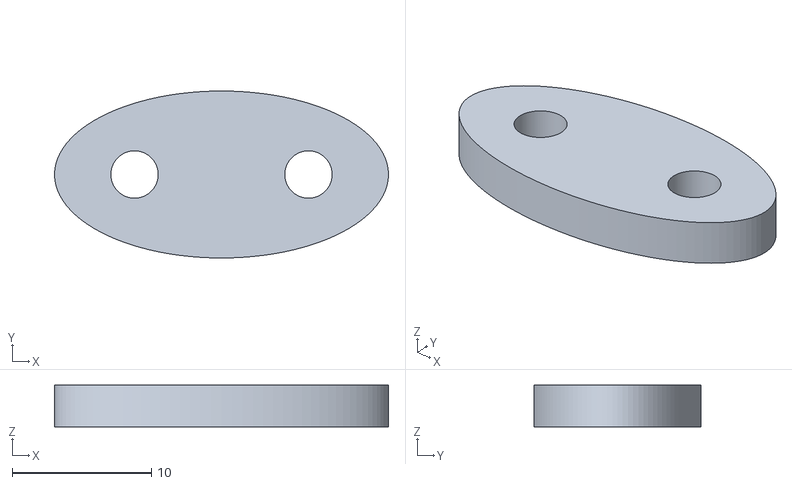
[picture p254: CAD file, 2017-06-06]
Ardu2/design/POC-3_MAX395/HMI/MountingBlocks/ovalPlate.stl
24.0 x 12.0 x 3.00
