gratefulfrog/ArduGuitar/Ardu2/design/POC-3_MAX395/HMI/PBx2.dxf

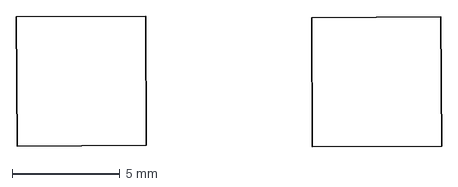
[picture p255: CAD file, 2016-01-25]
Ardu2/design/POC-3_MAX395/HMI/PBx2.dxf
19.8 x 6.06 mm
