gratefulfrog/ArduGuitar/arduino/Layouts/ArduStomp/EnclosureDesign/3D/FabTestModels/FabTestKerf01_02_ToCut.dxf

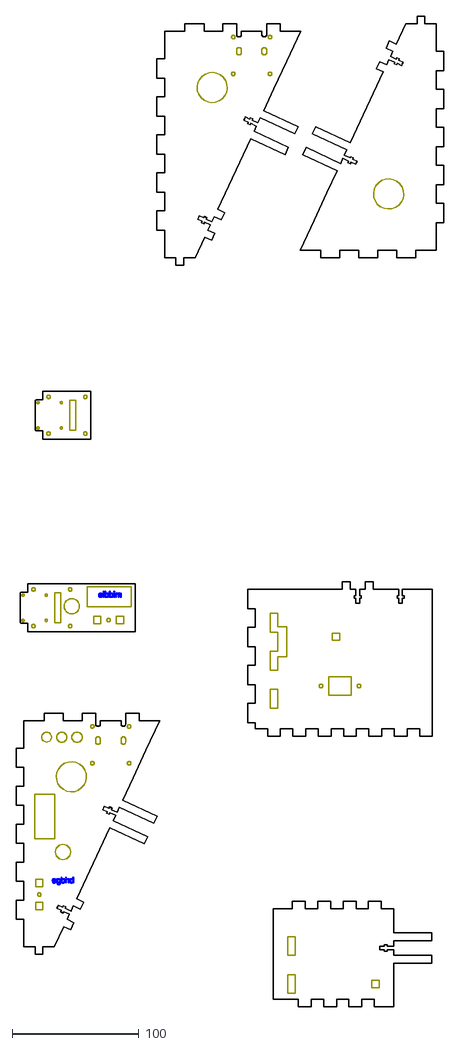
[picture p256: CAD file, 2013-12-15]
arduino/Layouts/ArduStomp/EnclosureDesign/3D/FabTestModels/FabTestKerf01_02_ToCut.dxf
337.7 x 781.9
