gratefulfrog/ArduGuitar/Ardu2/design/POC-3_MAX395/HMI/KicadProjects/2PB with Headers/DXF/2PB with Headers-Edge.Cuts.dxf

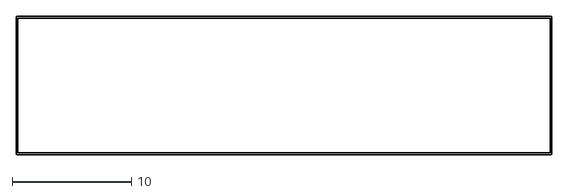
[picture p257: CAD file, 2016-01-25]
Ardu2/design/POC-3_MAX395/HMI/KicadProjects/2PB with Headers/DXF/2PB with Headers-Edge.Cuts.dxf
44.9 x 11.6
