gratefulfrog/ArduGuitar/Ardu2/design/POC-3_MAX395/HMI/MountingBlocks/spacerColumn.stl

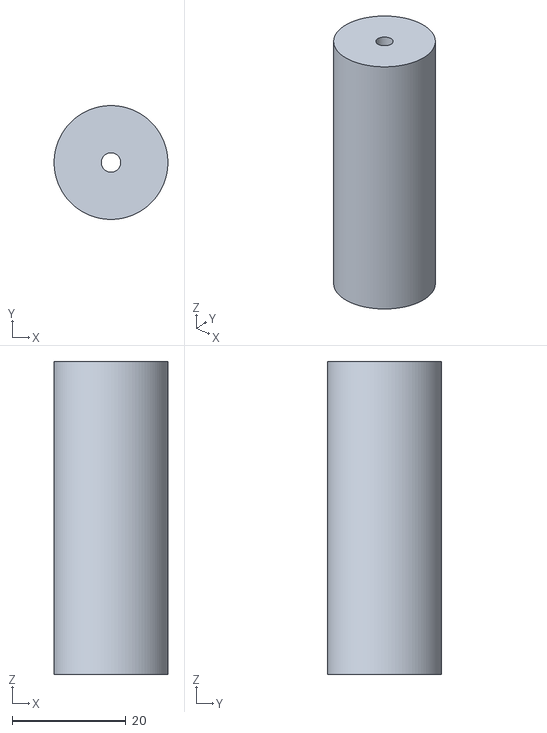
[picture p258: CAD file, 2017-06-06]
Ardu2/design/POC-3_MAX395/HMI/MountingBlocks/spacerColumn.stl
20.0 x 20.0 x 55.0
