gratefulfrog/ArduGuitar/Ardu2/design/POC-3_MAX395/HMI/pb2 pcb block.dxf

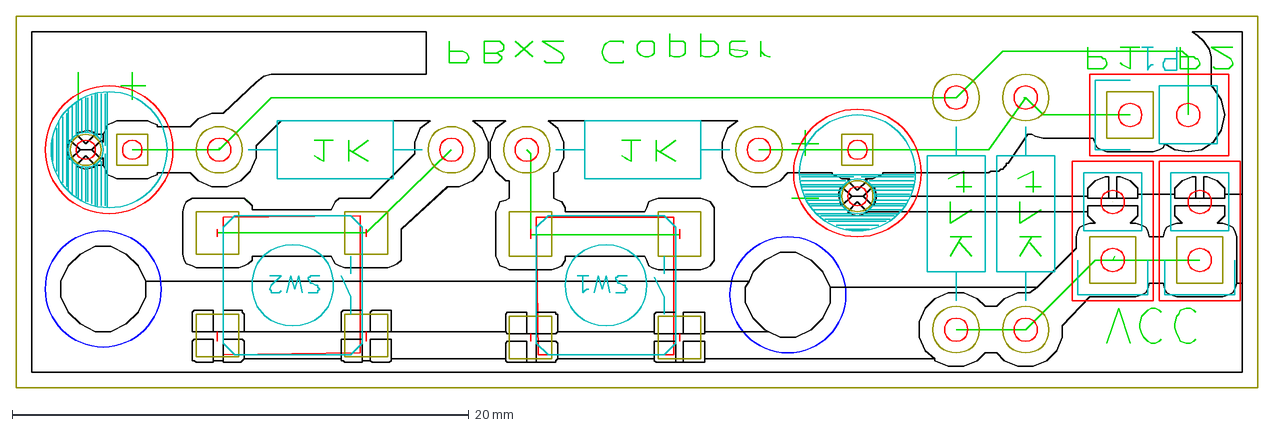
[picture p259: CAD file, 2016-01-24]
Ardu2/design/POC-3_MAX395/HMI/pb2 pcb block.dxf
54.4 x 16.3 mm
