gratefulfrog/ArduGuitar/Ardu2/design/POC-3_MAX395/HMI/2PBs_01.dxf

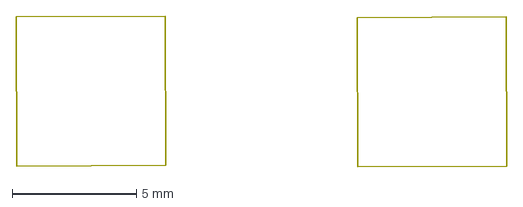
[picture p261: CAD file, 2016-01-24]
Ardu2/design/POC-3_MAX395/HMI/2PBs_01.dxf
19.8 x 6.06 mm
