gratefulfrog/ArduGuitar/Ardu2/design/POC-3_MAX395/HMI/KicadProjects/2PB with Headers/DXF/2PB with Headers-Cmts.User.dxf

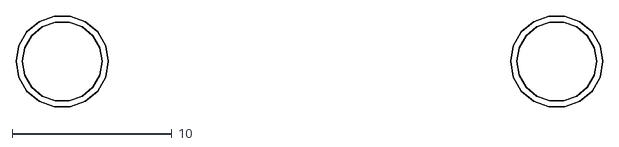
[picture p262: CAD file, 2016-01-25]
Ardu2/design/POC-3_MAX395/HMI/KicadProjects/2PB with Headers/DXF/2PB with Headers-Cmts.User.dxf
36.8 x 5.69
