gratefulfrog/ArduGuitar/Ardu2/design/POC-3_MAX395/HMI/HMI_04_Guitar_Top_Cut.dxf

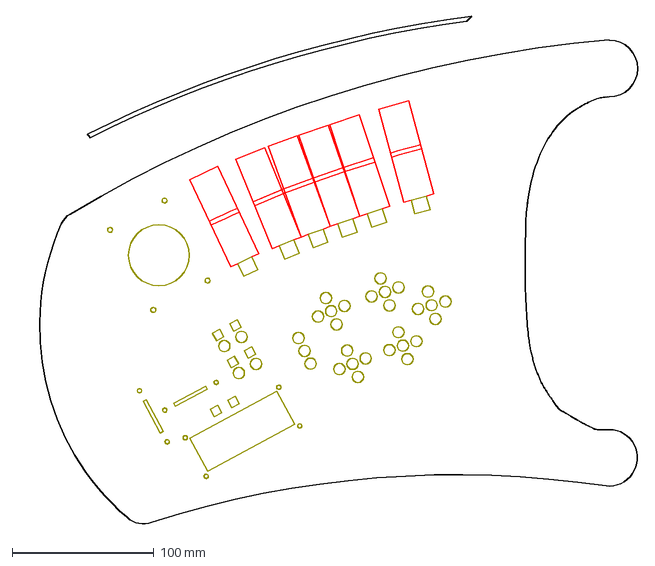
[picture p263: CAD file, 2016-01-24]
Ardu2/design/POC-3_MAX395/HMI/HMI_04_Guitar_Top_Cut.dxf
439.2 x 358.8 mm
