gratefulfrog/ArduGuitar/Ardu2/design/POC-3_MAX395/HMI/KicadProjects/2PB with Headers/DXF/2PB with Headers-drl_map.dxf

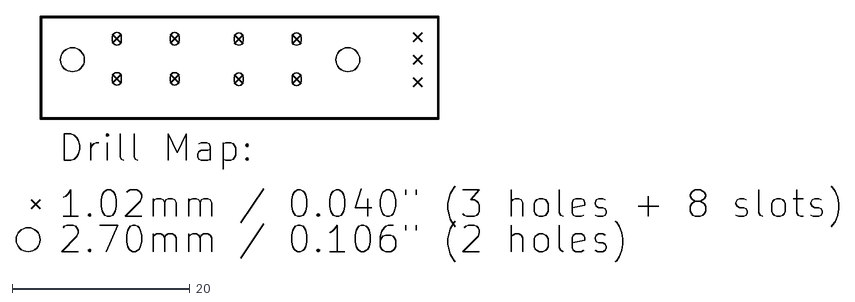
[picture p264: CAD file, 2016-01-25]
Ardu2/design/POC-3_MAX395/HMI/KicadProjects/2PB with Headers/DXF/2PB with Headers-drl_map.dxf
92.6 x 27.6
