gratefulfrog/ArduGuitar/Ardu2/design/POC-3_MAX395/HMI/MountingBlocks/roundPlate.stl

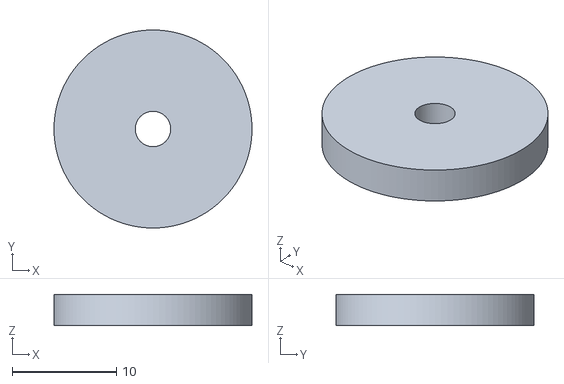
[picture p265: CAD file, 2017-06-06]
Ardu2/design/POC-3_MAX395/HMI/MountingBlocks/roundPlate.stl
19.0 x 19.0 x 3.00
