gratefulfrog/ArduGuitar/Ardu2/design/POC-3_MAX395/HMI/HMI_04_Guitar_Cut_02.dxf

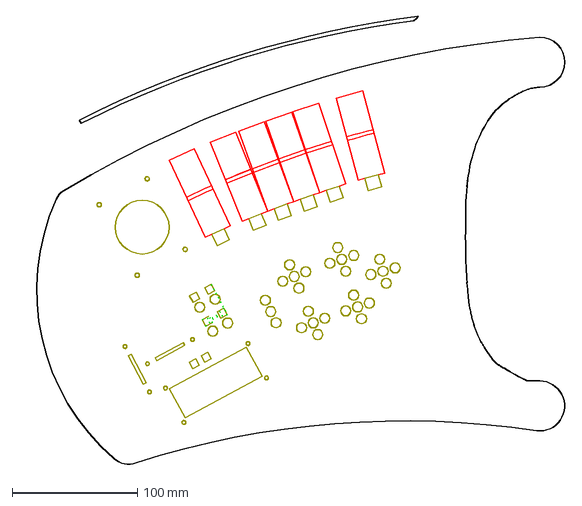
[picture p266: CAD file, 2016-01-06]
Ardu2/design/POC-3_MAX395/HMI/HMI_04_Guitar_Cut_02.dxf
439.2 x 358.8 mm
