gratefulfrog/ArduGuitar/Ardu2/design/POC-3_MAX395/HMI/MountingBlocks/LaserCutTempBlocks.dxf

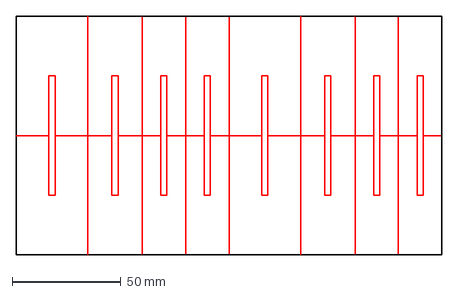
[picture p267: CAD file, 2017-06-06]
Ardu2/design/POC-3_MAX395/HMI/MountingBlocks/LaserCutTempBlocks.dxf
196.0 x 110.0 mm
