gratefulfrog/ArduGuitar/Ardu2/design/POC-3_MAX395/HMI/LEDx28_array.dxf

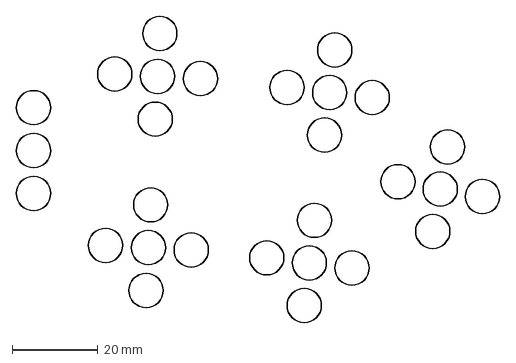
[picture p268: CAD file, 2015-11-12]
Ardu2/design/POC-3_MAX395/HMI/LEDx28_array.dxf
112.7 x 71.4 mm
