gratefulfrog/ArduGuitar/Ardu2/design/POC-3_MAX395/HMI/HMI_03_Guitar_Cut_02.dxf

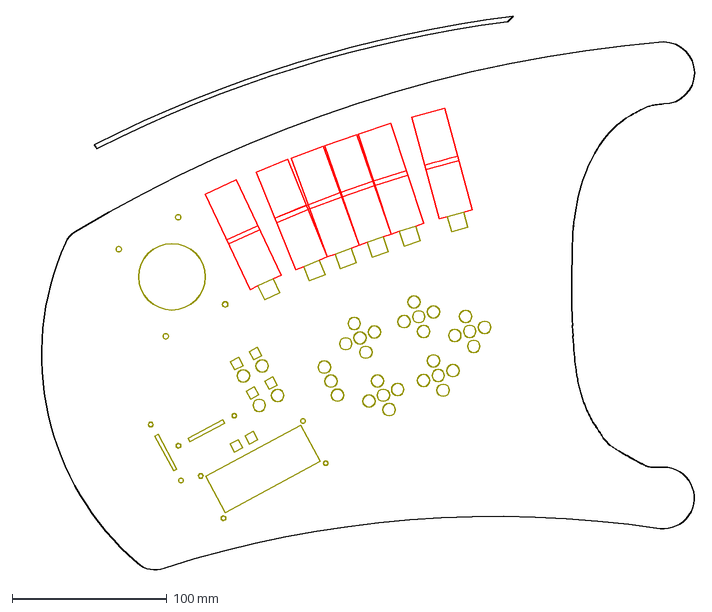
[picture p269: CAD file, 2015-11-09]
Ardu2/design/POC-3_MAX395/HMI/HMI_03_Guitar_Cut_02.dxf
439.2 x 358.8 mm
