gratefulfrog/ArduGuitar/Ardu2/design/POC-3_MAX395/HMI/BoldPlus Guitar Clean with Guides (Block).dxf

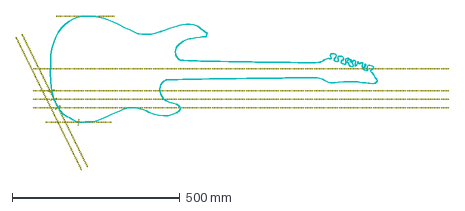
[picture p270: CAD file, 2015-11-08]
Ardu2/design/POC-3_MAX395/HMI/BoldPlus Guitar Clean with Guides (Block).dxf
1289.0 x 460.0 mm
