gratefulfrog/ArduGuitar/Ardu2/design/POC-3_MAX395/HMI/BoldPlus Guitar Clean (Block).dxf

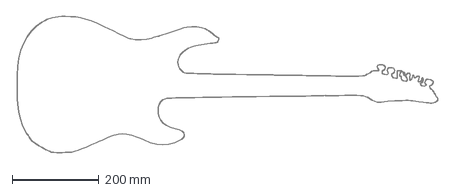
[picture p271: CAD file, 2015-11-08]
Ardu2/design/POC-3_MAX395/HMI/BoldPlus Guitar Clean (Block).dxf
976.4 x 315.1 mm
