gratefulfrog/ArduGuitar/Ardu2/design/POC-2/Carvin Integration/Carvin Wiring 00_schem.png

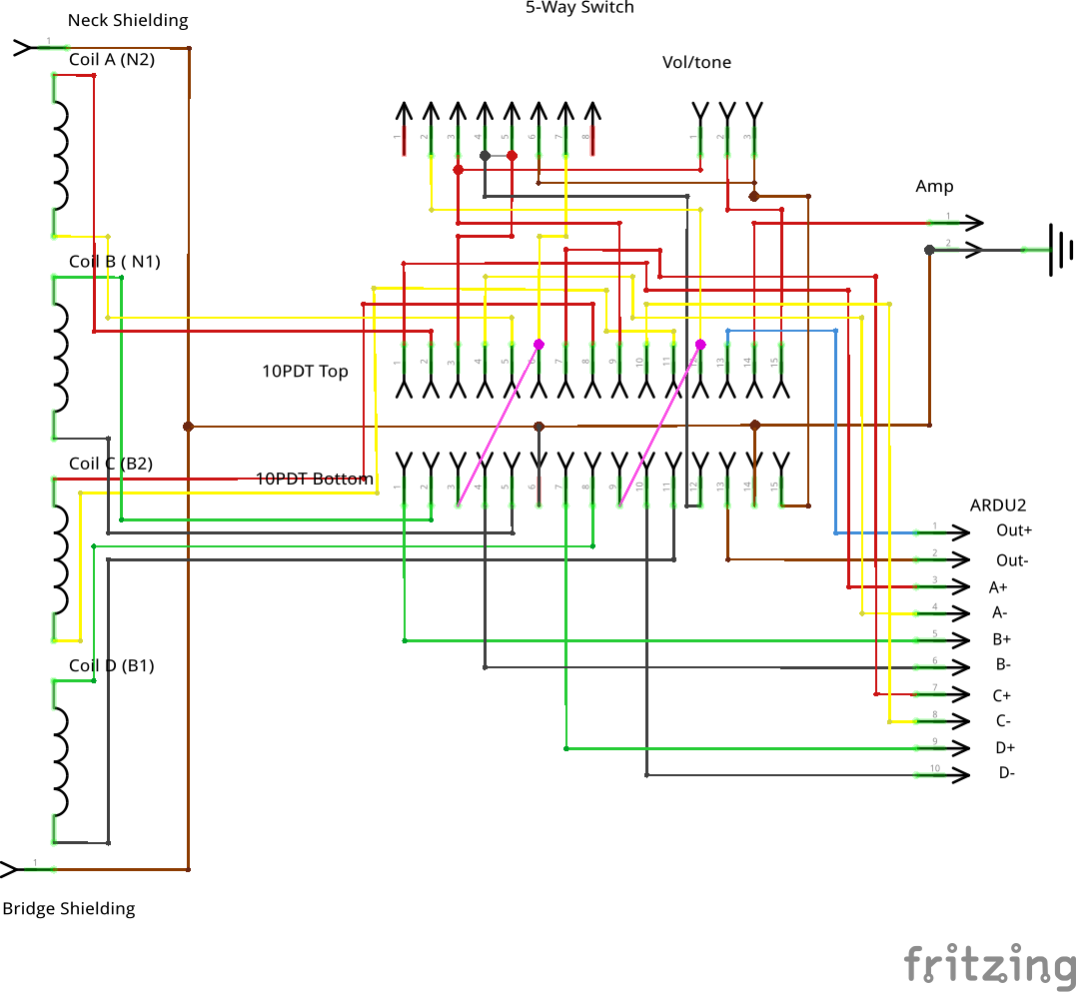
Ardu2/design/POC-2/Carvin Integration/Carvin Wiring 00_schem.png
