gratefulfrog/ArduGuitar/Ardu2/design/POC-3_MAX395/HMI/KicadProjects/PowerSupplyConnections Circuit/Prints/Board.png

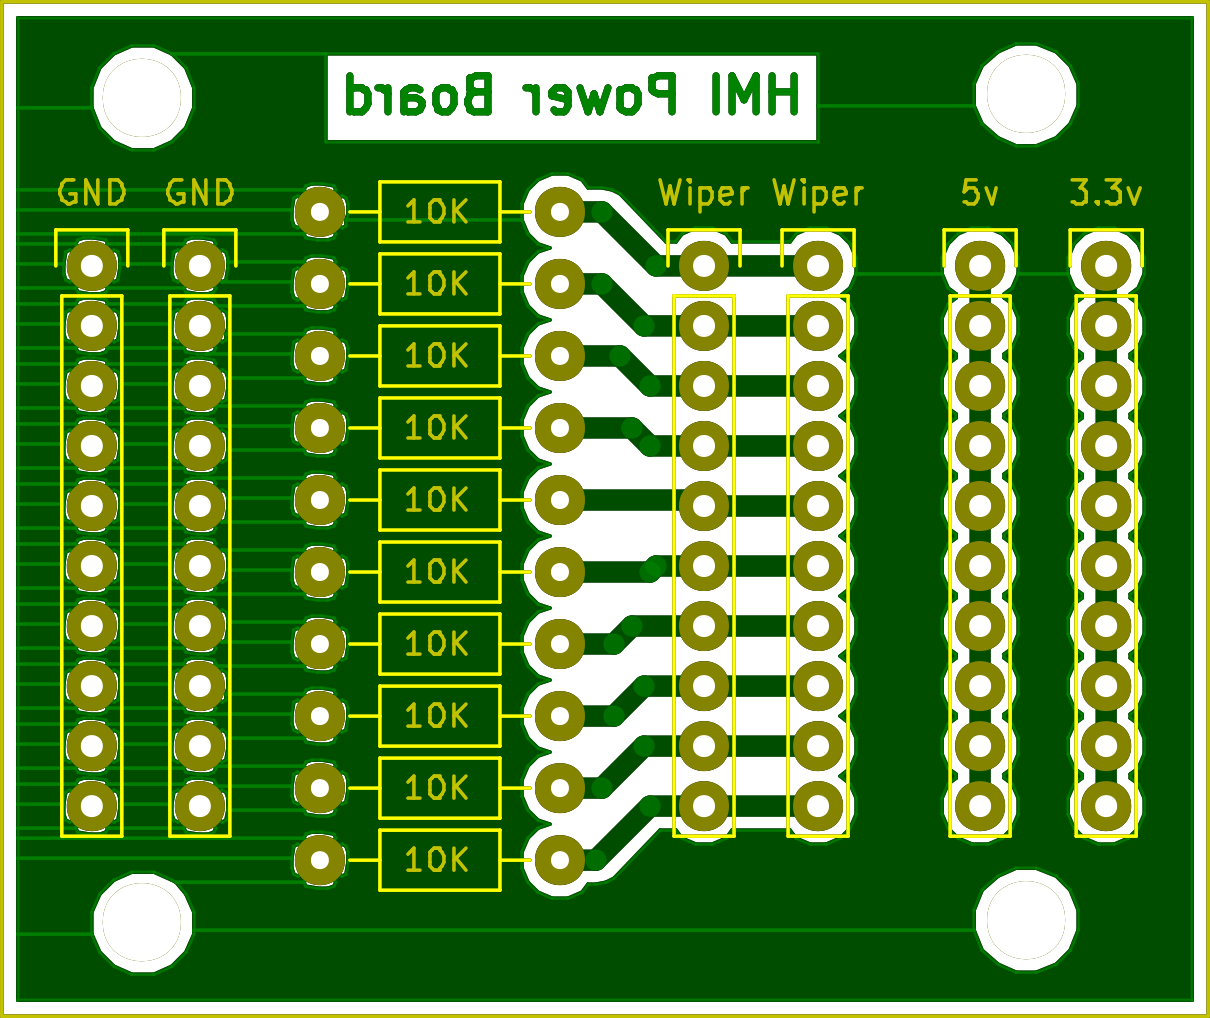
Ardu2/design/POC-3_MAX395/HMI/KicadProjects/PowerSupplyConnections Circuit/Prints/Board.png
