gratefulfrog/ArduGuitar/Ardu2/design/POC-3_MAX395/Images/10PDT Soldering.png

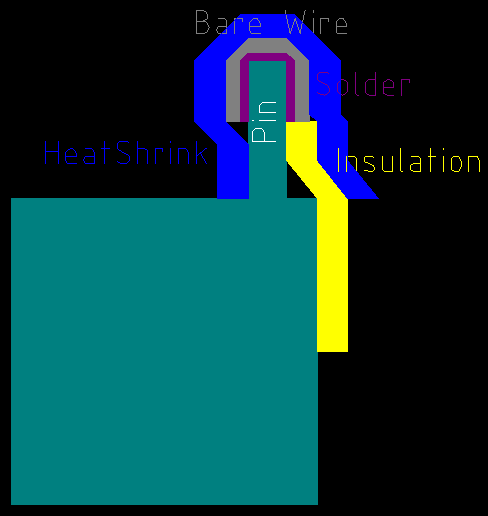
Ardu2/design/POC-3_MAX395/Images/10PDT Soldering.png
