gratefulfrog/ArduGuitar/Ardu2/design/POC-3_MAX395/Images/FinalAssembly/IMG_20171226_182632.jpg

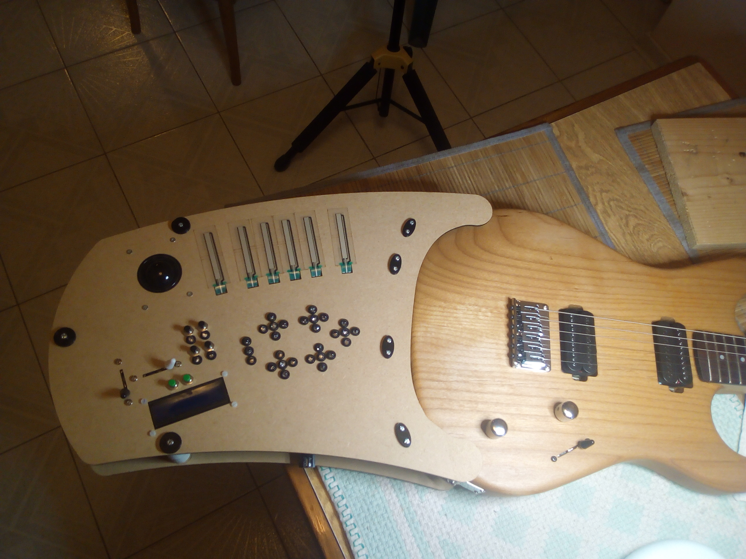
Ardu2/design/POC-3_MAX395/Images/FinalAssembly/IMG_20171226_182632.jpg
