gratefulfrog/ArduGuitar/Ardu2/design/POC-3_MAX395/KicadProjects/PickupWiring/PickupWiring.png

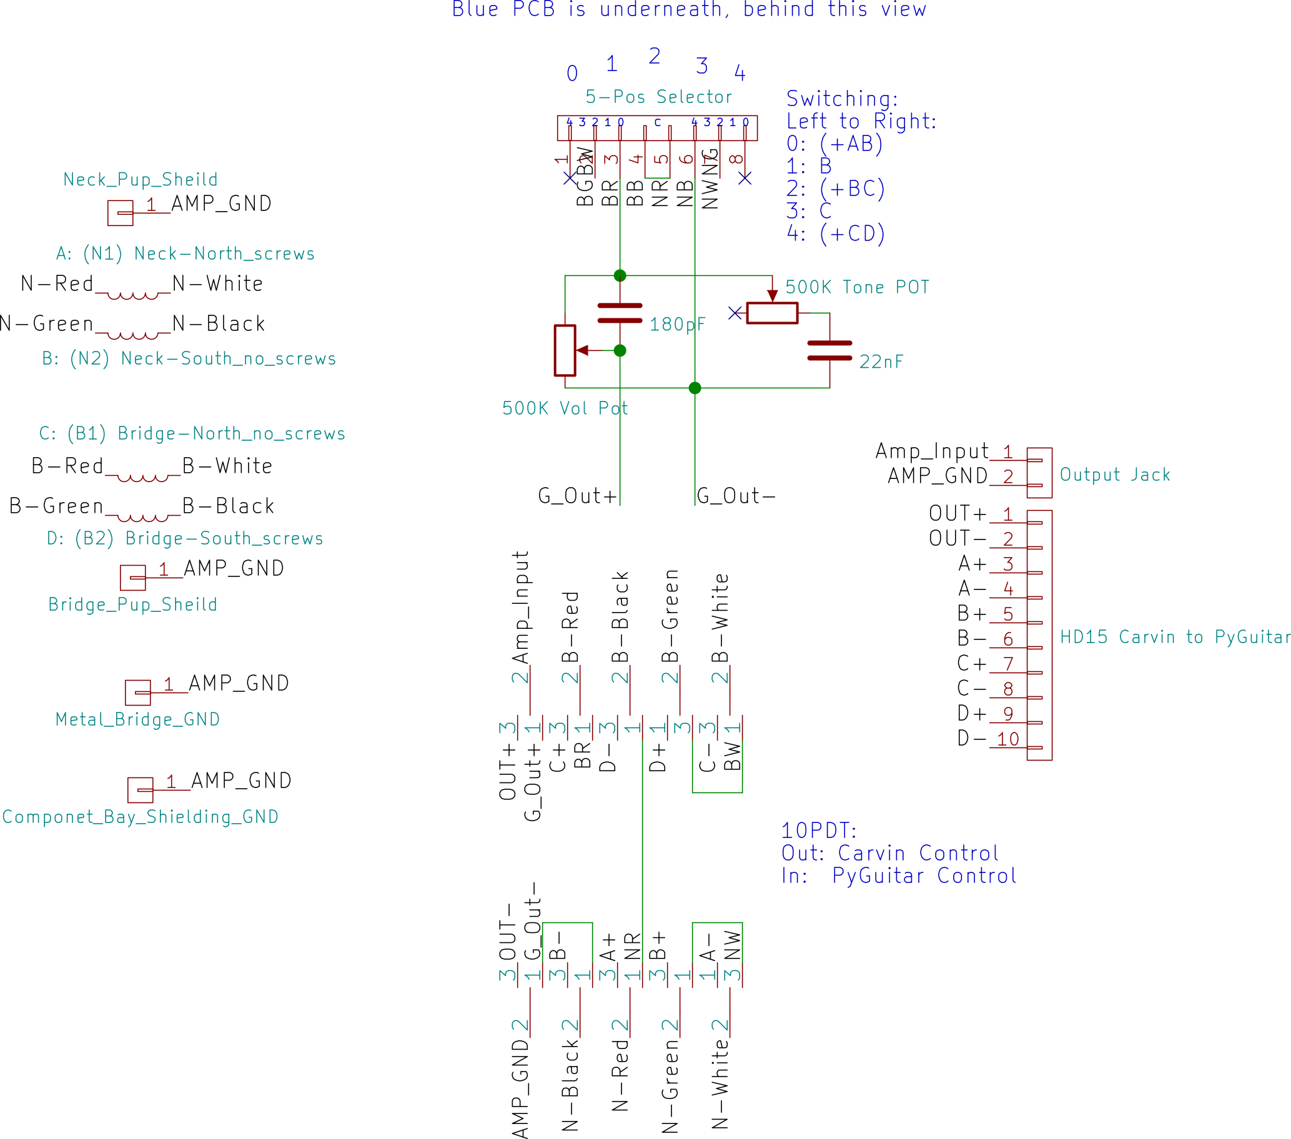
Ardu2/design/POC-3_MAX395/KicadProjects/PickupWiring/PickupWiring.png
