gratefulfrog/ArduGuitar/tests/Processing/PresetWriter/data/DataWrite-data.tsv

vol | tone | neck | middle | bNorth | bBoth
0 | 0 | 0 | 0 | 0 | 0
1 | 1 | 0 | 0 | 0 | 0
2 | 2 | 0 | 0 | 0 | 0
3 | 3 | 0 | 0 | 0 | 0
4 | 4 | 0 | 0 | 0 | 0
