gratefulfrog/ArduGuitar/android/ArduGuitarTestRN42_02/data/bridgeNorth1196x768.png

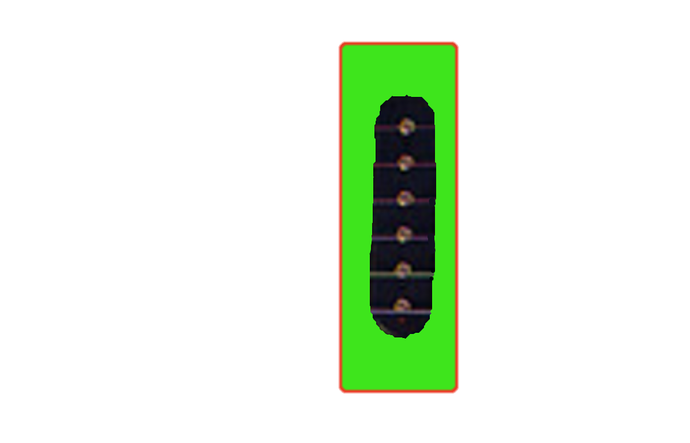
android/ArduGuitarTestRN42_02/data/bridgeNorth1196x768.png
