gratefulfrog/ArduGuitar/android/ArduGuitarTestRN42_02/data/Pickups1196x768.png

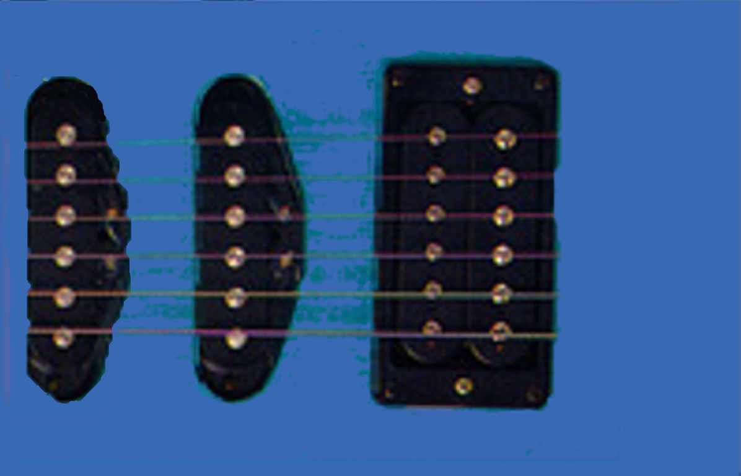
android/ArduGuitarTestRN42_02/data/Pickups1196x768.png
