gratefulfrog/ArduGuitar/Ardu2/design/POC-3_MAX395/HMI/Images/HMI PCB Test.jpg

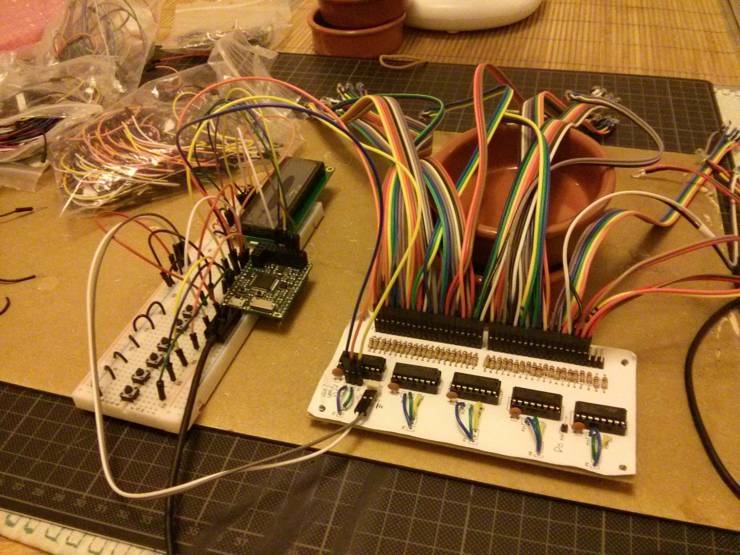
Ardu2/design/POC-3_MAX395/HMI/Images/HMI PCB Test.jpg
