gratefulfrog/ArduGuitar/Ardu2/design/POC-3_MAX395/pyboard/images/Full Test Platform 2016 10 06.jpg

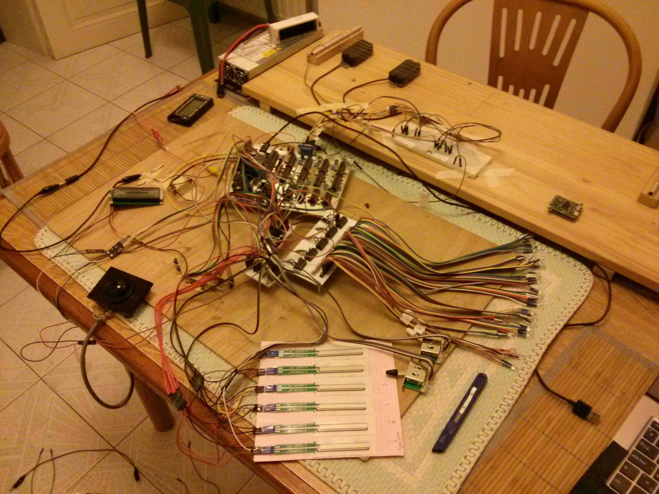
Ardu2/design/POC-3_MAX395/pyboard/images/Full Test Platform 2016 10 06.jpg
