gratefulfrog/ArduGuitar/Ardu2/design/POC-3_MAX395/pyboard/images/Tests 13V LM2596 PSU/temp_0.jpg

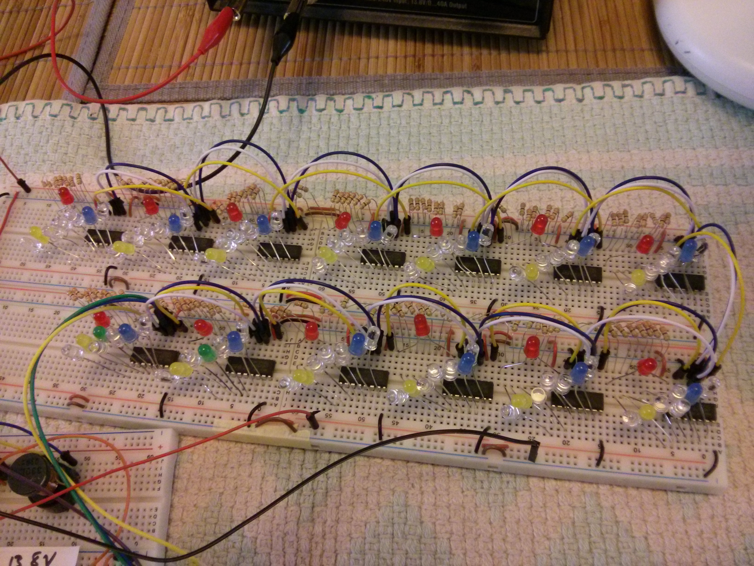
Ardu2/design/POC-3_MAX395/pyboard/images/Tests 13V LM2596 PSU/temp_0.jpg
