gratefulfrog/ArduGuitar/Ardu2/design/POC-3_MAX395/pyboard/images/Tests Arduino PSU/IMG_20150327_163743.jpg

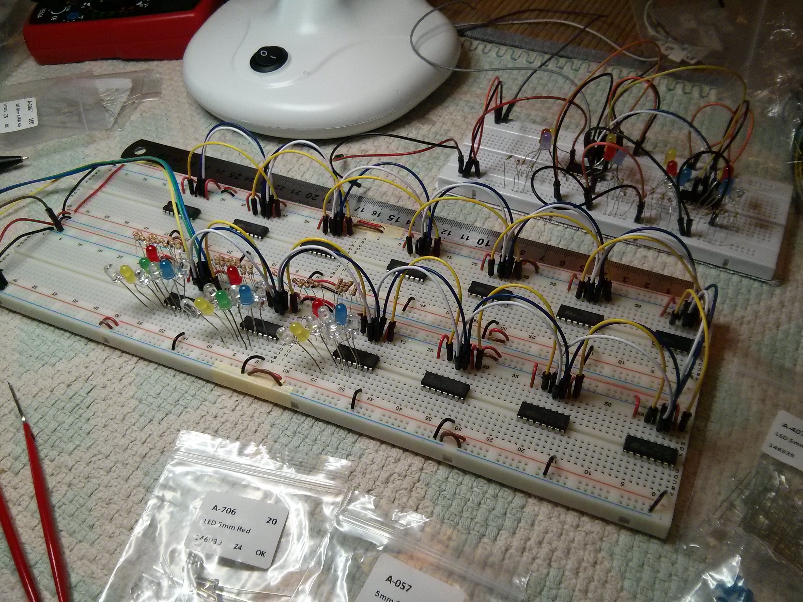
Ardu2/design/POC-3_MAX395/pyboard/images/Tests Arduino PSU/IMG_20150327_163743.jpg
