gratefulfrog/ArduGuitar/Ardu2/TestBed/Photos/IMG_20140201_170041.jpg

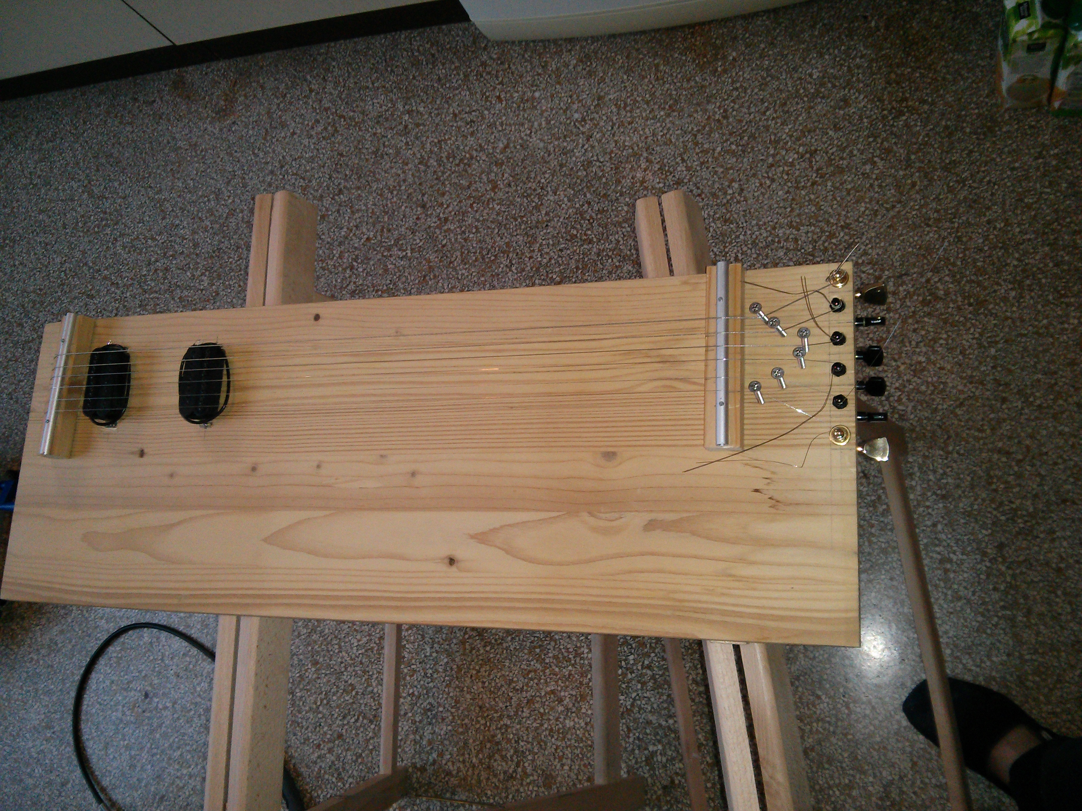
Ardu2/TestBed/Photos/IMG_20140201_170041.jpg
