gratefulfrog/ArduGuitar/Ardu2/TestBed/Photos/IMG_20140201_170257.jpg

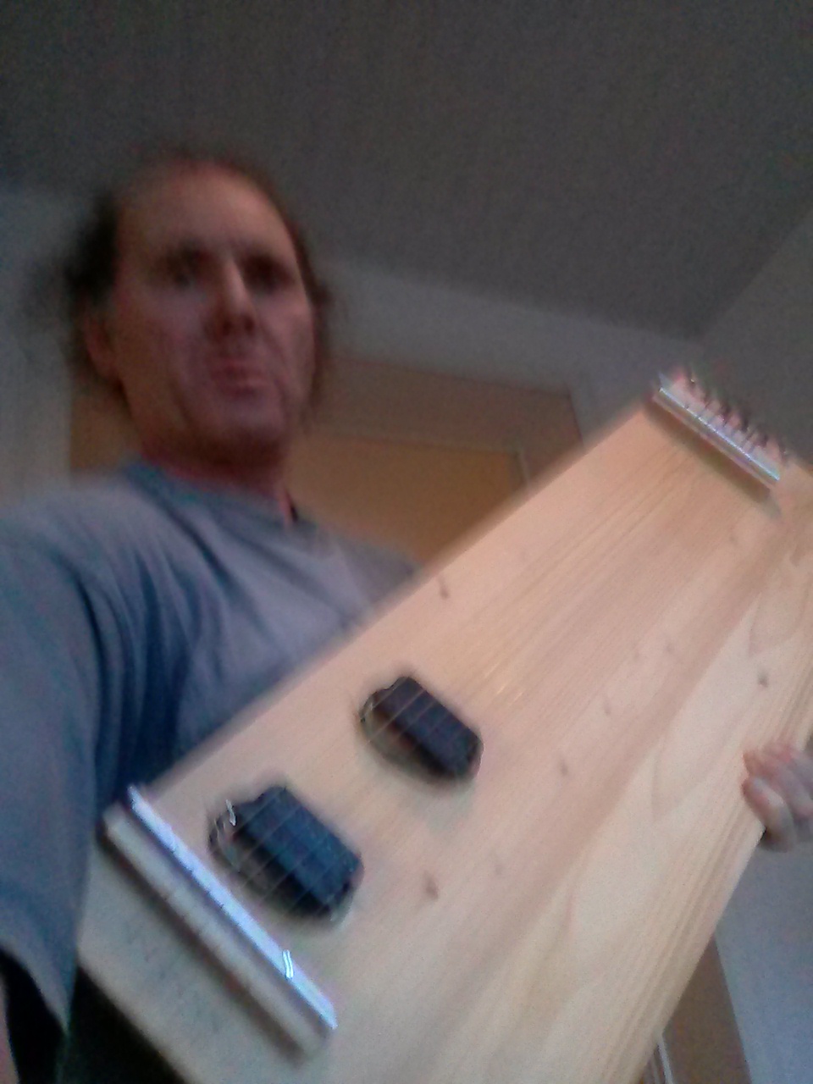
Ardu2/TestBed/Photos/IMG_20140201_170257.jpg
