gratefulfrog/ArduGuitar/Ardu2/TestBed/Photos/IMG_20140201_173019.jpg

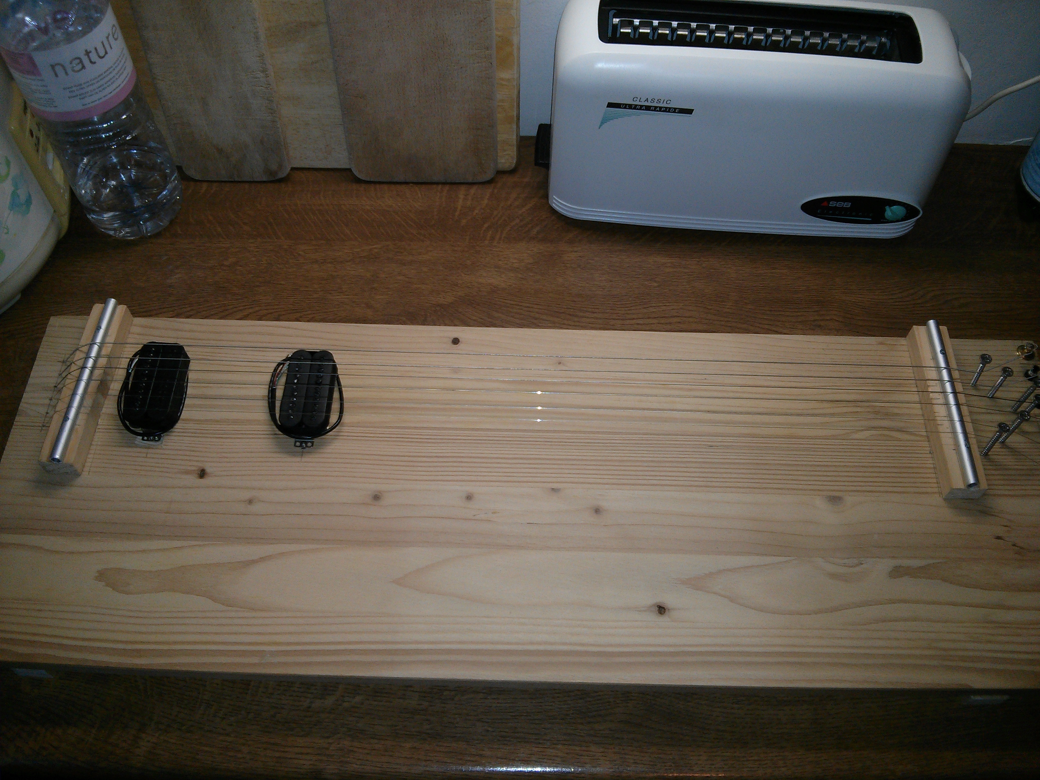
Ardu2/TestBed/Photos/IMG_20140201_173019.jpg
