gratefulfrog/ArduGuitar/Ardu2/TestBed/Photos/IMG_20140201_174342.jpg

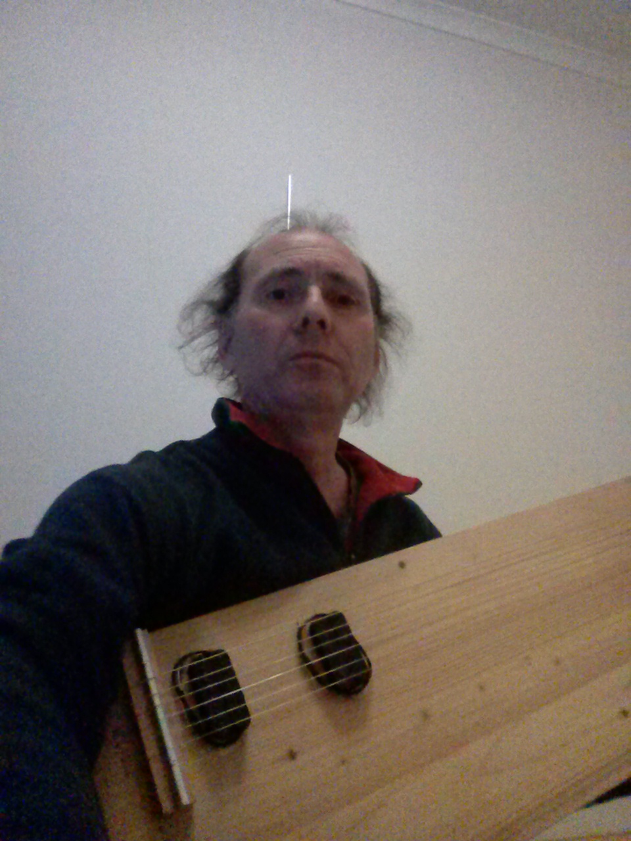
Ardu2/TestBed/Photos/IMG_20140201_174342.jpg
