gratefulfrog/ArduGuitar/Ardu2/TestBed/Photos/IMG_20140201_174350.jpg

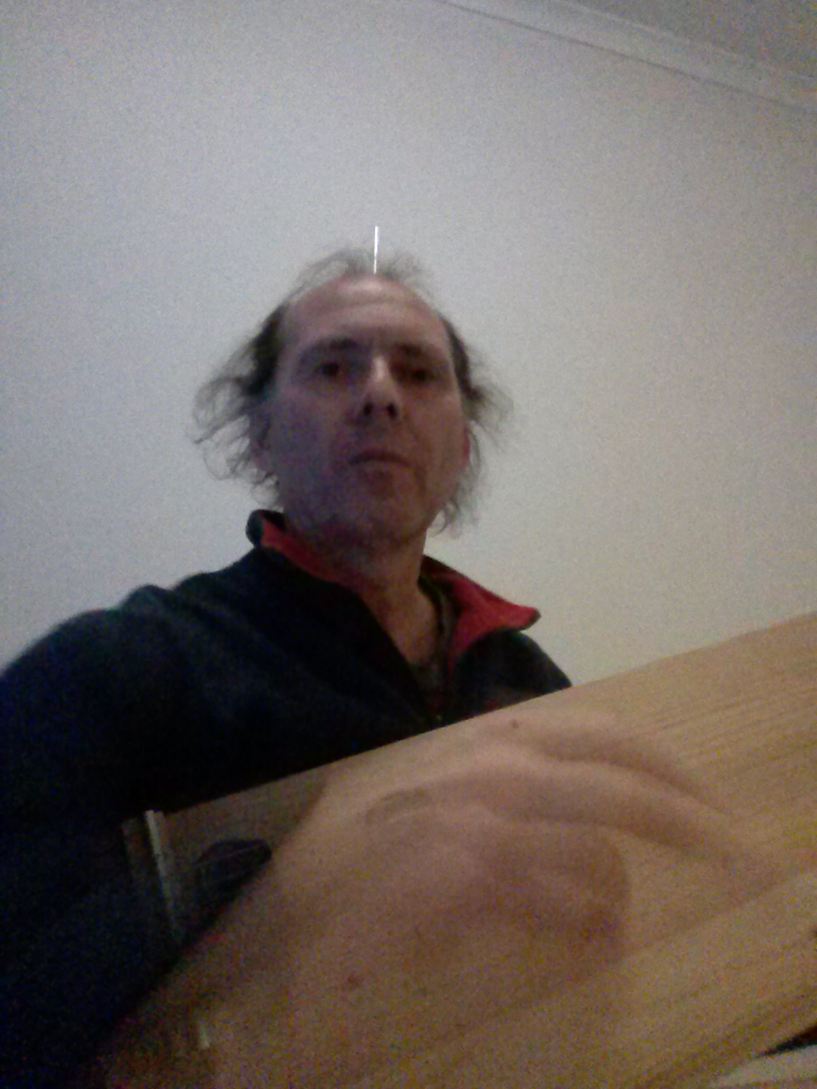
Ardu2/TestBed/Photos/IMG_20140201_174350.jpg
