gratefulfrog/ArduGuitar/Ardu3/DraftDevt/Pyboard/AD75019/NC Tests and Measures/Pin 6 and Pin 15 with 7.6v analog supply.png

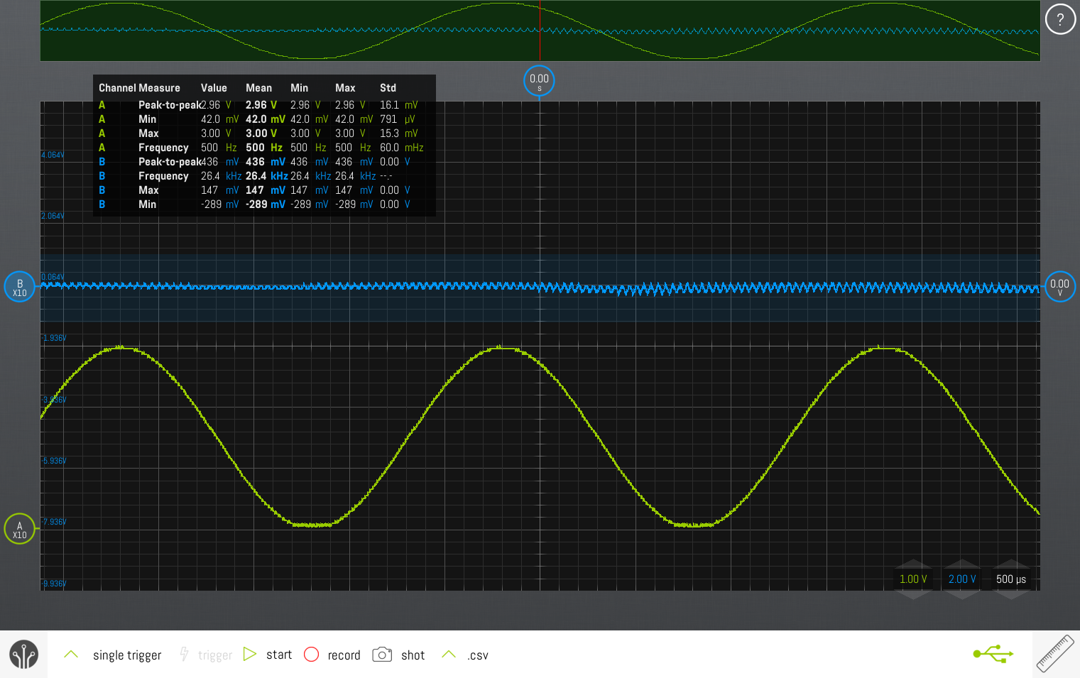
Ardu3/DraftDevt/Pyboard/AD75019/NC Tests and Measures/Pin 6 and Pin 15 with 7.6v analog supply.png
