gratefulfrog/ArduGuitar/Ardu3/DraftDevt/Pyboard/AD75019/NC Tests and Measures/Pin 39 and Pin 15 with 11.3v analog supply.png

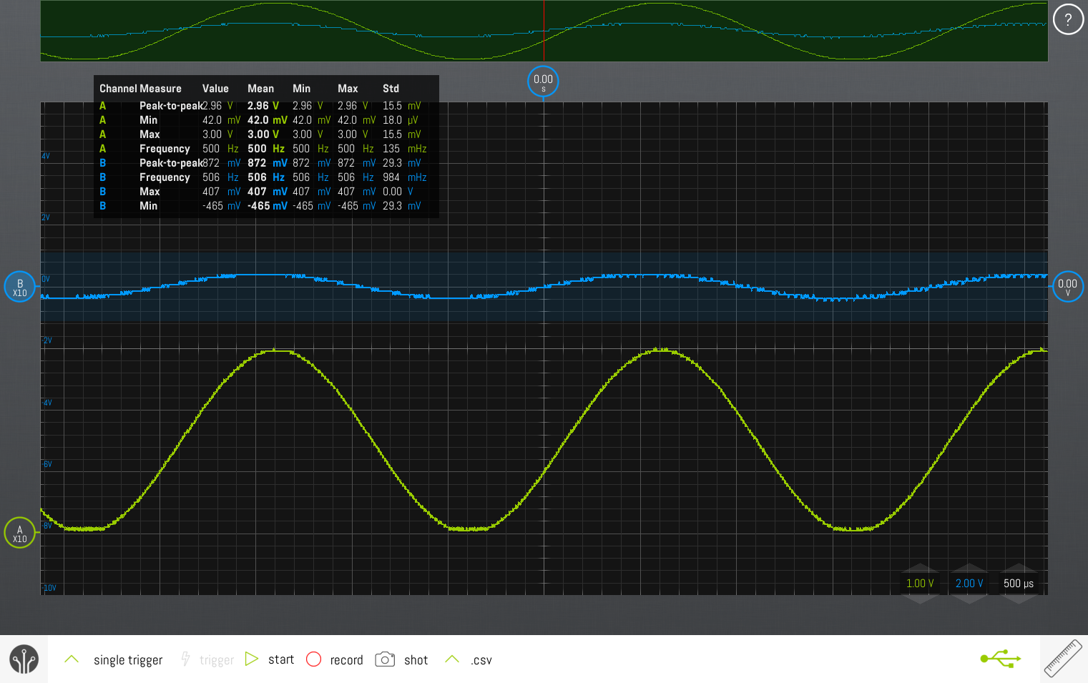
Ardu3/DraftDevt/Pyboard/AD75019/NC Tests and Measures/Pin 39 and Pin 15 with 11.3v analog supply.png
