gratefulfrog/ArduGuitar/Ardu3/DraftDevt/Pyboard/AD75019/Scope Images and Test Results/All Off.png

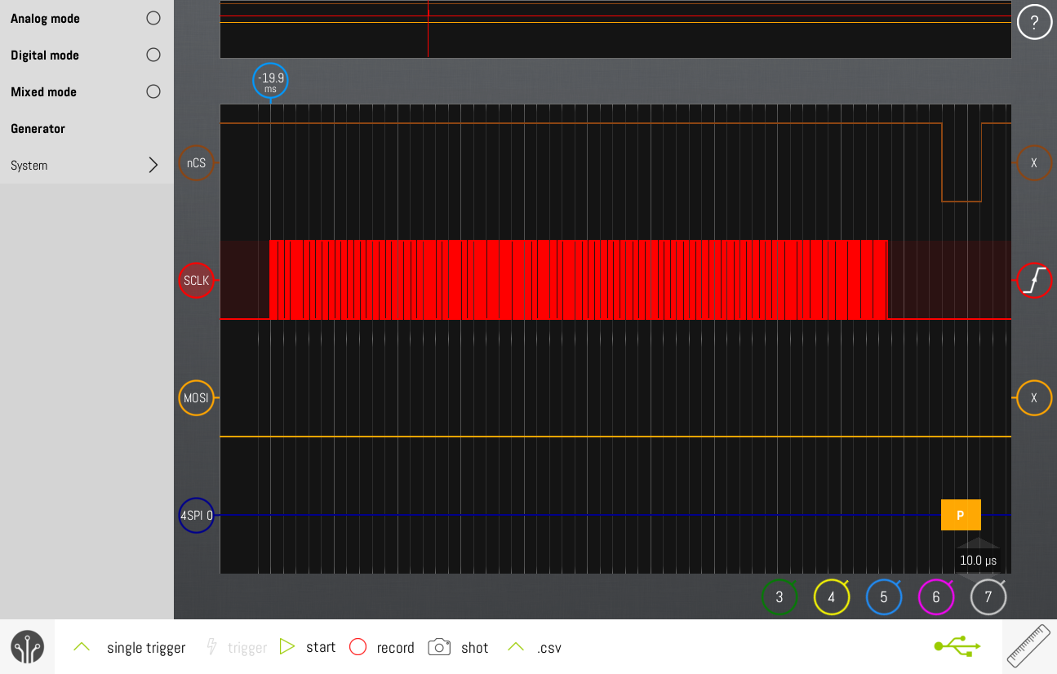
Ardu3/DraftDevt/Pyboard/AD75019/Scope Images and Test Results/All Off.png
