gratefulfrog/ArduGuitar/arduino/Layouts/ArduStomp/EnclosureDesign/3D/FabTestModels/middle.bmp

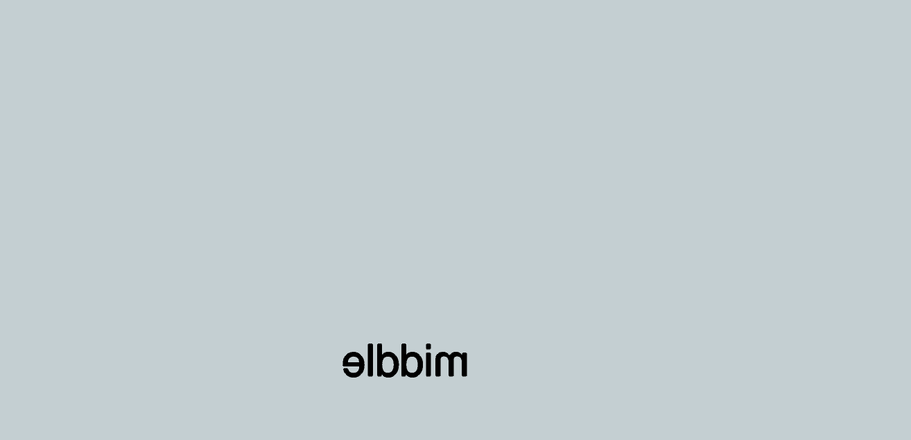
arduino/Layouts/ArduStomp/EnclosureDesign/3D/FabTestModels/middle.bmp
