gratefulfrog/ArduGuitar/tests/Processing/ControlP5Gui/Screenshot - 02192013 - 06:09:32 PM.png

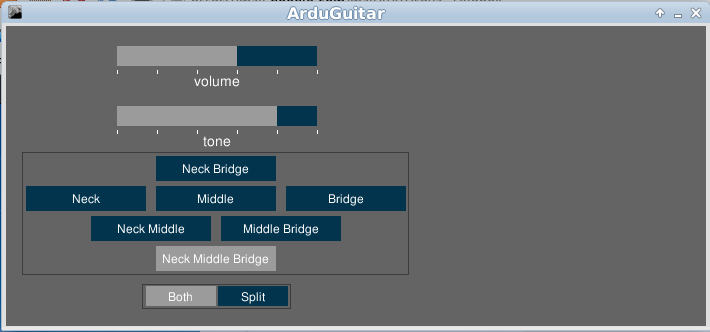
tests/Processing/ControlP5Gui/Screenshot - 02192013 - 06:09:32 PM.png
