gratefulfrog/ArduGuitar/tests/Processing/ControlP5Gui/Screenshot - 02202013 - 05:40:56 PM.png

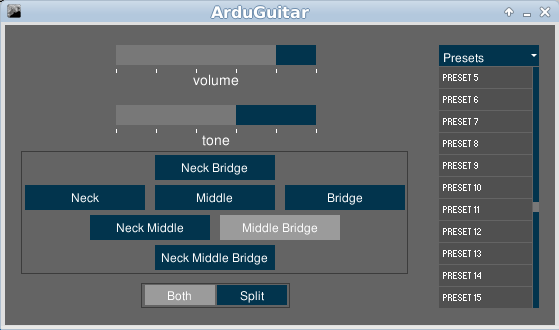
tests/Processing/ControlP5Gui/Screenshot - 02202013 - 05:40:56 PM.png
