gratefulfrog/ArduGuitar/tests/Processing/ControlP5Gui/Screenshot - 02212013 - 12:36:25 PM.png

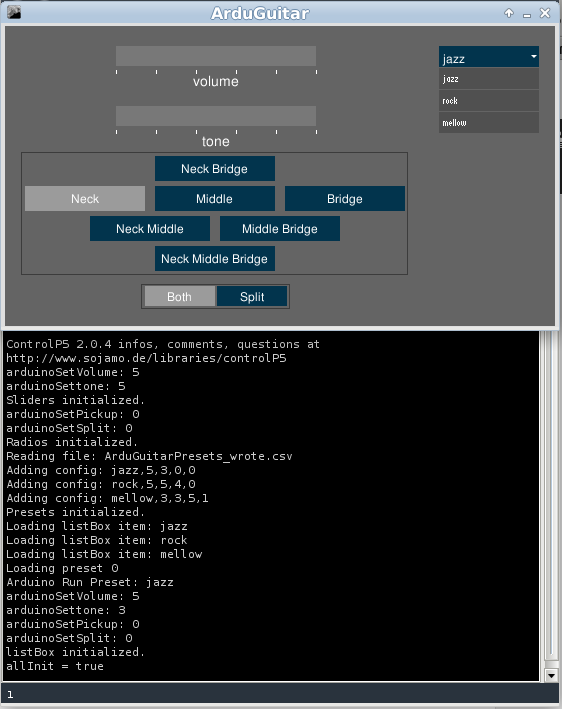
tests/Processing/ControlP5Gui/Screenshot - 02212013 - 12:36:25 PM.png
