gratefulfrog/ArduGuitar/tests/Processing/ControlP5Gui/Screenshot - 02252013 - 06:48:04 PM.png

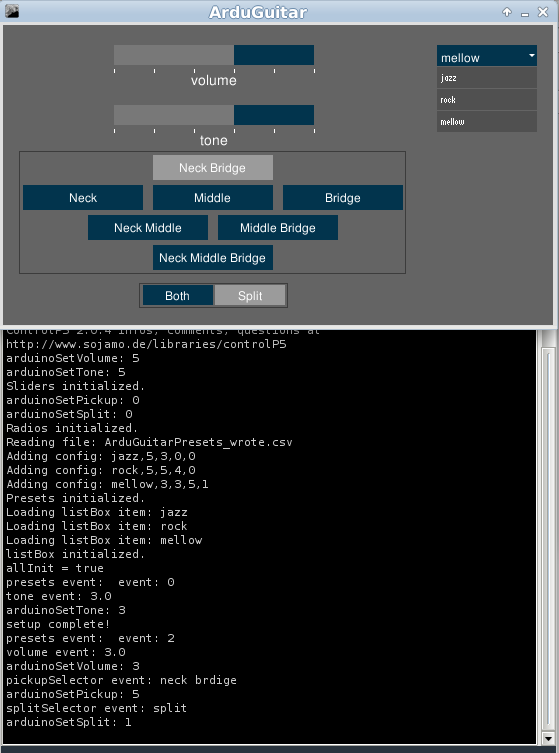
tests/Processing/ControlP5Gui/Screenshot - 02252013 - 06:48:04 PM.png
