gratefulfrog/ArduGuitar/tests/Processing/ControlP5Gui/Screenshot - 02282013 - 03:25:45 PM.png

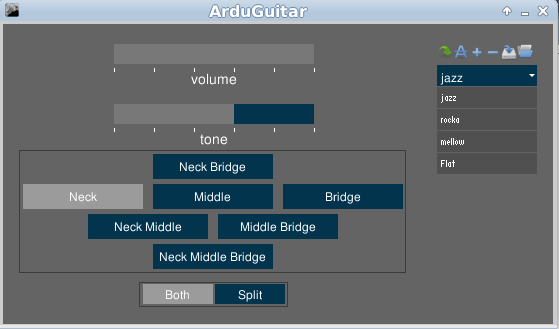
tests/Processing/ControlP5Gui/Screenshot - 02282013 - 03:25:45 PM.png
