gratefulfrog/ArduGuitar/tests/Processing/ControlP5Gui/Screenshot - 02282013 - 03:29:36 PM.png

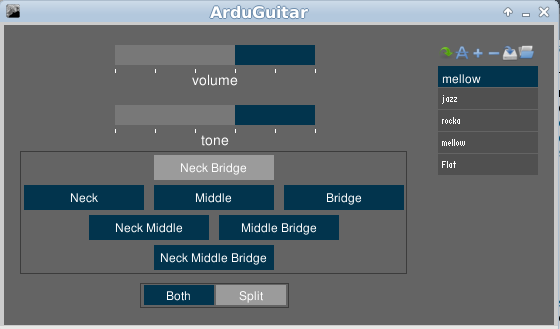
tests/Processing/ControlP5Gui/Screenshot - 02282013 - 03:29:36 PM.png
