gratefulfrog/ArduGuitar/tests/Processing/Humbucker/data/humbucker.png

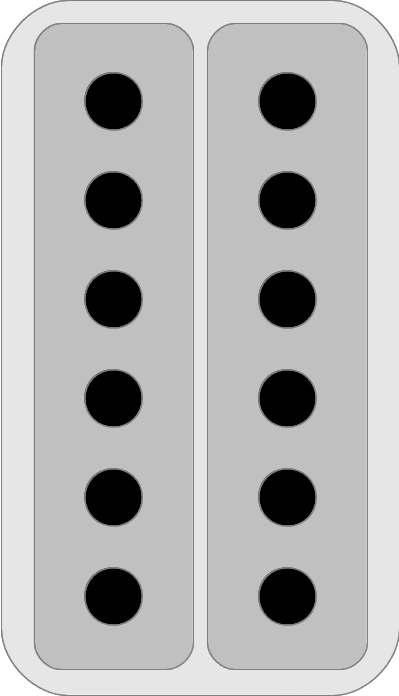
tests/Processing/Humbucker/data/humbucker.png
