gratefulfrog/ArduGuitar/Ardu2/design/POC-3_MAX395/KicadProjects/FullCircuit/Images/fullCircuit.pdf

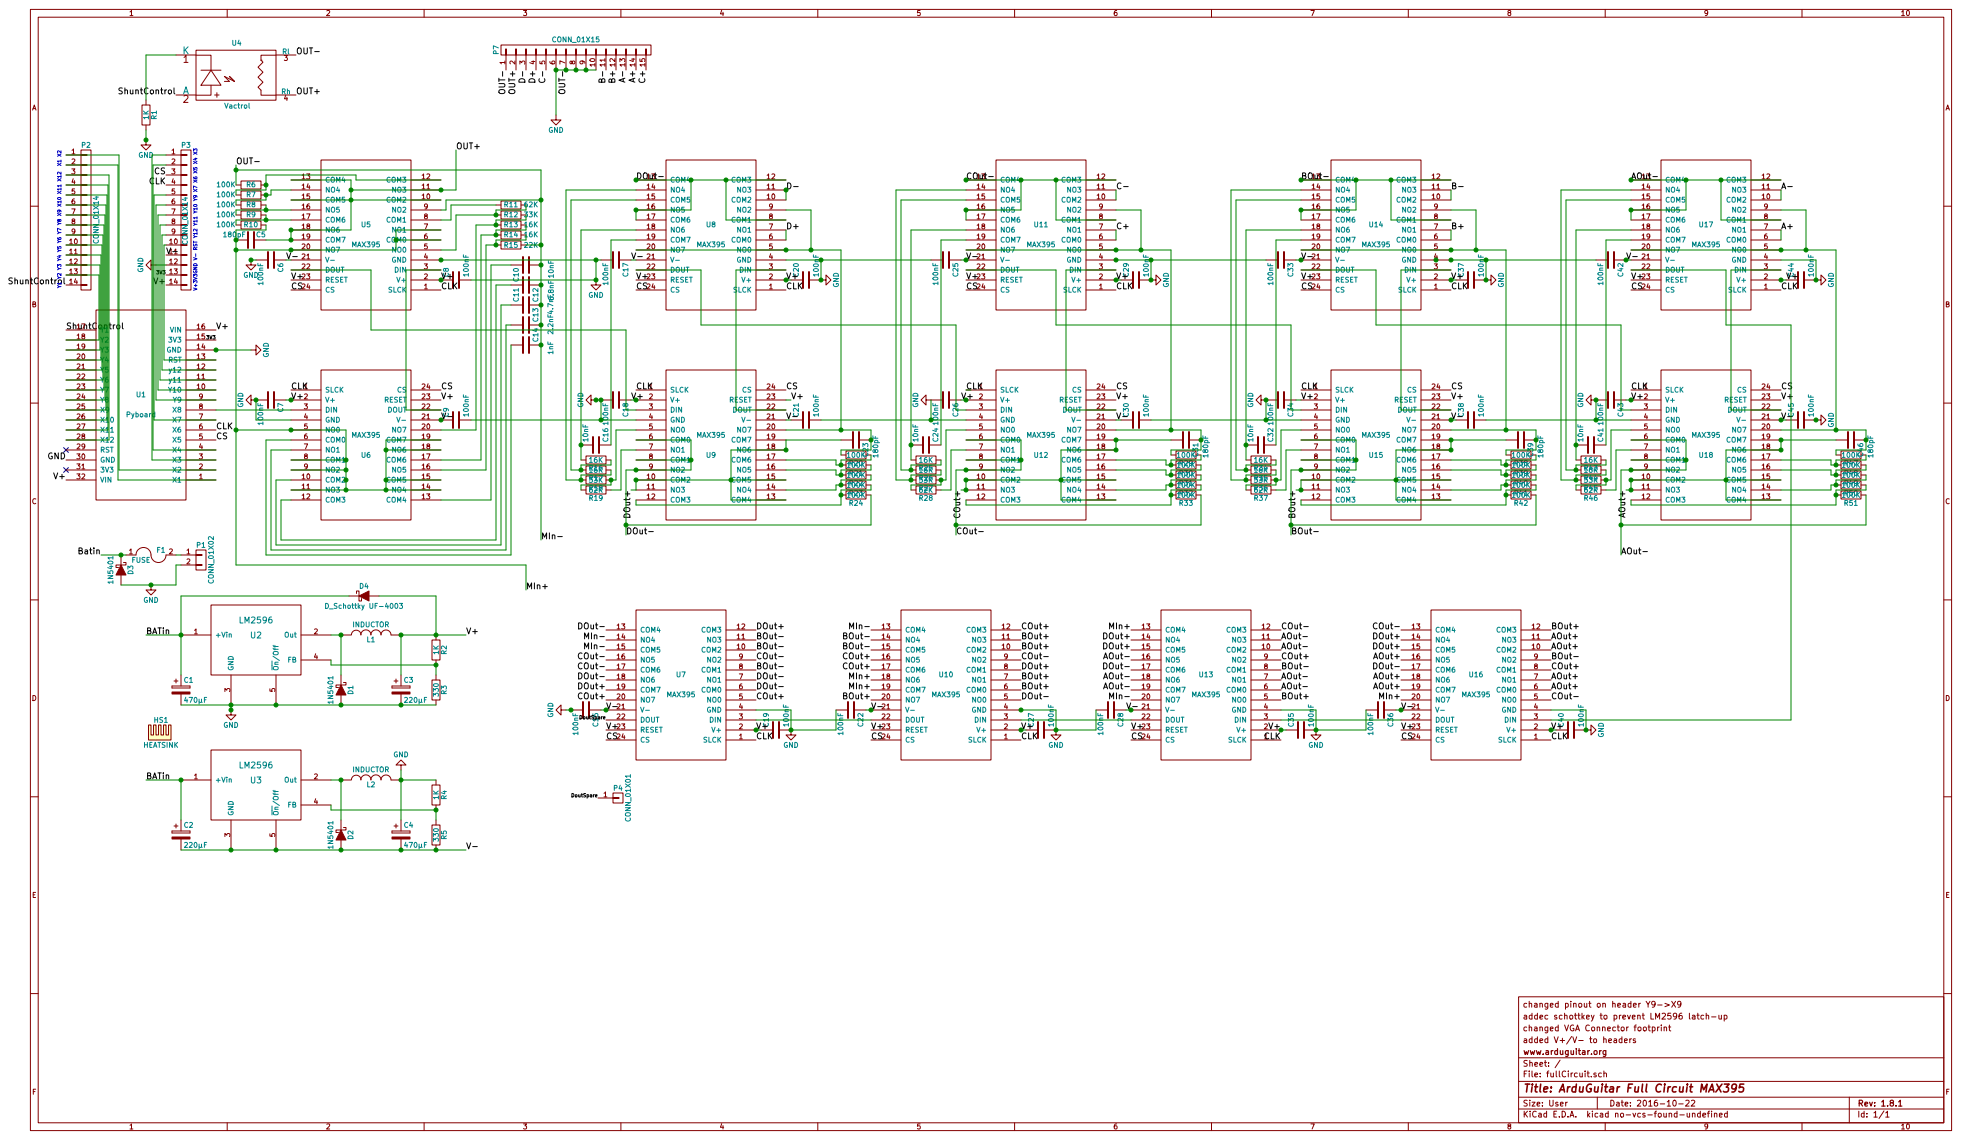
[picture p339: page 1]

DOut- MIn- MIn- COut-

BOut-
COut+
COut+ MIn+ MIn+ BOut+

changed pinout on header Y9->X9
addec schottkey to prevent LM2596 latch-up
changed VGA Connector footprint
added V+/V- to headers
File: fullCircuit.sch Sheet: / www.arduguitar.org

Id: 1/1 Title: ArduGuitar Full Circuit MAX395
