gratefulfrog/ArduGuitar/Ardu2/design/POC-3_MAX395/KicadProjects/HMI_PCB/FrontSilk.pdf

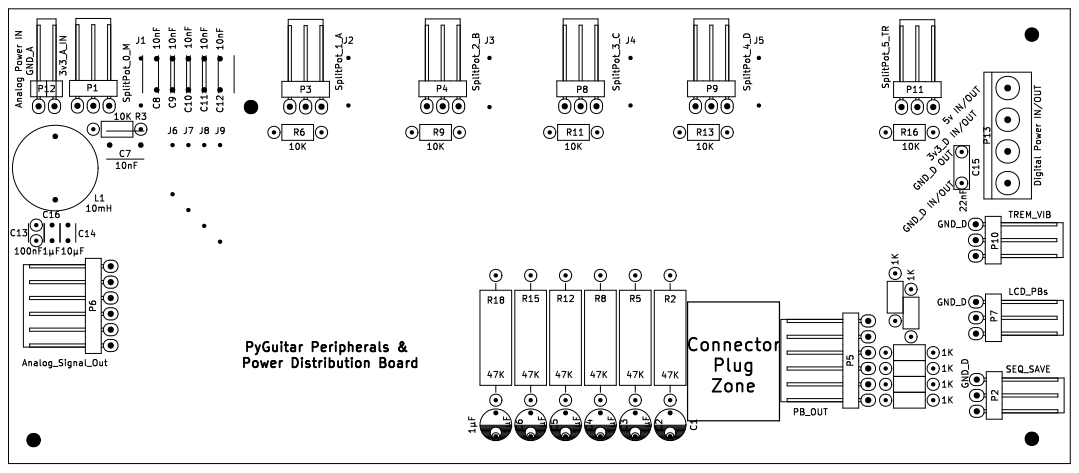
[picture p350: page 1]
