gratefulfrog/ArduGuitar/Ardu2/design/POC-3_MAX395/KicadProjects/HMI_PCB/FrontSilkWithTracks.pdf

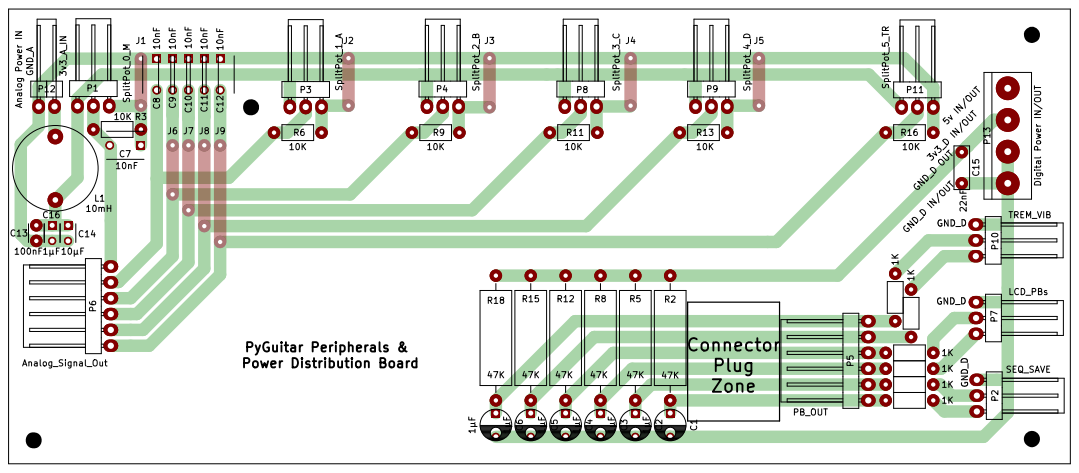
[picture p351: page 1]
