gratefulfrog/ArduGuitar/Ardu2/design/POC-3_MAX395/KicadProjects/HMI_PCB/DrillMap_components.pdf

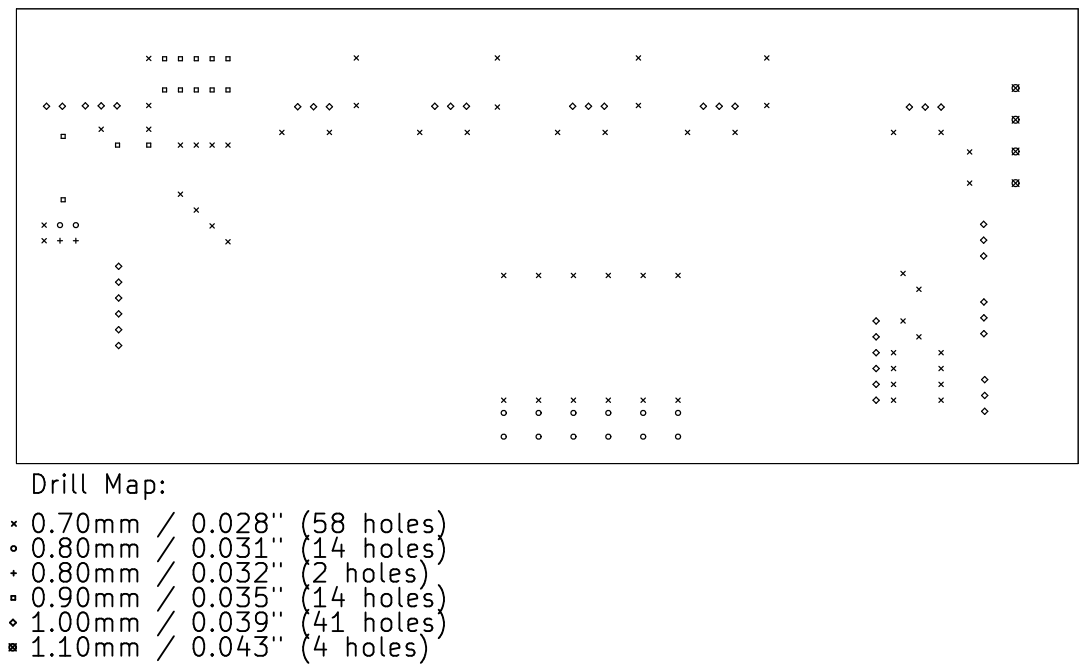
[picture p352: page 1]
