gratefulfrog/ArduGuitar/Ardu2/design/POC-3_MAX395/KicadProjects/HMI_PCB/HMI-PCB_1_4.pdf

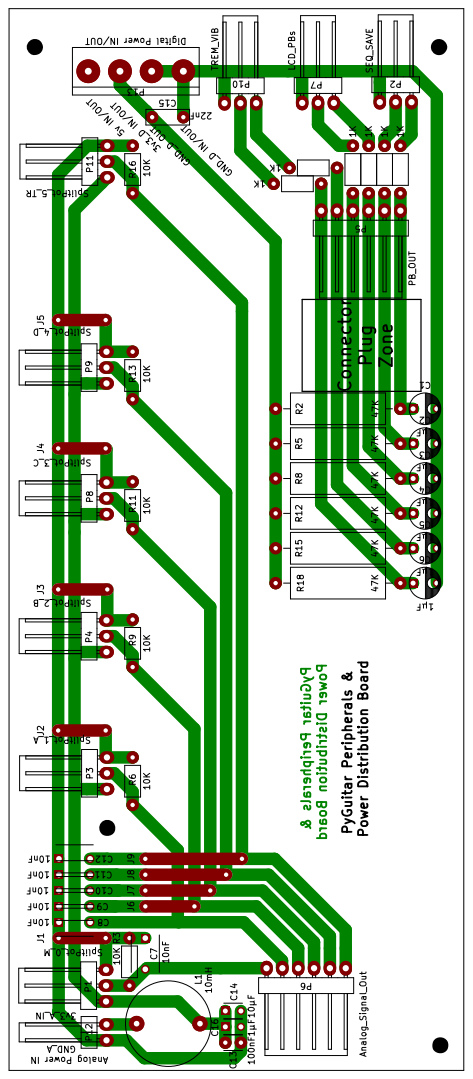
[picture p353: page 1]
