gratefulfrog/ArduGuitar/Ardu2/design/POC-3_MAX395/HMI/Etching_LCD_PBs/LCD_2xPBs_etch_copper_top.pdf

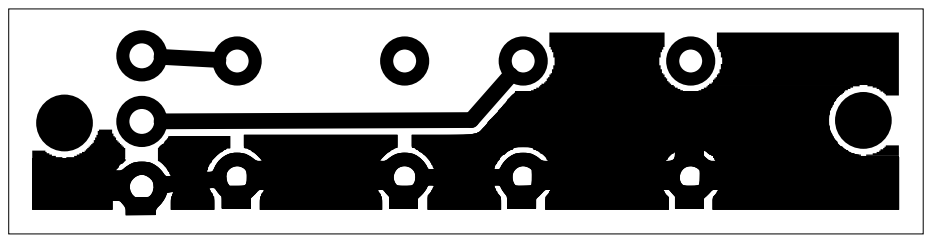
[picture p355: page 1]
