gratefulfrog/ArduGuitar/Ardu2/design/POC-3_MAX395/HMI/Etching_Upper/UPPER_Vibrato_Tremolo_2xPBs_etch_copper_top.pdf

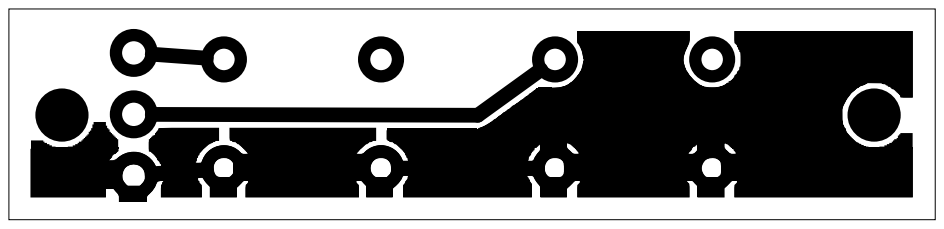
[picture p356: page 1]
