gratefulfrog/ArduGuitar/Ardu2/design/POC-2/Carvin Integration/Carvin/10PDT Mount v2_pcb.pdf

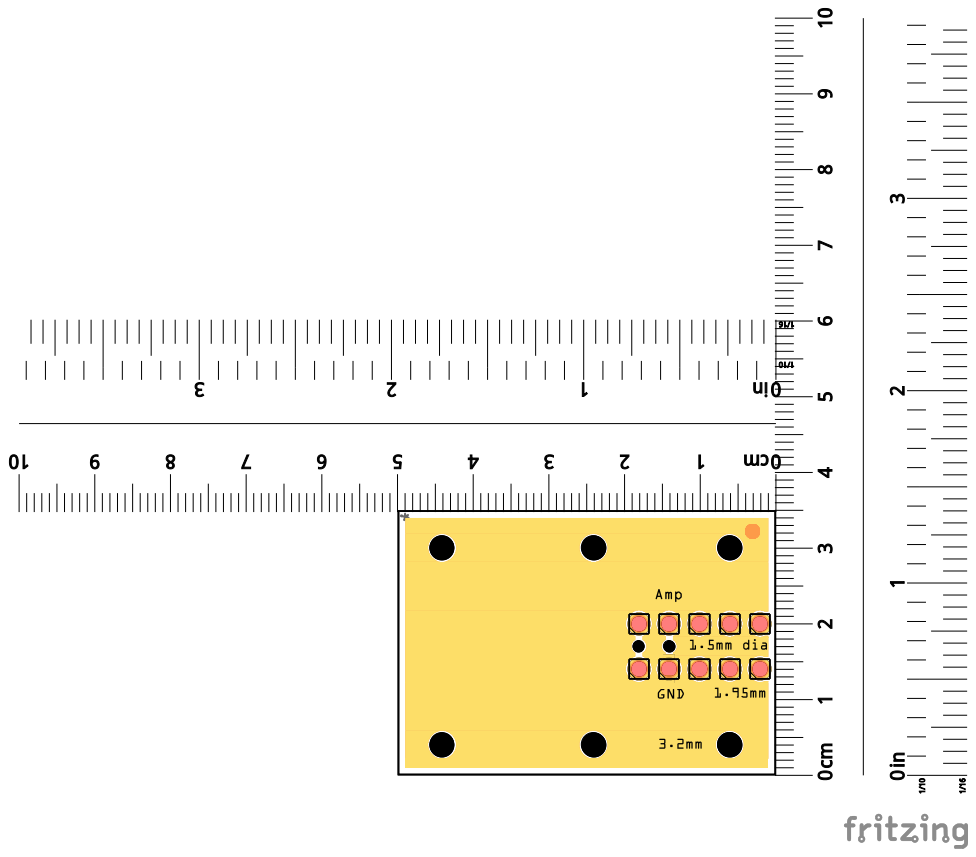
[picture p357: page 1]
