gratefulfrog/ArduGuitar/Ardu2/design/POC-2/InverterVolTone/Master-Vol-tone-GERBER/silkTop.pdf

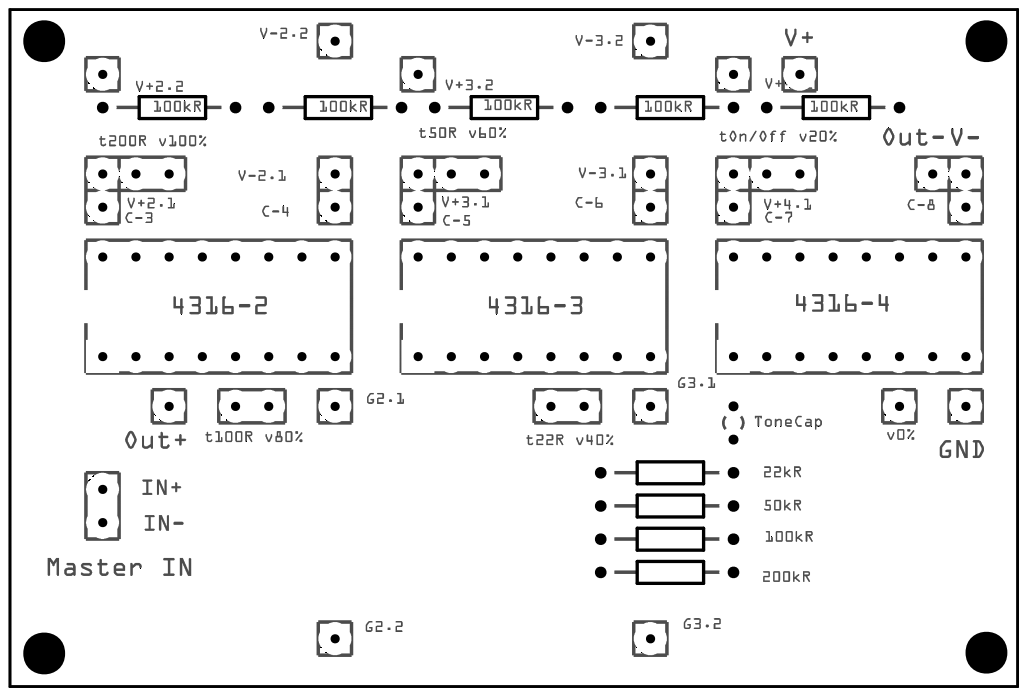
[picture p358: page 1]
