gratefulfrog/ArduGuitar/Ardu2/design/POC-2/InverterVolTone/Master-Vol-tone-GERBER/stencilTop.pdf

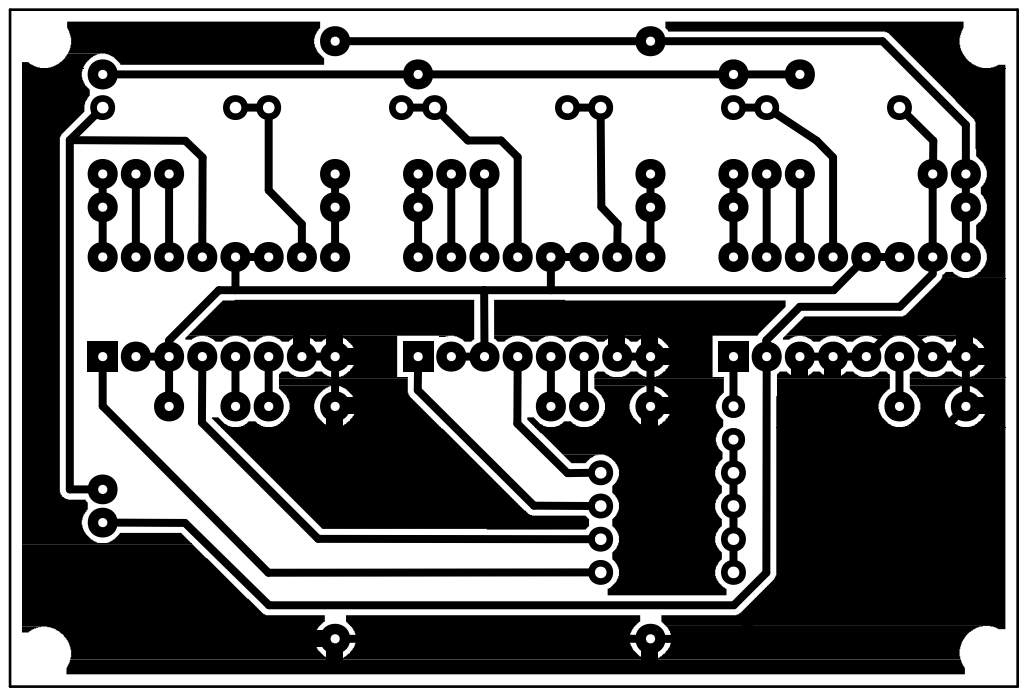
[picture p359: page 1]
