gratefulfrog/ArduGuitar/Ardu2/design/POC-2/InverterVolTone/Inverter-V-T-GERBER/silkTop.pdf

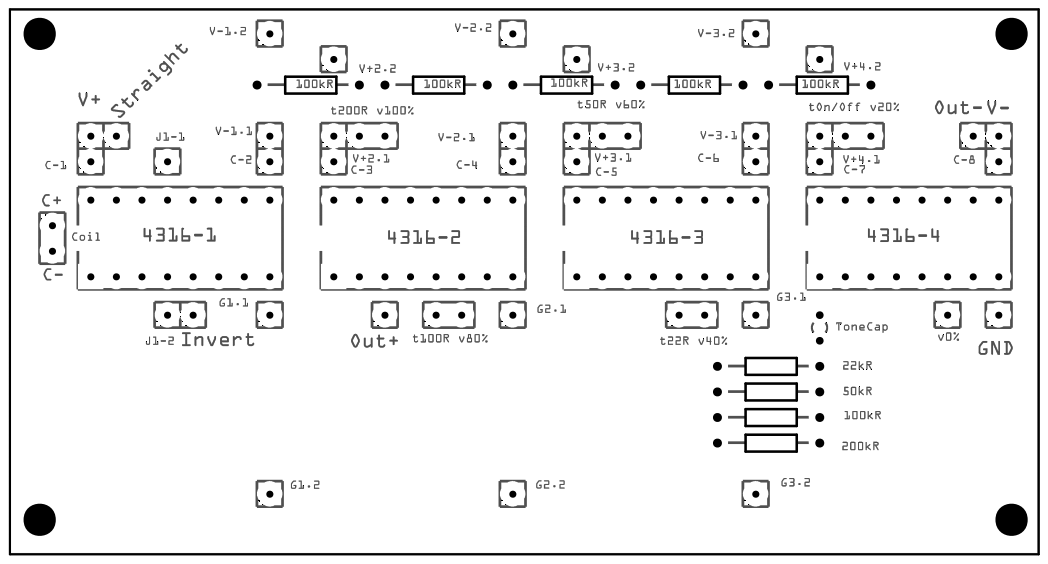
[picture p360: page 1]
