gratefulfrog/ArduGuitar/Ardu2/design/POC-2/InverterVolTone/Inverter-V-T-GERBER/stencilTop.pdf

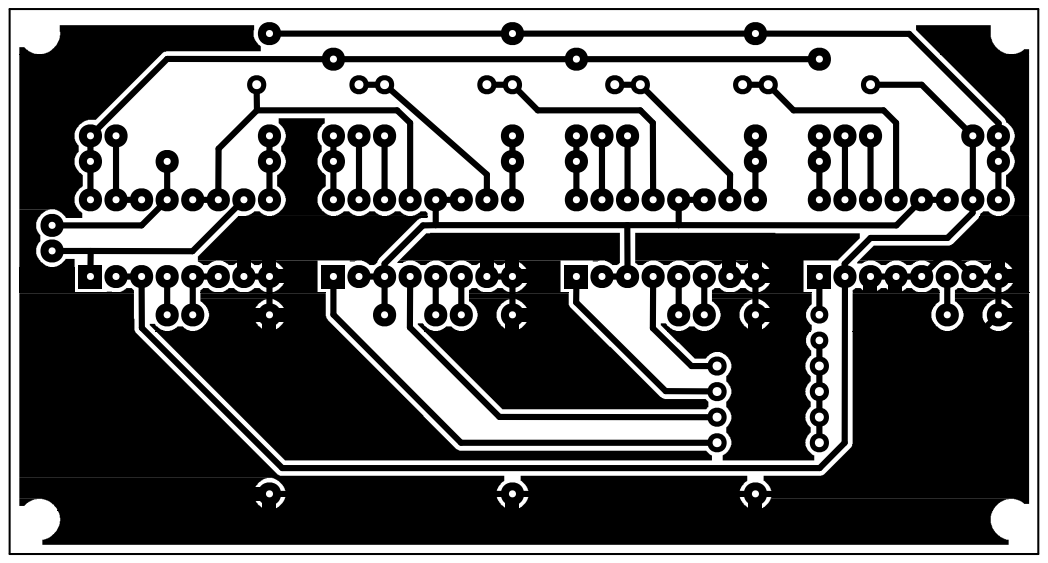
[picture p361: page 1]
