gratefulfrog/ArduGuitar/Ardu2/design/POC-2/InverterVolTone/SPDT-GERBER/silkTop.pdf

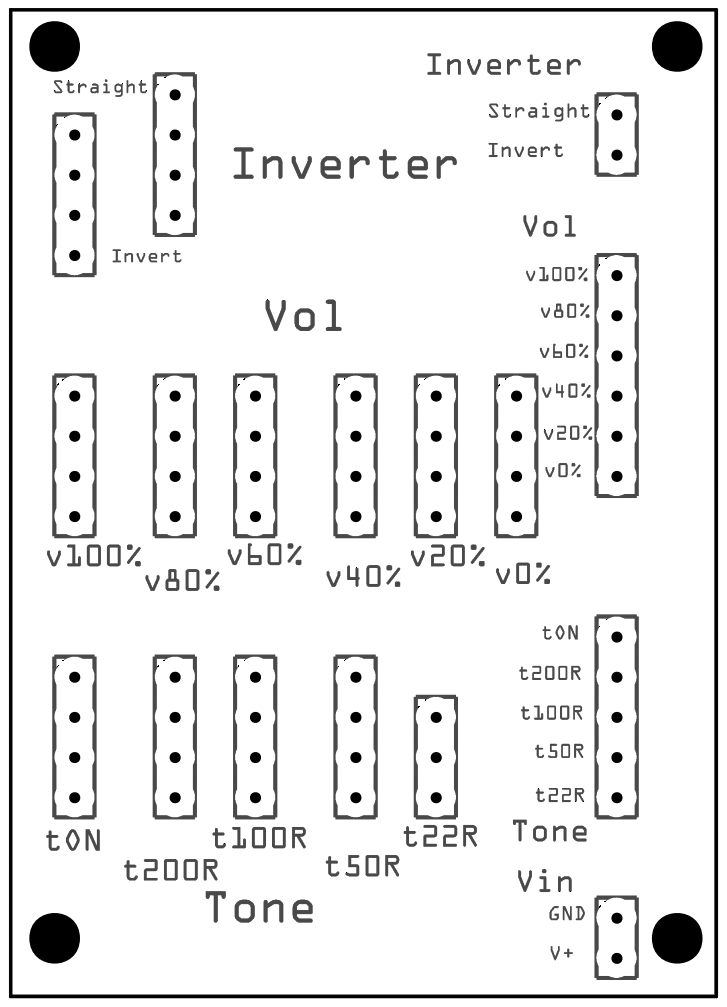
[picture p362: page 1]
