gratefulfrog/ArduGuitar/Ardu2/design/POC-2/InverterVolTone/SPDT-GERBER/stencilTopView.pdf

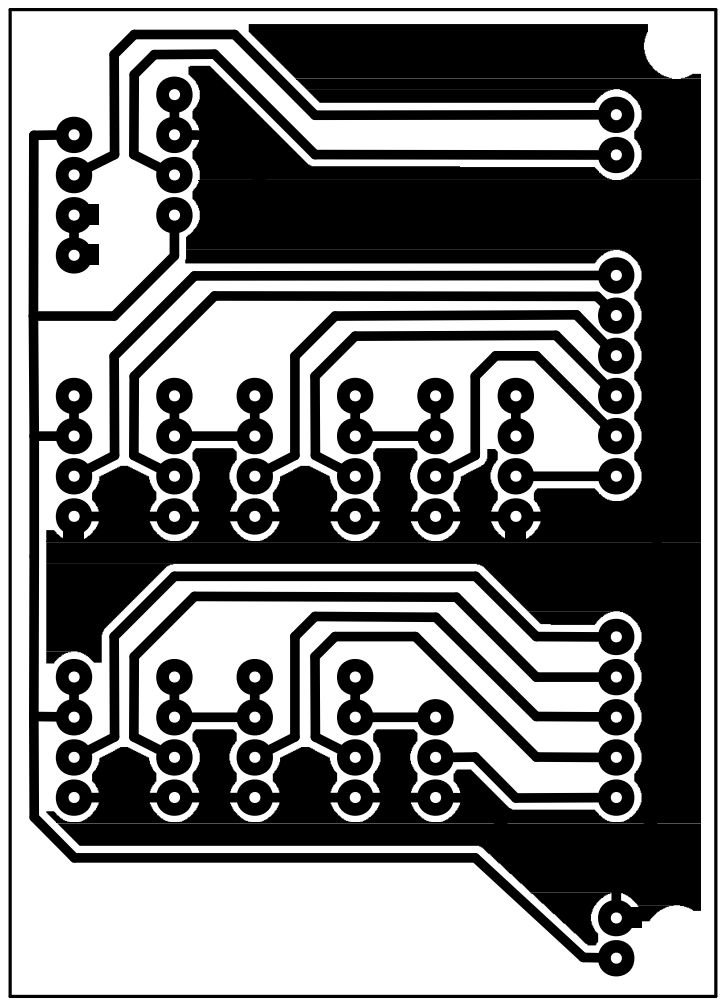
[picture p363: page 1]
