gratefulfrog/ArduGuitar/arduino/Layouts/ArduStomp/EnclosureDesign/2D/FullDesign08.pdf

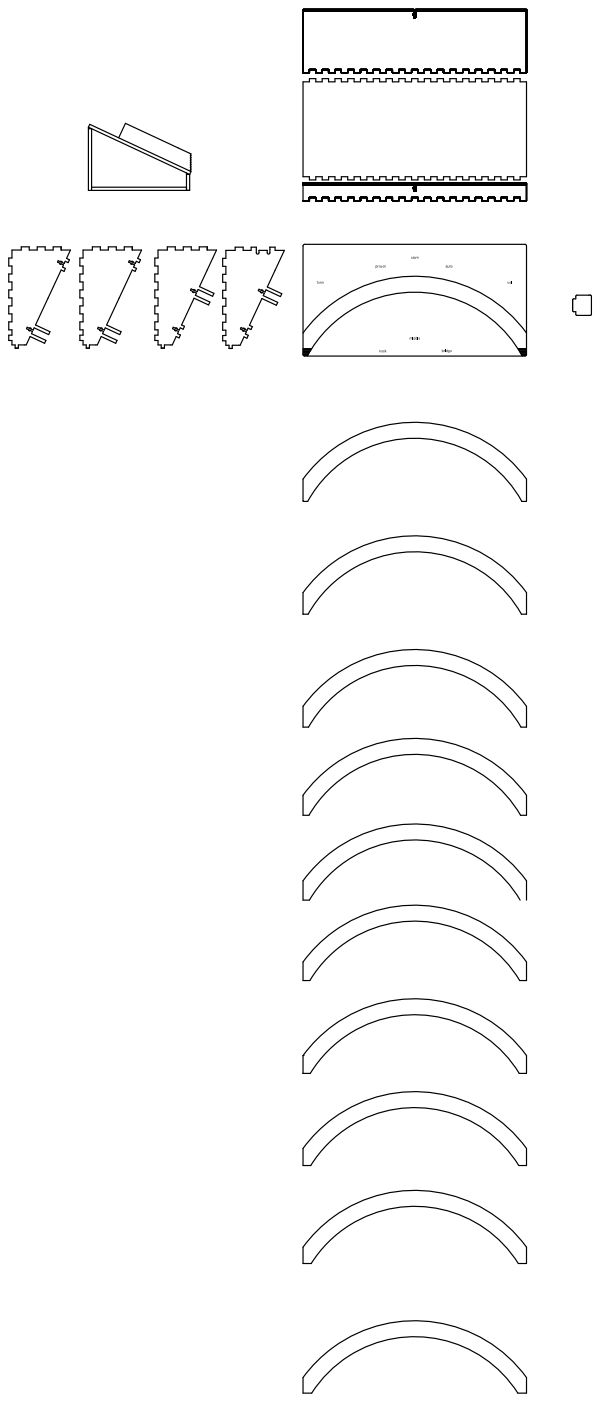
[picture p364: page 1]
