gratefulfrog/ArduGuitar/arduino/Layouts/ArduStomp/EnclosureDesign/2D/FullDesign00.pdf

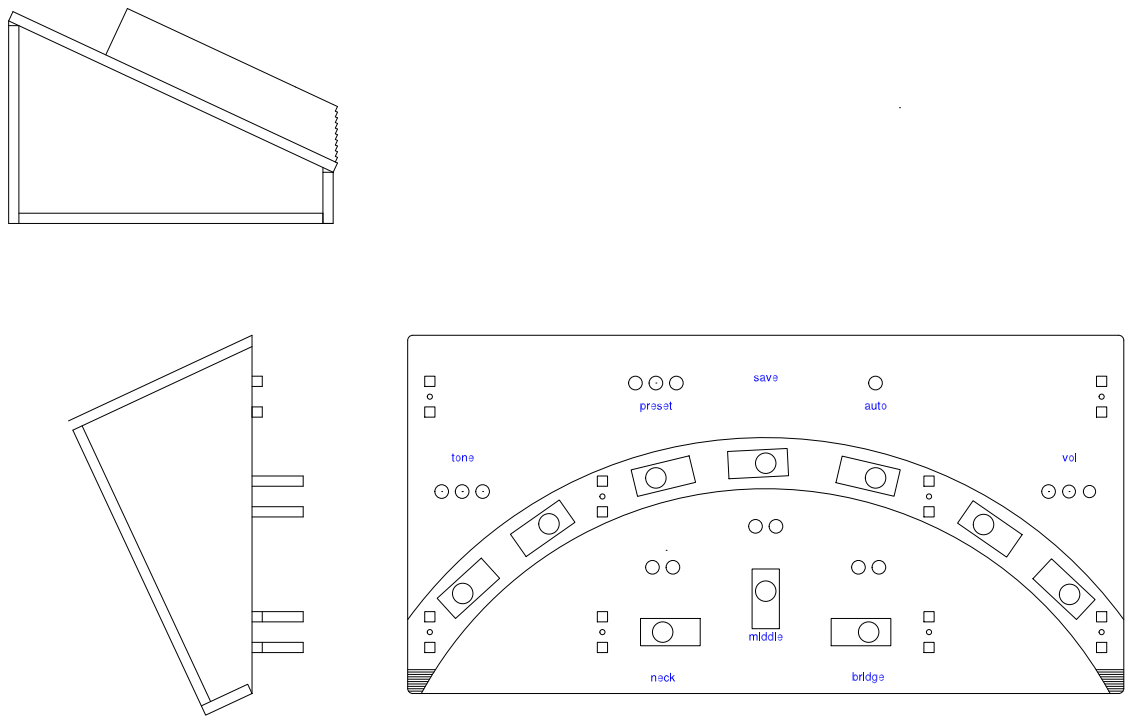
[picture p365: page 1]
