gratefulfrog/ArduGuitar/Ardu2/design/POC-3_MAX395/KicadProjects/PickupWiring/Gerber/stencil.pdf

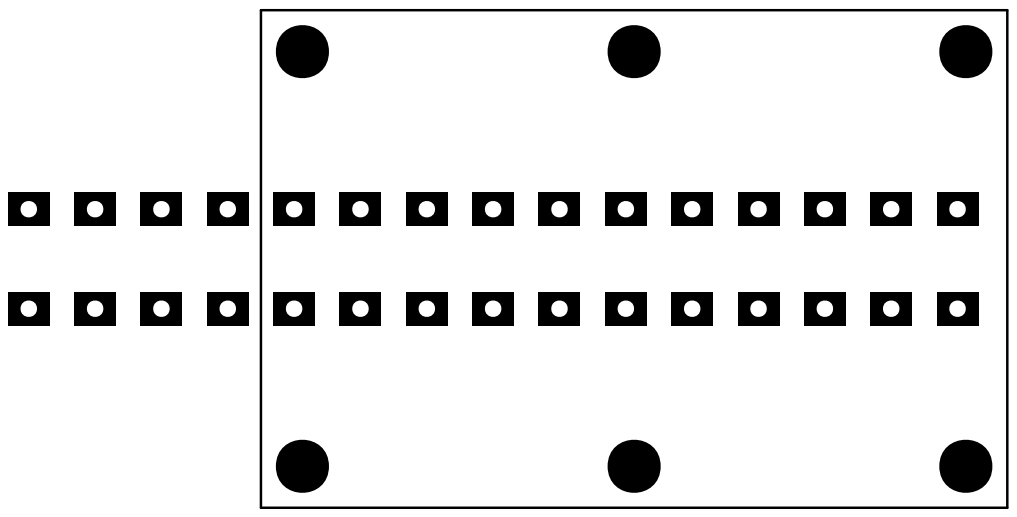
[picture p366: page 1]
