gratefulfrog/ArduGuitar/Ardu2/design/POC-3_MAX395/KicadProjects/PickupWiring/Gerber/stencil_ready.pdf

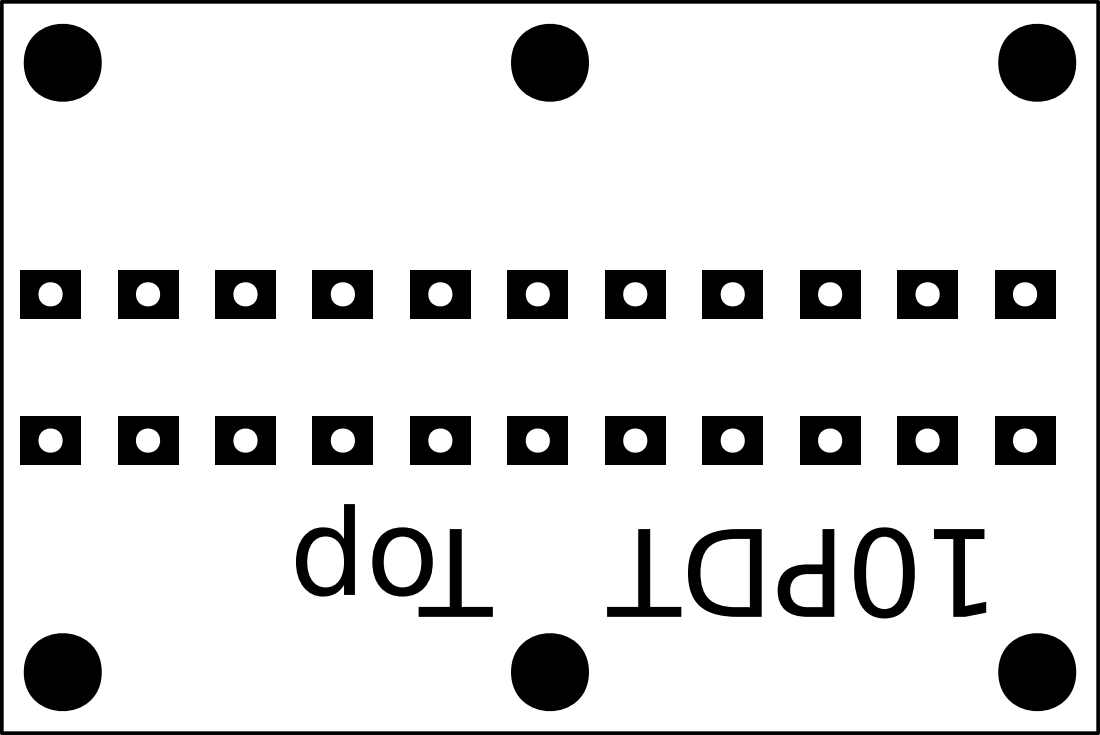
[picture p367: page 1]
