gratefulfrog/ArduGuitar/Ardu2/design/POC-3_MAX395/KicadProjects/PickupWiring/Gerber/10PDT Board.pdf

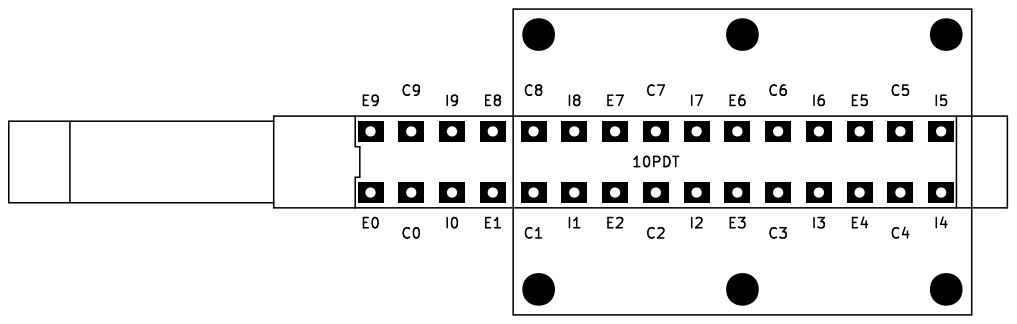
[picture p368: page 1]
