gratefulfrog/ArduGuitar/Ardu2/design/POC-3_MAX395/HMI/KicadProjects/Single HW Debounce PBs circuit /All Layers.pdf

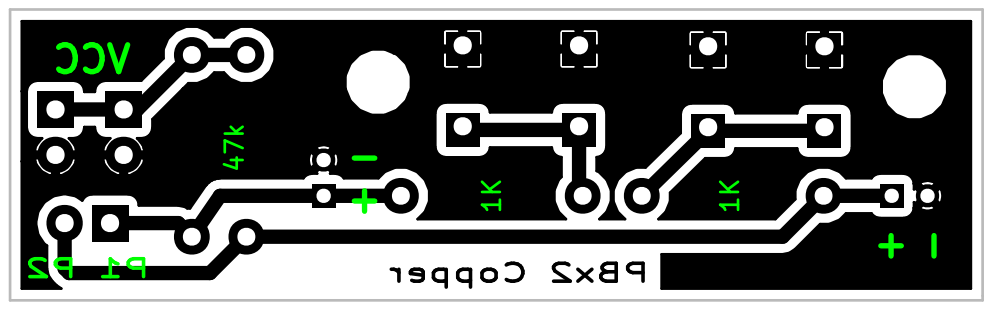
[picture p370: page 1]
