gratefulfrog/ArduGuitar/Ardu2/design/POC-3_MAX395/HMI/KicadProjects/Main HMI Circuit/PCB  02 no fill.pdf

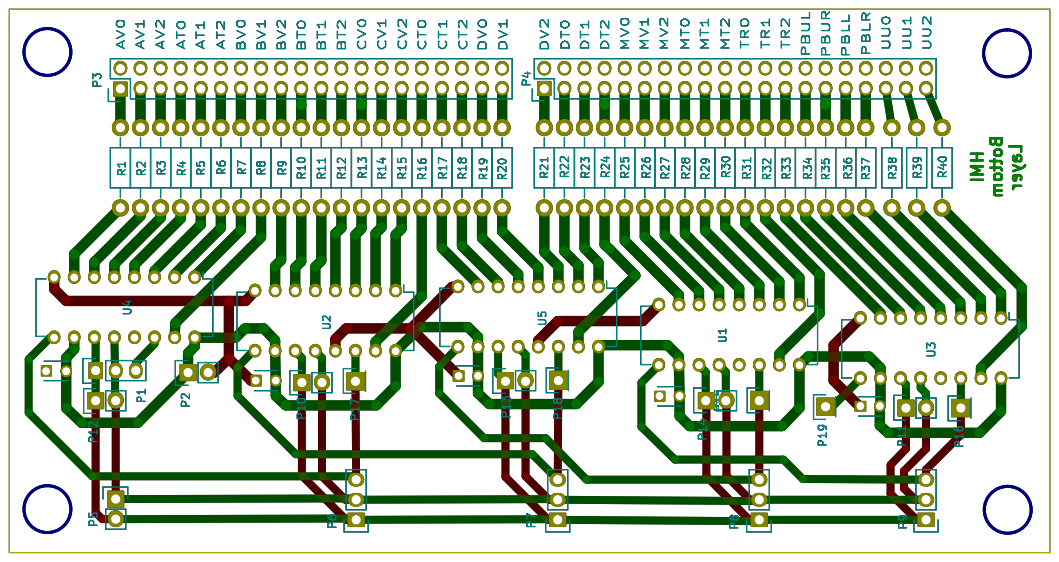
[picture p371: page 1]
