gratefulfrog/ArduGuitar/Ardu2/design/POC-3_MAX395/HMI/KicadProjects/Main HMI Circuit/PCB  02a no fill.pdf

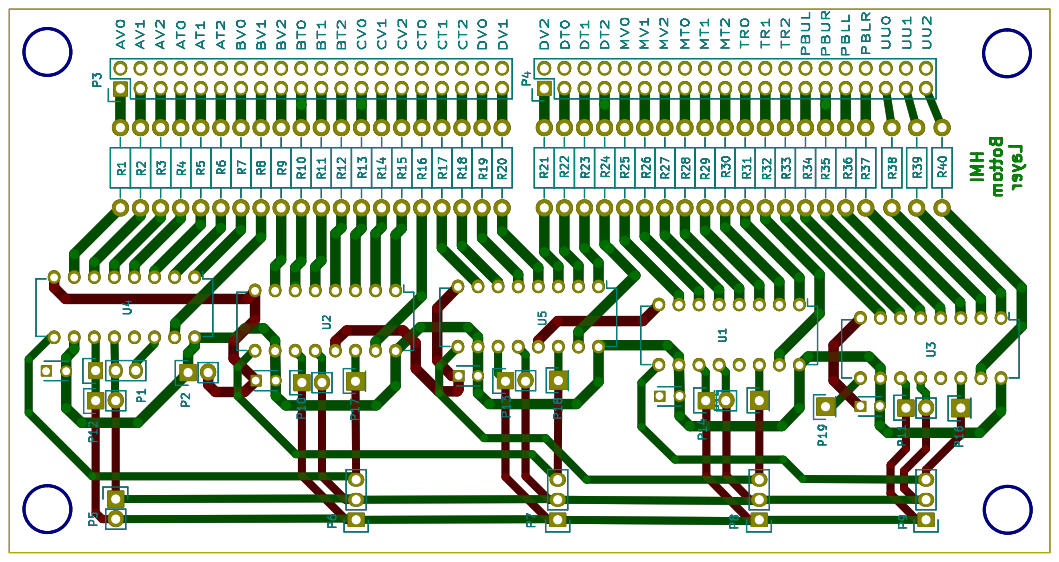
[picture p372: page 1]
