gratefulfrog/ArduGuitar/Ardu2/design/POC-3_MAX395/HMI/KicadProjects/Main HMI Circuit/PCB 00 no fill.pdf

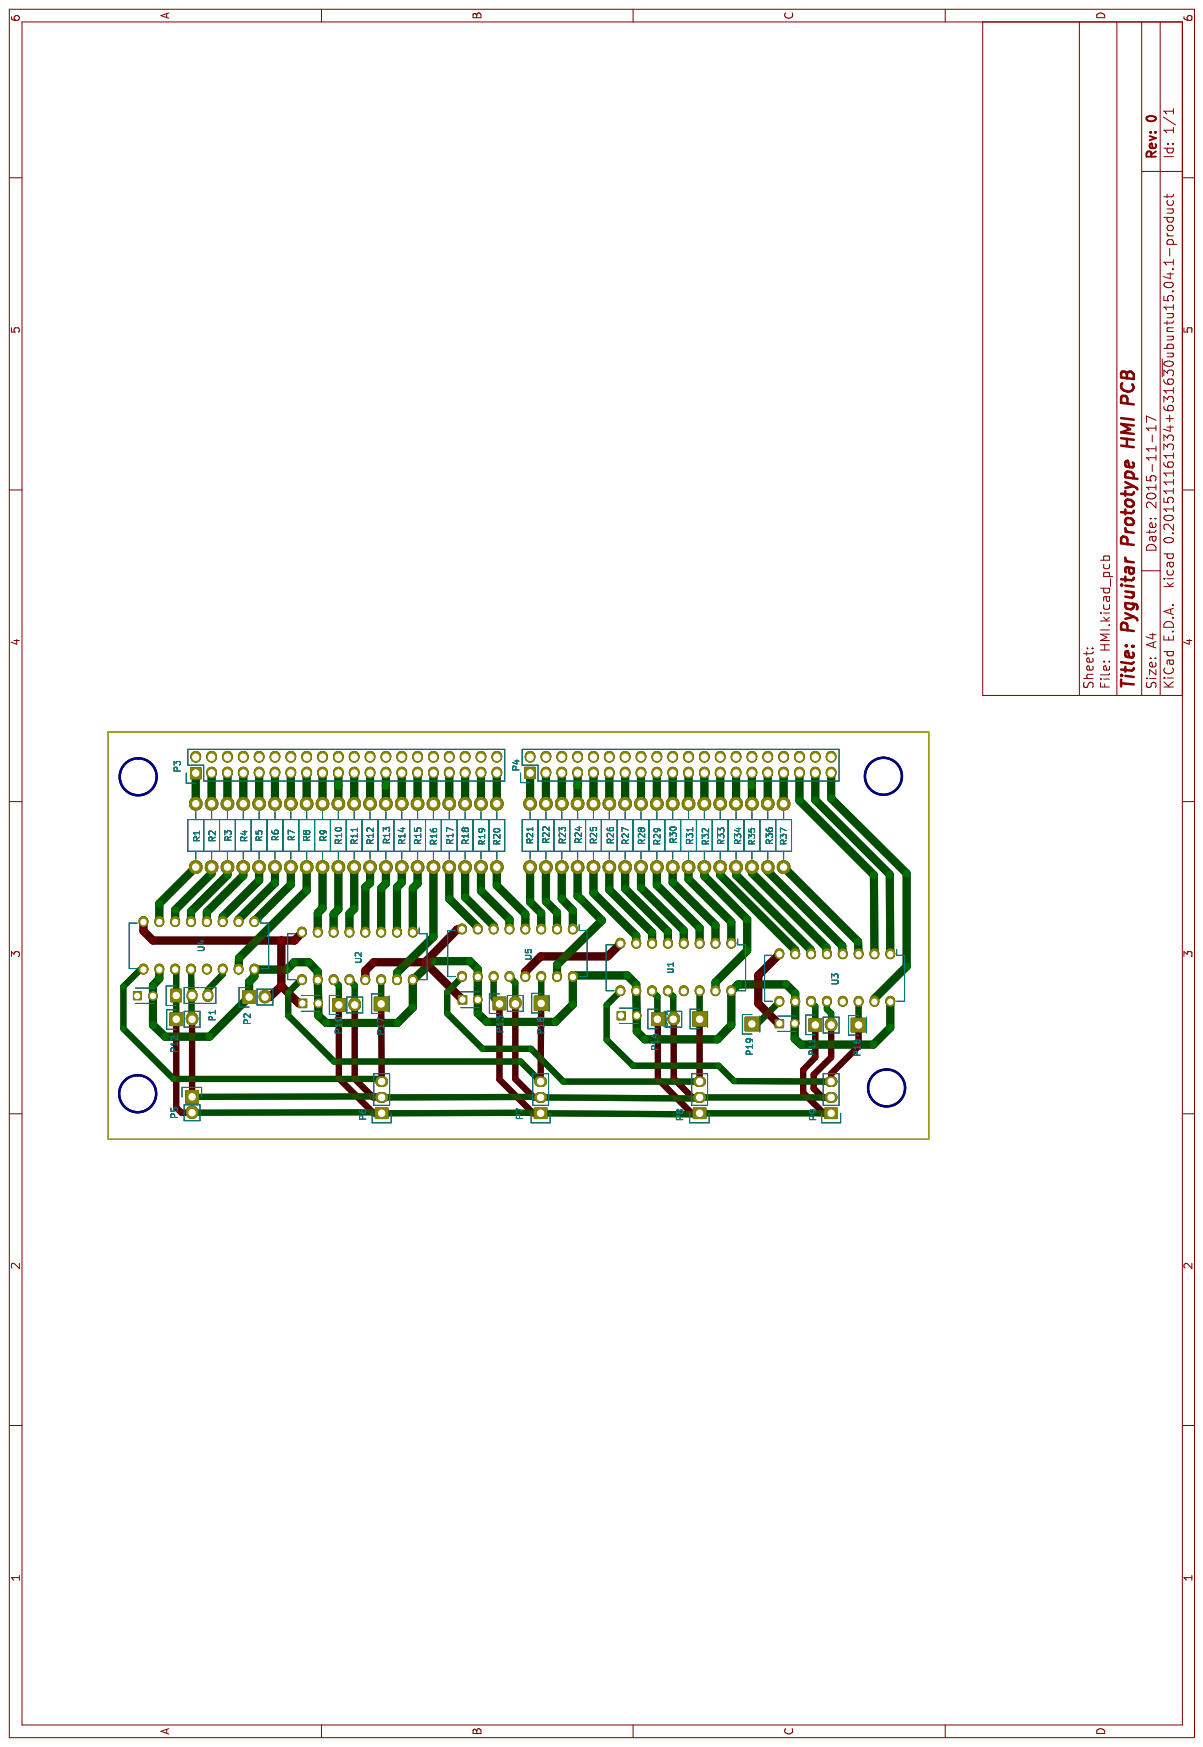
[picture p373: page 1]
