gratefulfrog/ArduGuitar/Ardu2/design/POC-2/SwitchArray/4316AnalogSwitchArrayBreadBoard/GERBER/StencilTopView.pdf

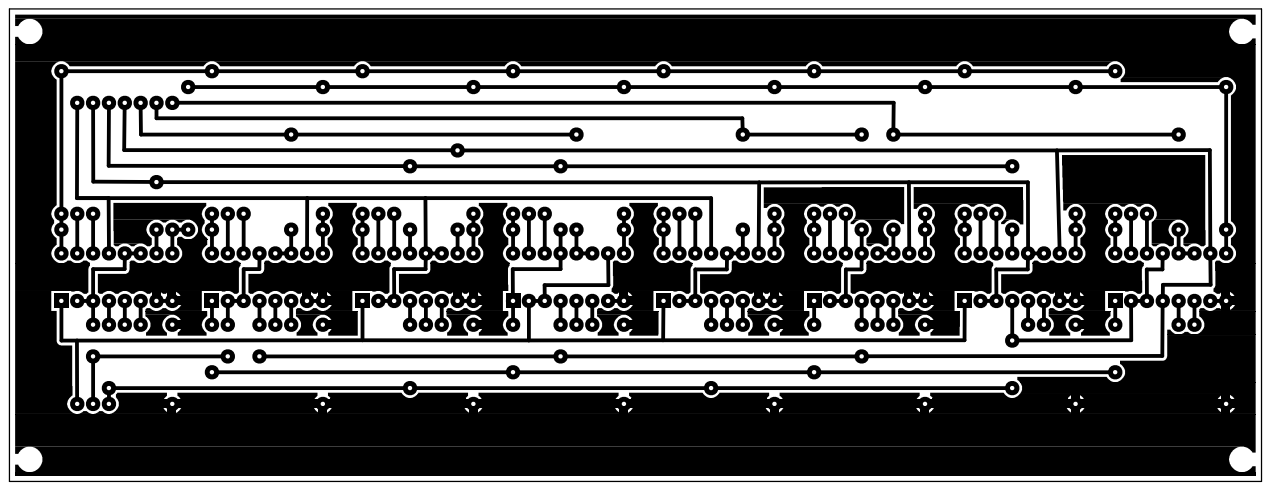
[picture p374: page 1]
