gratefulfrog/ArduGuitar/Ardu2/design/POC-2/SwitchArray/SwitchBoard/SPDT-JUMPER-Switch-Array-PCB-GERBER-Big-Pads/silkTop.pdf

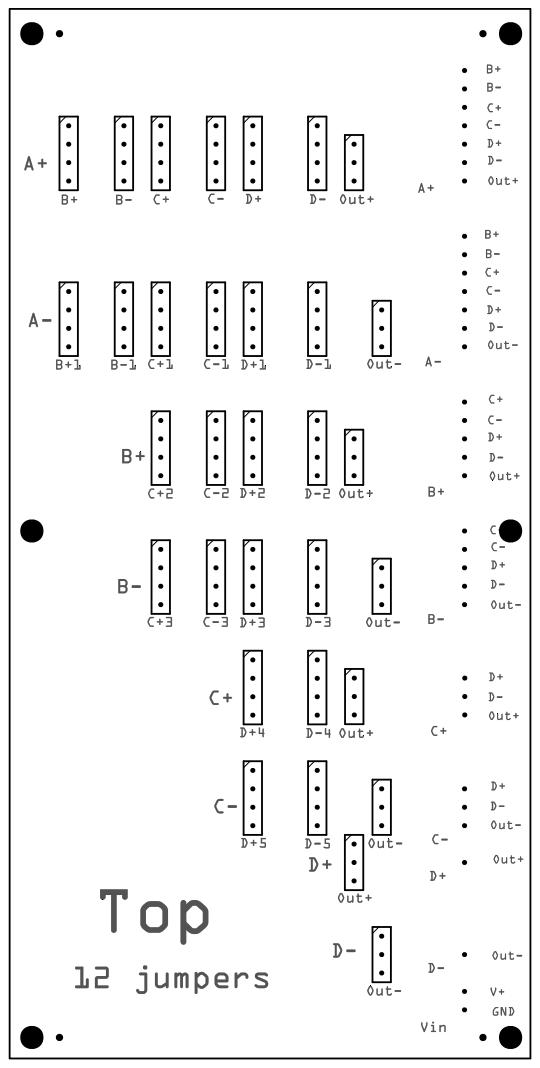
[picture p375: page 1]
