gratefulfrog/ArduGuitar/Ardu2/design/POC-2/SwitchArray/SwitchBoard/SPDT-JUMPER-Switch-Array-PCB-GERBER-Big-Pads/StencilTopView.pdf

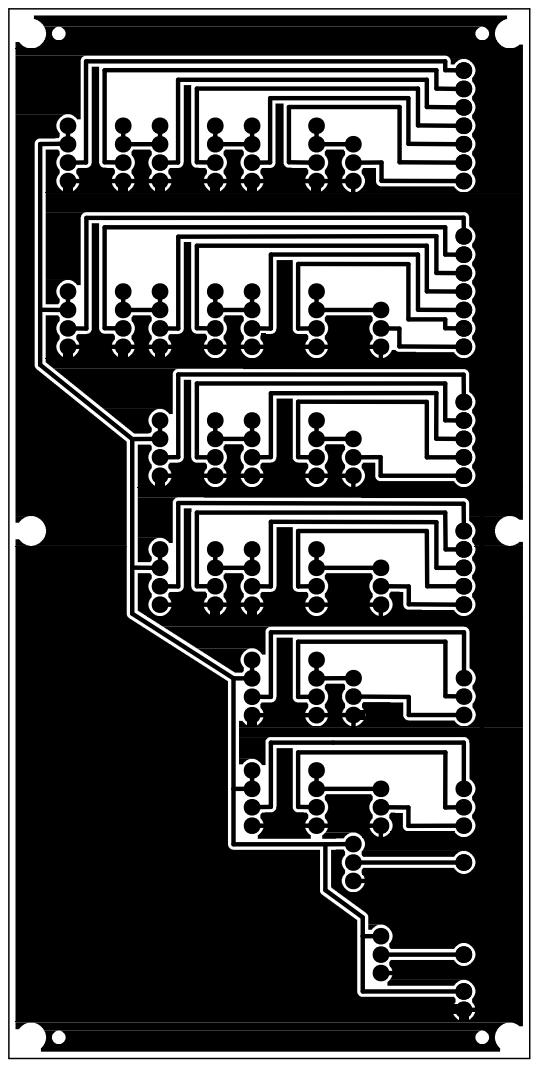
[picture p376: page 1]
