gratefulfrog/ArduGuitar/arduino/Layouts/ArduStomp/EnclosureDesign/2D/BoxTest/BoxTest2kerf_0_1.pdf

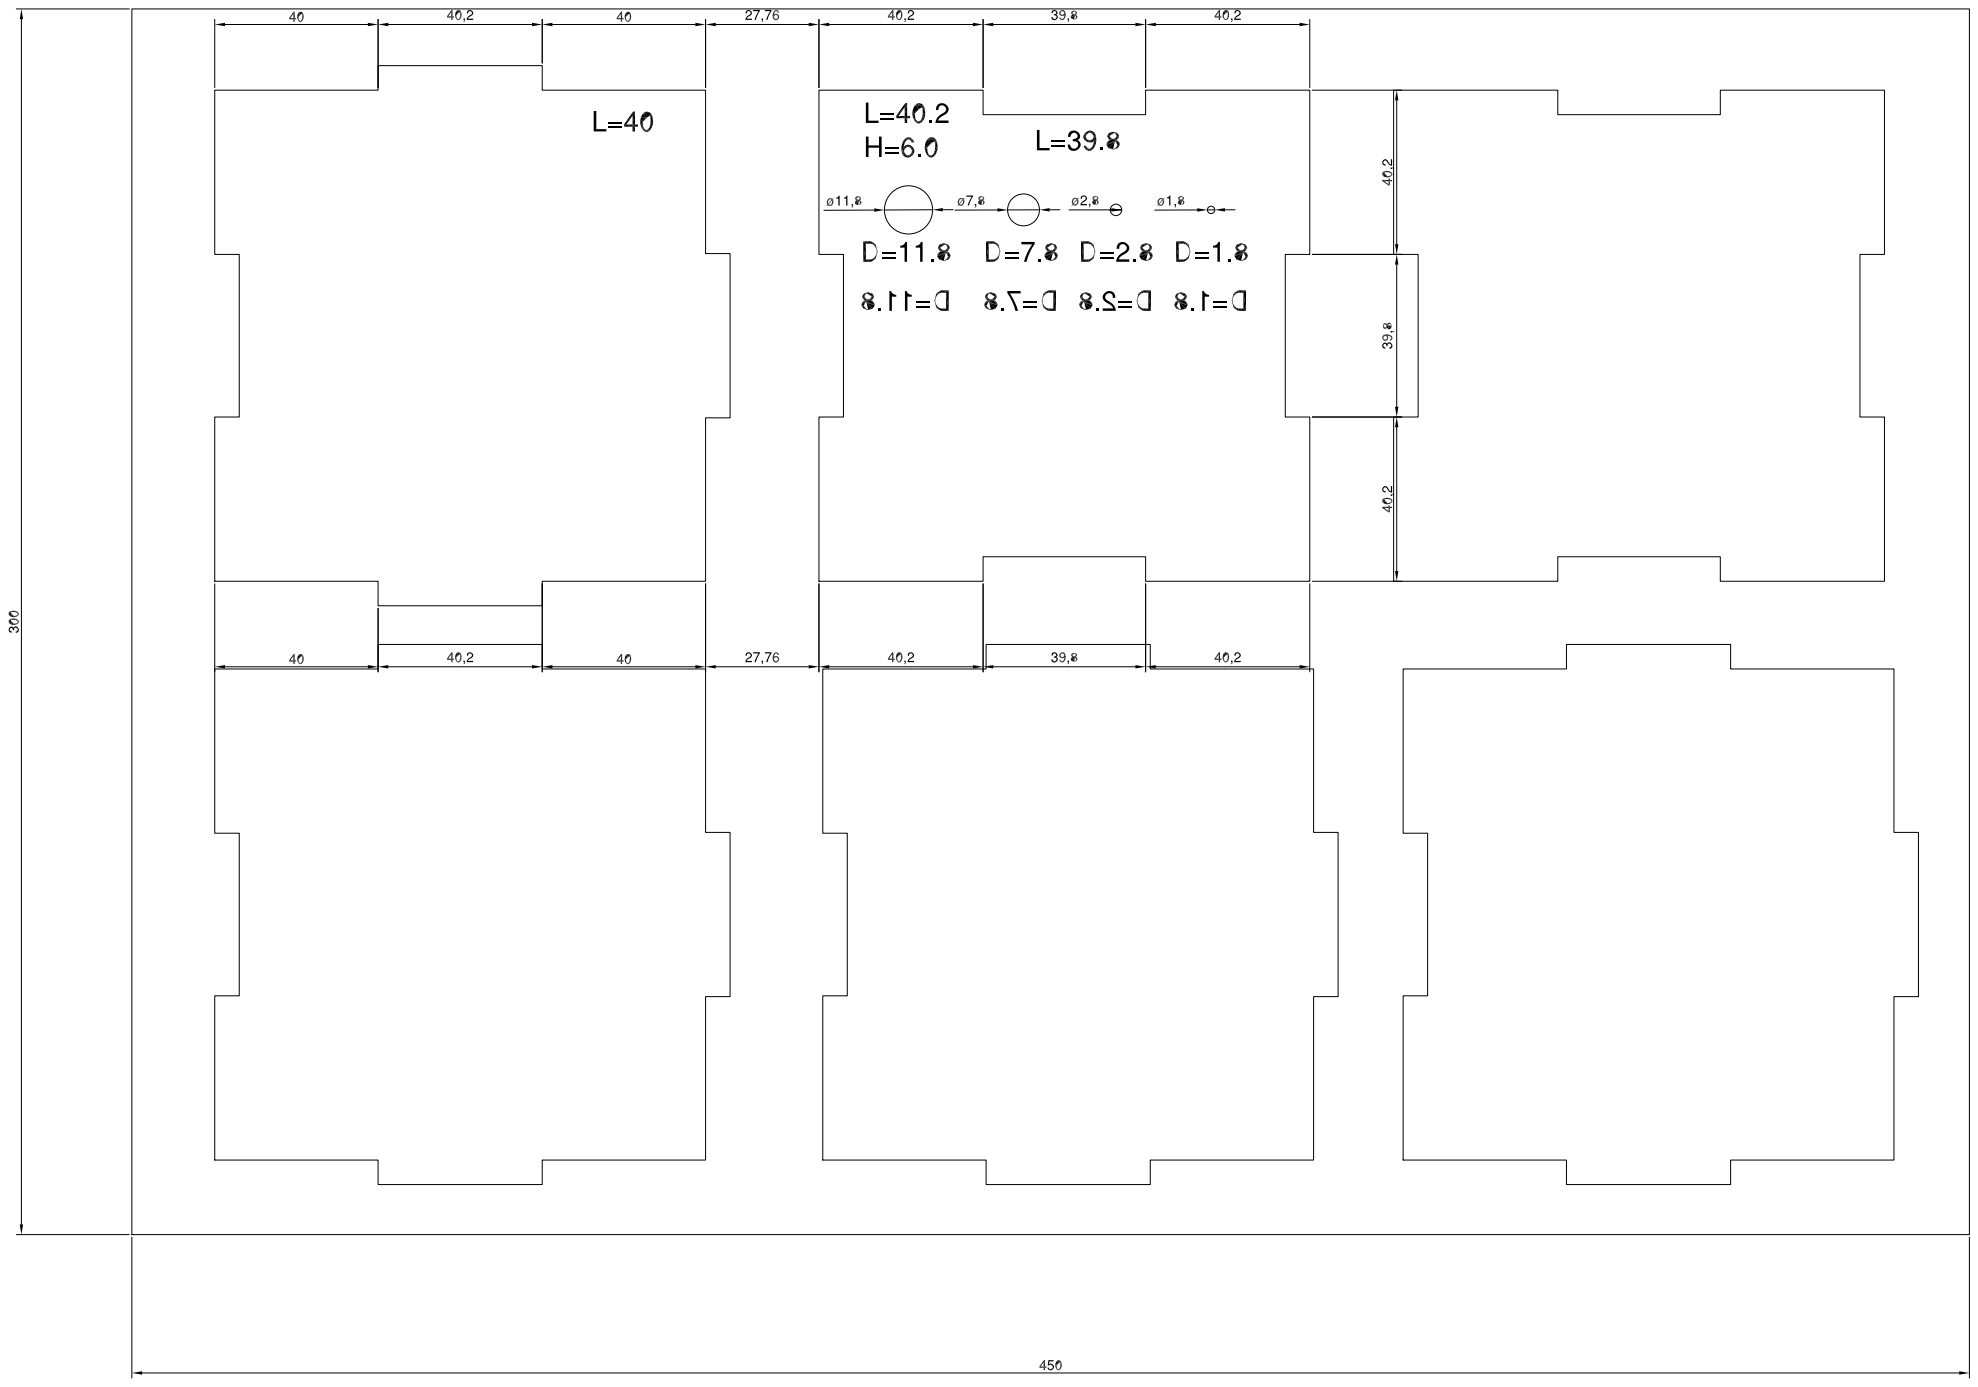
[picture p377: page 1]
