gratefulfrog/ArduGuitar/arduino/Layouts/ArduStomp/EnclosureDesign/2D/BoxTest/BoxTest2kerf_0_125.pdf

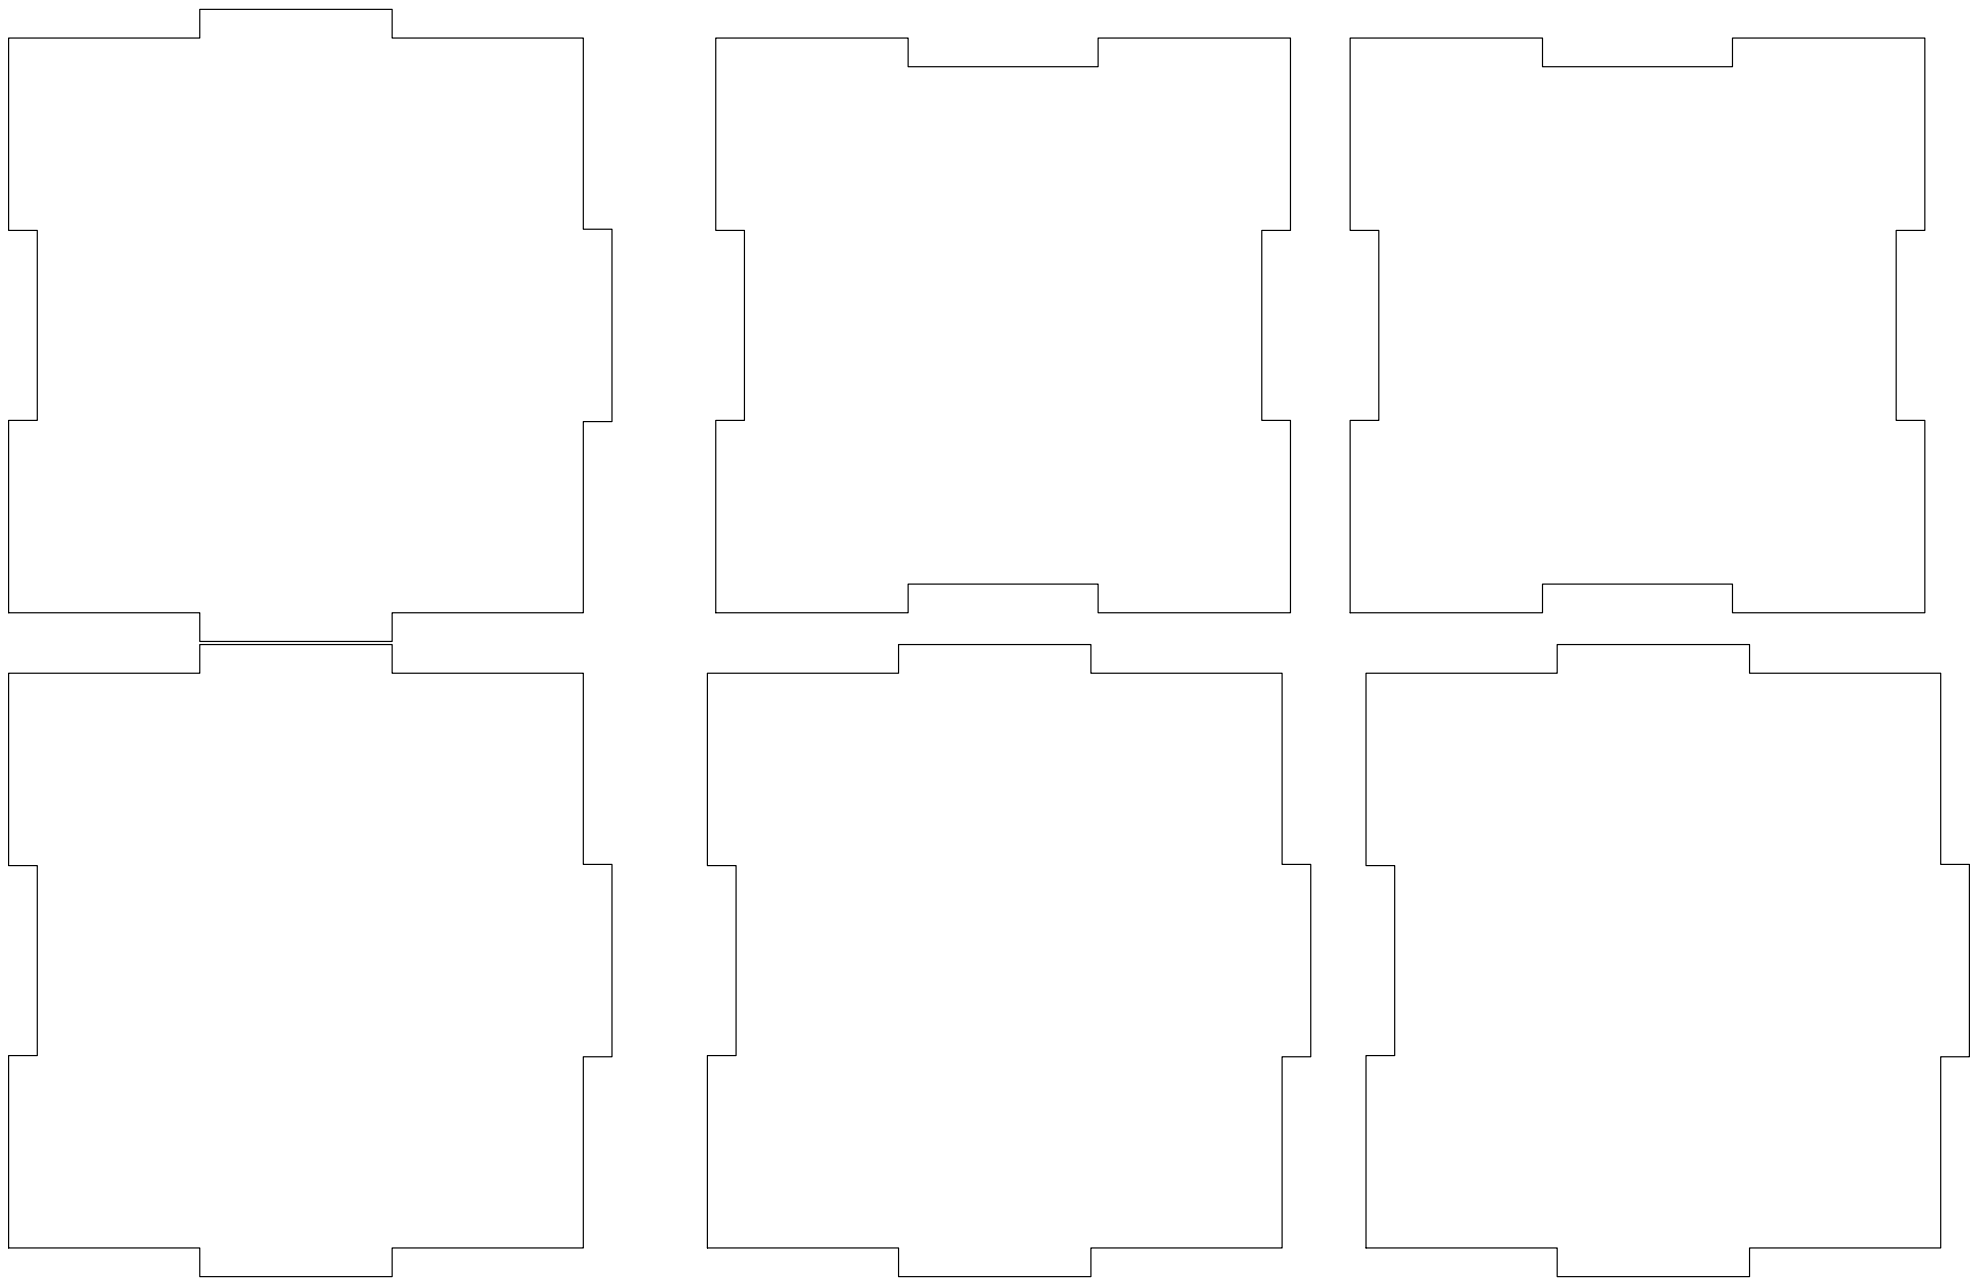
[picture p378: page 1]
