gratefulfrog/ArduGuitar/arduino/Layouts/ArduStomp/EnclosureDesign/2D/FullDesign09/back.pdf

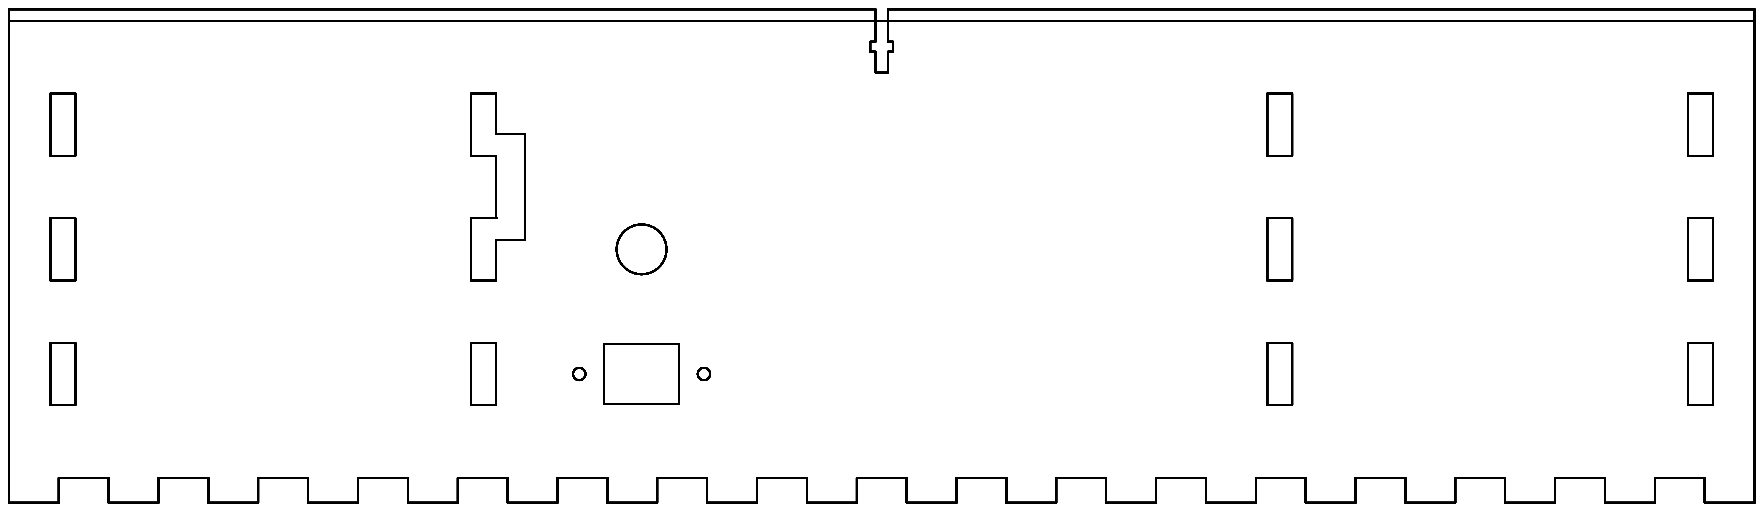
[picture p379: page 1]
