gratefulfrog/ArduGuitar/arduino/Layouts/ArduStomp/EnclosureDesign/2D/FullDesign09/inside-panels-and-slider.pdf

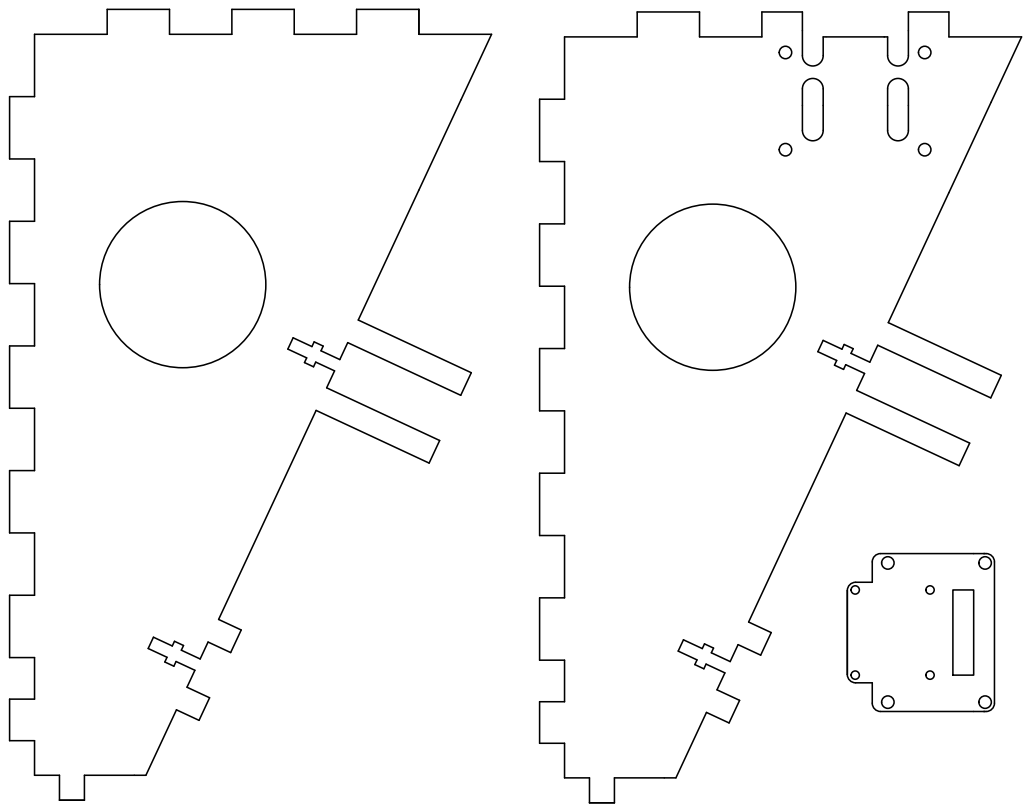
[picture p380: page 1]
