gratefulfrog/ArduGuitar/arduino/Layouts/ArduStomp/EnclosureDesign/2D/FullDesign09/L-1-2-3.pdf

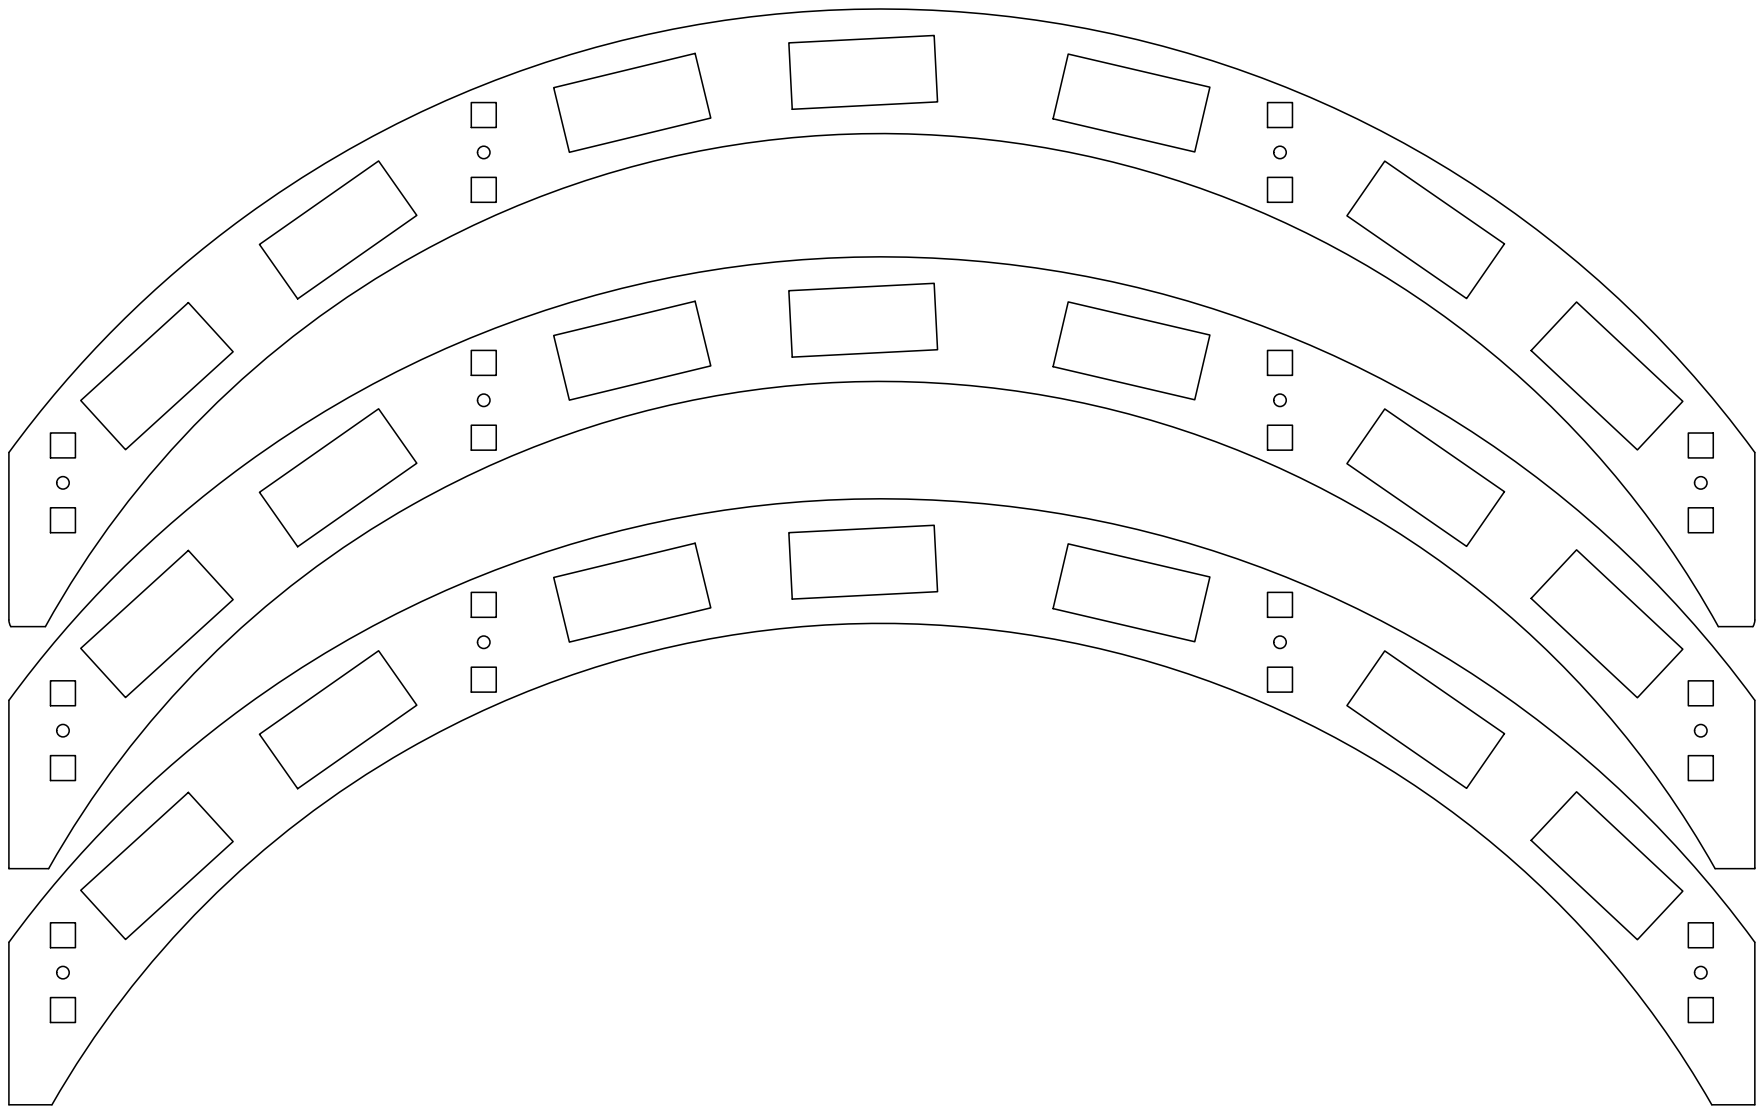
[picture p381: page 1]
