gratefulfrog/ArduGuitar/arduino/Layouts/ArduStomp/EnclosureDesign/2D/FullDesign09/L-4-5-6.pdf

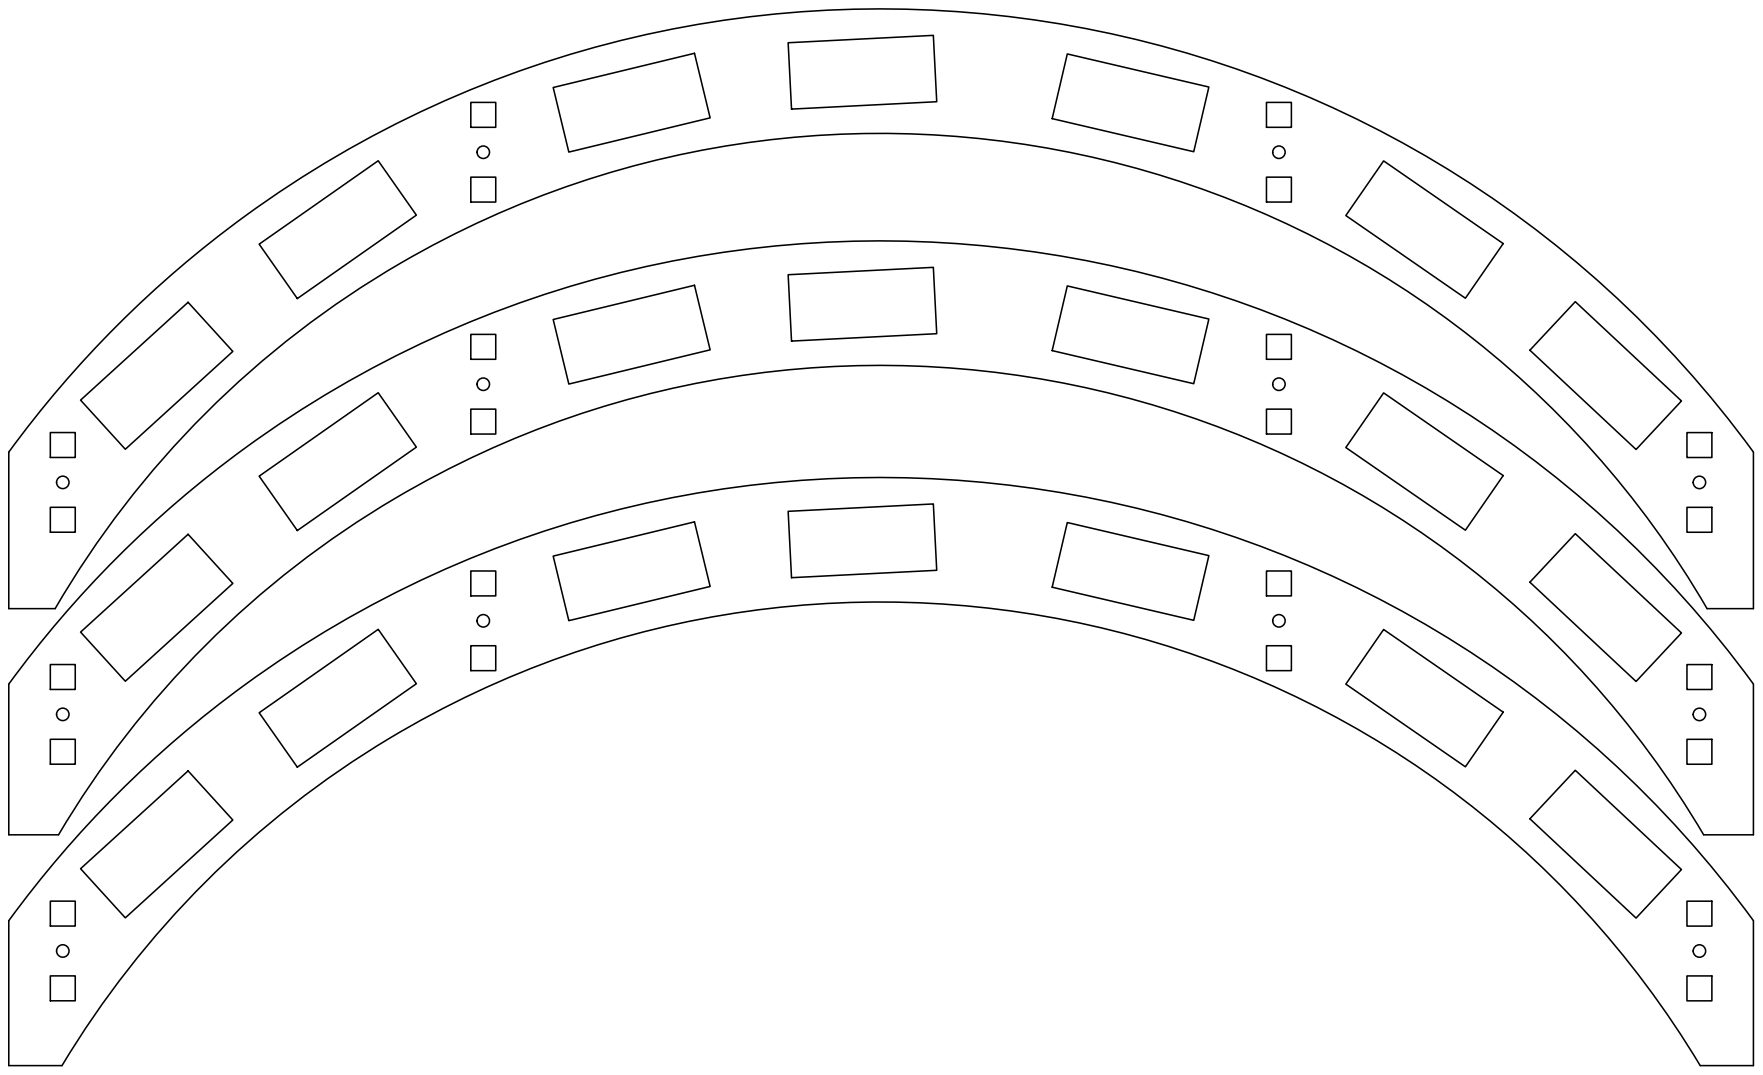
[picture p382: page 1]
