gratefulfrog/ArduGuitar/arduino/Layouts/ArduStomp/EnclosureDesign/3D/Arcs Model/Arcs19SomeKerfs.pdf

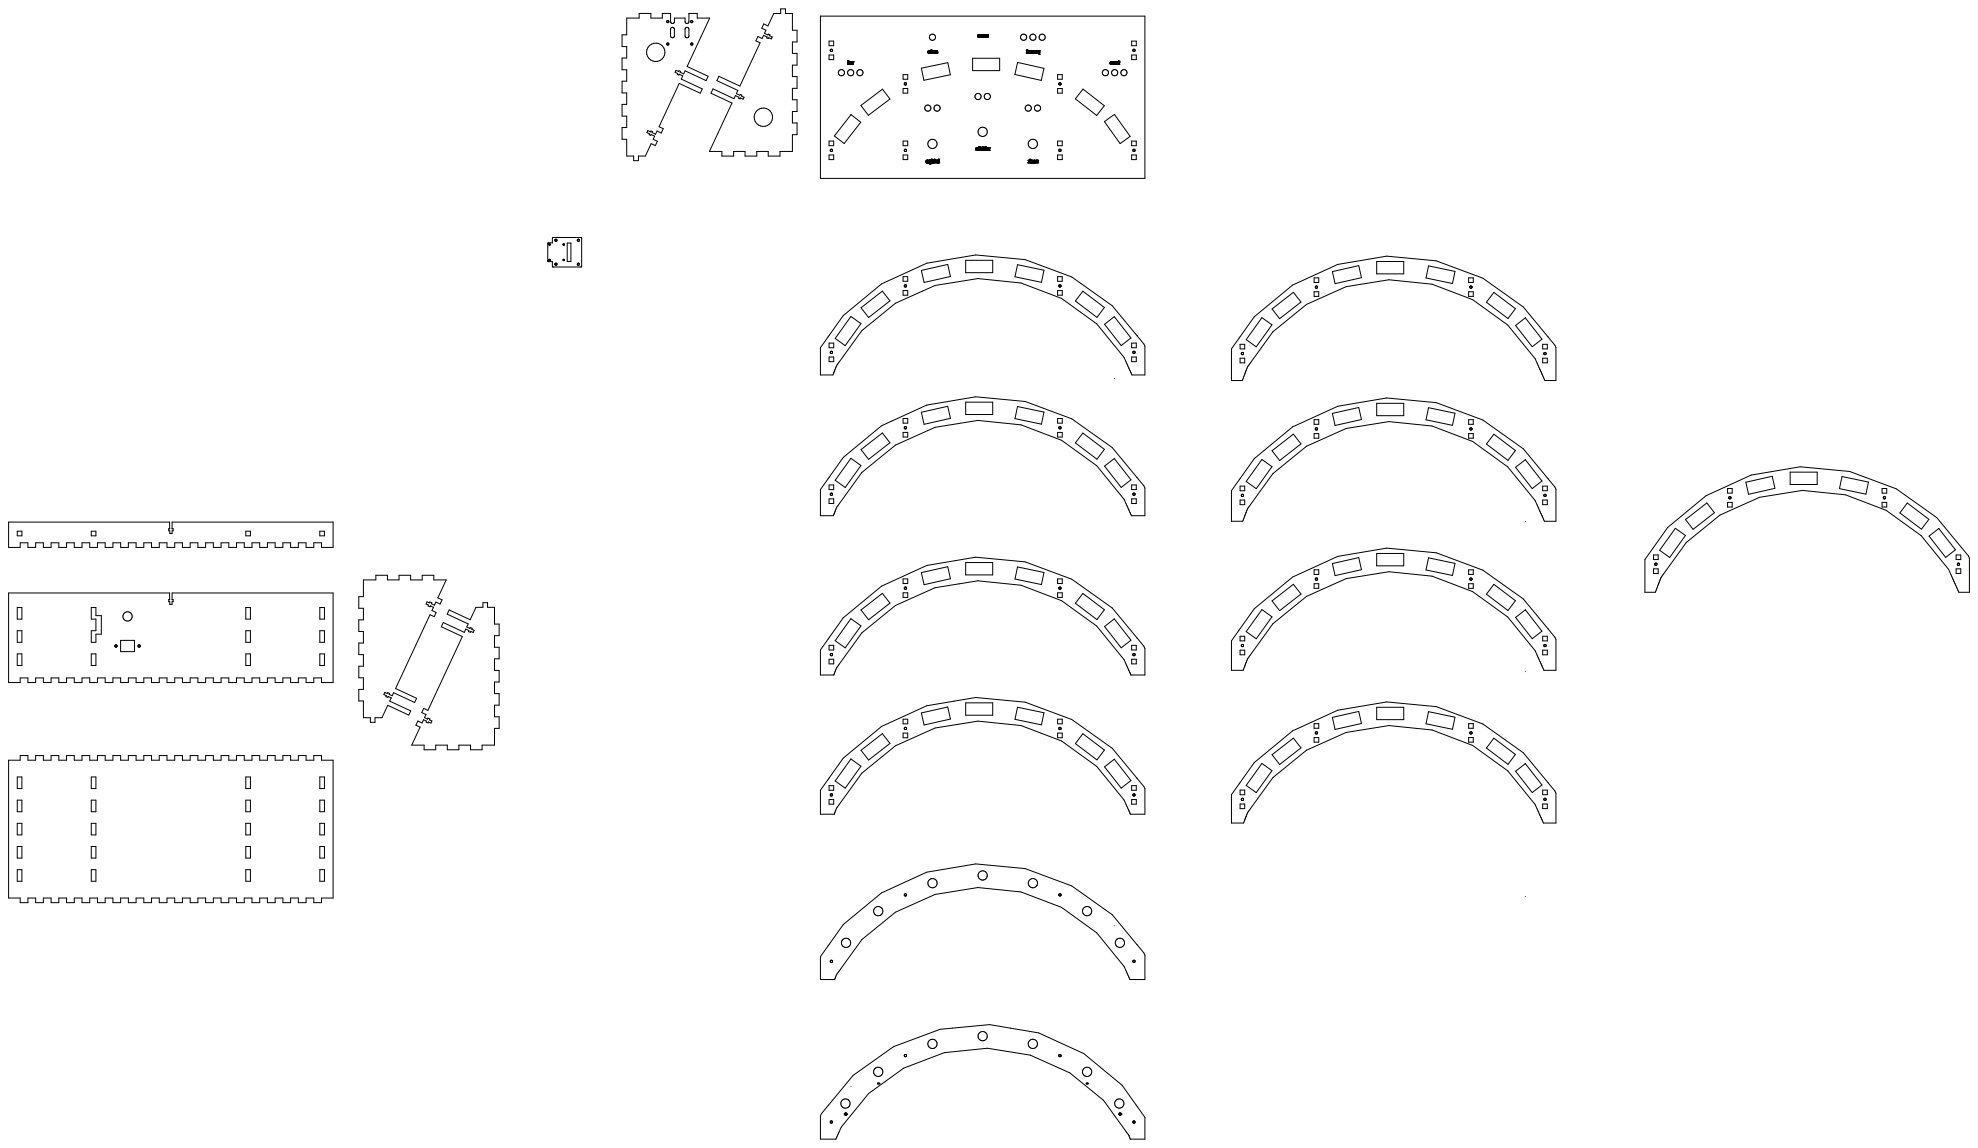
[picture p386: page 1]
