gratefulfrog/ArduGuitar/Ardu2/design/POC-3_MAX395/HMI/KicadProjects/Main HMI Circuit/Images/HMI LED PCB Schema.pdf

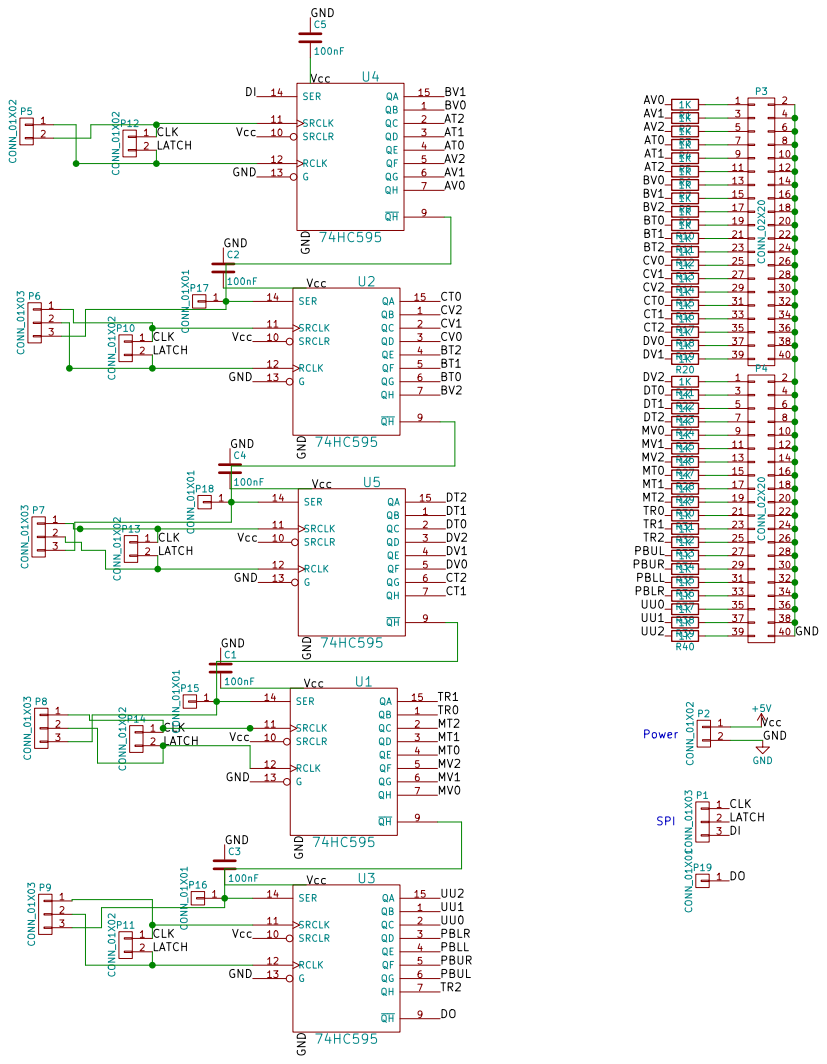
[picture p387: page 1]
