gratefulfrog/ArduGuitar/Ardu2/design/POC-3_MAX395/HMI/KicadProjects/PowerSupplyConnections Circuit/GERBER/Silk.pdf

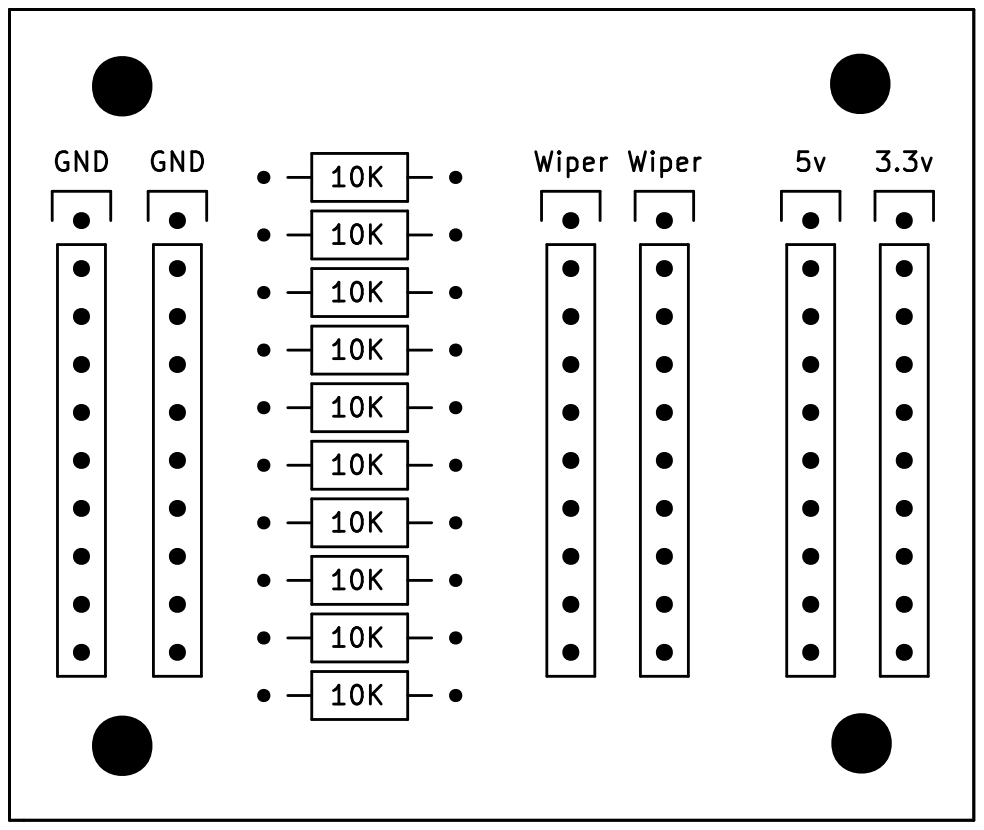
[picture p389: page 1]
