gratefulfrog/ArduGuitar/Ardu2/design/POC-3_MAX395/HMI/KicadProjects/PowerSupplyConnections Circuit/GERBER/Stencil.pdf

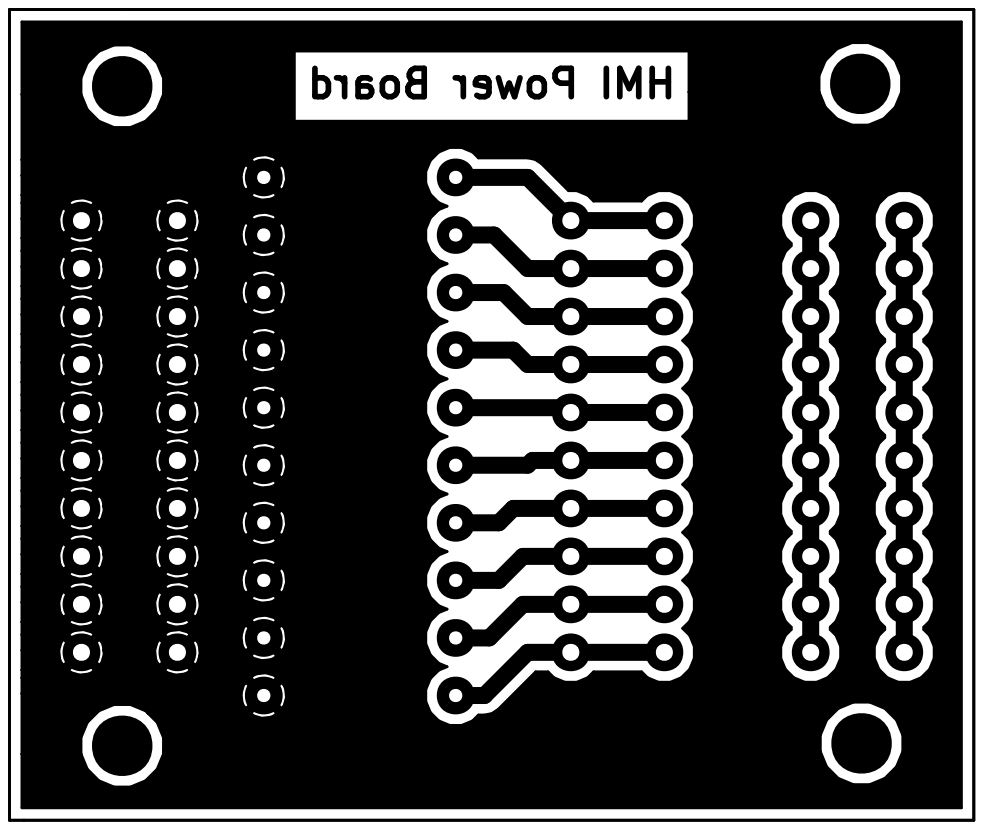
[picture p390: page 1]
