gratefulfrog/ArduGuitar/Ardu2/design/POC-3_MAX395/HMI/KicadProjects/PowerSupplyConnections Circuit/GERBER/Stencilx2.pdf

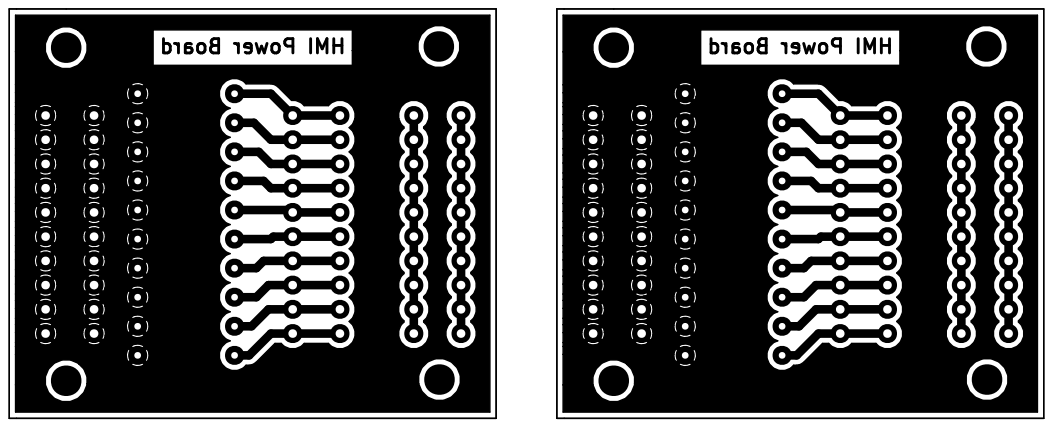
[picture p391: page 1]
