gratefulfrog/ArduGuitar/Ardu2/design/POC-3_MAX395/HMI/KicadProjects/Multi-PB-Debounce Circuit/Prints/SilkScreenFrontx4.pdf

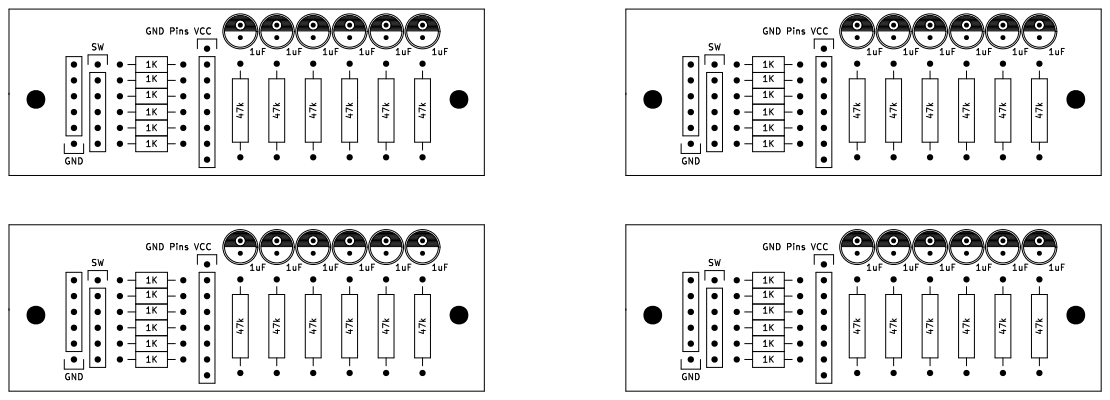
[picture p393: page 1]
