gratefulfrog/ArduGuitar/Ardu2/design/POC-3_MAX395/HMI/KicadProjects/2PB with Headers/Prints/Stencil.pdf

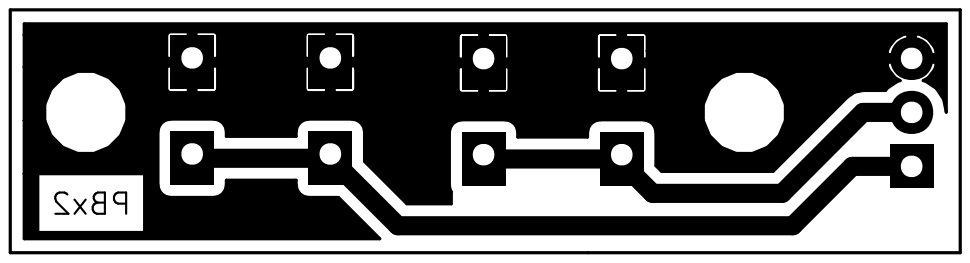
[picture p394: page 1]
