gratefulfrog/ArduGuitar/Ardu2/design/POC-3_MAX395/HMI/KicadProjects/Multi-PB-Debounce Circuit/Prints/Drilling Instructions.pdf

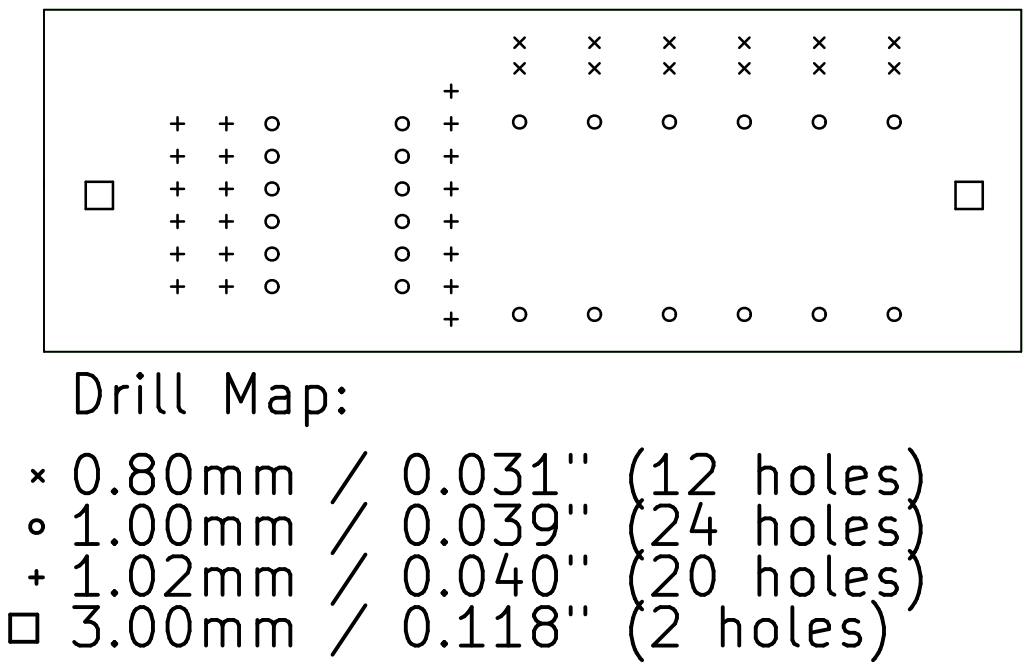
[picture p395: page 1]
