gratefulfrog/ArduGuitar/Ardu2/design/POC-3_MAX395/HMI/KicadProjects/Multi-PB-Debounce Circuit/Prints/SilkScreenFront.pdf

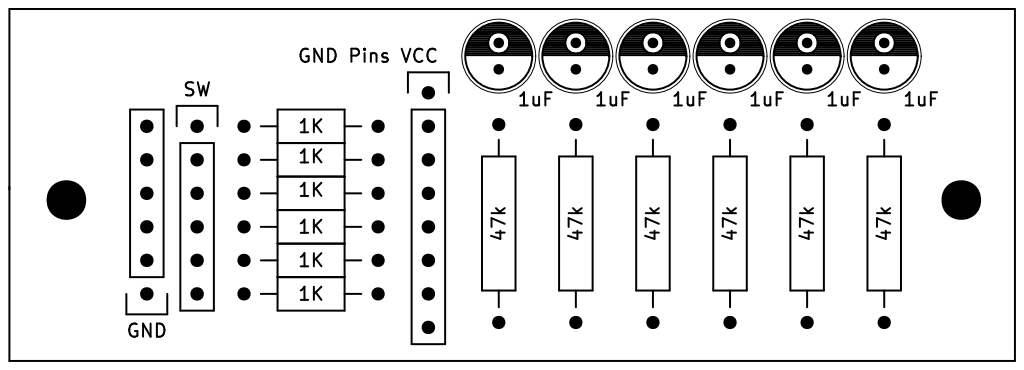
[picture p396: page 1]
