gratefulfrog/ArduGuitar/Ardu2/design/POC-3_MAX395/HMI/KicadProjects/Multi-PB-Debounce Circuit/Prints/Stencil.pdf

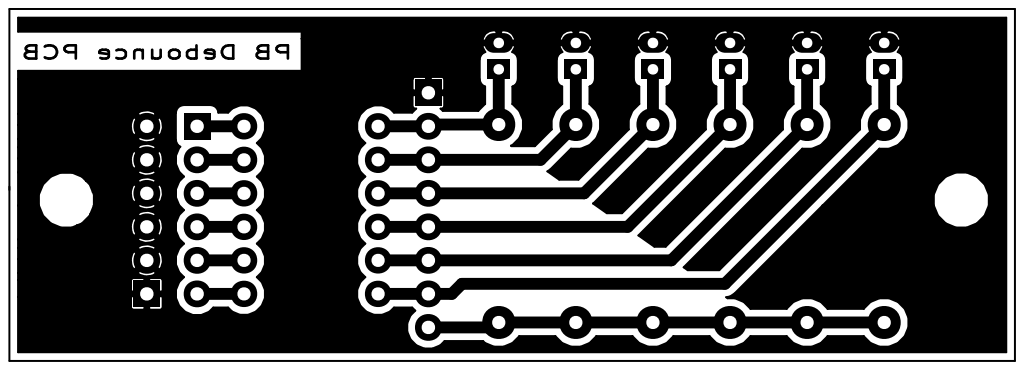
[picture p397: page 1]
