gratefulfrog/ArduGuitar/Ardu2/design/POC-3_MAX395/HMI/KicadProjects/2PB with Headers/Prints/Drilling Instructions.pdf

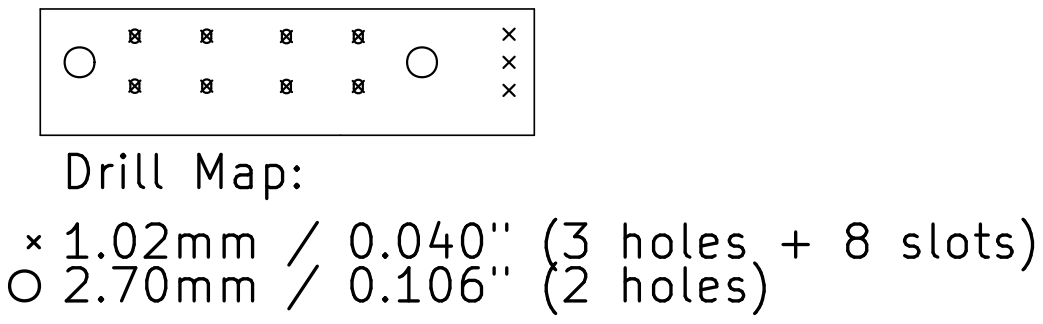
[picture p398: page 1]
