gratefulfrog/ArduGuitar/Ardu2/design/POC-3_MAX395/HMI/KicadProjects/Single HW Debounce PBs circuit /Printables/Drilling Instructions.pdf

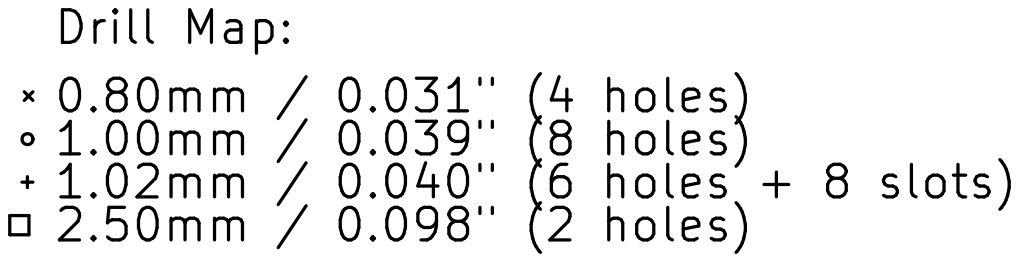
[picture p399: page 1]
