gratefulfrog/ArduGuitar/Ardu2/design/POC-3_MAX395/HMI/KicadProjects/Single HW Debounce PBs circuit /Printables/Test Image Mirror Y Axis.pdf

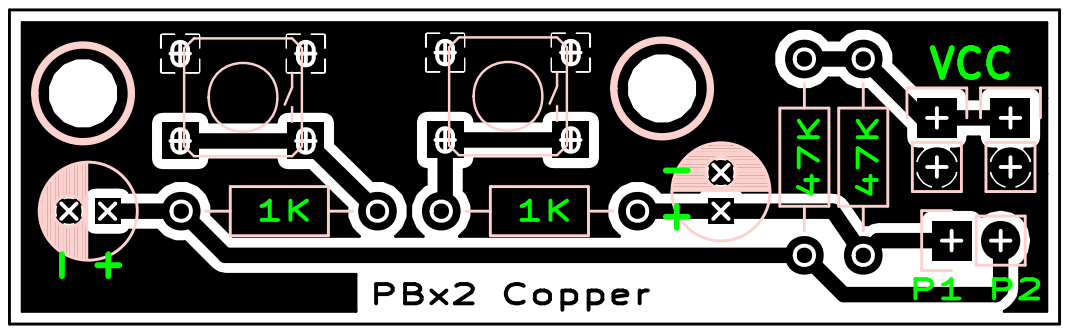
[picture p400: page 1]
