gratefulfrog/ArduGuitar/Ardu2/design/POC-3_MAX395/HMI/KicadProjects/Main HMI Circuit/GERBER/front silk.pdf

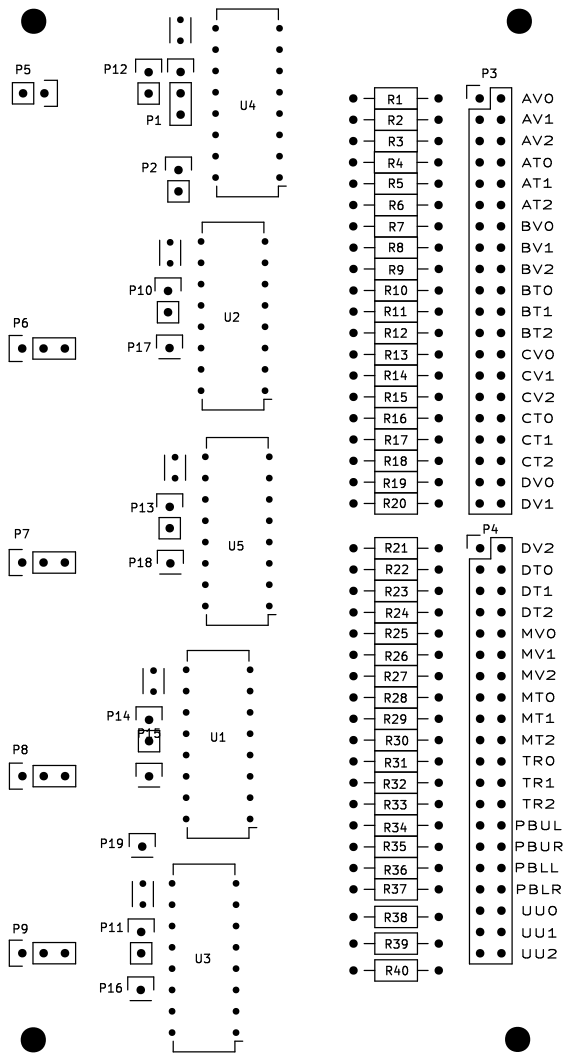
[picture p401: page 1]
