gratefulfrog/ArduGuitar/Ardu2/design/POC-3_MAX395/HMI/KicadProjects/Main HMI Circuit/GERBER/stencil.pdf

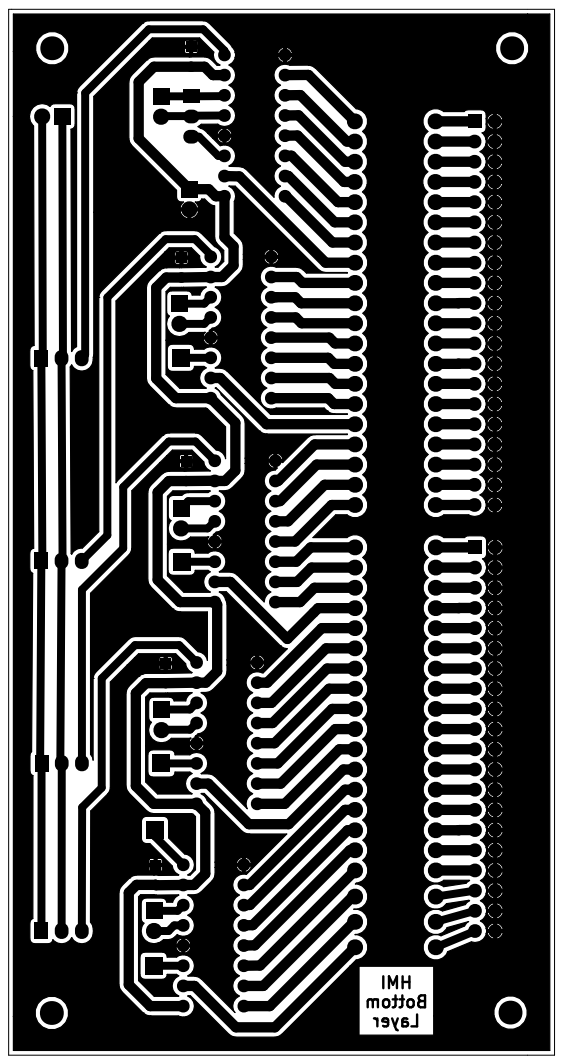
[picture p402: page 1]
