gratefulfrog/ArduGuitar/arduino/ArduStomp_05/actuatorClass.cpp

#include "actuatorClass.h"

deBounceButton::deBounceButton(byte pin){
  buttonPin = pin;
  buttonState = lastButtonState = LOW;
  lastDebounceTime = 0;
  pinMode(buttonPin,INPUT);
}  

boolean deBounceButton::pressed(){
  // read the state of the switch into a local variable:
  byte reading = digitalRead(buttonPin);

  // check to see if you just pressed the button 
  // (i.e. the input went from LOW to HIGH),  and you've waited 
  // long enough since the last press to ignore any noise:  

  // If the switch changed, due to noise or pressing:
  if (reading != lastButtonState) {
    // reset the debouncing timer
    lastDebounceTime = millis();
  } 
  
  if ((millis() - lastDebounceTime) > debounceDelay) {
    // whatever the reading is at, it's been there for longer
    // than the debounce delay, so take it as the actual current state:
    buttonState = reading;
  }
  
  boolean ret = (buttonState == LOW) && (lastButtonState == HIGH);
  // save the reading.  Next time through the loop,
  // it'll be the lastButtonState:
  lastButtonState = reading;
  
  return  ret;
}


actuatorClass::actuatorClass(int pin, doerFunPtr f): fPtr(f), b(pin){
  ;
}
void actuatorClass::update() {
  if(b.pressed()){
    (*fPtr)() ;
  }
}
