gratefulfrog/ArduGuitar/arduino/ArduStomp_10_0/ArduStomp_10_0.ino

//  -*-C++-*-
/* ArduStomp_10_0
 * 2014 02 02:
 *  all debugging removed.
 *  Loaded in Arduino Micro 2014 02 02 15:20
 *  tested stand alone, 2014 01 02 15:20
 *********************
 * rething after SRAM and PROGMEM issues:
 ** make it simpler
 ** make it more efficient in mem usage
 ** try to do everything static or at least without dynamic DE-allocations,
 ** use binary display for Bol and tone values! only 3 LEDS each!
 ** no: save this for the future ..allow for 2 LEDS on EACH Pup,
 * code to command the ARduGuitar from an arduino based stomp box.
 * integrating coms and BT
 */

#include <Arduino.h>
#include <SPI.h>
#include <ArduConf00.h>
#include <State.h>
#include <DebounceButton.h>
#include <outQueueStatic.h>
#include <ArduComOptStatic.h>
#include <RN42autoConnectOpt.h>
#include <SD.h>
#include <SDReader.h>
#include <LEDManager.h>
#include <Actuator.h>
#include <ArduStomp.h>
#include <outils.h>


///////////////////////////////////////////////////////
void setup(){
  Serial.begin(115200);
  //while(!Serial);
  //delay(5000);
  //Serial.println("Starting");
  //freeRam();

  ArduStomp::init();
  //Serial.println("XArduStomp::init");
  //freeRam();
  
  Actuator::init(ArduStomp::as);
  //Serial.println("XActuator::init");
  //freeRam();
  ArduStomp::as->doPreset();
  //Serial.println("Xsetup");
}

void loop(){
  if(Actuator::allOK){
    for (byte b = 0;b<NB_ACTUATORS;b++){
      //freeRam();
      if (Actuator::actuators[b] && 
          Actuator::actuators[b]->update()){
	break;
      }
    }
  }
  if(Actuator::allOK){
    ArduStomp::as->checkAuto();
    ArduStomp::as->com->stepLoop();
  }
  else{ // it's broken, tell the world!
    ArduStomp::as->stepAlarm();
  }
  //checkRam();
}
