gratefulfrog/ArduGuitar/arduino/ArduStomp_03/biInc.h

/* a general purpose value holder class
 * such that Zero is the min
 * max is assgined const at instatiation
 * inc can take positive and negative values but always incs by the step of One
 */

#ifndef BIINC_H
#define BIINC_H

#include <Arduino.h>

class biInc {
  protected:  
    static const int _minVal = 0;
    const int _maxVal,
              _incVal;
    int _val;
    
  public:
    biInc(int mx); // min is zero and start is zero
    int getVal() const;
    void setVal(int v);
    int inc(int i);
};

#endif
