gratefulfrog/ArduGuitar/Ardu2/design/POC-3_MAX395/pyboard/V1_WithHMI/pyboard_no_debug/hardware.py

# hardware.py
# classes corresponding to physical objects in the system
# * BounceMgr:
# * ShuntControl
# * SelectorInterrupt  (added 2016 08 24)
# * HWDebouncedPushButton
# * ShakeControl (3-axis shake controller)
# * TremVib  (tremolo and vibrato mgt class)
# * LcdDisplayI2C  (added 2016 09 13)
# * TrackBall (added 2016 08 26)
# * SplitPot & SplitPotArray (added 2016 08 30)
#### obsolete or unused ###
# * LCDDisplay6Wire (added 2016 06 11), moved 2016 09 13
# * Selector
# * Illuminator
# * SWDebouncedPushbutton
# * IlluminatedPushbutton
# * VoltageDividerPot
#####
# 2016 12 28: added polling to pb and selector
# 2016 12 28: create class BounceMgr
#           : added counter to shuntControl
# 2016 12 29: added stableValue(pin) function to try to fix spurious pb triggering
###############################################

from pyb import millis, Pin, Timer, delay, Accel, LED, ADC, ExtInt, I2C,enable_irq,disable_irq
#from pyb_gpio_lcd import GpioLcd
from pyb_i2c_adafruit_lcd import I2cLcd
from dictMgr import shuntConfDict
from state import State
from q import EnQueueable
from outils import *

#import micropython
#micropython.alloc_emergency_exception_buf(100)


def stableValue(pin,stabilityPeriod=20):
    res = pin.value()
    if res:
        return res
    readTime = millis()
    while(millis()-readTime < stabilityPeriod):
        if res != pin.value():
            res = pin.value()
            readTime = millis()
        delay(1)
    return res

class ShuntControl:
    """simple class providing on/off functionality of a vactrol
    controlled by a pyboard bin.
    """
    def __init__(self, confData):
        p = Pin(confData['p'] , mode=Pin.OUT_PP)
        tim = Timer(confData['t'],freq=confData['f'])
        self.control = tim.channel(confData['c'],Timer.PWM, pin=p)
        self.control.pulse_width_percent(0)
        self.shuntCount = 0
        
    def shunt(self, percent = 20):
        #State.printT('Shunting:\t' + str(self.shuntCount))
        self.control.pulse_width_percent(percent)

    def unShunt(self):
        #State.printT('UNshunting:\t' + str(self.shuntCount))
        self.shuntCount +=1
        self.control.pulse_width_percent(0)

    def __repr__(self):
        return 'ShuntControl: ' + '\n\t'  \
            'Timer.channel:\t' + str(self.control)


# SelectorInterrupt
# support for 3 or 5 ... position selector switches
class SelectorInterrupt (EnQueueable):
    """ Usage:
    >> pinIds = ('X1','X2','X3')
    >> s = SelectorInterrupt(pinNames,id,q)   
    >> s.currentPostion
    3
    >> # move switch
    >> s.setPostion()
    >> s.currentPostion
    0
    -----
    wiring:
    common on switch to GND
    position 0 side wire to pin 0
    position 2 side wire to pin 1
    position 4 side wire to pin 2
    """
    
    # this defines the switch position pin values
    # note: it is a diction of dictionaries, where at the top level we have number of pins,
    # then at next level the mapping of pin values to positions
    masterDict = {2: {(0,1): 0,  # position 0, i.e. left: left pin is GND
                      (0,0): 1,  # position 1, i.e. middle: left and right pins are GND
                      (1,0): 2}, # position 2, i.e. right: right pin is GND
                  3: {(0,1,1): 0,  # position 0, i.e. left: left pin is GND
                      (0,0,1): 1,  # position 1, i.e. left/middle: left and middle pins are GND
                      (1,0,1): 2,  # position 2, i.e. middle: middle pin is GND
                      (1,0,0): 3,  # position 3, i.e. middle/right: middle & right pins are GND
                      (1,1,0): 4}} # position 4, i.e. right: right pin is GND

    
    def __init__(self,pinNames,id,q,usePolling): #, bMgr):
        """create an instance of a 3 or 5 position switch connected to the 
        pins provided.
        Pins should be configured as Pin('X1', Pin.IN, Pin.PULL_UP)
        len(pins) should be 2, for 3 postions, 3, for 5 positions
        incorrect arguments raise exceptions
        """
        EnQueueable.__init__(self,EnQueueable.CONF,q)
        if len(pinNames) not in (2,3):
            raise Exception('invalid nb of pins', pinNames)
        self.pinLis =  [Pin(p, Pin.IN, Pin.PULL_UP) for p in pinNames]
        self.truthDict = SelectorInterrupt.masterDict[len(pinNames)]
        self.id = id
        self.currentPosition = 0
        self.setPosition()  # reads the pin values and deduces current switch position
        #self.bounceMgr = bMgr
        if not usePolling:
            self.extIntVec = [None for p in pinNames]
            for i in range(len(pinNames)):
                self.extIntVec[i]=ExtInt(pinNames[i],
                                         ExtInt.IRQ_RISING_FALLING,
                                         Pin.PULL_UP,
                                         self.callback)
            
    def callback(self,unusedLine):
        irq_state = disable_irq()
        self.push(self.id)
        enable_irq(irq_state)
        #print('Push Selector:%d'%self.id)
        #State.printT('SelectorCallBack:\t',self.id)
        #print('SelectorCallBack:\t',self.id)
        
    def setPosition(self):
        """ reads the pin values and deduces current switch position
        in case of failure, exception is raised.
        """
        #tLis  = [p.value() for p in self.pinLis]
        error = True
        while (error):
            try:
                tLis  = [stableValue(p) for p in self.pinLis]
                self.currentPosition = self.truthDict[tuple(tLis)]
                error = False
            except KeyError:
                #print ('Selector Exception ignored!')
                error = True
                delay(1)

    def poll(self):
        #if not self.bounceMgr.ready():
        #    return
        prevPos = self.currentPosition
        self.setPosition()
        if (prevPos != self.currentPosition):
            #self.bounceMgr.trigger()
            self.callback(None)
        
    def __repr__(self):
        return 'Selector:' + \
            '\n\tpostion:\t' + str(self.currentPosition) +\
            '\n\tpinLis:\t' + str(self.pinLis) +\
            '\n\ttruthTable:\t' + str(self.truthDict)  + '\n'

# HWDebouncedPushButton
# uses interrupts and queueing to indicate a push

class HWDebouncedPushButton(EnQueueable):
    """
    an interrupt generating pushbutton, using the q to manage actions
    avoiding repeated pushes using a lock and a time delay
    """
    def __init__(self,pinName,q,usePolling): #,bMgr):
        EnQueueable.__init__(self,EnQueueable.PB,q)
        if  usePolling:
            self.pin = Pin(pinName,Pin.IN,Pin.PULL_UP)
        else:
            self.extInt = ExtInt(pinName, ExtInt.IRQ_FALLING, Pin.PULL_UP, self.callback)
        self.id = State.pinNameDict[pinName][1]
        #self.debugPinName = pinName
        #self.locked = False
        #self.bounceMgr = bMgr
        
    def callback(self,unusedLine):
        #if self.locked:
        #    return
        #self.locked = True
        irq_state = disable_irq()
        self.push(self.id)
        enable_irq(irq_state)
        #print('top5:\t',self.top5)
        #secondByte=0
        #lower3=self.id
        #pushee =  ((self.top5 |lower3)<<8)|(0xFF & (secondByte if secondByte>=0 else 256+secondByte))
        #print('Pushing:\t',bin(pushee))
        #print('Push PB:%d'%self.id)
        #self.locked = False
    """    
    def poll(self):
        if not self.bounceMgr.ready():
            return
        if not self.pin.value():
            self.bounceMgr.trigger()
            self.callback(None)
    """
    def poll(self):
        if not stableValue(self.pin):
            self.callback(None)
            
    def __repr__(self):
        return 'HWDebouncedPushButton:\n  ID:\t%d'%(self.id)


# PushButtonArray
# an array of HWDebouncedPushputton
class PushButtonArray():
    def __init__(self,q,usePolling): #,bMgr):
        self.pbVec = []
        for pinName in State.PBPinNameVec:
            self.pbVec.append(HWDebouncedPushButton(pinName,q,usePolling)) #,bMgr))

    def poll(self):
        for pb in self.pbVec:
            pb.poll()
            
    def __repr__(self):
        res = 'PushButtonArray:\n'
        for pb in self.pbVec:
            res += repr(pb) +'\n'
        return res
                    
class ShakeControl1:
    """ 
    provides single axis shake control; when there is shake in the
    axis, then the appropriate toggle function is called.  IF there is no shake for
    a timeout period, then the appropriate off function is called.
    """

    pThreshold = 5  # values for 1.5g Freescale accelerometer on [+31,-32]
    nThreshold = -5
    readDelay = 20 # min interval between reads in milliseconds maybe try 5ms???
    timeOut = 2000  # interval after which to call offFunc and turn off associated control
    
    def __init__(self, readFunc, toggleFunc, offFunc,
                 pt=State.AccpThreshold,nt=State.AccnThreshold,rd=State.AccreadDelay,to=State.AcctimeOut,
                 autoOff=False):
        """ 
        Instance Creation:
        provides default values for thresholds, read delay, and timeout
        other args are:
         readFunc: will be called to read the value of the accelerometer
         toggleFunc: will be called when the value read is in a zone that is 
                     different from previous zone, but only if over a threshold
         offFunc: will be called in case of inactivity lasting for the timeout period
        baseVal: is used to cancel gravity in each axis, so the accelerometer will read
                 as if there were no gravity.
        prevZone: is the zone value from when we last read the accelerometer
        lastActionTime: is milis since a toggle or an off action was called
        lastReadTime: is millis since call to readFunc (failed or not)
        autoOff: if True, turn off after timeout
        """
        self.rf = readFunc
        self.tf = toggleFunc
        self.of = offFunc
        self.pt = pt
        self.nt = nt
        self.rd = rd
        self.to = to
        self.autoOff=autoOff
        self.baseVal  = 0
        self.prevZone = 0
        self.lastActionTime = 0
        self.lastReadTime = 0
        self.doInit()

    def doInit(self, loopDelay=5):
        """
        sets the base value so that gravity is cancelled out from the initial postion
        loopDelay is the time in ms between attempts to read the accelerometer.
        """
        self.baseVal=0
        init=False
        while not init:
            delay(loopDelay)
            init,self.baseVal = self.readA()
        self.lastActionTime = millis()
        #State.printT('Initialized!')
        
    def readA(self):
        """
        calls the read func, which we know may return a big value to indicate a failed reading
        if  value is ok, returns True and value
        if not returns False and None
        we only read every read-delay milliseconds, if called earlier, returns failure,
        at every read, the read timer is reset, even in the case of a failed read!
        """
        if millis()-self.lastReadTime < self.rd:  # too soon!
            return False, None
        res = self.rf()
        self.lastReadTime  = millis()  # we made a read, so the timer is reset, even if the
                                       # read turns out to be bad!
        if res > 31 or res < -32:  # error
            return False, None
        else:
            return True, res

    def detectionZone(self, val):
        """
        returns the detection zone for the val arg:
        if val >= pos threshold <- +1
        if val <= ned threshold <- -1
        else <- 0
        """
        res = 0
        if val >= self.pt:
            res = 1
        elif val <- self.nt:
            res = -1
        return res

    def update(self):
        if self.autoOff:  # we look for timeout, otherwise keep going
            if millis() - self.lastActionTime > self.timeOut:
                self.of() # oFunc must be not None
                self.lastActionTime = millis()
                return  # we're done!
        ok,v = self.readA()
        if ok:  # read went ok
            curZone = self.detectionZone(v - self.baseVal)
            if (curZone): # we have passed a threshold,
                if curZone != self.prevZone: # changed zones!
                    self.tf() #tfunc must be not None
                    self.lastActionTime = millis()
                    self.prevZone = curZone

    def __repr__(self):
        return 'ShakeControl1:'                                  + \
            '\n\treadFunc        \t' + str(self.rf)              + \
            '\n\ttoggle Func     \t' + str(self.tf)              + \
            '\n\toff Func        \t' + str(self.of)              + \
            '\n\tpos Threshold   \t' + str(self.pt)              + \
            '\n\tneg Threshold   \t' + str(self.nt)              + \
            '\n\tread Delay      \t' + str(self.rd)              + \
            '\n\ttime Out        \t' + str(self.to)              + \
            '\n\tautoOff         \t' + str(self.autoOff)         + \
            '\n\tbase Value      \t' + str(self.baseVal)         + \
            '\n\tprevious Zone   \t' + str(self.prevZone)        + \
            '\n\tlast Action Time\t' + str(self.lastActionTime)  + \
            '\n\tlast Read Time  \t' + str(self.lastReadTime)
        
class ShakeControl:
    """ 
    provides 3-axis shake control; when there is shake in the appropriate
    axes, then the appropriate toggle function is called, LEDS always toggle!
    """
    ledVec = [[LED(4),0], # blue   -> x-axis
              [LED(3),0], # yellow -> y-axis
              [LED(2),0]] # green  -> z-axis

    def makeTFunc(tf,i,useLEDS):
        """
        this class method takes a toggle function tf, and a led index
        and returns a new toggle function that toggles the led before
        executing the external toggle call.
        and 'None' toggle function is okay!
        """
        if useLEDS:
            def f():
                if ShakeControl.ledVec[i][1]:
                    ShakeControl.ledVec[i][1]=0
                    ShakeControl.ledVec[i][0].off()
                else:
                    ShakeControl.ledVec[i][1]=1
                    ShakeControl.ledVec[i][0].on()
                tf and tf()
            return f
        else:
            def f():
                tf and tf()
            return f
    
    def makeOFunc(of,i,useLEDS):
        """
        similar to to above, this class method takes an off function of, and a led index
        and returns a new off function that turns off the led before
        executing the external off call.
        and 'None' off function is okay!
        """
        if useLEDS:
            def f():
                ShakeControl.ledVec[i][1]=0
                ShakeControl.ledVec[i][0].off()
                of and of()
            return f
        else:
            def f():
                of and of()
            return f
            
    def __init__(self,
                 tfx=None, tfy=None, tfz=None,
                 ofx=None, ofy=None, ofz=None,
                 useLEDS=False):
        """
        creates a 3-axis instance with default values, or as per args.
        """
        self.a = Accel()
        self.sVec= list(map(lambda r,t,o: ShakeControl1(r,t,o),
                            [self.a.x,self.a.y,self.a.z],
                            [ShakeControl.makeTFunc(i,f,useLEDS) for (f,i) in map(lambda ind,f: (ind,f),
                                                                                  range(3),
                                                                                  [tfx,tfy,tfz])],
                            [ShakeControl.makeOFunc(i,f,useLEDS) for (f,i) in map(lambda ind,f: (ind,f),
                                                                                  range(3),
                                                                                  [ofx,ofy,ofz])]))

    def update(self):
        """ the update method just calls update on all the individual shake controls
        """
        for s in self.sVec:
            s.update()

    def doInit(self):
        """
        reset the shake controls for gravity and last read time
        """
        for s in self.sVec:
            s.doInit()

    def __repr__(self):
        res = 'Accel:          \t\t'  + str(self.a) + '\n'
        for sc in self.sVec:
            res += repr(sc) +'\n'
        return res

class TremVib:
    vVec = (State.vibratoLowerLimit, State.vibratoUpperLimit)
    tVec = (State.tremoloLowerLimit, State.tremoloUpperLimit)

    def doTrem(self):
        if not self.aVec[0]:
            return
        #State.printT('Tremolo Level:\t',self.tremoloLevel)
        #print('Push: M Vol %s'%self.vVec[self.tremoloLevel])
        irq_state = disable_irq()
        self.volEnQueueable.push(self.targCoilID,self.vVec[self.tremoloLevel])
        enable_irq(irq_state)
        self.tremoloLevel ^= 1
    
    def doVib(self):
        if not self.aVec[1]:
            return
        #State.printT('Vibrato Level:\t',self.vibratoLevel)
        #print('Push: M Tone %s'%self.tVec[self.vibratoLevel])
        irq_state = disable_irq()
        self.toneEnQueueable.push(self.targCoilID,self.tVec[self.vibratoLevel])
        enable_irq(irq_state)
        self.vibratoLevel ^= 1

    def toggleTrem(self):
        self.tremOff(not self.aVec[0])

    def toggleVib(self):
        self.vibOff(not self.aVec[1])

    def tremOff(self,on=False):
        self.off(0,on)

    def vibOff(self,on=False):
        self.off(1,on)

    def off(self,whatIndex,on):
        """
        turn on or off the control given by the whatIindex
        """
        self.aVec[whatIndex] = on
        if self.aVec[whatIndex]:
            self.ctrl.doInit()
        #State.printT( ('Vibrato' if whatIndex else 'Tremolo')+':\t' + str(self.aVec[whatIndex]))

    def __init__(self,q):
        self.volEnQueueable=EnQueueable((EnQueueable.VOL,),q)
        self.toneEnQueueable=EnQueueable((EnQueueable.TONE,),q)
        self.targCoilID = 0
        # create the control with no off func, and autoOff disabled, and no leds!
        self.ctrl= ShakeControl(tfx=self.doTrem,
                                tfy=self.doVib)
        #active vect with index: Trem =0, Vib=1
        self.aVec = [False,False]
        self.tremoloLevel = self.vibratoLevel = 1

    def poll(self):
        if any(self.aVec):
            self.ctrl.update()

    def __repr__(self):
        res = 'TremVib:'                                          + \
              '\nvolEnQueueable: \t' + repr(self.volEnQueueable)  + \
              '\ntoneEnQueueable:\t' + repr(self.toneEnQueueable) + \
              '\ntargCoilID:     \t' + str(self.targCoilID)       + \
              '\naVec:           \t' + str(self.aVec)             + \
              '\ntremoloLevel:   \t' + str(self.tremoloLevel)     + \
              '\nvibratoLevel:   \t' + str(self.vibratoLevel)     + \
              '\nctrl:::\n'          + repr(self.ctrl)
        return res
    """
    # for testing
    def mainLoop(self):
        self.aVec = [True,True]
        self.ctrl.doInit()
        while any(self.aVec):
            self.ctrl.update()
            delay(50)
    """

class LcdDisplayI2C(I2cLcd):
    """
    Wiring: 
    X9 : CLOCK
    X10: Data
    """
    def __init__(self,confDict):
        I2cLcd.__init__(self,
                         I2C(confDict['i2c_id'],I2C.MASTER),
                         confDict['i2c_addr'],
                         confDict['num_lines'],
                         confDict['num_columns'])
        self.lns =['0123456789ABCDEF','0123456789ABCDEF']
   
    def setLn(self, lineNb, val):
        """
        Set the LCD line linNb to display the val;
        val is left justified to num_cols to overwrite any 
        characters leftover from previous writes.
        """
        self.lns[lineNb] = '%-*s' % ((self.num_columns), val) # left justify with spaces to nb of display cols
        self.move_to(0,lineNb)
        self.putstr(self.lns[lineNb])
        return self
  
    def getLn(self, lineNb):
        return self.lns[lineNb]




    
# class TrackBall:
# trackball quadrature resolution 1
"""
Wiring:
Red: V+ (checked out OK at both 5v and 3.3V)
Black: GND
Blue: Y-axis channel-A (leads if rotation is upwards, i.e. away from wires)
Green: Y-axis channel-B (leads if rotation is downwards)
Yellow: X-Axis channel-A (leads if rotation is right-wards, i.e. to the right when looking at the device wires at bottom)
White: X-Axis channel-B (leads if rotation is left-wards)

Some simple algorithms:
1x resolution: 
* on rise of channel-A: count += (channel-B==High ? -1 : +1)
2x resolution:  
* on rise of channel-A: count += (channel-B==High ? -1 : +1)
* on drop of channel-A: count += (channel-B==High ? +1 : -1)
4x resolution:
* on rise of channel-A: count += (channel-B==High ? -1 : +1)
* on rise of channel-B: count += (channel-A==High ? +1 : -1)
* on drop of channel-A: count += (channel-B==High ? +1 : -1)
* on drop of channel-B: count += (channel-A==High ? -1 : +1)

The circuit only has 2 interrupts available so use resolution 1.
x1_ = pyb.Pin(blue,   pyb.Pin.IN)
x2_ = pyb.Pin(yellow, pyb.Pin.IN)
y1_ = pyb.Pin(green,  pyb.Pin.IN)
y2_ = pyb.Pin(white,  pyb.Pin.IN)
"""

class TrackBall:
    def __init__(self,qq):
        self.volEnQueueable  = EnQueueable((EnQueueable.INC,EnQueueable.VOL),qq)
        self.toneEnQueueable = EnQueueable((EnQueueable.INC,EnQueueable.TONE),qq)
        self.targCoilID = 0;
        self.x1=Pin(State.trackballStateDict['x1'], Pin.IN, Pin.PULL_DOWN)
        self.x2=Pin(State.trackballStateDict['x2'], Pin.IN, Pin.PULL_DOWN)
        self.y1=Pin(State.trackballStateDict['y1'], Pin.IN, Pin.PULL_DOWN)
        self.y2=Pin(State.trackballStateDict['y2'], Pin.IN, Pin.PULL_DOWN)
        self.extInts = (ExtInt(State.trackballStateDict['x1'],
                                   ExtInt.IRQ_RISING,
                                   Pin.PULL_DOWN,
                                   self.x11),
                        ExtInt(State.trackballStateDict['y1'],
                                   ExtInt.IRQ_RISING,
                                   Pin.PULL_DOWN,
                                   self.y11))
            
    def x11(self,unused):
        if self.x2.value():
            irq_state = disable_irq()
            self.volEnQueueable.push(self.targCoilID,-1)
            enable_irq(irq_state)
        else:
            irq_state = disable_irq()
            self.volEnQueueable.push(self.targCoilID,1)
            enable_irq(irq_state)
    def y11(self,unused):
        if self.y2.value():
            irq_state = disable_irq()
            self.toneEnQueueable.push(self.targCoilID,-1)
            enable_irq(irq_state)
        else:
            irq_state = disable_irq()
            self.toneEnQueueable.push(self.targCoilID,1)
            enable_irq(irq_state)

    def __repr__(self):
        res = 'TrackBall:'                                        + \
              '\nvolEnQueueable: \t' + repr(self.volEnQueueable)  + \
              '\ntoneEnQueueable:\t' + repr(self.toneEnQueueable) + \
              '\ntargCoilID:     \t' + str(self.targCoilID)       + \
              '\nx1:             \t' + str(self.x1)               + \
              '\nx2:             \t' + str(self.x2)               + \
              '\ny1:             \t' + str(self.y1)               + \
              '\ny2:             \t' + str(self.y2)               #+ \
              #'\nExtInts:        \t' + str([i for i in self.extInts])
        return res

# SplitPot classes
#SplitPot
class SplitPot:
    """"
    This version only works for 2 pot split,
    reads the ADC 10 times over 10ms, and aborts if any of the values is out of scope!
    """
    def __init__(self,pinName,id,q,isToneRange=False,outputRangeTuple=(0,5),cutOff=30,spacing=30): #bMgr,
        """
        Create an instance:
        * pinName is used for the creation of the ADC, be sure to use a pin with an ADC!
        * outputRangeTuple is the range for output values after conversion & mapping
        * cutOff is the analog reading below wich a reading is considered NOISE, and is thus ignored
        * spacing is the number of readings between the 2 pots
        * if isToneRange, then the first range is reduced to length of 0
        """
        self.q        = q
        self.adc      = ADC(pinName)
        self.id       = id
        self.cutOff   = cutOff
        self.ranges   = [(cutOff,cutOff+1 if isToneRange else 2048-round(spacing/2.0)),
                         (2048+round(spacing/2.0),4095-cutOff)]
        self.rMaps    = [RMap(r,outputRangeTuple,True) for r in self.ranges]
        self.isToneRange = isToneRange
        self.tracking  = False
        self.update    = self.noTrackingUpdate
        self.track(False)

    def isMaster(self):
        return (self.id == 0)

    def track(self,onOff):
        self.tracking  = onOff
        if onOff:
            self.update = self.trackingUpdate
            self.enQV= [EnQueueable((EnQueueable.INC,EnQueueable.VOL),self.q),
                        EnQueueable((EnQueueable.INC,EnQueueable.TONE),self.q)]
        else:
            self.update = self.noTrackingUpdate
            self.enQV= [EnQueueable((EnQueueable.VOL,),self.q),
                        EnQueueable((EnQueueable.TONE,),self.q)]

    def poll(self):
        #if not self.bounceMgr.ready():
         #   return
        res = self.update()
        if res:
            #self.bounceMgr.trigger()
            irq_state = disable_irq()
            self.enQV[res[0]].push(self.id,res[1])
            enable_irq(irq_state)

    def getTrackingRange(self,vADC):
        curRange = None
        # 2 splits if not ToneRange, only second split if ToneRange
        for i in range((1 if self.isToneRange else 0),2): 
            if vADC >= self.ranges[i][0] and vADC<=self.ranges[i][1]:
                curRange=i
                break
        return curRange

    def inBounds(self,vADC):
        #print ('inBounds returning: ', (vADC >= self.cutOff and vADC <= self.ranges[1][1]))
        return (vADC >= self.cutOff and vADC <= self.ranges[1][1])
        
    def trackingUpdate(self):
        """
        This means we touch and hold, slide, then let go. 
        The slide distance corresponds to the magnitude and sign of the
        desired dec/increment.
        To simplify, we dec/inc by +/- 0,1,2.
        The initial touch determines the choice of vol or tone.
        The slide can go beyond the mid line dead zone without being
        invalidated!
        Sadly, calling INC means that the microvaluator will interpret the value to be inced,
        so we have to multiply the inc by 10 !!
        vRead <- adc.read()
        rangeId <- computeRange(Vread)
        if rangeId != None: that means vRead is a value in a valid range
            vInit <- vRead
            vLast <- vInit
        else:
           return None
        while vRead >lowCutOff && vRead < highCutoff and the delta(vLast,vRead) is with 30% of vLast 
           vLast <- vRead
           vRead <- adc.read()
        delta <- abs(vLast - vInit)
        sign <- 1 if vLast >= vInit else -1 # NO it's upside down!
        if delta < epsilon: # we have no  tracked values
          return None
        else if delta > bigStep:
           return (rangeId,20*sign)
        else:
           return (rangeId, 10*sign)
          convert to +1 or -1 (or maybe even +/-2 if big difference bewteen vLast and vInit
          and add to present value??
          return new value
        else:
           return None
        """
        vInit = self.adc.read()
        rangeID = self.getTrackingRange(vInit)
        if rangeID == None:
            return
        vLast = vInit
        vRead = self.adc.read()
        #print('vInit: ', vInit)
        #print('rangeID: ', rangeID)
        #print('new vRead: ',vRead)
        while (self.inBounds(vRead) and abs(vRead-vLast) < State.splitPotTrackingPercentCutoff*vLast):
            vLast = vRead
            vRead = self.adc.read()
            delay(1)
        #print('final vRead: ', vRead)
        #print('final vLast: ', vLast)
        delta  = abs(vLast-vInit)
        sign   = -1 if vInit >= vLast else 1
        #print('vInit: ', vInit, 'vLast: ',vLast)
        #print('delta: ', delta, 'sign: ', sign)
        #print('parametered Corrected! SplitPot ID: ',self.id)
        if self.isMaster():
            sign *= State.splitPotMasterFactor # correct for microvaluation on master vol/tone!
        if delta < State.splitPotTrackingError:
            #print('return None')
            return None
        elif delta < State.splitPotTrackingBigStep:
            #print('return (',rangeID,sign*State.splitPotTrackingSmallMultiplier,')')
            return (rangeID,sign*State.splitPotTrackingSmallMultiplier)
        elif delta < 2*State.splitPotTrackingBigStep:
            #print('return (',rangeID,sign*State.splitPotTrackingBigMultiplier,')')
            return (rangeID,sign*State.splitPotTrackingBigMultiplier)
        else:
            # this is full vol/tone in one go!
            #print('return (',rangeID,sign*5,')') # State.splitPotTrackingBigMultiplier
            return (rangeID,sign*5) #State.splitPotTrackingBigMultiplier)
            
    def noTrackingUpdate(self):
        """
        takes nbReadings reads, then avgs them and maps the result to the appropriate range and returns it.
        returns None if no valid value read
        """
        nbReadings = State.splitPotNoTrackingNbReadings
        vADC = 0
        for i in range(nbReadings):
            v=self.adc.read()
            if v<self.cutOff or (v>self.ranges[0][1] and v<self.ranges[1][0]) or v>self.ranges[1][1]:
                #print(v)
                return None
            vADC += v
            delay(1)
        vADC = round(vADC/nbReadings)
        #print(vADC)
        for i in range((1 if self.isToneRange else 0),2): # 2 splits if not ToneRange, only second split if ToneRange
            if vADC >= self.ranges[i][0] and vADC<=self.ranges[i][1]:
                
                #State.printT('VADC= ' +str(vADC) + " tuple: "  +str((i,self.rMaps[i].v(vADC))))
                return (i,self.rMaps[i].v(vADC))
        

#SplitPotArray
class SplitPotArray:
    #SplitPot.SplitPotArray(State.splitPotPinNameVec,self.q,useTracking=False)
    def __init__(self,pinNames,q,cutOff=State.splitPotCutOff,useTracking=False,spacing=State.splitPotSpacing): #bMgr,
        self.spvVec = []
        i=0
        for pn in pinNames[:-1]:
            self.spvVec.append(SplitPot(pn,i,q,cutOff=cutOff,spacing=spacing)) #bMgr,
            i+=1
        self.spvVec.append(SplitPot(pinNames[-1],i,q,isToneRange=True,cutOff=cutOff,spacing=spacing)) # bMgr,
        self.track(useTracking)

    def track(self,onOff):
        #print('called spa track: ', onOff)
        for sp in self.spvVec:
            sp.track(onOff)

    def poll(self):
        for sp in self.spvVec:
            sp.poll()
    
#############  Obsolete or Unused ############
# LcdDisplay
# Wiring:
# LCD PIN - connected to
#  1 - Vss (aka Ground) - Connect to one of the ground pins on you pyboard.
#  2 - VDD - connected to VIN which is 5 volts when your pyboard is powerd vi USB
#  3 - VE - connected to VIN (Contrast voltage) - I'll discuss this below
#  4 - RS (Register Select) connect to Y12 (as per call to GpioLcd)
#  5 - RW (Read/Write) - connect to ground
#  6 - EN (Enable) connect to Y11 (as per call to GpioLcd)
#  7 - D0 - leave unconnected
#  8 - D1 - leave unconnected
#  9 - D2 - leave unconnected
# 10 - D3 - leave unconnected
# 11 - D4 - connect to Y5 (as per call to GpioLcd)
# 12 - D5 - connect to Y6 (as per call to GpioLcd)
# 13 - D6 - connect to Y7 (as per call to GpioLcd)
# 14 - D7 - connect to Y8 (as per call to GpioLcd)
# 15 - A (BackLight Anode) - Connect to VIN
# 16 - K (Backlight Cathode) - Connect to Ground
#
# The Contrast line (pin 3) typically connects to the center tap of a
# 10K potentiometer, and the other 2 legs of the 10K potentiometer are
# connected to pins 1 and 2 (Ground and VDD)
#
# The wiring diagram on the followig page shows a typical "base" wiring:
# http://www.instructables.com/id/How-to-drive-a-character-LCD-displays-using-DIP-sw/step2/HD44780-pinout/
# Add to that the EN, RS, and D4-D7 lines.
#
#class LcdDisplay6Wire(GpioLcd):
#    """
#    Wiring:
#    LCD PIN - connected to
#     1 - Vss (aka Ground) - Connect to one of the ground pins on you pyboard.
#     2 - VDD - connected to VIN which is 5 volts when your pyboard is powerd vi USB
#     3 - VE - connected to VIN (Contrast voltage) - I'll discuss this below
#     4 - RS (Register Select) connect to Y12 (as per call to GpioLcd)
#     5 - RW (Read/Write) - connect to ground
#     6 - EN (Enable) connect to Y11 (as per call to GpioLcd)
#     7 - D0 - leave unconnected
#     8 - D1 - leave unconnected
#     9 - D2 - leave unconnected
#    10 - D3 - leave unconnected
#    11 - D4 - connect to Y5 (as per call to GpioLcd)
#    12 - D5 - connect to Y6 (as per call to GpioLcd)
#    13 - D6 - connect to Y7 (as per call to GpioLcd)
#    14 - D7 - connect to Y8 (as per call to GpioLcd)
#    15 - A (BackLight Anode) - Connect to VIN
#    16 - K (Backlight Cathode) - Connect to Ground
#    
#    The Contrast line (pin 3) typically connects to the center tap of a
#    10K potentiometer, and the other 2 legs of the 10K potentiometer are
#    connected to pins 1 and 2 (Ground and VDD)
#    
#    The wiring diagram on the followig page shows a typical "base" wiring:
#    http://www.instructables.com/id/How-to-drive-a-character-LCD-displays-using-DIP-sw/step2/HD44780-pinout/
#    Add to that the EN, RS, and D4-D7 lines.
#    """
#    def __init__(self,confDict):
#        GpioLcd.__init__(self,
#                         Pin(confDict['rs_pin']),
#                         Pin(confDict['enable_pin']),
#                         Pin(confDict['d4_pin']),
#                         Pin(confDict['d5_pin']),
#                         Pin(confDict['d6_pin']),
#                         Pin(confDict['d7_pin']),
#                         confDict['num_lines'],
#                         confDict['num_columns'])
#        self.lns =['0123456789ABCDEF','0123456789ABCDEF']
#   
#    def setLn(self, lineNb, val):
#        """
#        Set the LCD line linNb to display the val;
#        val is left justified to num_cols to overwrite any 
#        characters leftover from previous writes.
#        """
#        self.lns[lineNb] = '%-*s' % ((self.num_columns), val) # left justify with spaces to nb of display cols
#        self.move_to(0,lineNb)
#        self.putstr(self.lns[lineNb])
#        return self
#  
#    def getLn(self, lineNb):
#        return self.lns[lineNb]
#
# Selector
# support for 3 or 5 ... position selector switches
# class Selector:
#     """ Usage:
#     >> pinIds = ('X1','X2','X3')
#     >> s = Selector([Pin(p, Pin.IN, Pin.PULL_DOWN) for p in pinIds])
#     >> s.currentPostion
#     3
#     >> # move switch
#     >> s.setPostion()
#     >> s.currentPostion
#     0
#     -----
#     wiring:
#     common on switch to 3.3V
#     position 0 side wire to pin 0
#     position 2 side wire to pin 1
#     position 4 side wire to pin 2
#     """
#     
#     # this defines the switch position pin values
#     # note: if a 3 position selector is used, then only the 'upper left' 3x2 part is used
#     masterTable = [[1,0,0],  # position 0, i.e. left: left pin is HIGH
#                    [1,1,0],  # position 1, i.e. left/middle: left and middle pins are HIGH
#                    [0,1,0],  # position 2, i.e. middle: middle pin is HIGH
#                    [0,1,1],  # position 3, i.e. middle/right: middle & right pins are HIGH
#                    [0,0,1]]  # position 4, i.e. right: right pin is HIGH
#     
#     def __init__(self,pins):
#         """create an instance of a 3 or 5 position switch connected to the 
#         pins provided.
#         Pins should be configured as Pin('X1', Pin.IN, Pin.PULL_DOWN)
#         len(pins) should be 2, for 3 postions, 3, for 5 positions
#         incorrect arguments raise exceptions
#         """
#         if len(pins) not in (2,3):
#             raise Exception('invalid nb of pins', pins)
#         self.pinLis = []
#         for p in pins:
#             self.pinLis += [p]
#         nbPos = 2*len(pins) -1
#         self.truthTable = [x[:len(pins)] for x in Selector.masterTable[:nbPos]]
#         self.currentPosition = 0
#         self.setPosition()  # reads the pin values and deduces current switch position
#         
#     def setPosition(self):
#         """ reads the pin values and deduces current switch position
#         in case of failure, exception is raised.
#         """
#         tLis  = [p.value() for p in self.pinLis]
#         i = 0
#         found = False
#         while not found:
#             if all(map(lambda x,y: x==y,tLis,self.truthTable[i])):
#                 found = True
#             else:
#                 i +=1
#         if not found:
#             raise Exception('position not found', tLis)
#         self.currentPosition = i
# 
#     def __repr__(self):
#         return 'Selector:' + \
#             '\n\tpostion:\t' + str(self.currentPosition) +\
#             '\n\tpinLis:\t' + str(self.pinLis) +\
#             '\n\ttruthTable:\t' + str(self.truthTable)  + '\n'

# Illuminator
# # support leds or other pin controlled lights
# class Illuminator__:
#     """
#     Helper class for Illuminator, see below
#     """
#     
#     def __init__(self,pin):
#         """create an instance of a LED connected to the 
#         pin provided.
#         Pins should be configured as Pin('X1', Pin.OUT_PP)
#         """
#         self.p = pin
#         self.off()
#         
#     def off(self):
#         """ set pin to low
#         """
#         self.p.low()
# 
#     def on(self):
#         """ set pin to high
#         """
#         self.p.high()
# 
#     def value(self):
#         """ returns 0 or 1 depending on state of pin
#         """
#         return self.p.value()
# 
# class Illuminator(Illuminator__):
#     """ Usage:
#     >> pinId = 'X1
#     >> i = Illuminator(Pin(pinID, Pin.OUT_PP))
#     >> i.value()
#     0
#     >> i.on()
#     >> i.value()
#     1
#     >> i.off()
#     >> i.value()
#     0
#     -----
#     wiring:
#     from pin to LED+ 
#     from LED- to current limiting resistor
#     from current limiting resistor to ground
#     """
# 
#     toggleFuncs = (Illuminator__.on, Illuminator__.off)  # for use in toggle
# 
#     def __init__(self,pin):
#         """create an instance of a LED connected to the 
#         pin provided.
#         Pin should be configured as Pin('X1', Pin.OUT_PP)
#         """
#         Illuminator__.__init__(self,pin)
#         
#     def toggle(self):
#         """ toggles the value of the pin
#         """
#         type(self).toggleFuncs[self.value()](self)
# 
#     def __repr__(self):
#         return 'Illuminator:' + \
#             '\n\tpin:\t' + str(self.p) +\
#             '\n\tvalue:\t' + str(self.p.value())  + '\n'                    
# 
# 
# # SWDebouncedPushbutton
# # debounce a momentary pushbutton with HIGH == ON state and
# # at every push, toggle a LED illuminator
# # usage:
# # >>> p = pyb.Pin('X1', pyb.Pin.IN, pyb.Pin.PULL_DOWN)
# # >>> i = Illuminator(pyb.Pin('X2', pyb.Pin.OUT_PP))
# # >>> b = DebouncePushbutton(p,i.toggle)
# # >>> while True:
# # ...   b.update()
# #
# class SWDebouncedPushbutton:
#     debounceDelay = 20 #milliseconds between pushes
# 
#     def __init__(self, pin, onHigh=None):
#         self.pin = pin
#         self.lastDebounceTime = millis()
#         self.lastReading = 0
#         self.onHigh = onHigh
# 
#     def update(self):
#         # if there's been enouh time since last bounce, then take a reading
#         if millis() - self.lastDebounceTime > self.debounceDelay:
#             reading = self.pin.value()
#             # if the reading is different from the last one,
#             if reading != self.lastReading:
#                 # we got a new value:
#                 # * update bounce time
#                 # * update reading
#                 # * and if reading is HIGH, execute the onHigh action
#                 self.lastDebounceTime = millis()
#                 self.lastReading = reading
#                 if reading and self.onHigh:
#                     self.onHigh()
# 
#     def __repr__(self):
#         return 'Pushbutton:' + \
#             '\n\tpin:\t' + str(self.pin) + \
#             '\n\tlastDebounceTime:\t' + str(self.lastDebounceTime)  + \
#             '\n\tlastReading:\t' + str(self.lastReading)  + \
#             '\n\tonHigh:\t' + str(self.onHigh)  + '\n'
#

# class IlluminatedPushbutton(SWDebouncedPushbutton) :
#     """
#     a Pushbutton with an Illuminator built-in, in addtion to the
#     onHigh action, of course.
#     """
# 
#     def __init__(self, pin, illum, onAction = None):
#         SWDebouncedPushbutton.__init__(self,pin,self.illumOnHigh)
#         self.illuminator = illum
#         self.onAction = onAction
#         
#     def illumOnHigh(self):
#         if self.onAction:
#             self.onAction()
#         self.illuminator.toggle()
# 
#     def __repr__(self):
#         return 'IlluminatedPushbutton:' + \
#             '\n\tilluminator:\t' + str(self.illuminator) + \
#             '\n\tonAction:\t' + str(self.onAction)  + \
#             '\n' + SWDebouncedPushbutton.__repr__(self)
#

    
# class VoltageDividerPot:
#     """
#     Encapsulate the reading of an analog pot in voltage divider configuration
#     """
#     def __init__(self,pin,rm=None):
#         """
#         instance creation, args:
#         * pin is a pyb.Pin object as per: pyb.Pin('X1', pyb.Pin.ANALOG)
#         * an optional RMap instance to provide a reading in the proper range
#         """
#         self.a = ADC(pin)
#         if rm:
#             self.v = lambda x: rm.v(x)
#         else:
#             self.v = lambda x:x
# 
#     def update(self):
#         """
#         returns the current reading as per config
#         """
#         return self.v(self.a.read())
# 
#class BounceMgr:
#    """Singleton object to allow for global waiting after any action...
#    """
#    def __init__(self,timeDelay):
#        self.debounceDelay = timeDelay
#        self.lastTriggerTime = 0
#
#    def ready(self):
#        return (millis()- self.lastTriggerTime > self.debounceDelay)
#
#    def trigger(self):
#        self.lastTriggerTime = millis()
#        
