gratefulfrog/ArduGuitar/Ardu2/design/POC-3_MAX395/pyboard/DraftDevt/vactrolControl.py

#!/usr/local/bin/python3.4
# vactrolControl.py
# underwork, not ready as of 2015 06 10


from pyb import Pin

class vactrolControl:
    """simple class providing on/off functionality of a vactrol
    controlled by a pyboard bin.
    """
    def __init__(self, vactrolPin):
        self.vactrol = Pin(vactrolPin, Pin.OUT_PP)
        self.vactrol.low()

    def on(self):
        self.vactrol.high()

    def off(self):
        self.vactrol.low()
