gratefulfrog/ArduGuitar/tests/Arduino/DSO_NANO_TESTER/DSO_NANO_TESTER.ino

/*
  Blink
  Turns on an LED on for one second, then off for one second, repeatedly.
 
  This example code is in the public domain.
 */
 
// Pin 13 has an LED connected on most Arduino boards.
// give it a name:
int led = 13;
boolean b = true;

// the setup routine runs once when you press reset:
void setup() {                
  // initialize the digital pin as an output.
  pinMode(led, OUTPUT);     
}

// the loop routine runs over and over again forever:
void loop() {
  if (b){
   digitalWrite(led, HIGH);
  }
  else{
    digitalWrite(led, LOW);
  }
  b = ! b;
  delay(100);               
}
