gratefulfrog/ArduGuitar/Ardu2/design/POC-3_MAX395/pyboard/V1_WithHMI/pyboard_no_debug/app.py

# app.py
# provides classes for the application level.
# This is where all the user interface calls are found!
#######################################################
# 2016 12 24: dissabled tracking on splitpots
# 2016 12 25: updated validateAndApplyLCDInput to save edited conf as preset, but not to disk
# 2016 12 28: added polling version to pb and selectors with swtich
# 2017 01 01: re-activated tracking on pb 0, if not sequencing... to see what happens!
# 2017 01 02: reorganized loadConf, created loadConfHelper

from bitMgr import BitMgr
from dictMgr import shuntConfDict
from components import Invertable,VTable,OnOffable,MicroValuator
from state import State
from spiMgr import SPIMgr
#from configs import configDict,mapReplace
from hardware import ShuntControl,LcdDisplayI2C,PushButtonArray,SelectorInterrupt,TrackBall,SplitPotArray,TremVib #BounceMgr,
from q import Q
from config import PyGuitarConf
from Presets import Preset
import sParse
from lcdMgr import LCDMgr
import pyb
import gc

lastUpdate = "updated: 2017 01 08 12:23 (sParse.py)"

class App():
    """
    This class is the top level user facing application class.
    A single instance should be created and maintained during execution.
    The instance will maintain the user readable component classes as well
    as manage the Bits and SPI interfacing.
    usage:
    from app import App
    from state import State
    a = App()
    a.set(...)
    a.connect(...)
    a.x()
    details:
    >>> from app import App
    >>> a = App()
    >>> from state import State
    >>> a.set('PB',State.Vibrato,State.l0)
    (0, 5) ((0, 223),)
    ('masking: ', ['0', '0b11011111'])
    ('setting: (0, 5)',)
    >>> a.set('PB',State.Tremolo,State.l0)
    (0, 6) ((0, 191),)
    ('masking: ', ['0', '0b10111111'])
    ('setting: (0, 6)',)
    >>> a.x()
    xxxxxxxxxxx6543210
    ('send:\t0b1100000',)

    >>> a.set('A',State.Vol,State.l5)
    ((10, 7), (4, 5), (4, 7)) ((10, 3), (4, 31))
    ('masking: ', ['10', '0b11'])
    ('masking: ', ['4', '0b11111'])
    ('setting: ((10, 7), (4, 5), (4, 7))',)

    >>> a.connect('A',0,'B',1)
    ('setting: (8, 2)',)
    
    >>> a.x()
    setting: None
    ...

    >>> 
    """
    class LCDMessenger:
        messageTime = 3000 # ms
        def __init__(self):
            self.messaging = False
            self.startTime = 0
            self.oldLines = ['','']
            
        def message(self, text, lcdM, lnLen=16):
            """ 
            inits the display of some text to the lcd
            if time has run out, cancels messaging
            """
            if not self.messaging:
                self.messaging = True
                for i in range(2):
                    self.oldLines[i] = lcdM.getLn(i)
                    lcdM.setLn(i,text[i*lnLen:(i+1)*lnLen])
                self.startTime = pyb.millis()
                    
        def update(self,lcdM):
            if not self.messaging:
                return
            else:
                self.messaging = ((pyb.millis() - self.startTime) < App.LCDMessenger.messageTime)
                if not self.messaging:
                    for i in range(2):
                        lcdM.setLn(i,self.oldLines[i])
                    
        def stopMessaging(self,lcdM):
            if self.messaging:
                self.messaging = False
                for i in range(2):
                    lcdM.setLn(i,self.oldLines[i])
            
    
    targVec = [['M','A','B','C','D','TR'], #['MVol','MTone'],
               [0,1,2,3,4,5],
               [0,1], #horizontal, vertical
               ['M','A','B','C','D','TR']]
    
    def __init__(self, uPolling=True):
        """
        Instance creation; creation of member variables which are
        mainly instances of supporting classes.
        some details
        - resetConnections: boolean True if the connections have been reset
                            False, if they need to be reset before any new
                            connections are added.
        - coils is a vector: first is the Master-out, then coils A through D:
          [VTable, Ivertable, Ivertable, Ivertable, Ivertable]
        also,
        after creation of the SPIMgr, the update message is sent to it to 
        initialize all the pins.
        """
        #print(lastUpdate)
        self.usePolling = uPolling
        self.messenger = App.LCDMessenger()
        #self.bounceMgr = BounceMgr(State.HWDebounceDelay)
        self.mainLoopDelay = 50
        self.gcd=False # true if we just did a garbage collection, false if work has been done and garbage not yet collected
        self.setVec = [self.inc, self.pb, self.doConf, self.vol, self.tone]
        self.q = Q()
        self.conf = PyGuitarConf()
        self.preset = Preset(self.conf)
        self.mEval = MicroValuator()
        self.shuntControl = ShuntControl(shuntConfDict)
        self.state = State() # needed since State.__init__ must be called!
        self.reset()
        self.pba = PushButtonArray(self.q,self.usePolling) #,self.bounceMgr)
        self.spa = SplitPotArray(State.splitPotPinNameVec,self.q,useTracking=False) #self.bounceMgr
        self.tv  = TremVib(self.q)
        self.lcdMgr= LCDMgr(self.preset.currentDict,'S','Name',self.lcd,self.q,self.validateAndApplyLCDInput)
        self.selectorVec=[None,None]
        for i in range(2):
            self.selectorVec[i] = SelectorInterrupt(State.SelectorPinNameArray[i],i,self.q,self.usePolling) #,self.bounceMgr)
        self.tb = TrackBall(self.q)
        self.currentConfTupleKey = (-1,-1)
        self.sequencing = False
        self.doConf(0)  # anonymous value just to fill the argument
        self.x()

    def reset(self):
        gc.collect()
        self.bitMgr = BitMgr()
        self.resetConnections = True
        self.coils = {}
        for coil in State.coils[:-1]:
            self.coils[coil] = Invertable(coil)
        self.coils[State.coils[-1]]= VTable(State.coils[-1])
        self.coils[State.pb] = OnOffable()
        self.spiMgr = SPIMgr(State.spiOnX,State.spiLatchPinName)
        #self.lcd = LcdDisplay6Wire(State.lcdConfDict)
        self.lcd = LcdDisplayI2C(State.lcdConfDict)
        self.messenger.stopMessaging(self.lcd)
        # shunt, turn all to State.lOff, unshunt
        self.shuntControl.shunt()
        self.spiMgr.update(self.bitMgr.cnConfig[BitMgr.cur])
        self.shuntControl.unShunt()
        self.pbTime = pyb.millis()
        gc.collect()
        self.gcd=True

    def pollPollables(self):
        #State.printT('polling spa...')
        if self.usePolling:
            self.pba.poll()
            for i in range(2):
                self.selectorVec[i].poll()
        self.spa.poll()
        if (self.preset.currentDict[self.conf.vocab.configKeys[9]] or self.preset.currentDict[self.conf.vocab.configKeys[8]]):
            #State.printT('polling tv..')
            self.tv.poll()
    
    def mainLoop(self):
        while True:
            self.messenger.update(self.lcdMgr)
            try:
                self.pollPollables()            
                self.processQ()    
            except Exception as e:
                self.messenger.message(str(e), self.lcdMgr)
                #print(type(e),str(e.args))
                
            # put a sleep comand here to save energy
            # pyb.delay(self.mainLoopDelay)
            
    def processQ(self):
        #State.printT('processQ')
        irq_state = pyb.disable_irq()
        work = self.q.pop()
        pyb.enable_irq(irq_state)
        worked = False
        while (work != None):
            #print('Work: ', bin(work))
            worked = self.doWork(work) or worked
            irq_state = pyb.disable_irq()
            work = self.q.pop()
            pyb.enable_irq(irq_state)
        
        if worked:
            self.messenger.stopMessaging(self.lcd)
            #State.printT('worked!')
            self.x()
            # added 2017 01 02 to ensure that all changes are permanent
            if not self.sequencing:
                self.preset.saveCurrentConfigAsPreset(self.currentConfTupleKey, False)
            self.gcd=False
        elif not self.gcd:
            #State.printT('GC!')
            gc.collect()  # time to do this is 5ms
            self.gcd=True

    def doWork(self,twoBytes):
        #print('next deque index: ', self.q.gptr)
        #print('twoBytes of work:\t',bin(twoBytes))
        V = twoBytes & 0xFF
        K = (twoBytes>>8) & 0xFF
        mask = 0x80
        res = False
        #State.printT('Work:\tK:\t' + bin(K) + '\tV:\t'+ hex(V))
        #print('Work:\tK:\t' + bin(K) + '\tV:\t'+ hex(V),'\tQlength:\t',self.q.qNbObj)
        #print(self.q)
        #print('X:\tK:\t' + bin(K) + '\tV:\t'+ hex(V))
        for i in range(5):
            if K & (mask>>i):
                who = App.targVec[min(i,3)][K & 0b111]
                val = (0xFF & V) if (V & 0xFF)<128 else (V & 0XFF)-256
                res = self.setVec[i](who,val,K&0B11111000) or res
                break
        return res

    def inc(self,who,val,what):
        # updated version works with updated top byte INC | VOL + M,A,B,C,D,TR -it DOES work for tone range!
        # we need to find if its vol or tone then to which coil then call the appropriate methods
        volMask  = 0B10000
        toneMask = 0B1000
        newVal = val
        sFunc = None
        #State.printT('INC:\t%s\t%s\t%d'%('Vol' if (what & volMask) else 'Tone', who,val))
        #print('INC:\t%s\t%s\t%d'%('Vol' if (what & volMask) else 'Tone', who,val))
        if what & volMask:
            sFunc = self.vol
            if who == 'M':
                self.mEval.inc(0,val)
                newVal = self.mEval.valRounded(0)
            else:
                newVal = max(0,(min(self.preset.currentDict[who][0] + val,5)))
        elif what & toneMask:
            sFunc = self.tone
            if who == 'M':
                self.mEval.inc(1,val)
                newVal = self.mEval.valRounded(1)
            else:
                newVal = max(0,(min(self.preset.currentDict[who][1] + val,5)))
        return sFunc(who,newVal)

    def vol(self,who,val,unused=None,force=False):
        # who is 'M','A','B','C','D'
        if force or val != self.preset.currentDict[who][0]:
            #State.printT('VOL:\t' + str(who) +'\t' + str(val))
            #print("a.set('%s',State.Vol,State.l%s)"%(who,(str(val) if val !=0 else 'Off')))
            #self.outgoing.append("a.set('%s',State.Vol,State.l%s)"%(who,(str(val)))) # if val !=0 else 'Off')))
            self.set(who,State.Vol,eval('State.l%s'%str(val)))
            self.preset.currentDict[who][0] = val
            if who == 'M':
                self.mEval.set(0,val)
            return True
        return False

    def tone(self,who,val,unused=None,force=False):
        # who is 'M','A','B','C','D','TR'
        if force or val != self.preset.currentDict[who][1]:
            #State.printT('TONE:\t' + str(who) +'\t' + str(val))
            trVal = 'Off'
            toneVal = '0'
            if who =='TR':
                trVal =  str(val-1) if val else 'Off'
                targ = 'M'
                toneVal = None
            elif who == 'M':
                targ = who
                trVal = None
                toneVal = str(val-1) if val else 'Off'
                self.mEval.set(1,val)
            else:
                targ = who
                trVal = '0' if val else 'Off'
                toneVal = str(val-1) if val else 'Off'
            if trVal != None:
                #self.outgoing.append("a.set('%s',State.ToneRange,State.l%s)"%(targ,trVal))
                self.set(targ,State.ToneRange,eval('State.l%s'%trVal))
            if toneVal != None:
                #self.outgoing.append("a.set('%s',State.Tone,State.l%s)"%(targ,toneVal))
                self.set(targ,State.Tone,eval('State.l%s'%toneVal))
            self.preset.currentDict[who][1] = val
            return True
        return False

    def doConfHelper(self,cf):
        self.reset()
        #State.printT('loading conf: ' + str(cf))
        self.loadConf(self.preset.presets[cf])
        return True

    def doConf(self,who,unused0=None, unused1=None):
        # who is 0 for horizontal, 1 for vertical    
        self.selectorVec[who].setPosition()
        cf = (self.selectorVec[0].currentPosition,self.selectorVec[1].currentPosition)
        if  self.currentConfTupleKey == cf:
            return False
        else:
            self.startSeq(cf == self.preset.seq.seqStartKey)
        self.currentConfTupleKey = cf
        return self.doConfHelper(cf)

    def startSeq(self,onOff):
        self.sequencing = onOff
        self.preset.currentDict[self.conf.vocab.configKeys[10]] = 1 if onOff else 0
        self.set(State.pb,State.Red,State.l0 if self.preset.currentDict[self.conf.vocab.configKeys[10]] else State.lOff)
        if onOff:
            self.preset.seq.reset()
            
    def doNextSeq(self):
        cf = self.preset.seq.nextKey()
        self.preset.currentDict[self.conf.vocab.configKeys[10]] ^= 1 
        self.set(State.pb,State.Red,State.l0 if self.preset.currentDict[self.conf.vocab.configKeys[10]] else State.lOff)
        return self.doConfHelper(cf)
    
    def pb(self,who,unused=None,unusedA=None):
        if ((pyb.millis()  - self.pbTime) < State.pbProcessingDelay):
            self.pbTime = pyb.millis()
            #State.printT('PB Processing BOUNCE!! delta millis:\t' +  str(pyb.millis()  - self.pbTime))
            return False
        #State.printT('PB delta millis:\t' +  str(pyb.millis()  - self.pbTime))
        self.pbTime = pyb.millis()
        
        whoFuncs = (
            # this either steps the seq or toggles splitpot tracking if not sequencing
            (self.pb0Func,),  # pb 0 # either step sequence or toggle tracking if not sequencing
            # this is the one saves the preset,      
            (self.turnOnYellowLed, self.saveCurrentConfAsPreset),          # pb 1
            # Tremolo
            (self.toggleTrem,),                       # pb 2
            # Vibrato
            (self.toggleVib,),                        # pb 3
            (self.lcdMgr.onLeftButton,),              # pb 4
            (self.lcdMgr.onRightButton,))             # pb 5

        #State.printT('PB:\t' + str(who))  
        res = False         
        for f in whoFuncs[who]:
            res = f() or res
        #State.printT('pb returning: ' +str(res))
        return res # True if who in [2,3] else False

    def pb0Func(self):
        if self.sequencing:
            #State.printT('pb0Func:\tstepping the sequence...')
            #State.debug and input('Press Return:')
            return self.doNextSeq()
        else:
            #return False  # no more tracking for now
            #State.printT('pb0Func:\ttoggling tracking...')
            #State.debug and input('Press Return:')
            #print('pb0Func:\ttoggling tracking...')
            return self.toggleTracking()

    def toggleTracking(self):
        self.preset.currentDict[self.conf.vocab.configKeys[10]] ^= 1 # 0 if self.preset.currentDict[self.conf.vocab.configKeys[10]] else 1
        self.spa.track(self.preset.currentDict[self.conf.vocab.configKeys[10]])
        self.set(State.pb,State.Red,State.l0 if self.preset.currentDict[self.conf.vocab.configKeys[10]] else State.lOff)
        #State.printT('Tracking:\t%d'%self.preset.currentDict[self.conf.vocab.configKeys[10]])
        return True # False
    
    def tracking(self,onOff):
        self.preset.currentDict[self.conf.vocab.configKeys[10]] = 1 if onOff else 0
        self.spa.track(self.preset.currentDict[self.conf.vocab.configKeys[10]])
        self.set(State.pb,State.Red,State.l0 if self.preset.currentDict[self.conf.vocab.configKeys[10]] else State.lOff)
        #State.printT('Tracking:\t%d'%self.preset.currentDict[self.conf.vocab.configKeys[10]])
        return False
    
    def trem(self,onOff):
        res = ((onOff and not self.preset.currentDict[self.conf.vocab.configKeys[8]]) or (self.preset.currentDict[self.conf.vocab.configKeys[8]] and not onOff))
        self.preset.currentDict[self.conf.vocab.configKeys[8]] = 1 if onOff else 0
        self.tv.tremOff(onOff)
        self.set(State.pb,State.Tremolo,State.l0 if onOff else State.lOff)
        #v = str(0) if self.preset.currentDict[self.conf.vocab.configKeys[8]] else 'Off'
        #print ("CANNOT YET SEND:\ta.set('M',State.Tremolo,l%s)"%v)
        return res
    
    def vib(self,onOff):
        res = ((onOff and not self.preset.currentDict[self.conf.vocab.configKeys[9]]) or (self.preset.currentDict[self.conf.vocab.configKeys[9]] and not onOff))
        self.preset.currentDict[self.conf.vocab.configKeys[9]] = 1 if onOff else 0
        self.tv.vibOff(onOff)
        self.set(State.pb,State.Vibrato,State.l0 if onOff else State.lOff)
        #v = str(0) if self.preset.currentDict[self.conf.vocab.configKeys[9]] else 'Off'
        #print ("CANNOT YET SEND:\ta.set('M',State.Vibtrato,l%s)"%v)
        return res
    
    def toggleTrem(self):
        #trem =2, vibrato =3
        #self.preset.currentDict[self.conf.vocab.configKeys[8]] = 0 if self.preset.currentDict[self.conf.vocab.configKeys[8]] else 1
        #v = str(0) if self.preset.currentDict[self.conf.vocab.configKeys[8]] else 'Off'
        #print ("CANNOT YET SEND:\ta.set('M',State.Tremolo,l%s)"%v)
        self.preset.currentDict[self.conf.vocab.configKeys[8]] ^= 1 
        self.tv.toggleTrem()
        self.set(State.pb,State.Tremolo,State.l0 if self.preset.currentDict[self.conf.vocab.configKeys[8]] else State.lOff)
        return True
    
    def toggleVib(self):
        #trem =2, vibrato =3
        #self.preset.currentDict[self.conf.vocab.configKeys[9]] = 0 if self.preset.currentDict[self.conf.vocab.configKeys[9]] else 1
        #v = str(0) if self.preset.currentDict[self.conf.vocab.configKeys[9]] else 'Off'
        #print ("CANNOT YET SEND:\ta.set('M',State.Vibtrato,l%s)"%v)
        #self.outgoing.append("a.set('M',State.Vibtrato,l%s)"%v)
        self.preset.currentDict[self.conf.vocab.configKeys[9]] ^= 1
        self.tv.toggleVib()
        self.set(State.pb,State.Vibrato,State.l0 if self.preset.currentDict[self.conf.vocab.configKeys[9]] else State.lOff)
        return True
    
    def displayCurrentConf(self):
        return self.preset.currentDict

    def loadConfHelper(self):
        self.tone('TR',self.preset.currentDict['TR'][1],force=True)
        for c in ['A','B','C','D','M']:
            self.vol(c,self.preset.currentDict[c][0],force=True)
            self.tone(c,self.preset.currentDict[c][1],force=True)
        self.lcdMgr.loadConf()
        self.trem(self.preset.currentDict[self.conf.vocab.configKeys[8]])
        self.vib(self.preset.currentDict[self.conf.vocab.configKeys[9]])
        self.tracking(self.preset.currentDict[self.conf.vocab.configKeys[10]])
       
    def loadConf(self, conf):
        #State.printT('loading conf: ' + str(conf))
        #print('currentDict: ',self.preset.currentDict)
        #print('keys: ', [key for key in self.preset.currentDict.keys()])
        for key in self.preset.currentDict.keys():
            self.preset.currentDict[key] = conf[key]
            #print('key: ',key, ' processed ok!')
        self.loadConfHelper()
        try:
            #res = self.doParse(conf[self.conf.vocab.configKeys[7]])
            self.doParse(conf[self.conf.vocab.configKeys[7]])
            #print('doParse ok')            
        except Exception as e:
            #print('loadConf threw exception type:',type(e), ' args: ', e.args)
            #print('conf was:\t', conf)
            #import sys
            #sys.exit()            
            for key in self.conf.presetConf.defaultConfDict.keys():
                self.preset.currentDict[key] = self.conf.presetConf.defaultConfDict[key]
            self.preset.currentDict[self.conf.vocab.configKeys[0]] = 'DEFAULT PRESET'
            self.loadConfHelper()
            self.doParse(self.conf.presetConf.defaultConfDict[self.conf.vocab.configKeys[7]])
            raise e
        gc.collect()
        self.gcd=True
        return True

    def doParse(self,confString):
        sp = sParse.SExpParser(self,confString.strip())
        #print('sParse.SExpParser ok')
        sp.execute()
        #print('sp.execute ok')

    def turnOnYellowLed(self):
        self.preset.currentDict[self.conf.vocab.configKeys[11]] = 1
        self.set(State.pb,State.Yellow,State.l0)
        self.x()
        return False

    def saveCurrentConfAsPreset(self):
        self.preset.saveCurrentConfigAsPreset(self.currentConfTupleKey)
        self.set(State.pb,State.Yellow,State.lOff)
        return True
    
    def validateAndApplyLCDInput(self,confString):
        try:
            #res = self.doParse(confString.strip())
            self.doParse(confString.strip())
            """
            for e in res:
               #print(e)
               self.outgoing.append(e)
            self.sendX()
            """
            
            ## is this self.x() well placed, or even needed here?
            # maybe because the connect and invert calls resulting from doParse need to be execucted,
            # but the return True at the end of this 'try' block will execute all self.x() too!
            self.x()
            self.preset.currentDict[self.conf.vocab.configKeys[7]]=confString.strip()
            # updated 2016 12 25 to save edited conf as preset, but not to disk
            self.preset.saveCurrentConfigAsPreset(self.currentConfTupleKey,False)
            self.currentConfTupleKey = (self.selectorVec[0].currentPosition,self.selectorVec[1].currentPosition)
            self.doConfHelper(self.currentConfTupleKey)
            return True
        except Exception as e:
            #print('validateAndApplyLCDInput threw exception: ', type(e), 'args: ', e)
            # raise e
            # finally called
            return False

    def __repr__(self):
        res=[]
        for k in dir(self):
            try:
                res.append((k,self.__dict__[k]))
            except:
                pass
        return res

##################  old stuff !!
     
    def set(self,name,att,state):
        """
        This is called to set a coil's V or T or TR or I attribute to 
        the state argument.
        It simply looks up the instance in the coils vector and applies
        the coil's method with the state given as argument. Note that 
        the attribute is converted to an index to be passed to the coil's
        setFuncs vector to find the correct method to call.
        Once the user representation is updated, the bitMgr is called
        with the same arguments to update the NEXT bit vectors.
        usage:
        >>> a.set('M',State.Vol,State.l0)
        """
        self.coils[name].setFuncs[State.stateNeg2SetFuncIndex(att)](state)
        self.bitMgr.update(name,att,state)

    def connect(self,name,pole,otherName,otherPole):
        """
        Similar to the set method, this method calls the coil's connect
        method with the arguments as given. Then the bit representation
        is updated with the same arguments.
        The subtlty here is that if the connections have not yet been reset,
        i.e. if self.resetConnections is False, then the connections must be 
        set to 0 in the NEXT bit vector. This is only done once per updating 
        session. That means that the connections are reset, then n number of
        connection updates are applied, then the updates are exectued, 
        and only then will the NEXT vector be reset.
        """
        if not self.resetConnections:
            # if the connections have not been reset, then reset just
            # the switches part of the NEXT vector
            self.bitMgr.reset(BitMgr.switchRegEndPoints, 
                              curBool=False,
                              nexBool=True)
            self.resetConnections = True
        self.coils[name].connect(pole,(otherName,otherPole))
        self.bitMgr.update((name,pole),
                           (otherName,otherPole))
        #print('app.connect ok: ',name,pole,otherName,otherPole)

    def x(self):
        """
        This method calls the x() method on each of the coils, then on the
        bitMgr, then sends the bits to the spiMgr for hardware updating, and
        finally assigns 'False' to the resetConnections member in view of 
        future connection updates.
        usage:
        >>> a.x()
        """
        for coil in self.coils.values():
            coil.x()
        self.bitMgr.x()
        # shunt
        self.shuntControl.shunt()
        #send bits!
        self.spiMgr.update(self.bitMgr.cnConfig[BitMgr.cur])
        #unshunt
        self.shuntControl.unShunt()
        self.resetConnections = False

    def showConfig(self):
        #State.printT(self.bitMgr)

##############################
#### obsolete code  
#    def loadConfig(self,confName):
#        """ loads a predefined configuration.
#        Arg 0 : the name of the conf to load, for lookup in configDict
#        Note:
#        - this resets next bitMgr config and each coils next config
#          before beginning since there is no 'addition' of settings here
#        - it also resets all the coils connection and vtri values prior
#          to executing.
#        """
#        self.bitMgr.reset(BitMgr.allRegEndPoints,
#                          curBool=False,
#                          nexBool=True)
#        for coil in self.coils.values():
#            coil.resetNext()
#        for expr in mapReplace('self',
#                               configDict[confName]):
#            State.printT('Evalutating:\t' + expr)
#            eval(expr , globals(),{'self':self})
#        self.x()
#
#    def lcdSetLine(self, lineNb, line):
#        State.printT('Setting LCD Line:\t%d\t"%s"'%(lineNb, line))
#        self.lcd.setLn(lineNb, line)
#
##############################
#
#    def loadConf(self, conf):
#        State.printT('loading conf: ' + str(conf))
#        try:
#            #res = self.doParse(conf[self.conf.vocab.configKeys[7]])
#            self.doParse(conf[self.conf.vocab.configKeys[7]])
#            #print('doParse ok')
#            """
#            for e in res:
#                #print(e)
#                self.outgoing.append(e)
#            """
#            #print('currentDict: ',self.preset.currentDict)
#            #print('keys: ', [key for key in self.preset.currentDict.keys()])
#            for key in self.preset.currentDict.keys():
#                self.preset.currentDict[key] = conf[key]
#                #print('key: ',key, ' processed ok!')
#        except Exception as e:
#            #print('loadConf threw exception type:',type(e), ' args: ', e.args)
#            #print('conf was:\t', conf)
#            #import sys
#            #sys.exit()
#            
#            self.doParse(self.conf.presetConf.defaultConfDict[self.conf.vocab.configKeys[7]])
#            for key in self.conf.presetConf.defaultConfDict.keys():
#                self.preset.currentDict[key] = self.conf.presetConf.defaultConfDict[key]
#            self.preset.currentDict[self.conf.vocab.configKeys[0]] = 'DEFAULT PRESET'
#            raise e
#        self.tone('TR',self.preset.currentDict['TR'][1],force=True)
#        for c in ['A','B','C','D','M']:
#            self.vol(c,self.preset.currentDict[c][0],force=True)
#            self.tone(c,self.preset.currentDict[c][1],force=True)
#        self.lcdMgr.loadConf()
#        self.trem(self.preset.currentDict[self.conf.vocab.configKeys[8]])
#        self.vib(self.preset.currentDict[self.conf.vocab.configKeys[9]])
#        self.tracking(self.preset.currentDict[self.conf.vocab.configKeys[10]])
#        gc.collect()
#        self.gcd=True
########################################
