gratefulfrog/ArduGuitar/Ardu2/design/POC-3_MAX395/pyboard/V1_WithHMI/pyboard_no_debug/Presets.py

import csv
from state import State

# 2016 12 25: changed saveCurrentConfigAsPreset to allow for both save to disk and not to disk

# this is where I put all the preset configs

"""
Each config is a dictionary of this form:
currentDict = {'Name': 'EasyMusic','M' : [0,0],'A' : [0,0],'B' : [0,0],'C' : [0,0],'D' : [0,0],'TR' : [None,0],'S' : '(|(+A(|BC)D)','TREM' : 0,'VIB' : 0}
"""
# configs is a dictionary with key (hs,vs) where hs is horizontal selector pos, and vs is vertical selector pos
"""
Configs  = {(0,0): {'Name':'(0,0)','M' : [0,0],'A' : [0,0],'B' : [0,0],'C' : [0,0],'D' : [0,0],'TR' : [None,0],'S' : '(|(Ab)','TREM' : 0,'VIB' : 0, 'AUX0' : 0, 'AUX1' : 0, 'SEQ : 0},
            (1,0): {'Name':'(1,0)','M' : [1,0],'A' : [1,0],'B' : [1,0],'C' : [1,0],'D' : [1,0],'TR' : [None,0],'S' : '(|BA)', 'TREM' : 1,'VIB' : 1, 'AUX0' : 1, 'AUX1' : 1, 'SEQ : 1},
            (2,0): {'Name':'(2,0)','M' : [2,0],'A' : [2,0],'B' : [2,0],'C' : [2,0],'D' : [2,0],'TR' : [None,0],'S' : '(|CA)', 'TREM' : 0,'VIB' : 0, 'AUX0' : 0, 'AUX1' : 0, 'SEQ : 4},
            (3,0): {'Name':'(3,0)','M' : [3,0],'A' : [3,0],'B' : [3,0],'C' : [3,0],'D' : [3,0],'TR' : [None,0],'S' : '(|DA)', 'TREM' : 1,'VIB' : 1, 'AUX0' : 1, 'AUX1' : 1, 'SEQ : 3},
            (4,0): {'Name':'(4,0)','M' : [4,0],'A' : [4,0],'B' : [4,0],'C' : [4,0],'D' : [4,0],'TR' : [None,0],'S' : '(|dA)', 'TREM' : 0,'VIB' : 0, 'AUX0' : 0, 'AUX1' : 0, 'SEQ : 2},
            (0,1): {'Name':'(0,1)','M' : [0,1],'A' : [0,1],'B' : [0,1],'C' : [0,1],'D' : [0,1],'TR' : [None,0],'S' : '(|AB)', 'TREM' : 1,'VIB' : 1, 'AUX0' : 1, 'AUX1' : 1, 'SEQ : 5},
            (1,1): {'Name':'(1,1)','M' : [1,1],'A' : [1,1],'B' : [1,1],'C' : [1,1],'D' : [1,1],'TR' : [None,0],'S' : '(|Bc)', 'TREM' : 0,'VIB' : 0, 'AUX0' : 0, 'AUX1' : 0, 'SEQ : ''},
            (2,1): {'Name':'(2,1)','M' : [2,1],'A' : [2,1],'B' : [2,1],'C' : [2,1],'D' : [2,1],'TR' : [None,0],'S' : '(|CB)', 'TREM' : 1,'VIB' : 1, 'AUX0' : 1, 'AUX1' : 1, 'SEQ : ''},
            (3,1): {'Name':'(3,1)','M' : [3,1],'A' : [3,1],'B' : [3,1],'C' : [3,1],'D' : [3,1],'TR' : [None,0],'S' : '(|DB)', 'TREM' : 0,'VIB' : 0, 'AUX0' : 0, 'AUX1' : 0, 'SEQ : ''},
            (4,1): {'Name':'(4,1)','M' : [4,1],'A' : [4,1],'B' : [4,1],'C' : [4,1],'D' : [4,1],'TR' : [None,0],'S' : '(|dB)', 'TREM' : 1,'VIB' : 1, 'AUX0' : 1, 'AUX1' : 1, 'SEQ : ''},
            (0,2): {'Name':'(0,2)','M' : [0,2],'A' : [0,2],'B' : [0,2],'C' : [0,2],'D' : [0,2],'TR' : [None,0],'S' : '(|AC)', 'TREM' : 0,'VIB' : 0, 'AUX0' : 0, 'AUX1' : 0, 'SEQ : ''},
            (1,2): {'Name':'(1,2)','M' : [1,2],'A' : [1,2],'B' : [1,2],'C' : [1,2],'D' : [1,2],'TR' : [None,0],'S' : '(|BC)', 'TREM' : 1,'VIB' : 1, 'AUX0' : 1, 'AUX1' : 1, 'SEQ : ''},
            (2,2): {'Name':'(2,2)','M' : [2,2],'A' : [2,2],'B' : [2,2],'C' : [2,2],'D' : [2,2],'TR' : [None,0],'S' : '(|Cd)', 'TREM' : 0,'VIB' : 0, 'AUX0' : 0, 'AUX1' : 0, 'SEQ : ''},
            (3,2): {'Name':'(3,2)','M' : [3,2],'A' : [3,2],'B' : [3,2],'C' : [3,2],'D' : [3,2],'TR' : [None,0],'S' : '(|DC)', 'TREM' : 1,'VIB' : 1, 'AUX0' : 1, 'AUX1' : 1, 'SEQ : ''},
            (4,2): {'Name':'(4,2)','M' : [4,2],'A' : [4,2],'B' : [4,2],'C' : [4,2],'D' : [4,2],'TR' : [None,0],'S' : '(|dC)', 'TREM' : 0,'VIB' : 0, 'AUX0' : 0, 'AUX1' : 0, 'SEQ : ''},
            (0,3): {'Name':'(0,3)','M' : [0,3],'A' : [0,3],'B' : [0,3],'C' : [0,3],'D' : [0,3],'TR' : [None,0],'S' : '(|AD)', 'TREM' : 1,'VIB' : 1, 'AUX0' : 1, 'AUX1' : 1, 'SEQ : ''},
            (1,3): {'Name':'(1,3)','M' : [1,3],'A' : [1,3],'B' : [1,3],'C' : [1,3],'D' : [1,3],'TR' : [None,0],'S' : '(|BD)', 'TREM' : 0,'VIB' : 0, 'AUX0' : 0, 'AUX1' : 0, 'SEQ : ''},
            (2,3): {'Name':'(2,3)','M' : [2,3],'A' : [2,3],'B' : [2,3],'C' : [2,3],'D' : [2,3],'TR' : [None,0],'S' : '(|CD)', 'TREM' : 1,'VIB' : 1, 'AUX0' : 1, 'AUX1' : 1, 'SEQ : ''},
            (3,3): {'Name':'(3,3)','M' : [3,3],'A' : [3,3],'B' : [3,3],'C' : [3,3],'D' : [3,3],'TR' : [None,0],'S' : '(|Da)', 'TREM' : 0,'VIB' : 0, 'AUX0' : 0, 'AUX1' : 0, 'SEQ : ''},
            (4,3): {'Name':'(4,3)','M' : [4,3],'A' : [4,3],'B' : [4,3],'C' : [4,3],'D' : [4,3],'TR' : [None,0],'S' : '(|da)', 'TREM' : 1,'VIB' : 1, 'AUX0' : 1, 'AUX1' : 1, 'SEQ : ''},
            (0,4): {'Name':'(0,4)','M' : [0,4],'A' : [0,4],'B' : [0,4],'C' : [0,4],'D' : [0,4],'TR' : [None,0],'S' : '(|Ad)', 'TREM' : 0,'VIB' : 0, 'AUX0' : 0, 'AUX1' : 0, 'SEQ : ''},
            (1,4): {'Name':'(1,4)','M' : [1,4],'A' : [1,4],'B' : [1,4],'C' : [1,4],'D' : [1,4],'TR' : [None,0],'S' : '(|Bd)', 'TREM' : 1,'VIB' : 1, 'AUX0' : 1, 'AUX1' : 1, 'SEQ : ''},
            (2,4): {'Name':'(2,4)','M' : [2,4],'A' : [2,4],'B' : [2,4],'C' : [2,4],'D' : [2,4],'TR' : [None,0],'S' : '(|Cd)', 'TREM' : 0,'VIB' : 0, 'AUX0' : 0, 'AUX1' : 0, 'SEQ : ''},
            (3,4): {'Name':'(3,4)','M' : [3,4],'A' : [3,4],'B' : [3,4],'C' : [3,4],'D' : [3,4],'TR' : [None,0],'S' : '(|Da)', 'TREM' : 1,'VIB' : 1, 'AUX0' : 1, 'AUX1' : 1, 'SEQ : ''},
            (4,4): {'Name':'(4,4)','M' : [4,4],'A' : [4,4],'B' : [4,4],'C' : [4,4],'D' : [4,4],'TR' : [None,0],'S' : '(|Da)', 'TREM' : 0,'VIB' : 0, 'AUX0' : 0, 'AUX1' : 0, 'SEQ : ''}
            }
"""
class Preset():
    class Sequencer():
        def __init__(self,presetDict,seqKey):
            # seqLis is an ordered list of ((key,index),(key,index)
            # where key is a key from the presetDict, eg. (0,0) and index is an int.
            self.seqLis = []
            for k in presetDict.keys():
                index = presetDict[k][seqKey]
                if index != '':
                    self.seqLis.append((k,index))
            self.seqLis.sort(key=lambda pr: pr[1])
            self.seqLen    = len(self.seqLis)
            self.seqStartKey = self.seqLis[0][0]  # the tuple that is the key to the initial seq preset
            self.reset()
            
        def reset(self):
            self.nextIndex = self.seqLis[1][1]

        def nextKey(self):
            rNext = self.nextIndex
            self.nextIndex = (self.nextIndex+1)%self.seqLen
            return self.seqLis[rNext][0]
    
    def __init__(self,pyGuitarConf,fileName=None):
            # the fileName is used to load a presets file, if one exists,
            # if not, one is created
            self.conf = pyGuitarConf
            self.presets = {}
            if fileName==None:
                self.filePath =  self.conf.LocalConf.presetDir +\
                                 self.conf.LocalConf.dirSeparator +  \
                                 self.conf.LocalConf.presetFileName
            else:
                self.filePath = fileName
            #State.printT ("creating preset instance from:\t" + self.filePath)
            #print("creating preset instance from:\t" + self.filePath)
            try:
                #print(self.filePath) 
                with open(self.filePath, 'r') as csvfile:
                    # from official csv module, not used on pyboard!
                    # reader = csv.DictReader(csvfile,fieldnames = self.conf.Vocab.headings,delimiter=',')
                    # self.header = reader.next()
                    # the next lines refer to my version of the csv reader
                    reader = csv.CSV.Reader(csvfile)
                    self.header = next(reader)
                    for row in reader:
                        if len(row)>2:
                            self.rowDict2confDict(row)
                    if len(self.presets) ==0:
                        raise Exception("read failure")
            except Exception as e:
                #print('reading csv file threw exception: ', type(e), 'Args: ', e.args)
                #State.printT( "error reading preset file!  Creating new one!")
                #print( "error reading preset file!  Creating new one!")
                self.createDefaultPresets()
            self.currentDict = {}
            #print(self.presets)
            #print(self.presets[(0,0)])
            for k in self.presets[(0,0)].keys():
                self.currentDict[k] = self.presets[(0,0)][k]
            self.seq=Preset.Sequencer(self.presets,pyGuitarConf.vocab.configKeys[12])

    def rowDict2confDict(self,row):
        #print(row)
        curConfDict= {}
        self.presets[(int(row[0]),int(row[1]))]= curConfDict
        
        curConfDict[self.conf.Vocab.configKeys[0]] = row[2]

        for i in  range(1,6):
            curConfDict[self.conf.Vocab.configKeys[i]] = [int(row[1+2*i]),int(row[2+2*i])]
        curConfDict[self.conf.Vocab.configKeys[6]] = [None,int(row[13])]
        curConfDict[self.conf.Vocab.configKeys[7]] = row[14]
        j=15
        for k in self.conf.Vocab.configKeys[8:]:
            if row[j] != '':
                curConfDict[k] = int(row[j])
            else:
                curConfDict[k] = row[j]
            j+=1
        #print(curConfDict)
        
    """    
    def createDefaultPresets(self):
        # this will create a default preset file in the default location
        # with default content
        for i in range(5):
            for j in range(5):
                self.presets[(i,j)] = self.conf.presetConf.defaultConfDict
        self.header = self.conf.Vocab.headings
        #self.toFile(self.conf.presetFileName)
    """
    def createDefaultPresets(self):
        """
        this will create a default preset dictionary
        with default content
        and attempt to save to SD,
        in case of write failure, message to console and continue anyway!
        """
        import defaultPresets
        self.presets= defaultPresets.defPresetDict
        self.header = self.conf.Vocab.headings
        try:
            self.toFile()
        except Exception as e:
            #print('Writing csv file raised exception: ', type(e), 'Args: ', e.args)
            pass
                            
    def toFile(self, file = None):
        """
        this will write the presets to a file,
        if a file argument is provided it is used and it
        updates the instance filePath
        otherwise the current instance filePath is used
        """
        if file: 
            self.filePath = file
        with open(self.filePath, 'w') as csvfile:
            writer = csv.CSV.Writer(csvfile)
            #print(self.header)
            writer.writeRow(self.header)
            for p in self.presets.keys():
                rowDict = self.confDict2RowDict(p,self.presets[p])
                #print(rowDict)
                rawRow = [rowDict[k] for k in self.header]
                #print(rawRow)
                writer.writeRow(rawRow)
        #State.printT( "Wrote file:\t" + self.filePath)
        #print( "Wrote file:\t" + self.filePath)

    def makeRawRowWorkAround(self,rowDict):
        res = []
        for badKey in self.header:
            for goodKey in rowDict.keys():
                if badKey==goodKey:
                    res.append(rowDict[goodKey])
                    break
        return res
        
    def confDict2RowDict(self,key,conf):
        curRowDict= {}
        # horiz and verti
        for i in range(2):
            curRowDict[self.conf.Vocab.headings[i]] = key[i]
        #Name
        curRowDict[self.conf.Vocab.headings[2]] = conf[self.conf.Vocab.headings[2]]
        
        #M,A,B,C,D  vol and tone    
        for i in  range(1,6):
            curRowDict[self.conf.Vocab.headings[1+2*i]] = conf[self.conf.Vocab.configKeys[i]][0]
            curRowDict[self.conf.Vocab.headings[2+2*i]] = conf[self.conf.Vocab.configKeys[i]][1]
        # TneRange    
        curRowDict[self.conf.Vocab.headings[13]] = conf[self.conf.Vocab.configKeys[6]][1]
        #S,TREM,VIB,AUX0,AUX1
        for k in self.conf.Vocab.headings[14:]:
                curRowDict[k] = conf[k]
        return curRowDict
    
    def add(self,name,vDict):
        # add this to the presets, if the vDict is proper length:
        # and no keys are wrong
        # print "preset.add(",name,vDict,")", self.header
        newDict = {}
        for k in vDict.keys():
            newDict[k] = vDict[k]
        self.presets[name]=newDict
        #print(self.presets[name])
        
    def remove(self,name):
        # just remove it or do nothing if not possible
        if name in self.presets.keys():
            del self.presets[name]
    
    def rename(self,old,new):
        # to rename a preset, we create a new dict copied from previous one
        # put it in with the new name
        # and remove the reference to the old name
        # if the old name is not found, do nothing
        # return True if success, False otherwise
        # print "renaming preset: " + old + " to: " + new
        res = False
        if old in self.presets.keys():
            newDict = {}
            for k in self.presets[old].keys():
                newDict[k] = self.presets[old][k]
            self.presets[new] = newDict
            del self.presets[old]
            res = True
        return res
    """
    # changed 2016 12 25 to save current edited conf as preset but not to disk
    def saveCurrentConfigAsPreset(self, key):
        self.currentDict[self.conf.vocab.configKeys[11]] = 0
        self.add(key,self.currentDict)
        #print(self.presets)
        self.toFile()
    """        
    def saveCurrentConfigAsPreset(self, key, saveToDisk = True):
        self.currentDict[self.conf.vocab.configKeys[11]] = 0
        self.add(key,self.currentDict)
        #print(self.presets)
        if saveToDisk:
            self.toFile()
