gratefulfrog/ArduGuitar/Ardu2/design/POC-3_MAX395/pyboard/V1_WithHMI/pyboard_no_debug/spiMgr.py

#!/usr/local/bin/python3.4
# spiMgr.py
# exercise some pyboard SPI with as many 74HC595 shift registers connected
# as needed:
# as of 2015 03 26 this module has been tested:
#  - Off-board
#  - on-board, but with no shift Registers connected

"""
The pyboard SPI class gives details:
http://docs.micropython.org/en/latest/library/pyb.SPI.html

the NSS pin is NOT used by the SPI driver and is free for other use.

SPI(1) is on the X position: 
(NSS, SCK, MISO, MOSI) = (X5, X6, X7, X8) = (PA4, PA5, PA6, PA7)

SPI(2) is on the Y position: 
(NSS, SCK, MISO, MOSI) = (Y5, Y6, Y7, Y8) = (PB12, PB13, PB14, PB15)

This is the wiring used:
pin   
Shift Reg 1
8  : GND
9  : Shift Reg 0, pin 14 (serial data out-> serial data in)
10 : 5v
11 : X6 SHCP 
12 : X5 STCP (latch)
13 : GND (Output Enable)
14 : X8  (Serial Data In - MOSI)
16 : 5v
Q0-Q7 : LEDs 8-15

Shift Reg 0
8  : GND
9  : not connected
10 : 5v
11 : X6 SHCP 
12 : X5 STCP (latch)
13 : GND (Output Enable)
14 : X8  (Serial Data In - MOSI)
16 : 5v
Q0-Q7 : LEDs 0-7
"""
from pyb import SPI,Pin
from state import State
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
